cluster2600/porscheparts/twins/m64-cylinder-head/source/additivefoam/README.md

# Marangoni contract fix for OpenFOAM 14

This patch only adds `assignable() const { return false; }` to the ORNL
Marangoni boundary condition. It allows `constrainHbyA` to preserve the normal
condition while the pressure predictor is built. It modifies neither
`evaluate`, nor `snGrad`, nor the pressure equations, nor the material
properties. It is not a cylinder head qualification.

The upstream file, under **GPL-3.0-or-later**, is
[`marangoniFvPatchVectorField.H`](https://github.com/ORNL/AdditiveFOAM/blob/9c05c5eb54db03faa342b14b0806efe740de8c44/applications/solvers/additiveFoam/derivedFvPatchFields/marangoni/marangoniFvPatchV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).
The patch is distributed under the same license. The tested context is
OpenFOAM 14, commit `7b05503f98a85be88af930df48623b4d152bfc35`.
The diff has no context lines: the exact input digest below is therefore a
precondition, and the output digest must be verified.

SHA-256 digests of the header:

- Required input: `bb21f5c705425c6903945f9ca95055d6ca4083d8b9d58e1b15e2a1c75deb022a`.
- Tested output: `c1bb4ab01a24a907aefda0995d7df650d4dc46c23f61f9d1130bd7d6a601a33c`.

On a **fresh copy of the solver sources**, from the directory that contains
`derivedFvPatchFields/`, verify the input hash before applying the patch with
`patch -p1`. Refuse any digest difference or ambiguous context; do not replace a
historical binary in place. Then rebuild the solver in a separate output
directory and record the digests of the sources, libraries and executable.

```mermaid
flowchart TD
    A["Fresh copy of the<br/>solver sources"] --> B{"Header input digest<br/>bb21f5c7…?"}
    B -- "different or ambiguous" --> R["Refuse; historical<br/>binary untouched"]:::stop
    B -- "exact" --> C["patch -p1"]
    C --> D{"Output digest<br/>c1bb4ab0…?"}
    D -- "no" --> R
    D -- "yes" --> E["Rebuild in a separate directory<br/>record source, library, executable digests"]
    E --> F["Native old/new witness<br/>traction, adjustPhi"]
    F -. "not sufficient" .-> G["LPBF coupon acceptance:<br/>balances, coupling, convergence,<br/>calibration checked separately"]:::open
    classDef stop fill:#fde2e1,stroke:#c0392b,color:#1a1a1a;
    classDef ok fill:#e3f1e6,stroke:#2e7d32,color:#1a1a1a;
    classDef open fill:#fff4d6,stroke:#b7791f,color:#1a1a1a;
```

The [native old/new witness](../../../../docs/reports/M64_F58_PREDICTOR_CONTRACT_20260908.md)
checks the conservation of the traction and the native `adjustPhi` step.
Success of this witness is not enough to accept an LPBF coupon: its balances,
its coupling, its convergence and its physical calibration remain separate
checks.

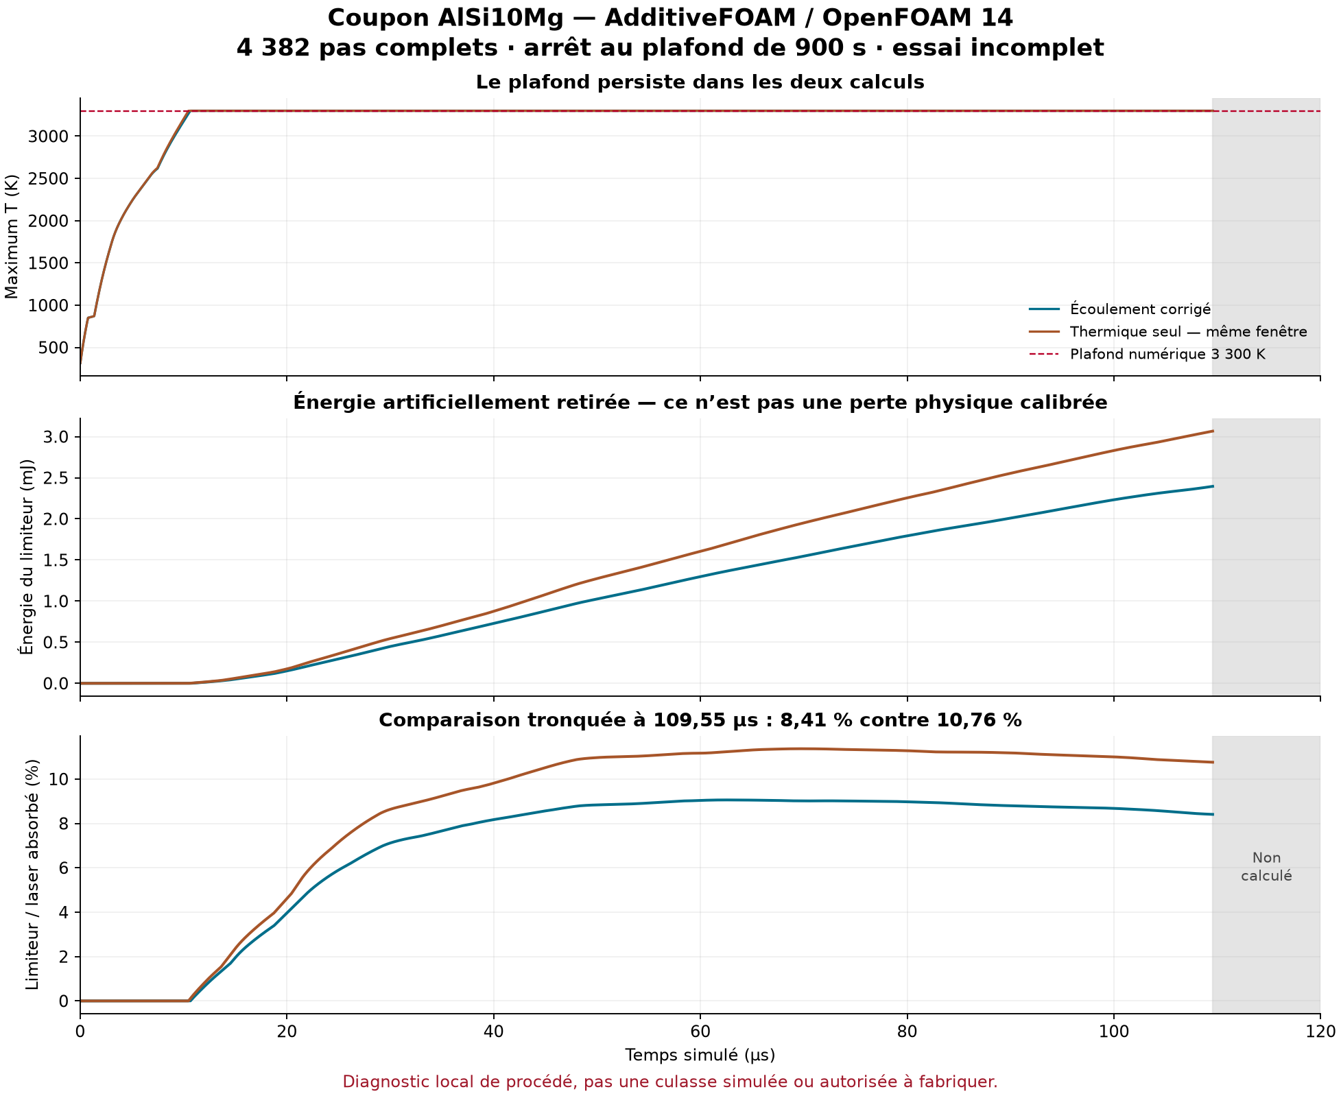
[picture p60: twins/m64-cylinder-head/evidence/corrected-coupon-diagnostic-20260908.png]
F58 AlSi10Mg coupon run with the corrected Marangoni contract: maximum temperature pinned at the 3,300 K numerical ceiling, limiter energy, and limiter share of absorbed laser, over the common 0–109.55 µs window


*The [corrected F58 coupon](../../../../docs/reports/M64_F58_CORRECTED_COUPON_20260908.md)
run that used this patch (labels in French): 4,382 complete steps, stopped at
the 900 s ceiling, an incomplete trial. It shows that the numerical 3,300 K
ceiling persists; it does not isolate the patch's effect and is not a simulated
or manufacturable cylinder head.*
