cluster2600/porscheparts/docs/reports/M64_BOUNDED_MESH_TRIALS_20260928.md

# M64 — bounded chamfer and native tip-cut experiments, 28 September 2026

## Retained result

Follow-up: the [local native reconstruction](M64_LOCAL_RECONSTRUCTION_20260928.md)
passes six-face locality and BOP checks, but its surface quality is worse;
the retained 32-tetrahedron result is unchanged.

**Zero rejected tetrahedra has not been demonstrated on the head.** The retained
volume mesh still has **32 elements below minSICN 0.1, out of 1,341,461**.
This continuation implements the [research-backed experiments](M64_ZERO_DEFECT_RESEARCH_20260928.md)
and rejects a misleading zero-quality-defect result on a synthetic witness.
Neither that witness nor a valid Boolean operation is a validated cylinder head.

A new **unchanged-CAD surface screen** has **seven incompatible triangles on
five faces**, versus eight on six faces in the retained mesh's boundary. It is
a different surface discretisation, **not** a new volume mesh or a reduction
of the retained 32-tetrahedron count. No CAD master, quality threshold,
functional-interface designation or manufacturing authorisation changes.

The private reference is still the scan-derived **935 research body**, not
certified M64 engine interfaces. Coordinates remain provisional scan units;
0.020 below is not a validated millimetre allowance and is unrelated to the
0.040 mm carrier-displacement target. Scan attribution and rights are recorded
under [Wolfe Classics](../../catalog/sources/src-wolfe-classics-935-billet-cylinder-head-scan.json).
Only this diagnostic figure, code and aggregate results are published; native
geometry, raw coordinates, volume meshes and detailed receipts stay private.

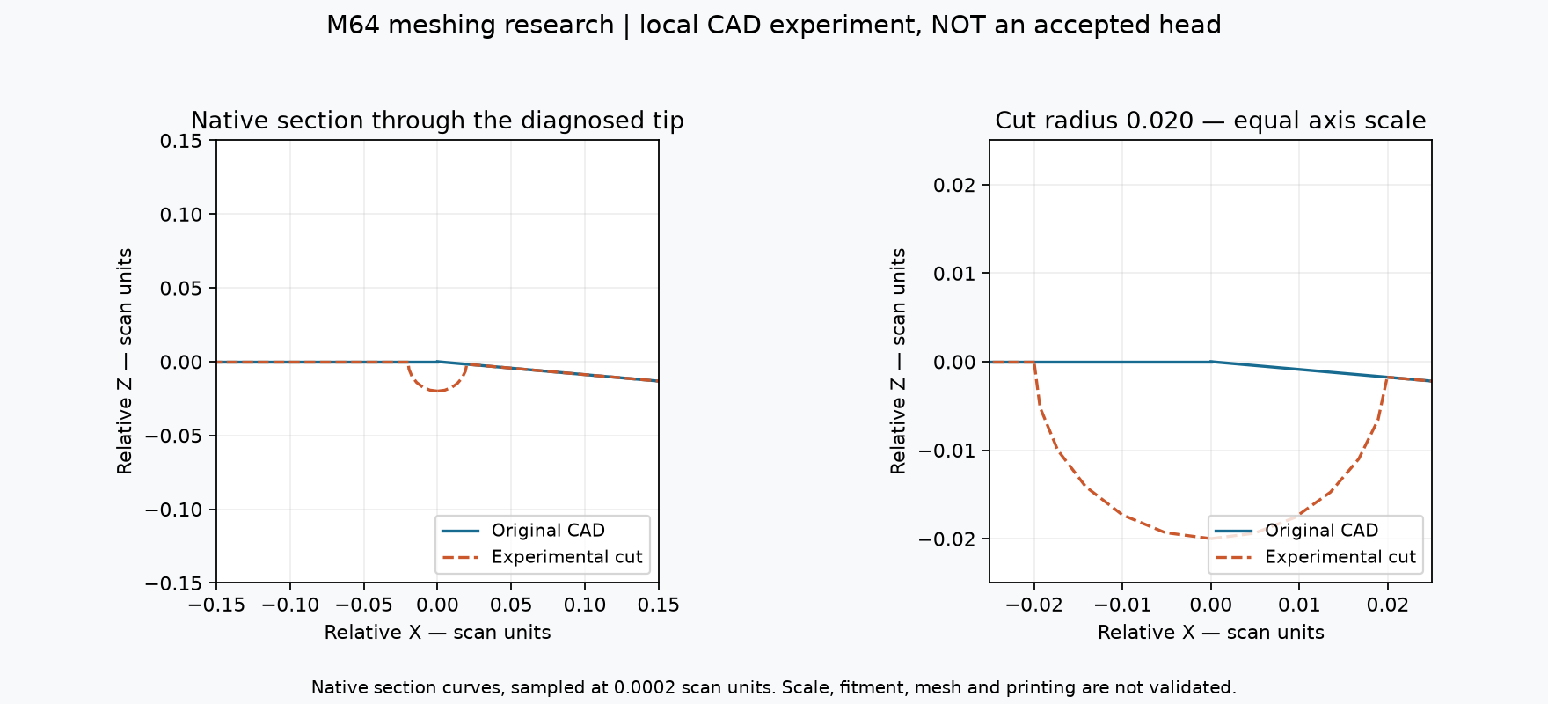
[picture p79: docs/media/m64-bounded-mesh-20260928/tip-cut-section.png]
Actual native section at the experimental cut


*Blue: original native section; orange: an experimental spherical cut of radius
0.020. The equal-scale section exposes the new notch; it is not an adopted
cooling feature, product photograph, thermal simulation or printing approval.*

## Tests and findings

| Experiment | Measured result | Decision |
|---|---|---|
| Shared curve/parametric-curve consistency on six obstructing faces | 19 edge/face uses, 129 samples each; maximum sampled gap **1.40088e-7**; none exceeds its recorded edge tolerance | No measured justification for a simple shared-curve repair. Sampling does not certify unsampled extrema. |
| Bounded DelOptim intermediate stage, unit tetrahedron, epsilon 0.020 | **4,182 inner tets; zero below 0.1; minimum 0.126104875** | **Rejected:** two material components and two boundary edges without incidence two. |
| Independent distance bounds on that witness | Two directed upper bounds **0.01970484492** and **0.00679892761**, below 0.020; interval gap tolerance 1e-4 | Small distance does not rescue failed topology. These are floating-point polygon comparisons, not a native-CAD or rounding-error certificate. |
| Acute tetrahedron witness, same bounded safe mode | Mesher stopped after **120 s**, no completed exported mesh | Nonconverged; no quality result. |
| One native spherical cut at face 1648, radius 0.020 | Exactly five source faces affected in memory; one valid solid and shell, unchanged maximum tolerances, valid reread; **BOP audit passes** without faults/errors/warnings in **261.75 s** | CAD candidate only; does not establish useful geometry or a passing mesh. |
| Four distinct acute tips on five selected faces, radius 0.020 | Exactly ten source faces affected in memory; **4,922 faces**, one valid solid/shell, unchanged maximum tolerances, valid reread | Local CAD construction succeeds; full candidate BOP and mesh/volume/deviation qualification remain open. |
| First surface recipe, single-tip candidate | 86,606 triangles, **105 incompatible**, minimum 0 | Rejected. This exploratory recipe also differs outside the cut; do not attribute every new bad triangle to the cut. |
| First surface recipe, four-tip candidate | Native process exits **139**, no completed surface result | Failed process; incomplete receipt is not a pass. |
| Curvature-aware matched recipe, unchanged reference | **441,650 triangles; seven incompatible; minimum 0.02134670874**, **260.69 s** | Surface-only improvement; still incompatible with zero rejected tets on that fixed skin. |
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
