cluster2600/porscheparts/docs/assets/m64-g13/central-section-x0.png

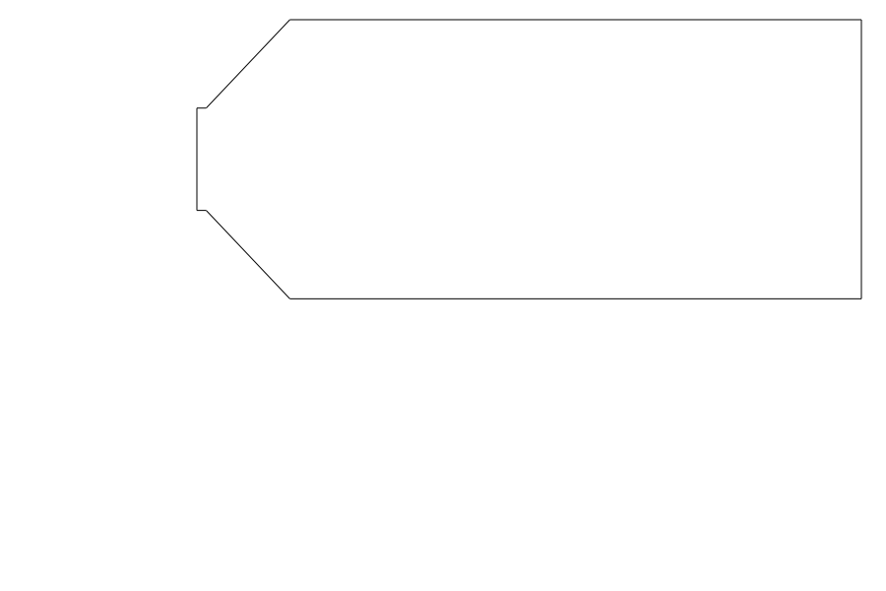
docs/assets/m64-g13/central-section-x0.png
