cluster2600/porscheparts/docs/assets/m64-g13/central-spine.png

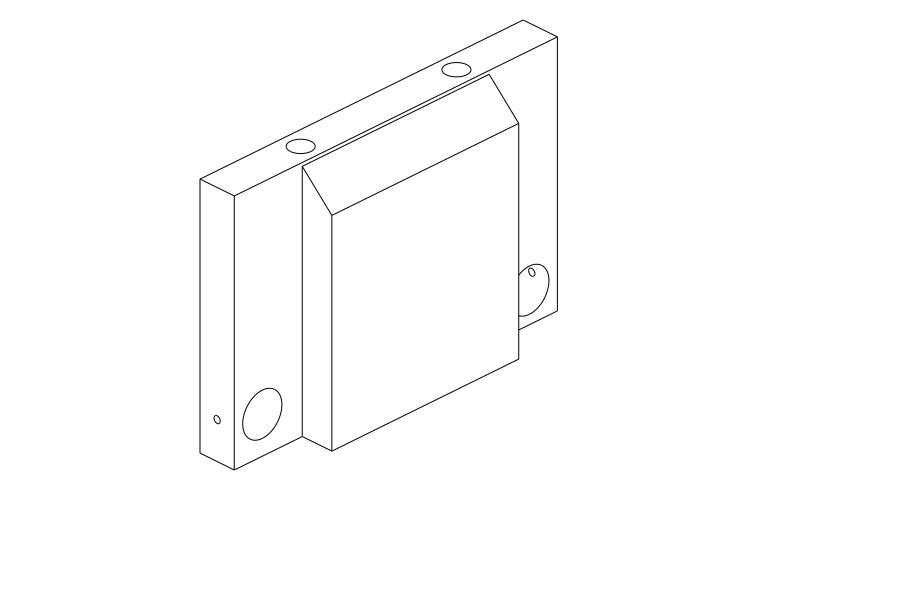
docs/assets/m64-g13/central-spine.png
