cluster2600/porscheparts/docs/assets/m64-g14/central68.png

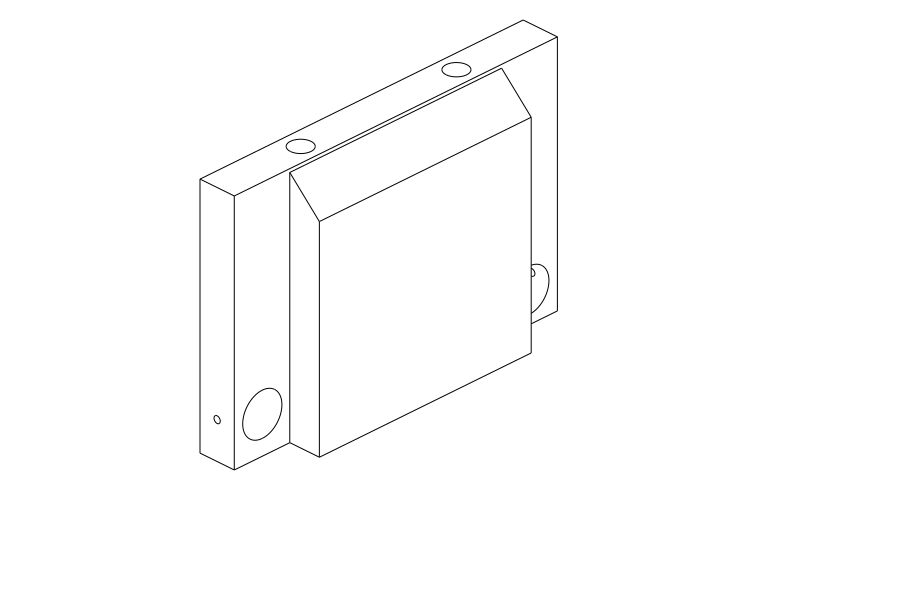
docs/assets/m64-g14/central68.png
