cluster2600/porscheparts/docs/assets/m64-g14/central-caps.png

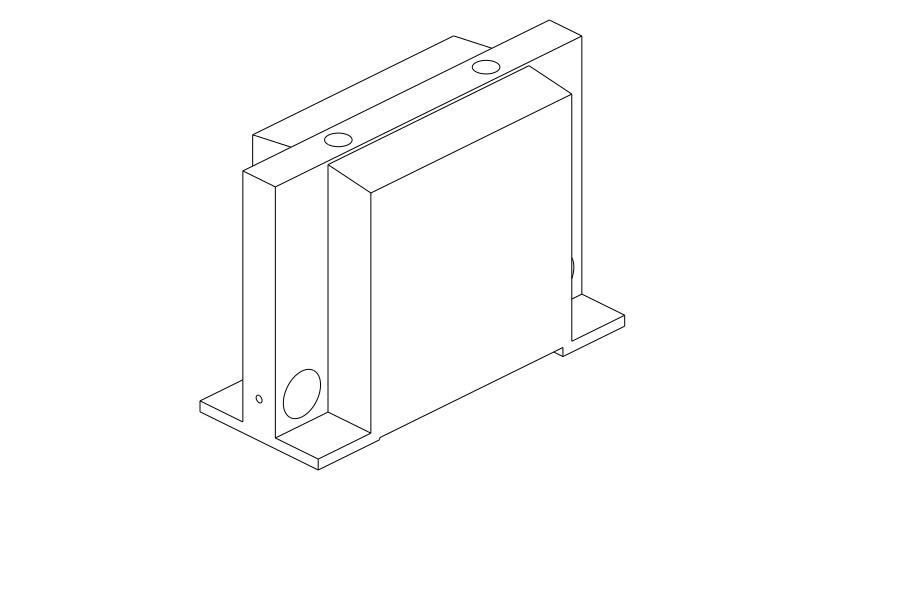
docs/assets/m64-g14/central-caps.png
