cluster2600/porscheparts/docs/assets/m64-g14/outer-combined-section.png

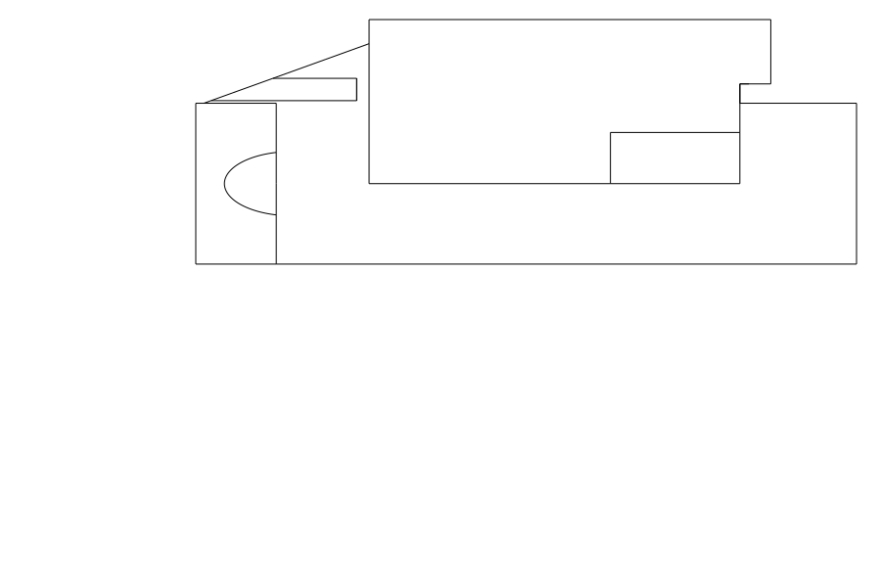
docs/assets/m64-g14/outer-combined-section.png
