cluster2600/porscheparts/docs/images/m64-hybrid-group-quality-20260909.png

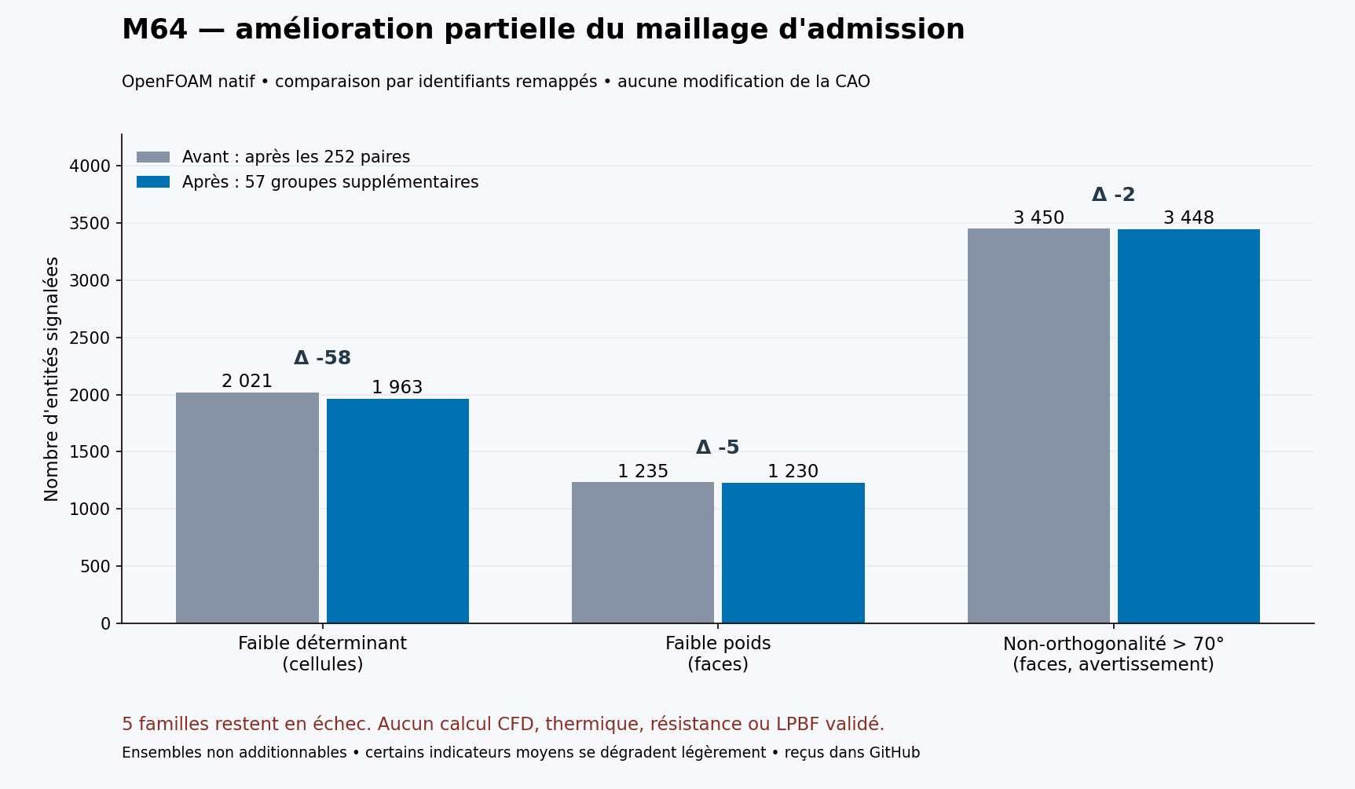
docs/images/m64-hybrid-group-quality-20260909.png
