cluster2600/porscheparts/docs/M64_SURFACE_METHOD_COMPARISON_20260909.png

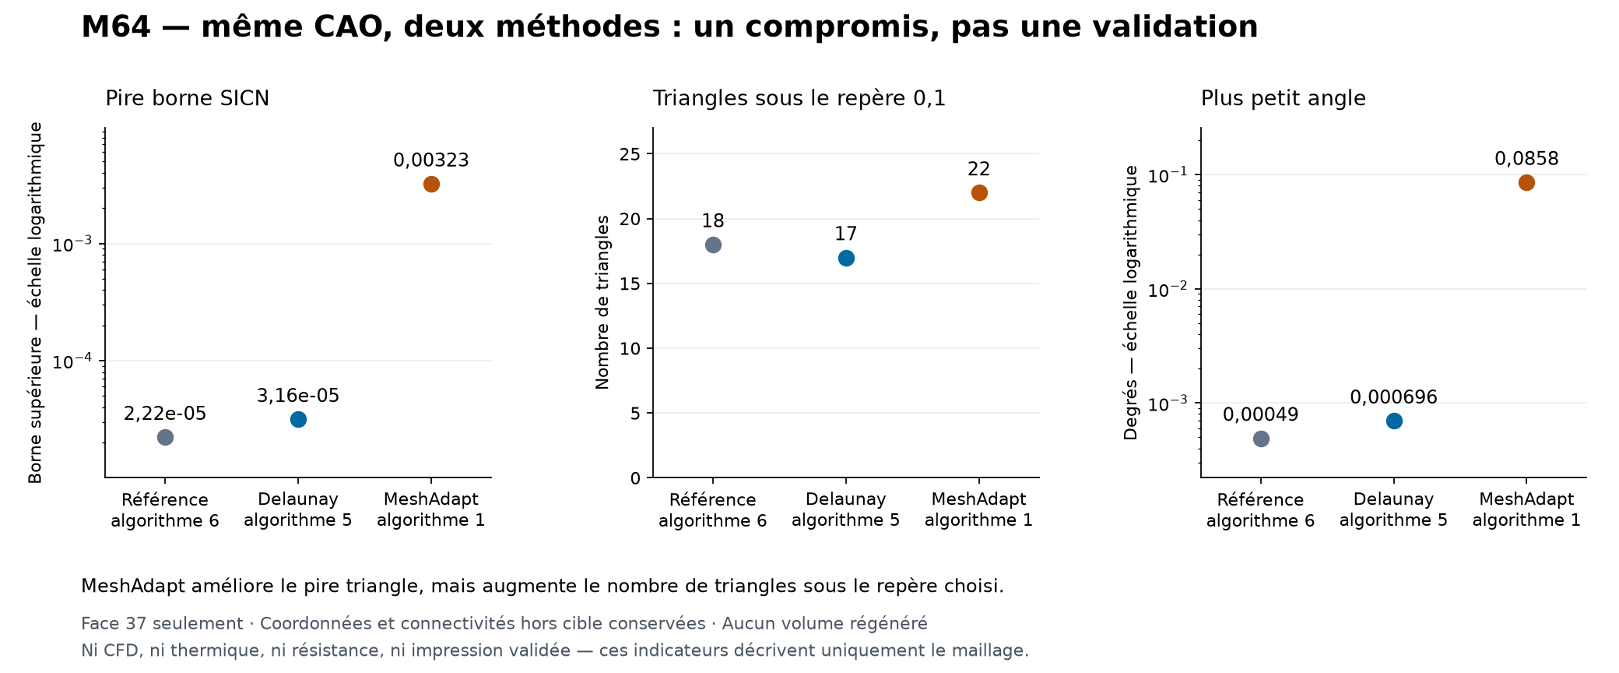
docs/M64_SURFACE_METHOD_COMPARISON_20260909.png
