cluster2600/porscheparts/docs/media/diagrams/digital-twin-993-etat.png

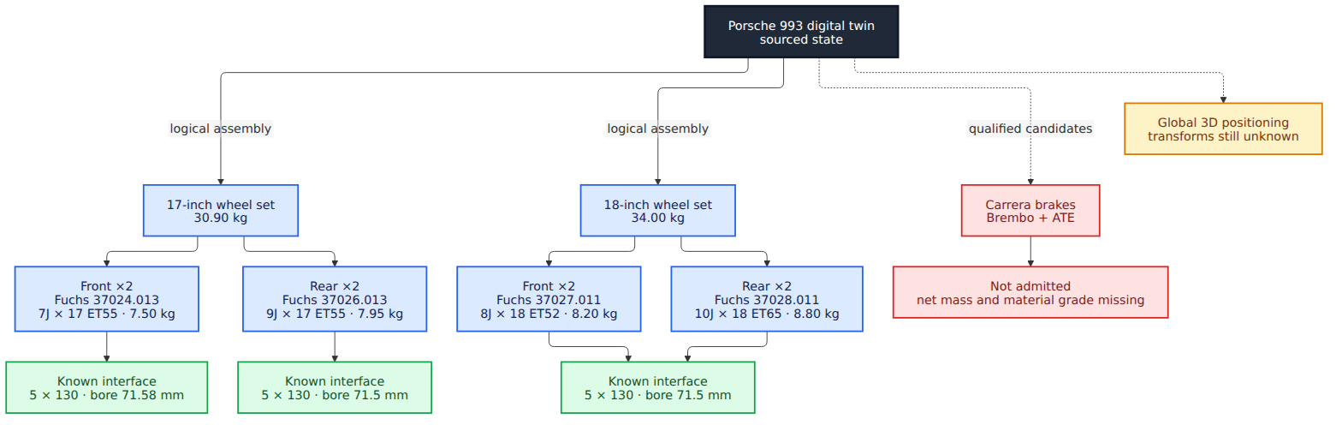
docs/media/diagrams/digital-twin-993-etat.png
