cluster2600/porscheparts/docs/media/diagrams/m64-700ps-execution.png

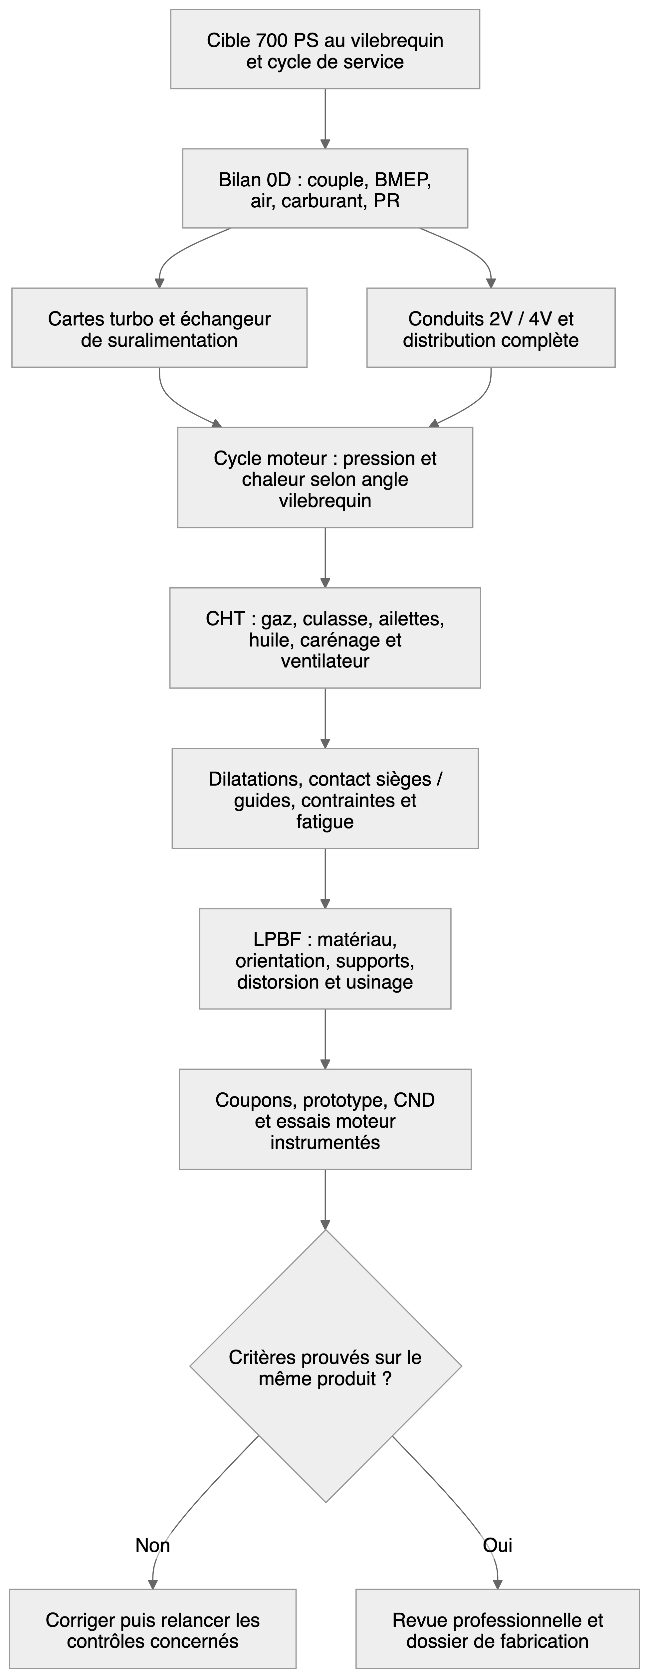
docs/media/diagrams/m64-700ps-execution.png
