cluster2600/porscheparts/docs/media/diagrams/m64-stack.png

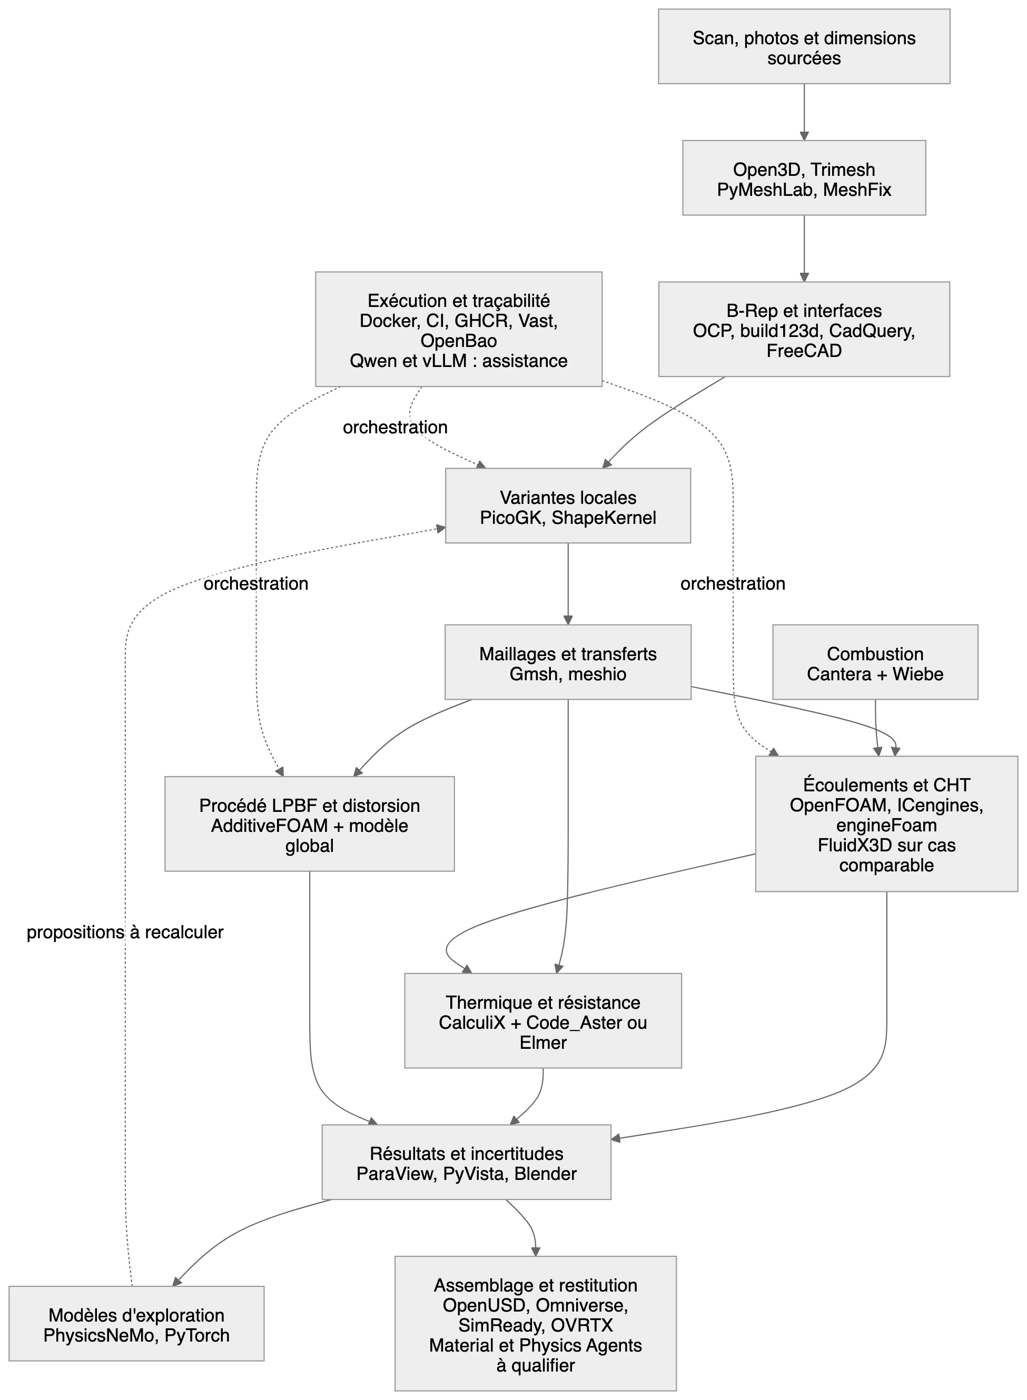
docs/media/diagrams/m64-stack.png
