cluster2600/porscheparts/docs/media/diagrams/m64-vast-run.png

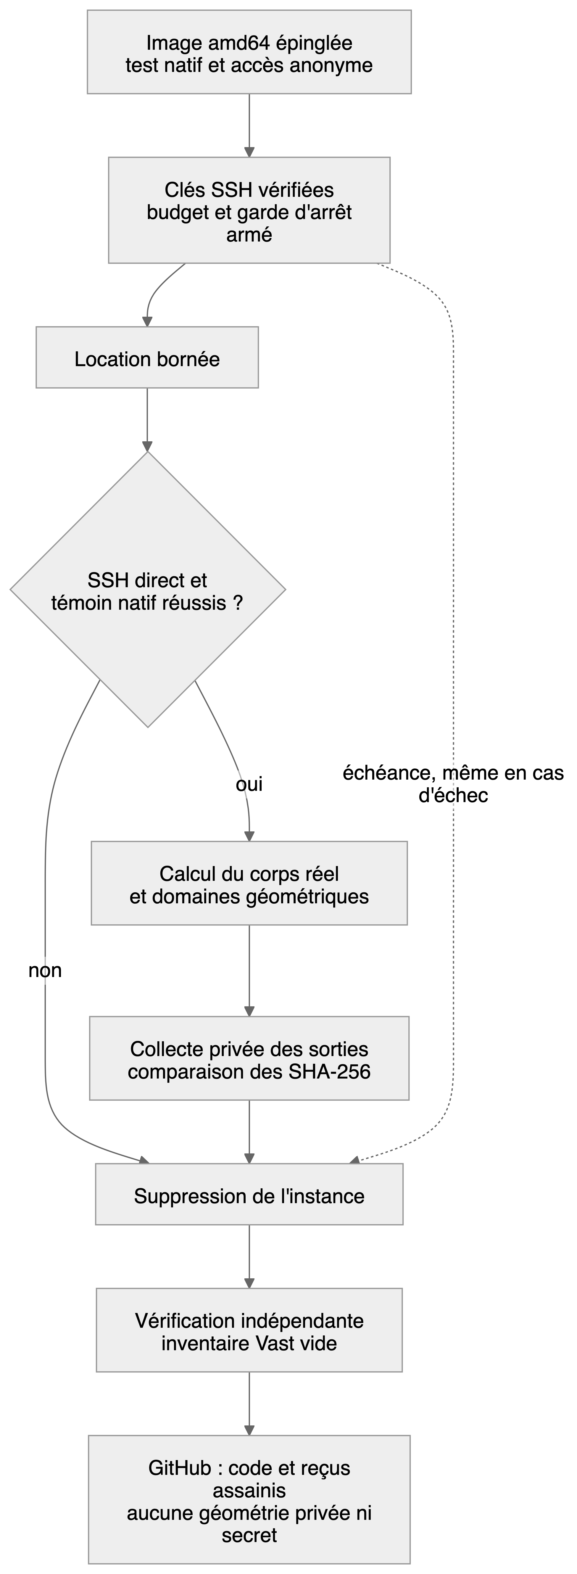
docs/media/diagrams/m64-vast-run.png
