cluster2600/porscheparts/docs/media/m64-adaptive-mesh-20260928/acute-native-face.png

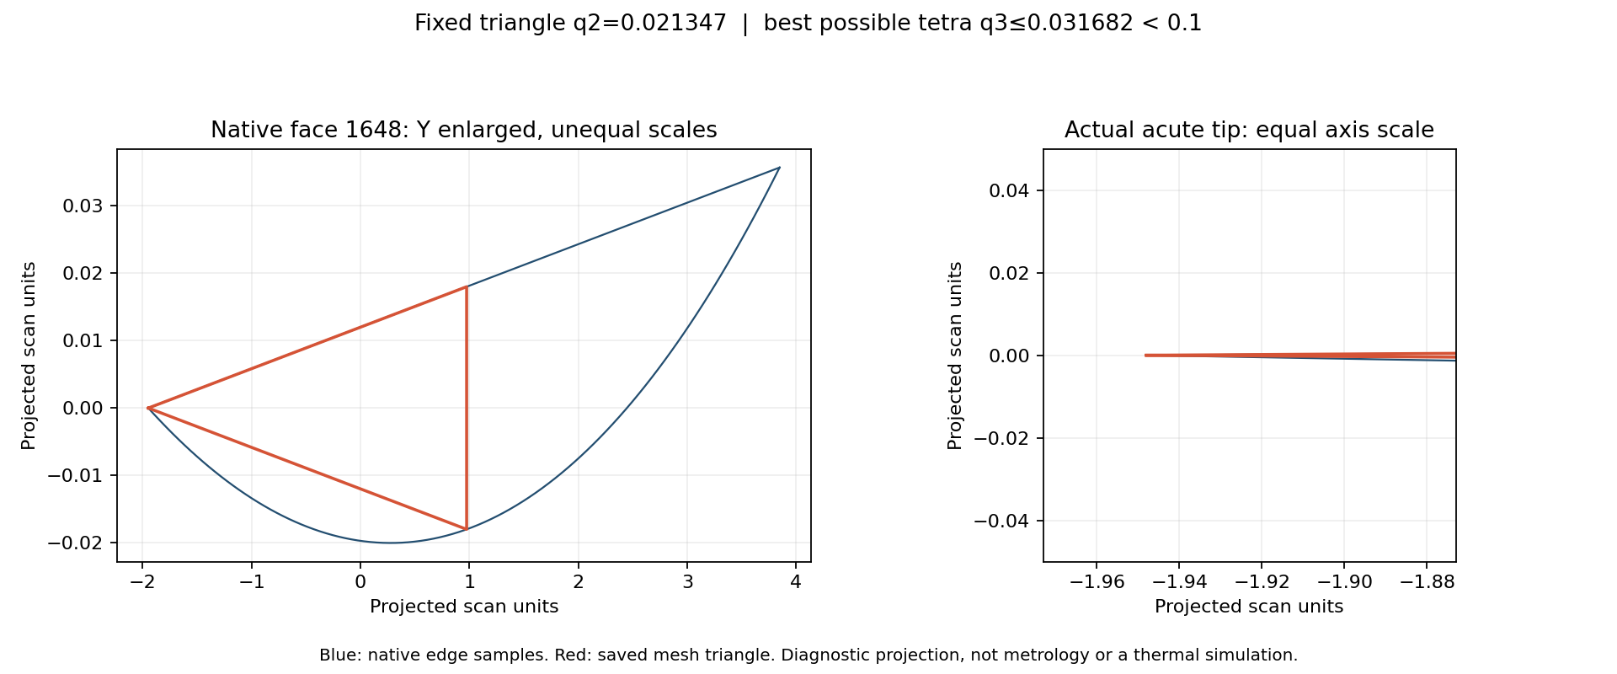
docs/media/m64-adaptive-mesh-20260928/acute-native-face.png
