cluster2600/porscheparts/docs/media/m64-am-20260928/geometric-screen.png

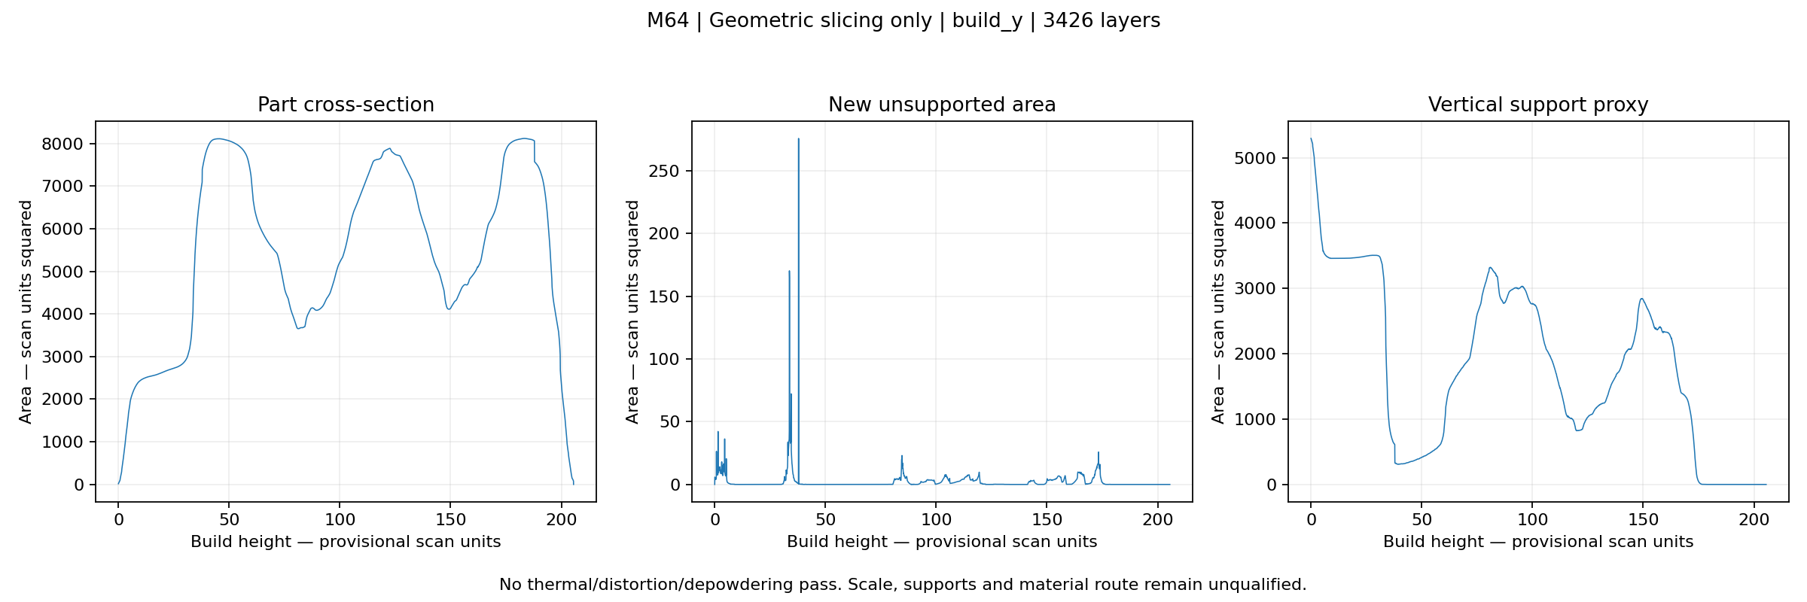
docs/media/m64-am-20260928/geometric-screen.png
