cluster2600/porscheparts/docs/media/m64-fixed-boundary-seam-20260928/native-section.png

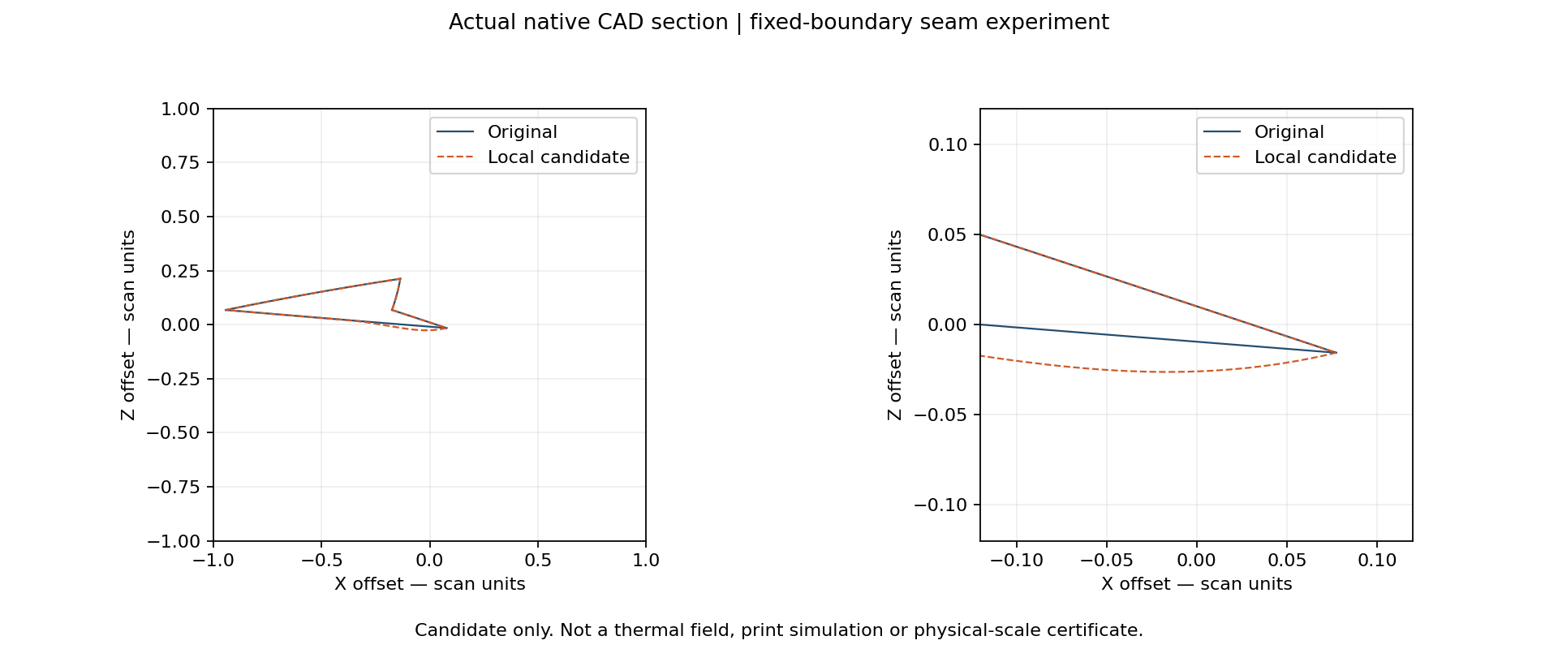
docs/media/m64-fixed-boundary-seam-20260928/native-section.png
