cluster2600/porscheparts/docs/media/m64-junction-recovery-20260928/junction-classes.png

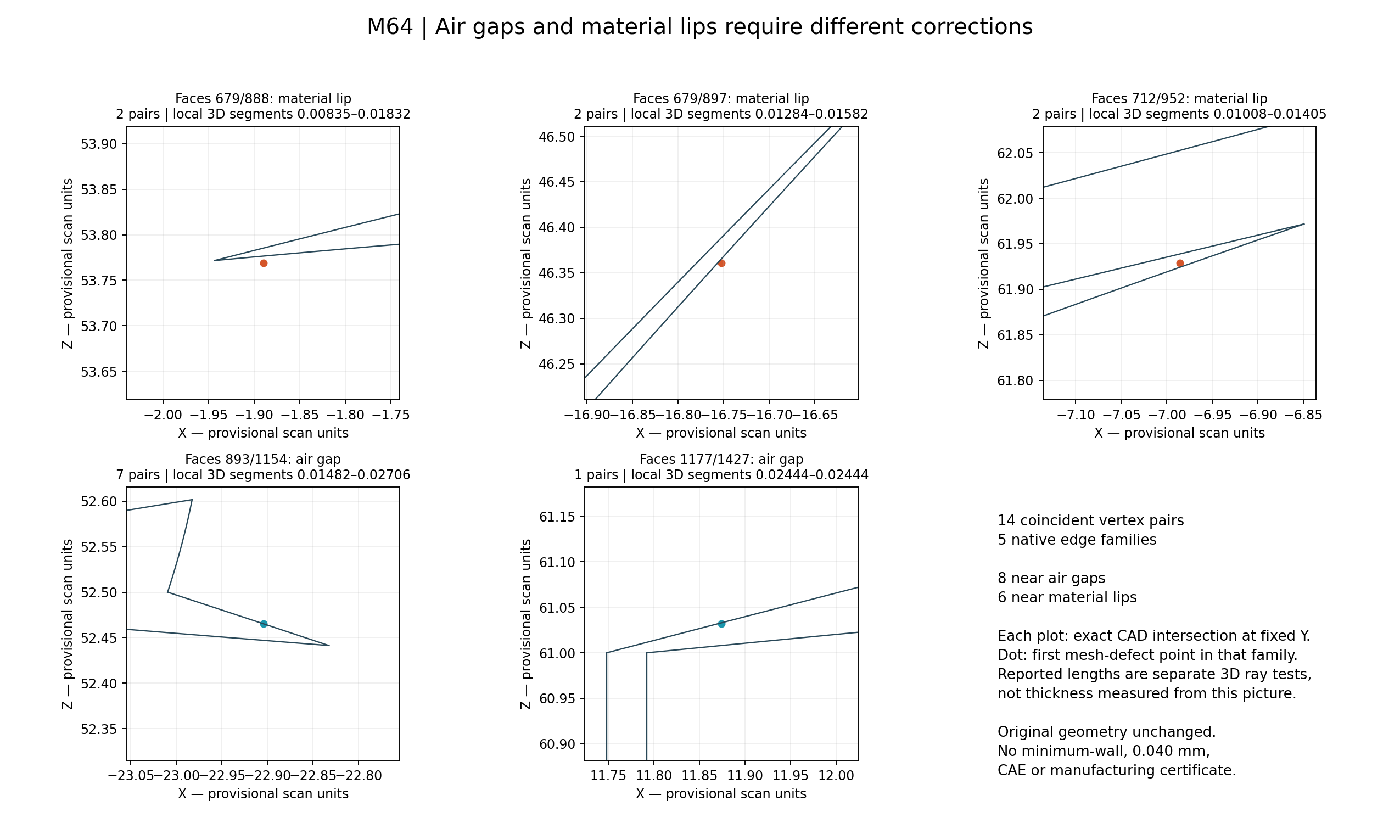
docs/media/m64-junction-recovery-20260928/junction-classes.png
