cluster2600/porscheparts/docs/media/m64-physics-am-20260928/thermal-reference.png

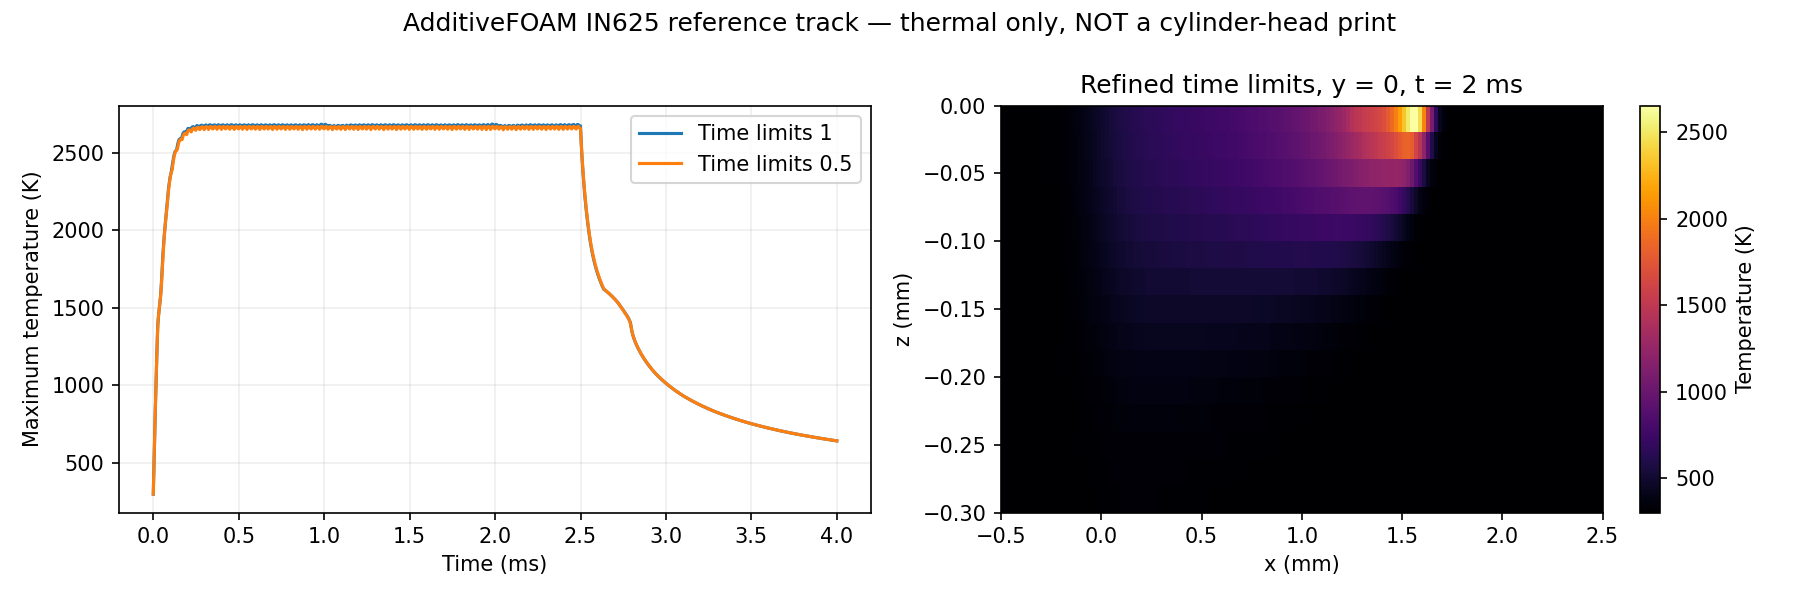
docs/media/m64-physics-am-20260928/thermal-reference.png
