cluster2600/porscheparts/docs/media/videos/917-head-f38-functional/assets/f38-lpbf.png

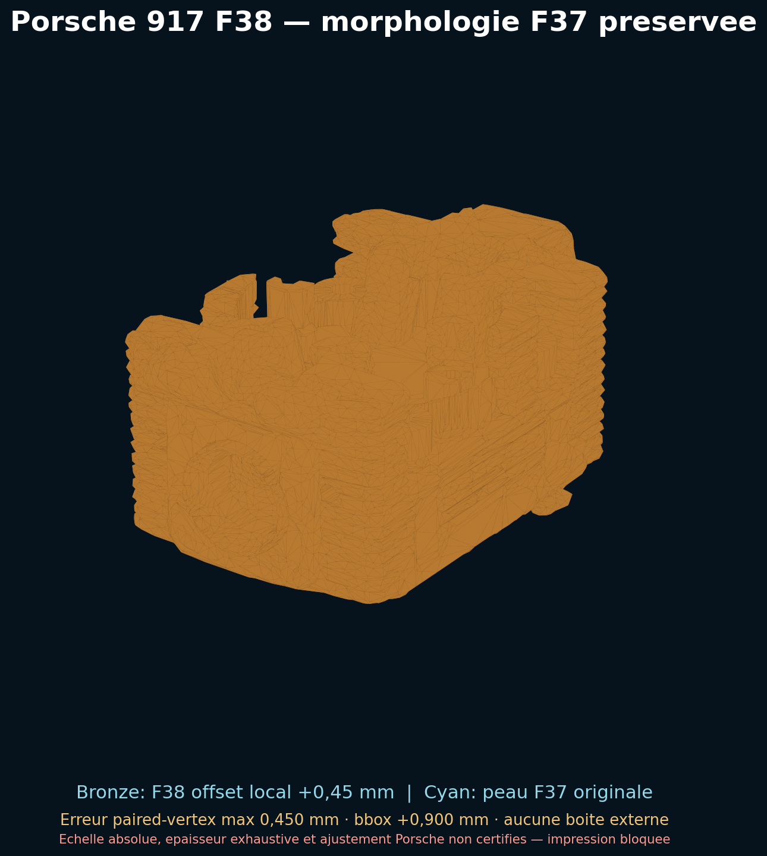
docs/media/videos/917-head-f38-functional/assets/f38-lpbf.png
