cluster2600/porscheparts/docs/media/videos/917-head-f39-function/assets/f39-cooling.png

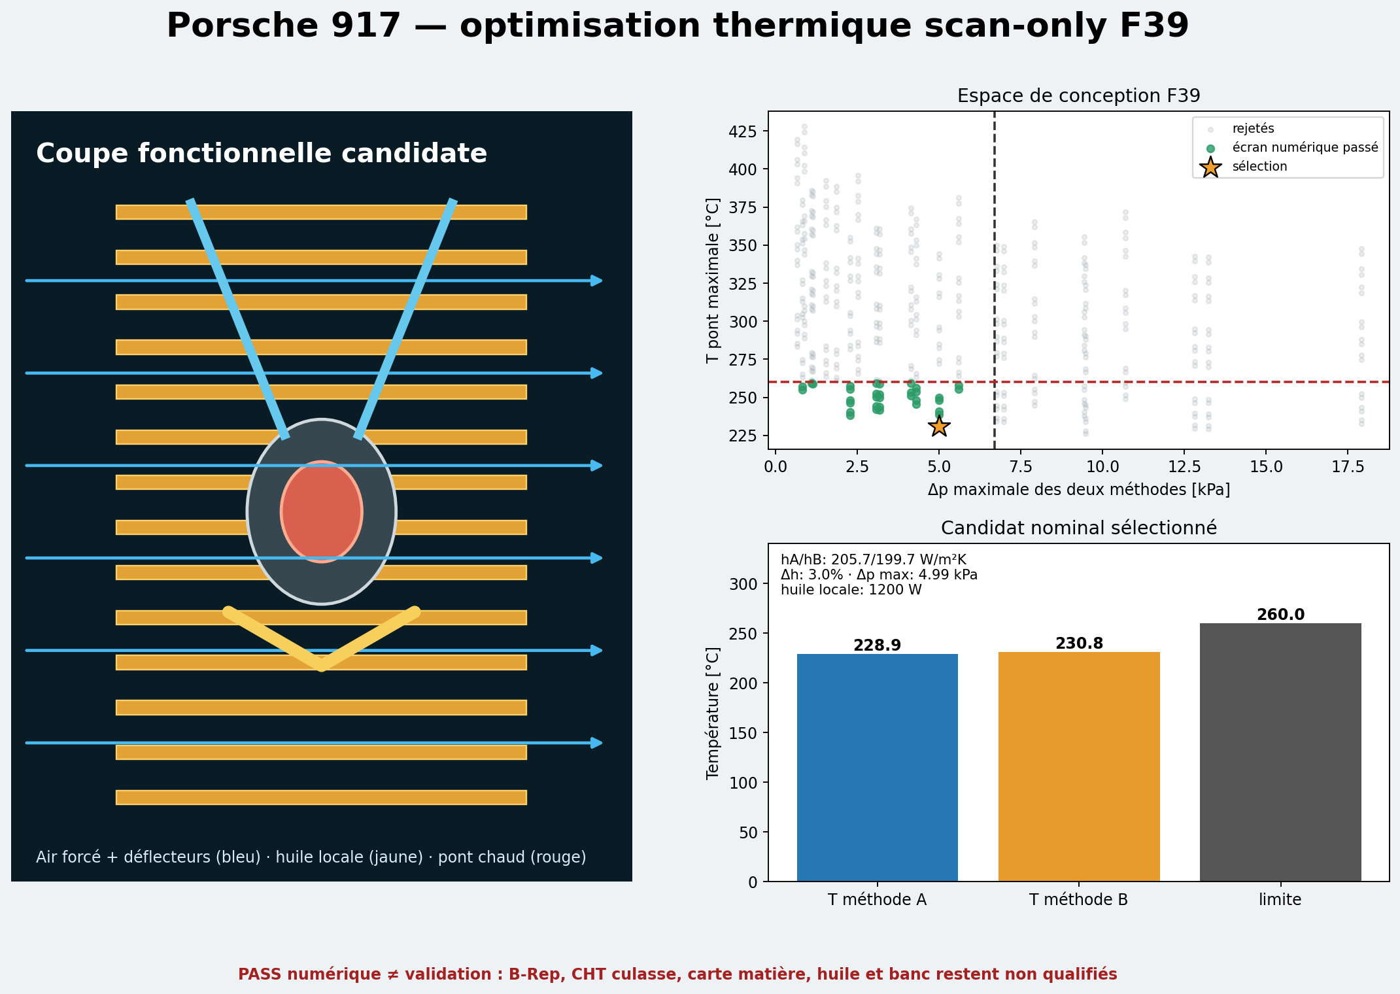
docs/media/videos/917-head-f39-function/assets/f39-cooling.png
