cluster2600/porscheparts/docs/research/993-turbo-20261002/exports/fr/demande_calculee_par_turbo.png

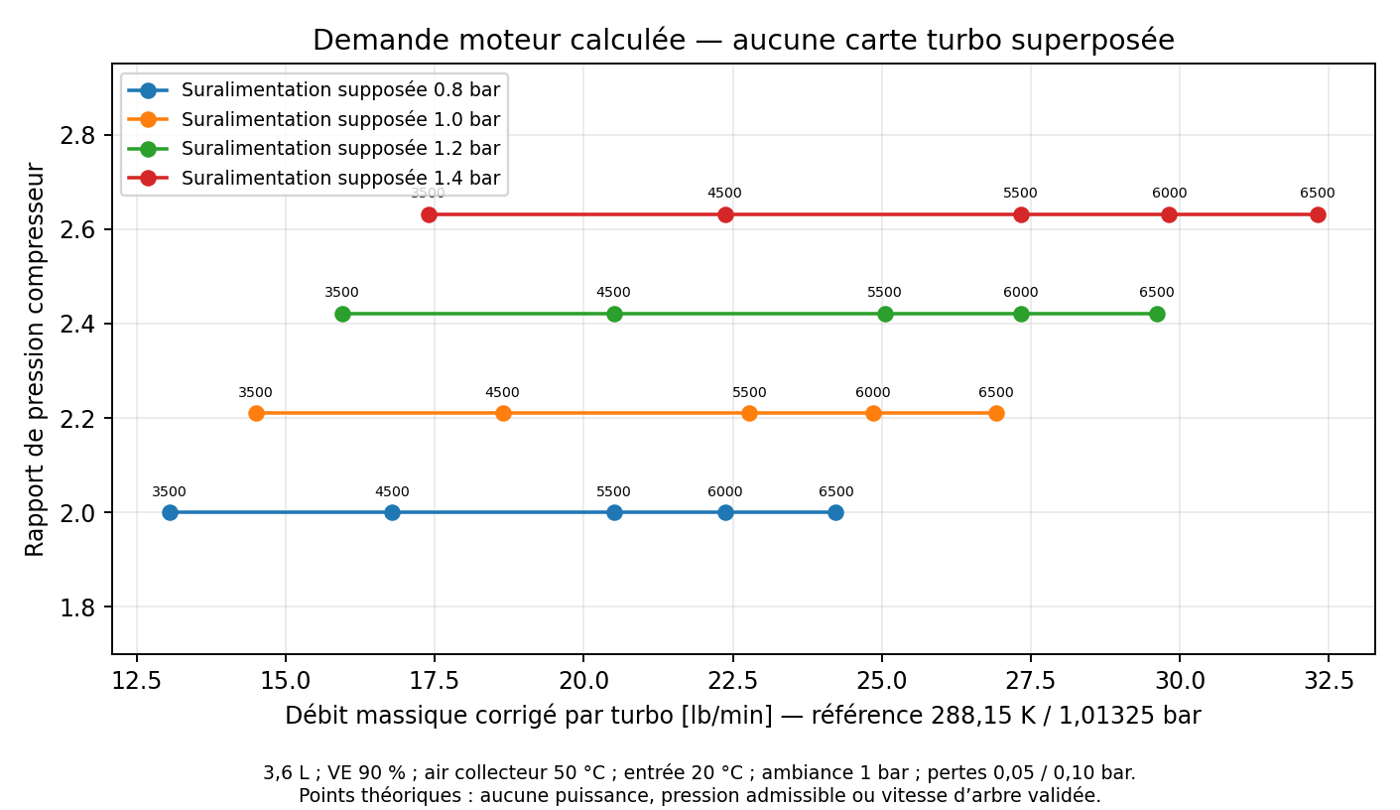
docs/research/993-turbo-20261002/exports/fr/demande_calculee_par_turbo.png
