cluster2600/porscheparts/twins/964-chassis/evidence/overlay.png

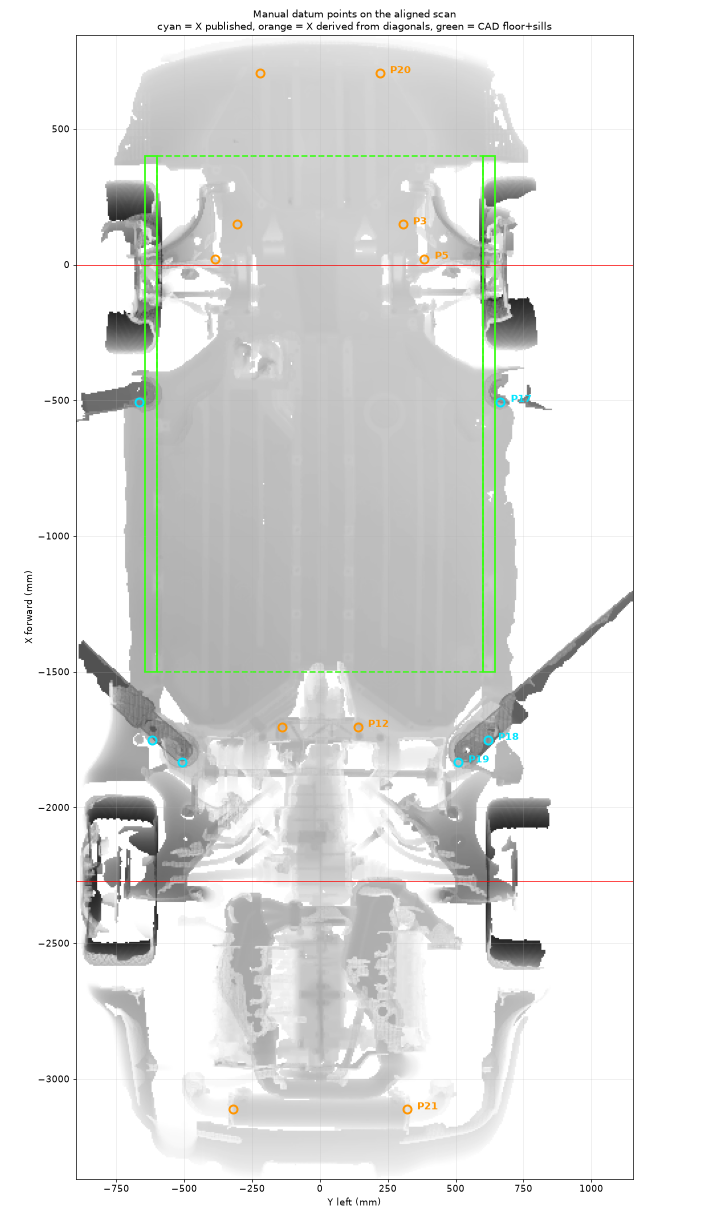
twins/964-chassis/evidence/overlay.png
