cluster2600/porscheparts/twins/993-exhaust-tip-ti-f0/evidence/lpbf-f1/993-exh-oval-tip-ti-f1-0001-lpbf-geometry-screen.png

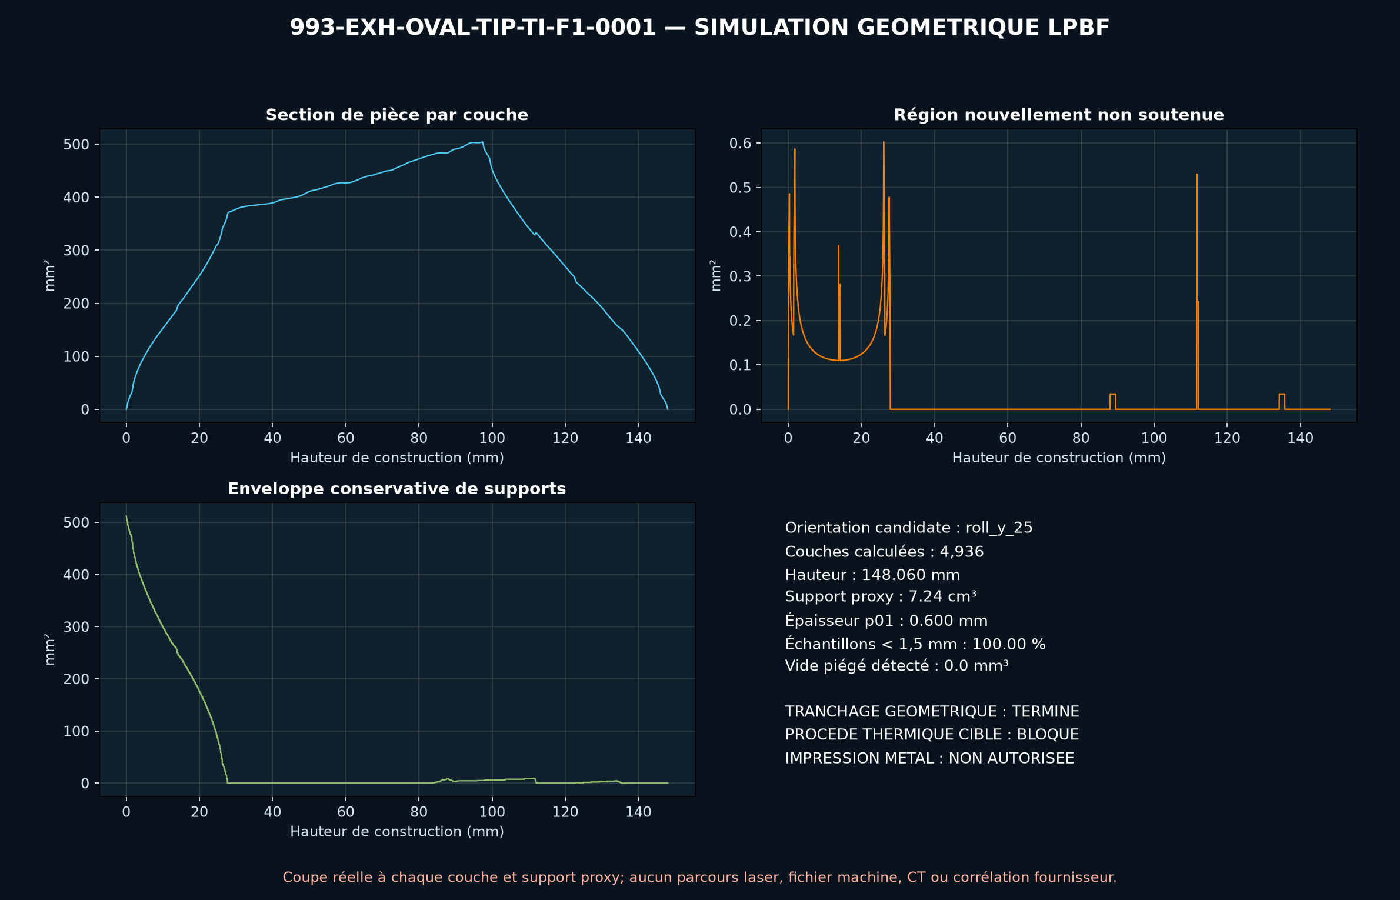
twins/993-exhaust-tip-ti-f0/evidence/lpbf-f1/993-exh-oval-tip-ti-f1-0001-lpbf-geometry-screen.png
