cluster2600/porscheparts/twins/993-m64-60-piston-gallery-f0/evidence/simready-f0/piston-cp1-gallery-f0-ovrtx.png

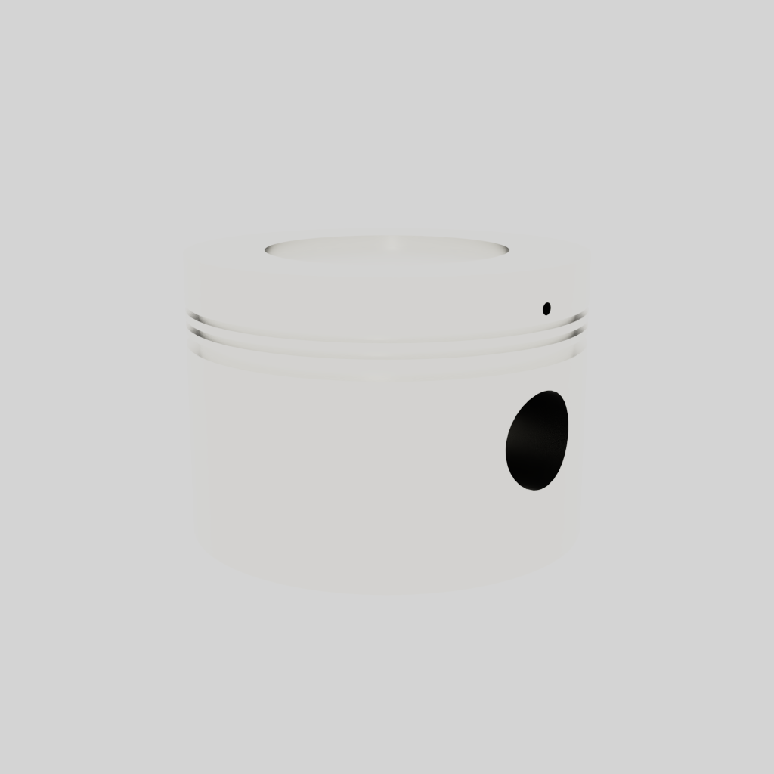
twins/993-m64-60-piston-gallery-f0/evidence/simready-f0/piston-cp1-gallery-f0-ovrtx.png
