cluster2600/porscheparts/twins/993-oval-exhaust-tip-in625-f0/evidence/simready-f0/grasp-preview-overlay.png

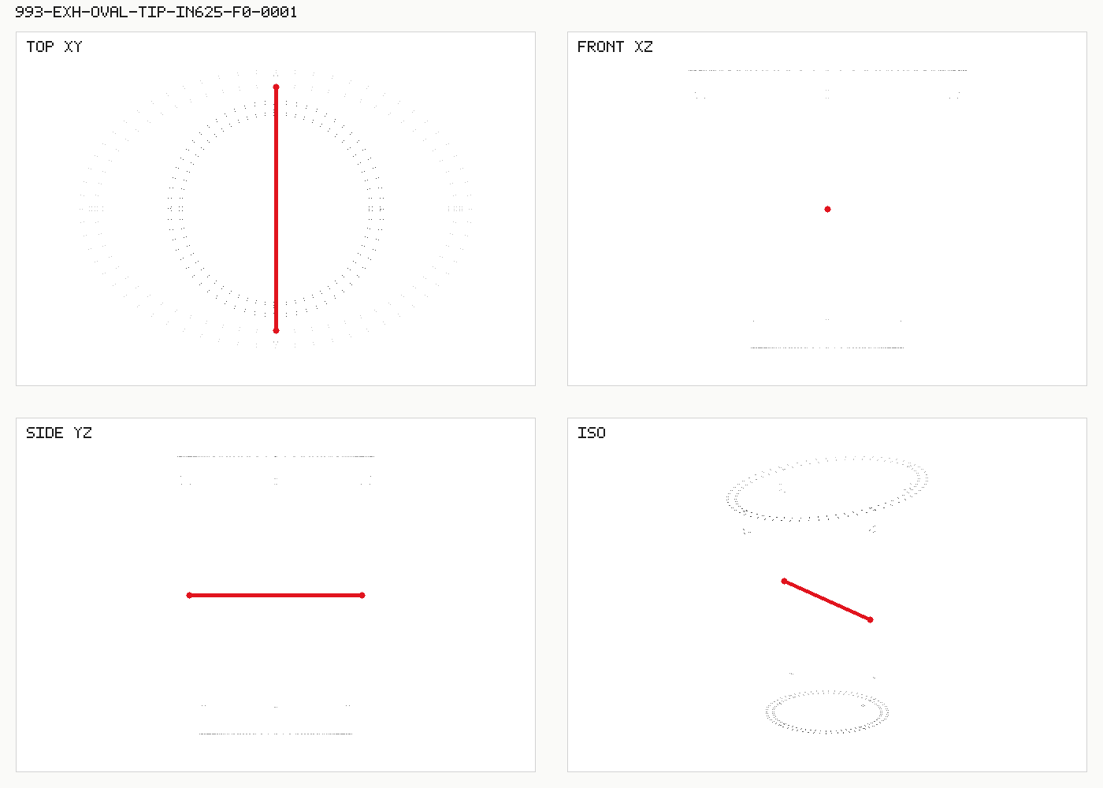
twins/993-oval-exhaust-tip-in625-f0/evidence/simready-f0/grasp-preview-overlay.png
