cluster2600/porscheparts/twins/m64-cylinder-head/evidence/935-reference-transition-before-after.png

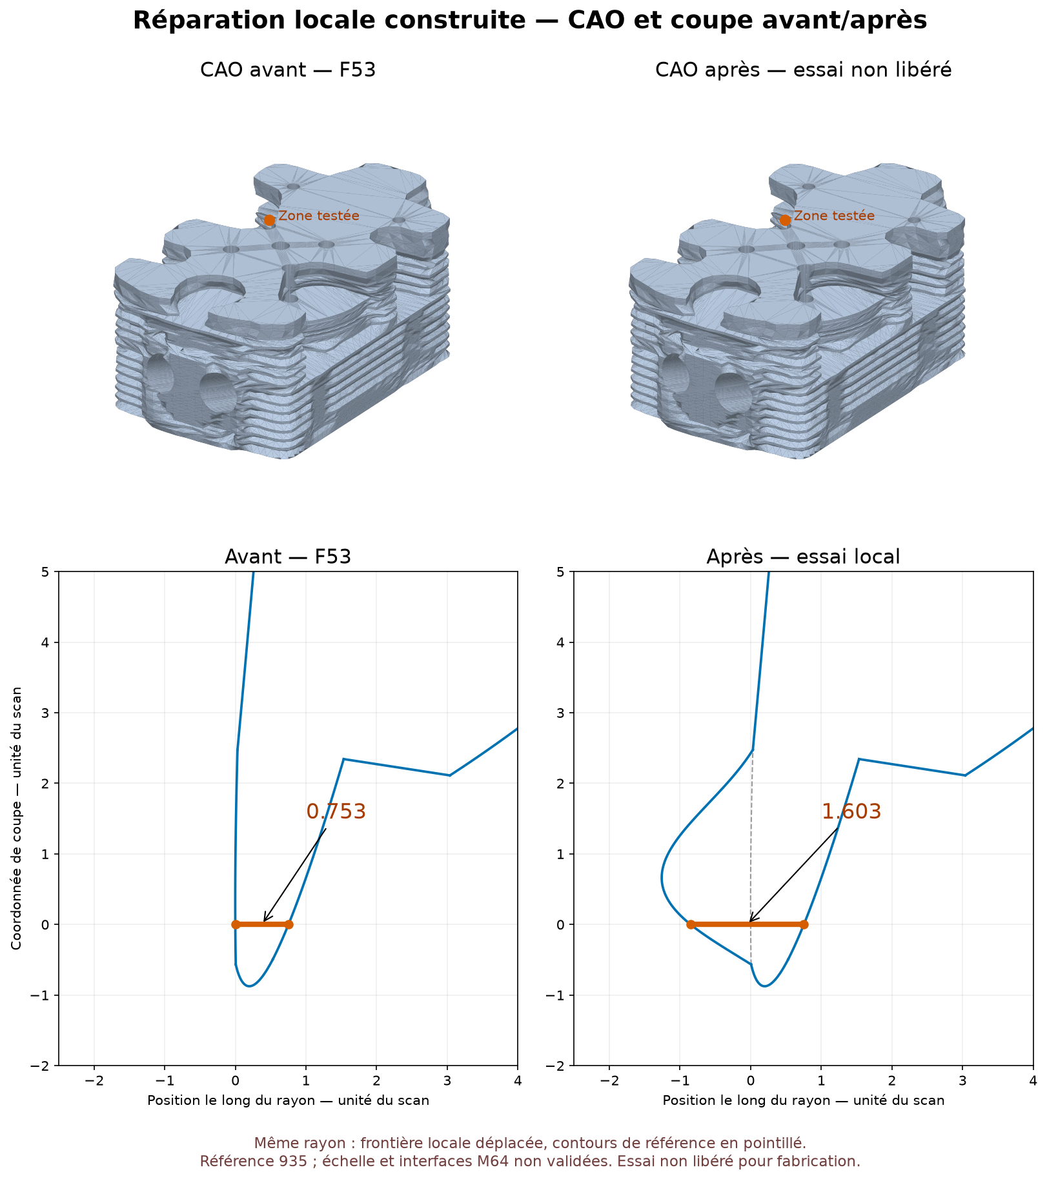
twins/m64-cylinder-head/evidence/935-reference-transition-before-after.png
