cluster2600/porscheparts/twins/m64-cylinder-head/evidence/g7-local-supports-cooling-20260925/supports-isometric.png

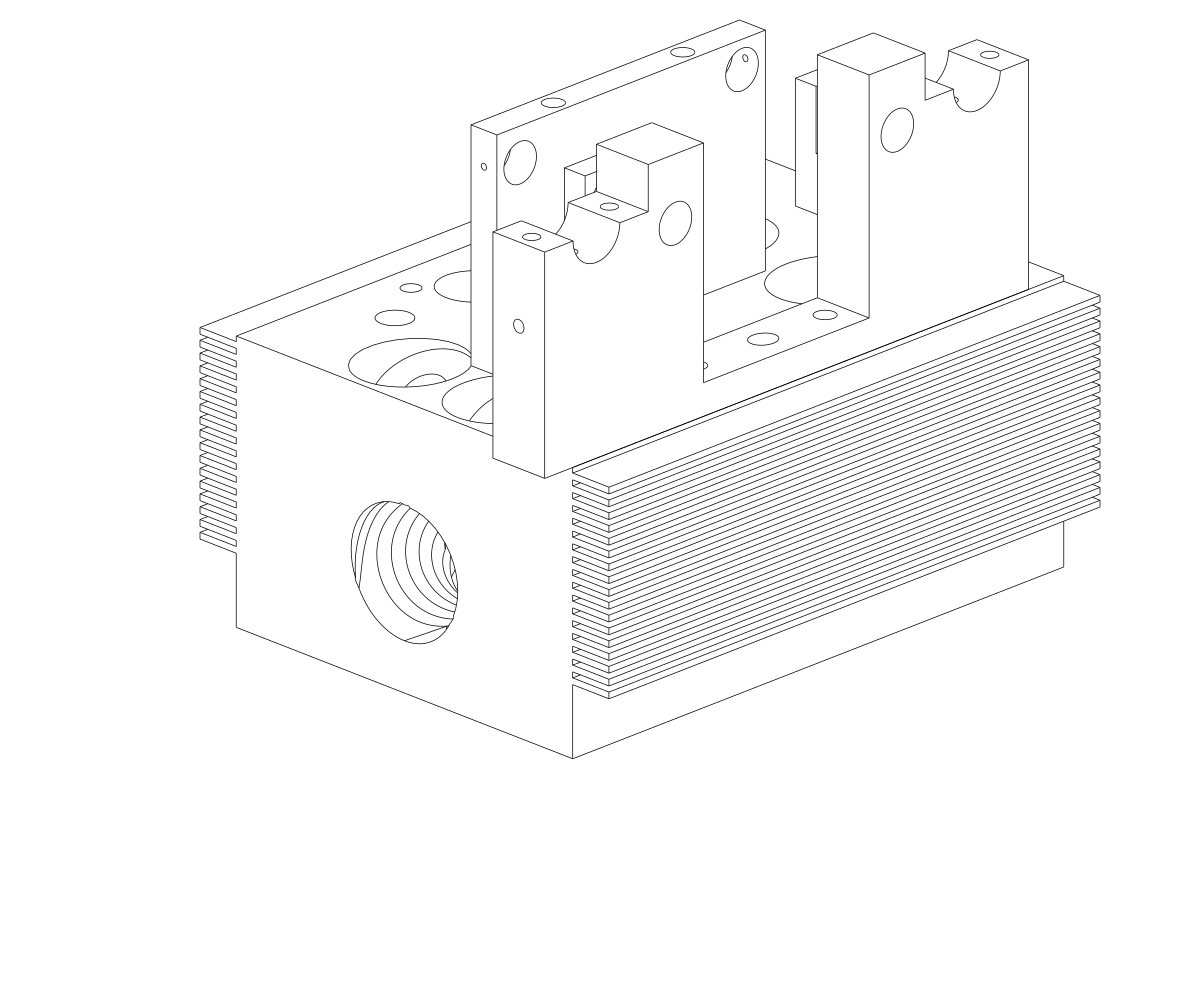
twins/m64-cylinder-head/evidence/g7-local-supports-cooling-20260925/supports-isometric.png
