cluster2600/porscheparts/twins/m64-cylinder-head/evidence/g11-support-stiffness-20260926/outer-d30-w30-section.png

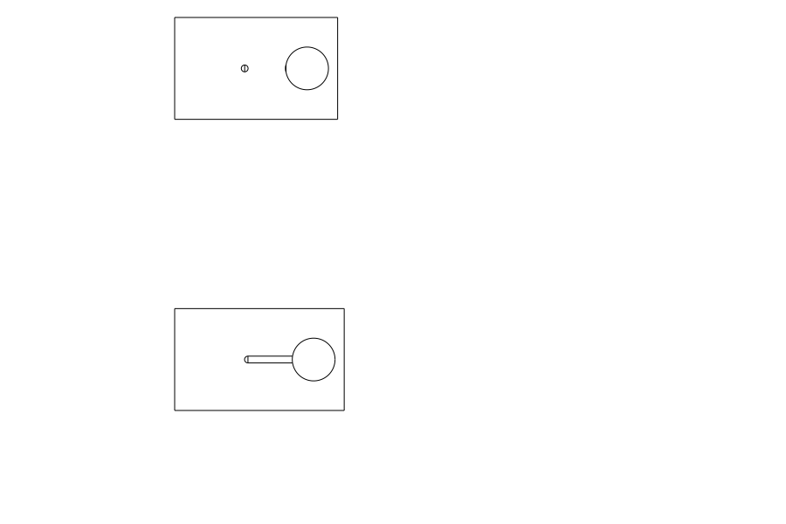
twins/m64-cylinder-head/evidence/g11-support-stiffness-20260926/outer-d30-w30-section.png
