cluster2600/porscheparts/twins/m64-cylinder-head/evidence/g12-local-buttresses-20260926/local24-preview.png

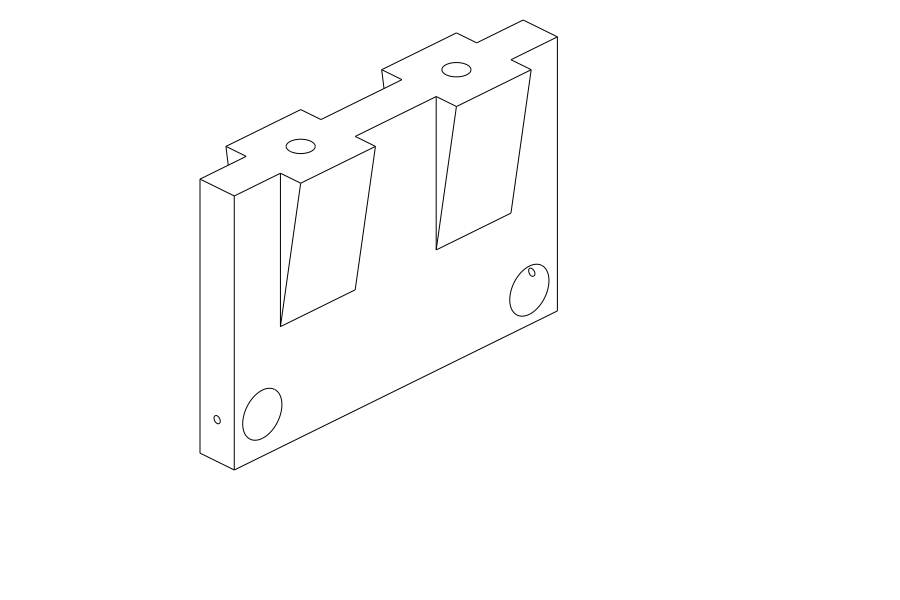
twins/m64-cylinder-head/evidence/g12-local-buttresses-20260926/local24-preview.png
