cluster2600/porscheparts/twins/m64-cylinder-head/evidence/thermal-face-proposals-and-section.png

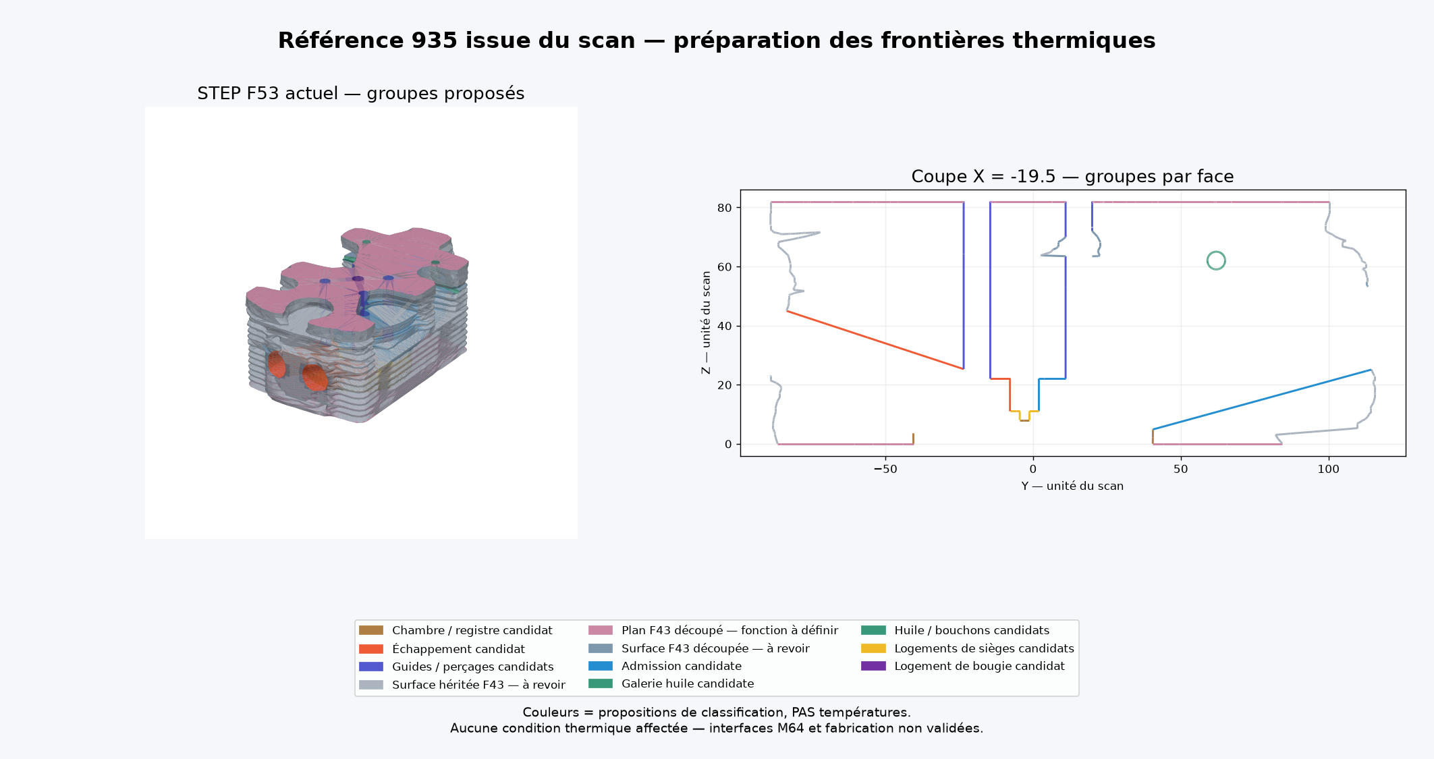
twins/m64-cylinder-head/evidence/thermal-face-proposals-and-section.png
