cluster2600/porscheparts/twins/m64-cylinder-head/evidence/valvetrain-v1/valvetrain-v1-float-sweep.png

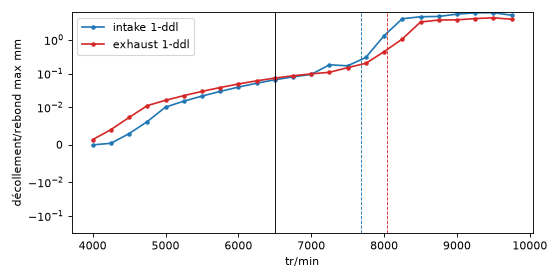
twins/m64-cylinder-head/evidence/valvetrain-v1/valvetrain-v1-float-sweep.png
