cluster2600/porscheparts/twins/m64-cylinder-head/evidence/valvetrain-v1/valvetrain-v1-kinematics.png

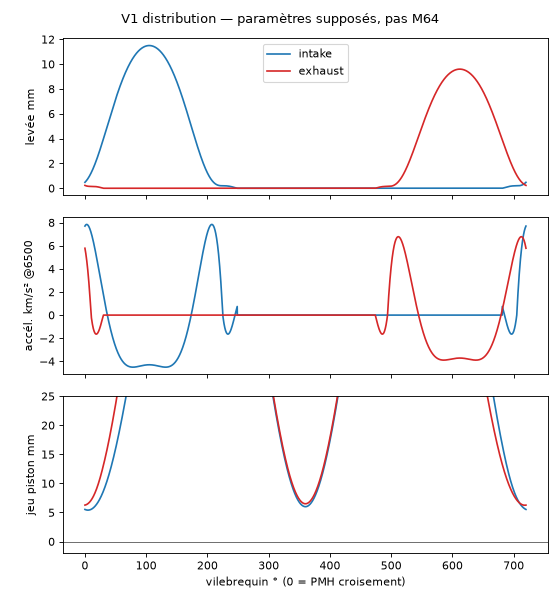
twins/m64-cylinder-head/evidence/valvetrain-v1/valvetrain-v1-kinematics.png
