cluster2600/porscheparts/twins/picogk-station-demo/qualification/runtime/omniverse-ui/kali2-native-video.png

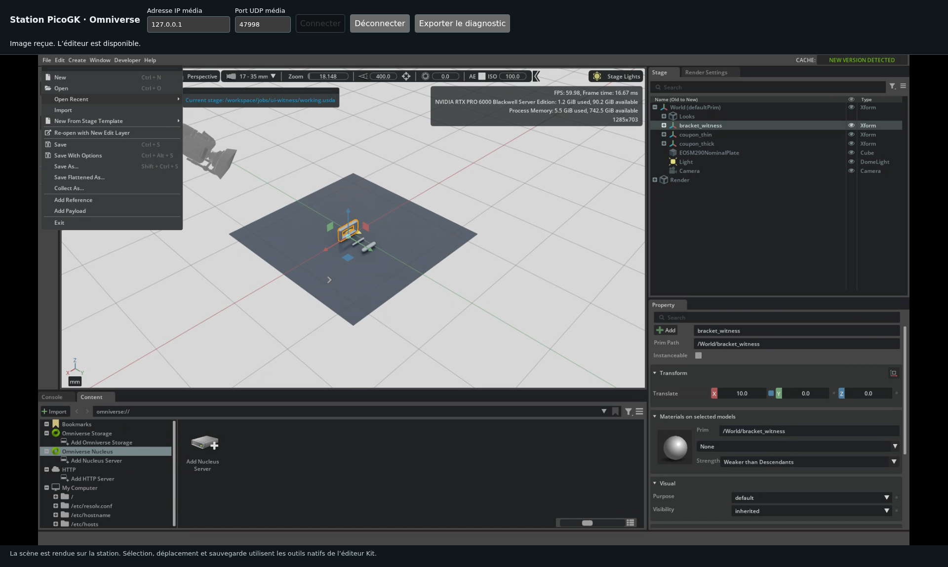
twins/picogk-station-demo/qualification/runtime/omniverse-ui/kali2-native-video.png
