cluster2600/porscheparts/twins/picogk-station-demo/qualification/runtime/omniverse-ui/picogk-kit-10mm-proof.png

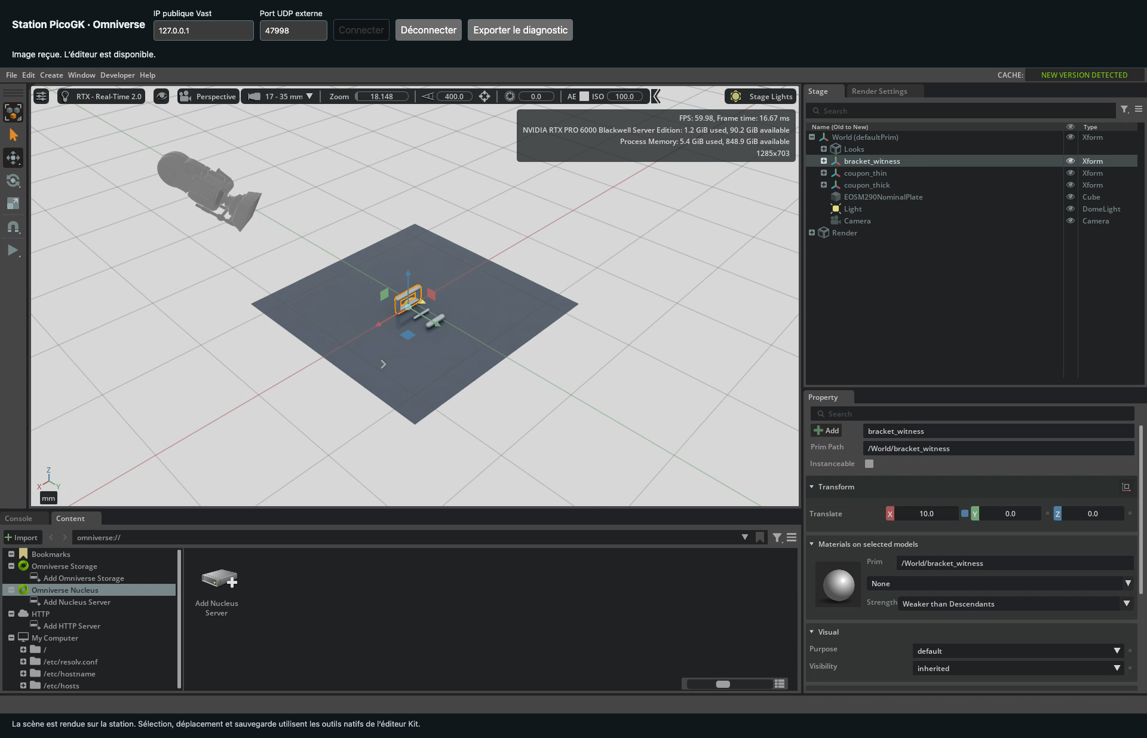
twins/picogk-station-demo/qualification/runtime/omniverse-ui/picogk-kit-10mm-proof.png
