cluster2600/porscheparts/twins/picogk-station-demo/qualification/runtime/omniverse-ui/picogk-kit-filename-corrected.png

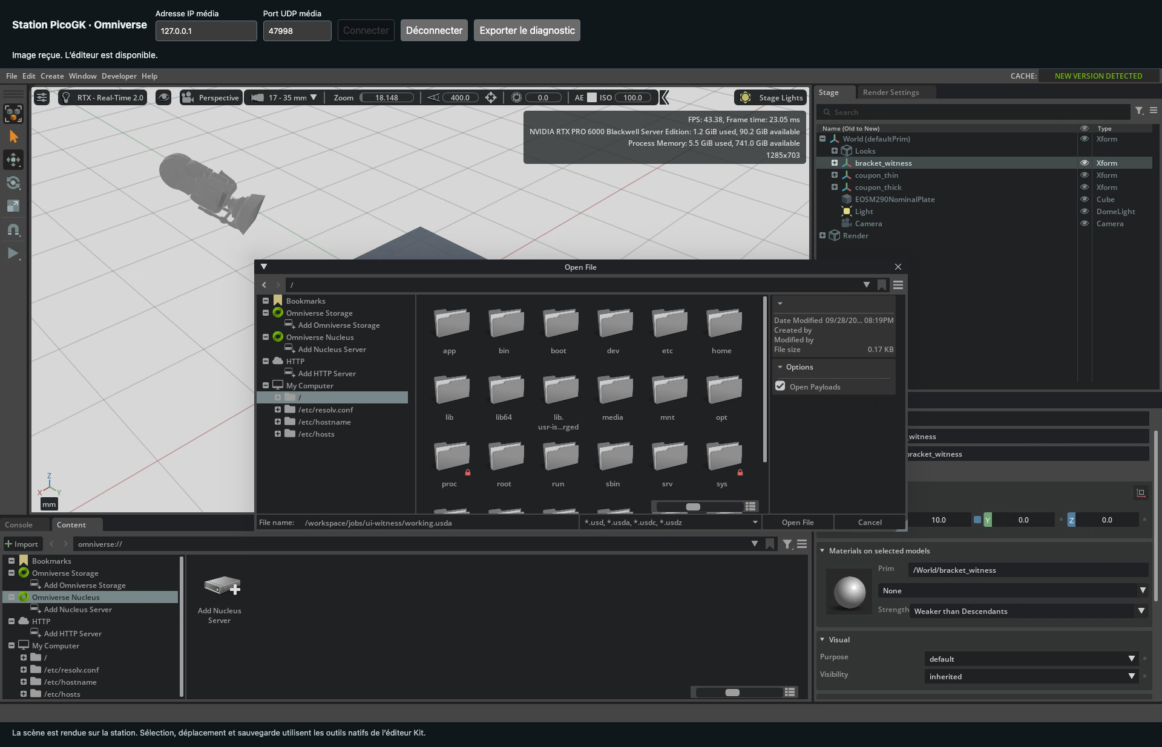
twins/picogk-station-demo/qualification/runtime/omniverse-ui/picogk-kit-filename-corrected.png
