cluster2600/porscheparts/twins/picogk-station-demo/qualification/runtime/omniverse-ui/picogk-kit-native-initial.png

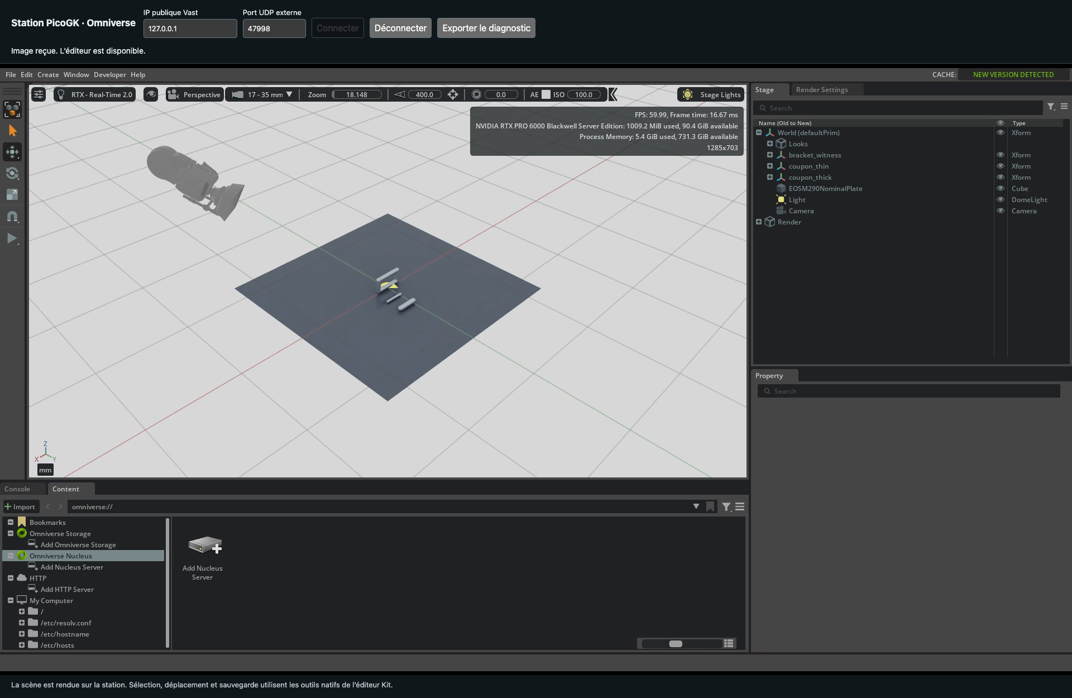
twins/picogk-station-demo/qualification/runtime/omniverse-ui/picogk-kit-native-initial.png
