cluster2600/porscheparts/twins/picogk-station-demo/qualification/runtime/ovrtx-after-edit/render-after.png

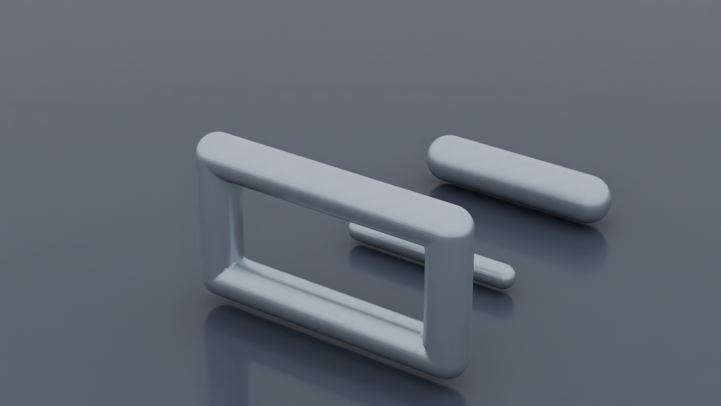
twins/picogk-station-demo/qualification/runtime/ovrtx-after-edit/render-after.png
