cluster2600/porscheparts/twins/picogk-station-demo/qualification/runtime/ovrtx-gpu3/render.png

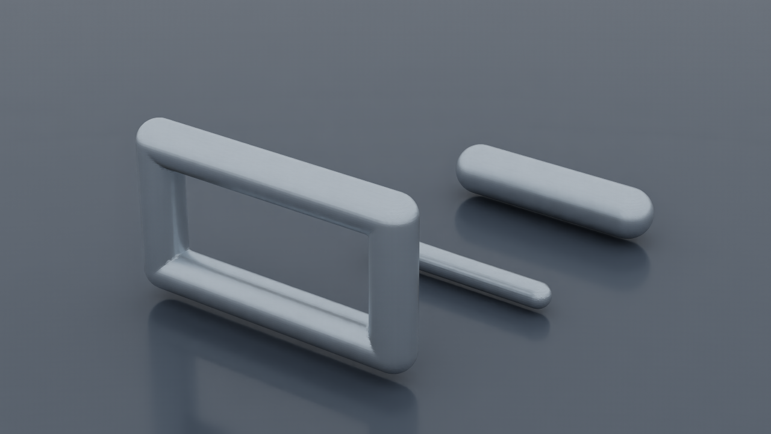
twins/picogk-station-demo/qualification/runtime/ovrtx-gpu3/render.png
