cluster2600/porscheparts/twins/reference-917-engine/evidence/f43-scan-contour-patch/917-head-f43-scan-contour-section.png

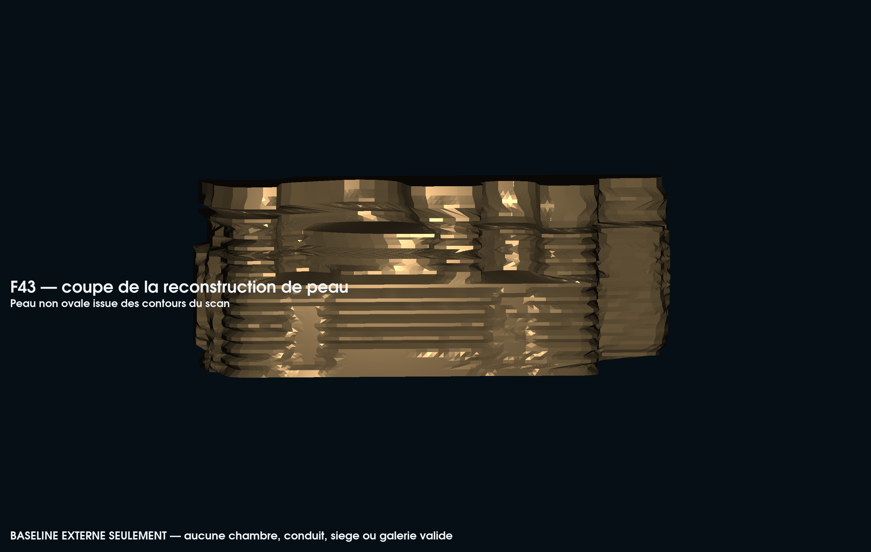
twins/reference-917-engine/evidence/f43-scan-contour-patch/917-head-f43-scan-contour-section.png
