cluster2600/porscheparts/twins/reference-917-engine/evidence/f47-cae-loads/figures/f47-cae-load-envelopes.png

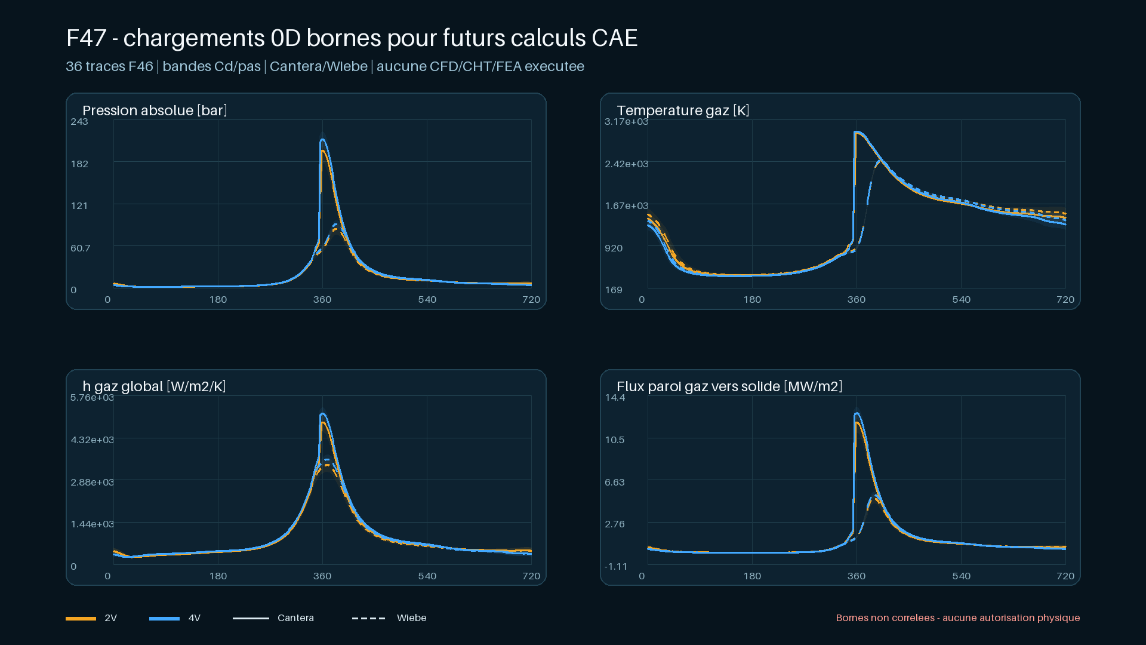
twins/reference-917-engine/evidence/f47-cae-loads/figures/f47-cae-load-envelopes.png
