cluster2600/porscheparts/twins/reference-917-engine/evidence/f47-internal-brep/917-head-f47-2v-4v-sections.png

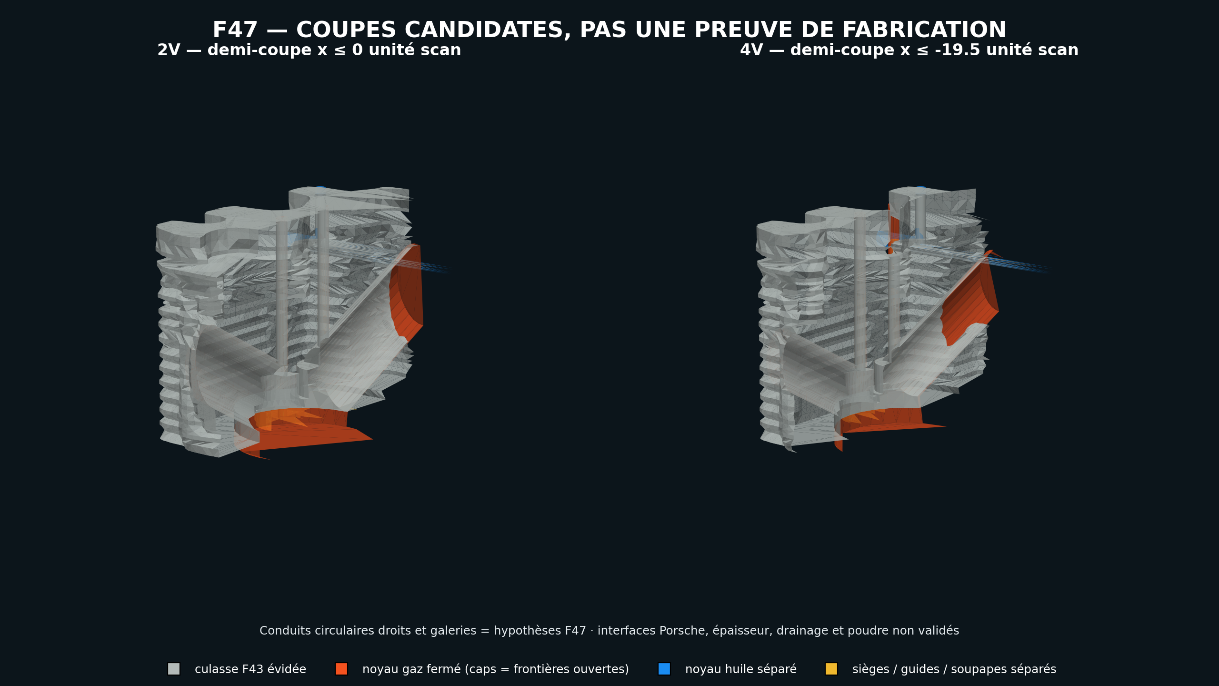
twins/reference-917-engine/evidence/f47-internal-brep/917-head-f47-2v-4v-sections.png
