cluster2600/porscheparts/twins/reference-917-engine/evidence/f48-cfd-domains/917-f48-cfd-domain-overview.png

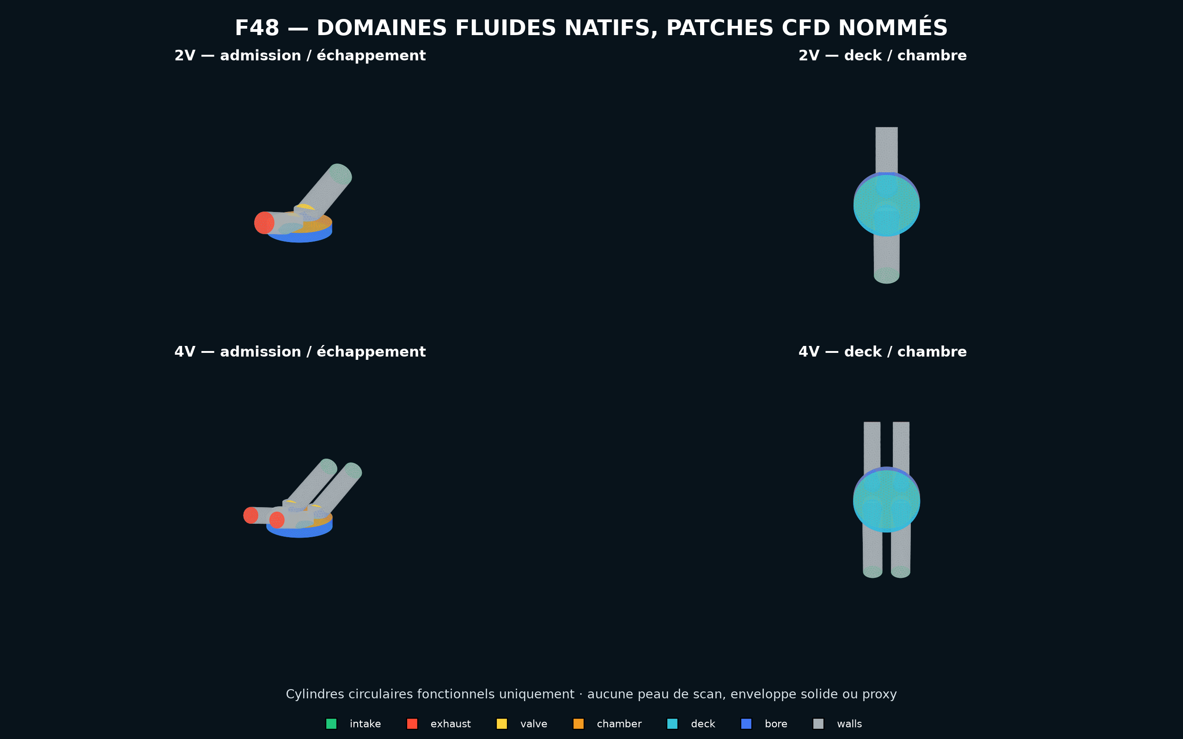
twins/reference-917-engine/evidence/f48-cfd-domains/917-f48-cfd-domain-overview.png
