cluster2600/porscheparts/twins/reference-917-engine/evidence/f49-cfd-cht/917-f49-openfoam-flow-comparison.png

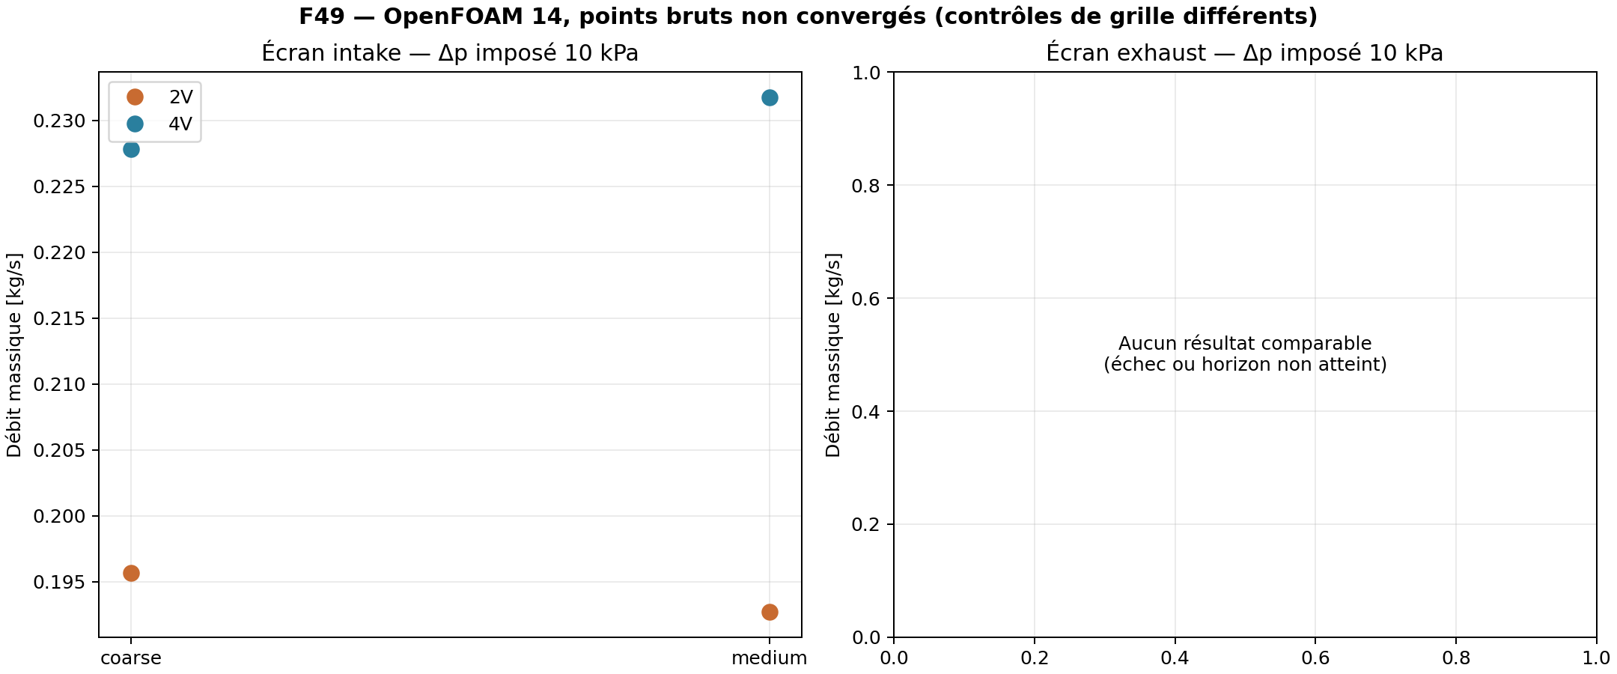
twins/reference-917-engine/evidence/f49-cfd-cht/917-f49-openfoam-flow-comparison.png
