cluster2600/porscheparts/twins/reference-917-engine/evidence/f50-cfd-recovery/917-f50-incompressible-grid-comparison.png

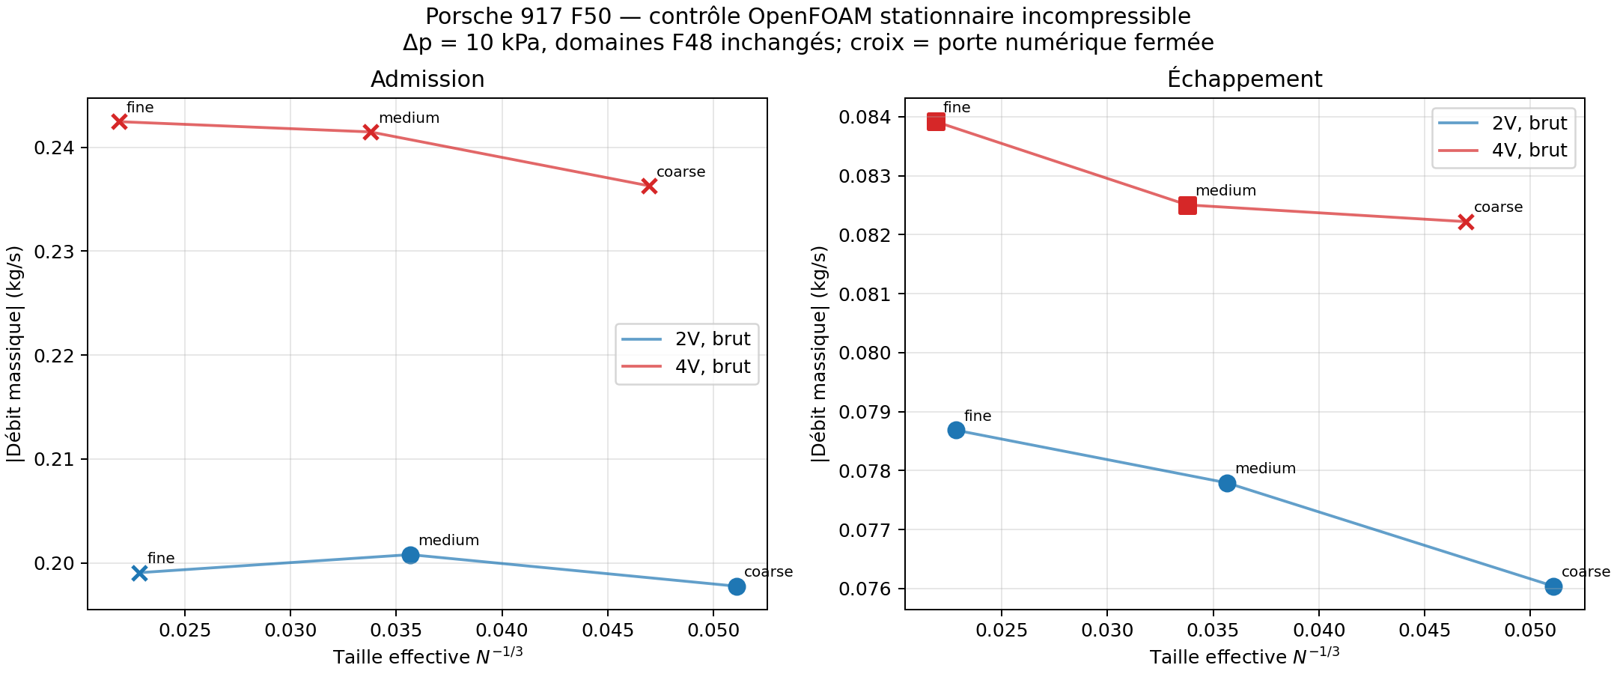
twins/reference-917-engine/evidence/f50-cfd-recovery/917-f50-incompressible-grid-comparison.png
