cluster2600/porscheparts/twins/reference-917-engine/evidence/f50-thermomechanical/f50-local-deck-2v-fields.png

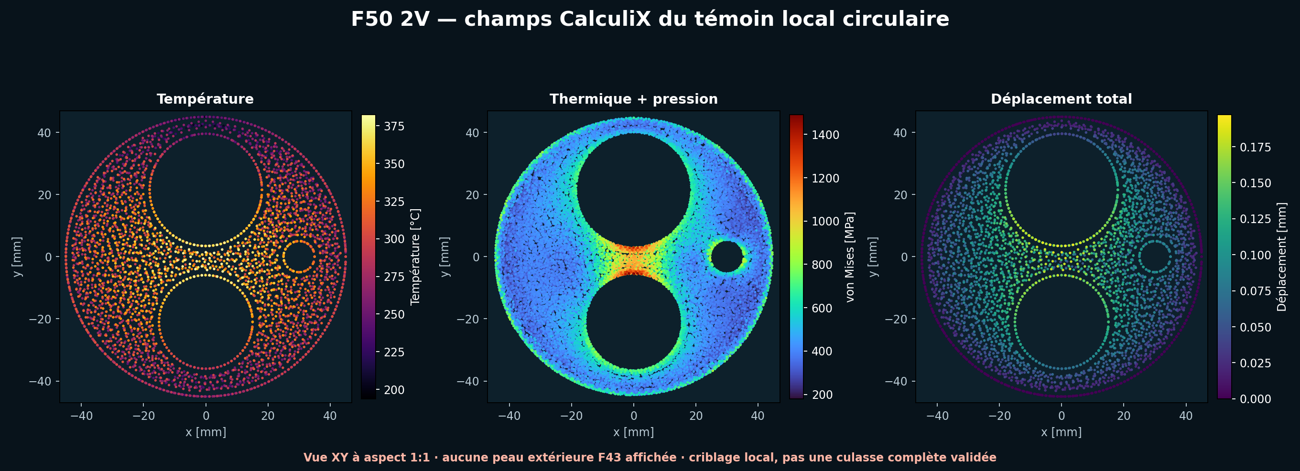
twins/reference-917-engine/evidence/f50-thermomechanical/f50-local-deck-2v-fields.png
