cluster2600/porscheparts/parts/993-eng-intake-valve-f1-0001/README.md

<!-- generated by scripts/render_part_pages.py - do not edit by hand -->

<div align="center">

# 993 intake valve - F1 proxy and titanium variant

**`993-ENG-INTAKE-VALVE-F1-0001`** · Porsche 993 · 1994–1998

  

</div>

> [!CAUTION]
> **Not ready to print, and not a copy of the original part.** The model shown here is a
> concept block for studying the part in software:
> - validation status `concept`: nothing has been checked against a real part;
> - geometry `estimated`: its dimensions are estimated design variables, not measured on the original part;
> - safety class `prohibited_pending_engineering`;
> - no part in this repository is released — read [SAFETY.md](../../SAFETY.md).

<table><tr>
<td width="50%" valign="top">
<b>Original part</b><br><br>
The original part is documented — pictures, catalogue entries or published data — on these pages. They are copyrighted, so they are linked here, not copied:<br><br>
↗ <a href="https://www.fvd.net/de/shop/einlassventil-49mm-993-94-95-turbo-95-98-m64-05-06-07-08-60-nicht-natrium-gekuehlt-99310540902eq1-99310540902~p306501">FVD - Declared 993 intake valve dimensions</a><br>
</td>
<td width="50%" valign="top" align="center">
<b>This repository's concept model</b><br><br>
Concept CAD block for 993 intake valve - F1 proxy and titanium variant<br>
<sub>Concept CAD block, 49.1 × 49.1 × 109.0 mm — <b>not</b> the original part, not a print file, not evidence of fit.</sub>
</td>
</tr></table>

> [!CAUTION]
> **Prohibited pending engineering** — risk, or insufficient data. Never published as a released part.

## What it is

Non-functional parametric proxy for comparing the envelope and mass of a 993 intake valve with a 49 mm head and 8 mm stem, with a Ti-6Al-4V variant explicitly limited to simulation.

## What it does on the car

Mass simulation, collision preparation and envelope check only

## At a glance

| | |
|---|---|
| Porsche part numbers | 99310540902 |
| variants | `993_C2`, `993_C4`, `993_Turbo` |
| candidate material | Ti-6Al-4V Grade 5 |
| candidate process | DMLS |
| safety class | `prohibited_pending_engineering` |
| validation status | `concept` |
| geometry | estimated, master build123d |

## Where it stands

```mermaid
flowchart LR
    L0["concept"]
    L1["dimensionally_reviewed"]
    L2["prototype_fitted"]
    L3["functionally_tested"]
    L4["engineering_reviewed"]
    L5["released"]
    L0 --> L1 --> L2 --> L3 --> L4 --> L5
    X["⛔ prohibited pending engineering"]
    L0 -. blocked .-> X
    classDef here fill:#fff4d6,stroke:#b7791f,color:#1a1a1a,stroke-width:3px;
    classDef done fill:#e3f1e6,stroke:#2e7d32,color:#1a1a1a;
    classDef todo fill:#f4f4f4,stroke:#9e9e9e,color:#6b6b6b;
    classDef stop fill:#fde2e1,stroke:#c0392b,color:#1a1a1a;
    class L0 here
    class L1 todo
    class L2 todo
    class L3 todo
    class L4 todo
    class L5 todo
    class X stop
```

*Validation ladder of `catalog/schemas/part.schema.json`; this record is at `concept`.*

## Views

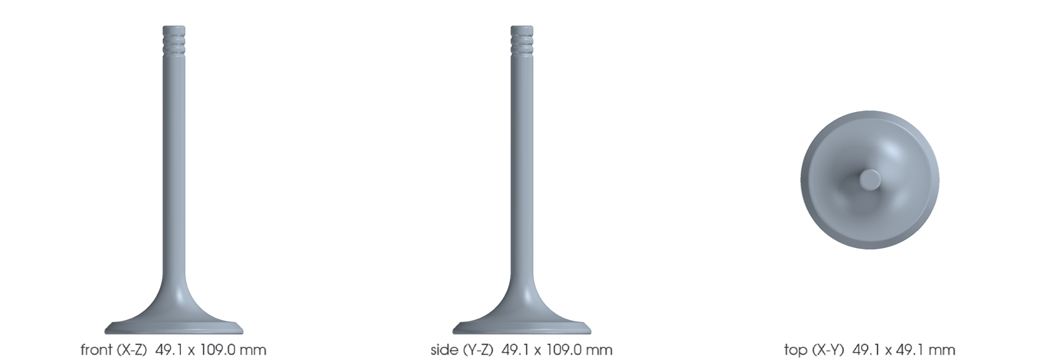
[picture p163: parts/993-eng-intake-valve-f1-0001/media/views.png]
Front, side and top orthographic views


*Orthographic views of the same concept CAD, with its bounding dimensions — not drawings of the original part.*

## What's in this folder

| folder | what it holds | files |
|---|---|---|
| `derived/` | CAD exports generated from the source (STEP for CAD tools, STL for meshing) | [`derived/993-intake-49-f1-picogk.json`](derived/993-intake-49-f1-picogk.json), [`derived/993-intake-49-f1-picogk.stl`](derived/993-intake-49-f1-picogk.stl), [`derived/993-intake-49-f1.step`](derived/993-intake-49-f1.step) |
| `media/` | concept-model views rendered from the CAD by `scripts/render_part_previews.py` — not pictures of the original | [`media/preview.json`](media/preview.json), [`media/preview.png`](media/preview.png), [`media/views.png`](media/views.png) |
| `source/` | parametric source — the editable master that generates the geometry | [`source/picogk.json`](source/picogk.json) |

## Read more

- **Full description page**, with sources and evidence: [docs/pieces/993-eng-intake-valve-f1-0001.md](../../docs/pieces/993-eng-intake-valve-f1-0001.md)
- **Catalogue record** (source of truth): [`catalog/parts/993-eng-intake-valve-f1-0001.json`](../../catalog/parts/993-eng-intake-valve-f1-0001.json)
- **Safety rules**: [SAFETY.md](../../SAFETY.md)

---

*This page is generated from the catalogue record by `scripts/render_part_pages.py` and checked by `make check`. Edit the record, not this page.*
