cluster2600/porscheparts/parts/993-eng-intake-valve-ti64-hollow-f0-0001/README.md

<!-- generated by scripts/render_part_pages.py - do not edit by hand -->

<div align="center">

# 993 hollow Ti64 intake valve, F0 LPBF concept

**`993-ENG-INTAKE-VALVE-TI64-HOLLOW-F0-0001`** · Porsche 993 · 1994–1998

  

</div>

> [!CAUTION]
> **Not ready to print, and not a copy of the original part.** The model shown here is a
> concept block for studying the part in software:
> - validation status `concept`: nothing has been checked against a real part;
> - geometry `mixed`: its dimensions are partly sourced, partly assumed, not measured on the original part;
> - safety class `prohibited_pending_engineering`;
> - no part in this repository is released — read [SAFETY.md](../../SAFETY.md).

<table><tr>
<td width="50%" valign="top">
<b>Original part</b><br><br>
The original part is documented — pictures, catalogue entries or published data — on these pages. They are copyrighted, so they are linked here, not copied:<br><br>
↗ <a href="https://www.fvd.net/de/shop/einlassventil-49mm-993-94-95-turbo-95-98-m64-05-06-07-08-60-nicht-natrium-gekuehlt-99310540902eq1-99310540902~p306501">FVD - declared 993 intake valve dimensions</a><br>
↗ <a href="https://porschefanatics.com/engine/993/">PorscheFanatics - titanium valve context for the 993 engine</a><br>
↗ <a href="https://www.elferclassic.de/technik/techdaten/993-turbo-95-98-techdat.php">elferclassic - 993 Turbo technical data</a><br>
</td>
<td width="50%" valign="top" align="center">
<b>This repository's concept model</b><br><br>
Concept CAD block for 993 hollow Ti64 intake valve, F0 LPBF concept<br>
<sub>Concept CAD block, 49.1 × 49.1 × 109.1 mm — <b>not</b> the original part, not a print file, not evidence of fit.</sub>
</td>
</tr></table>

> [!CAUTION]
> **Prohibited pending engineering** — risk, or insufficient data. Never published as a released part.

## What it is

Independent concept of a hollow Ti-6Al-4V intake valve with four internal ribs and an open axial bore for depowdering. Only the head diameter, stem diameter, product envelope, declared mass and part number are published; all functional geometry remains an F0 hypothesis.

## What it does on the car

CAD, DfAM, mass, harmonic kinematics, axial load, buckling, natural mode and thermal screening; no manufacturing, installation or engine start-up authorized

## At a glance

| | |
|---|---|
| Porsche part numbers | 99310540902 |
| variants | `993_C2`, `993_C4`, `993_Turbo`, `M64_research` |
| candidate material | Ti-6Al-4V Grade 5 LPBF, screening |
| candidate process | LPBF |
| safety class | `prohibited_pending_engineering` |
| validation status | `concept` |
| geometry | mixed, master build123d |

## Where it stands

```mermaid
flowchart LR
    L0["concept"]
    L1["dimensionally_reviewed"]
    L2["prototype_fitted"]
    L3["functionally_tested"]
    L4["engineering_reviewed"]
    L5["released"]
    L0 --> L1 --> L2 --> L3 --> L4 --> L5
    X["⛔ prohibited pending engineering"]
    L0 -. blocked .-> X
    classDef here fill:#fff4d6,stroke:#b7791f,color:#1a1a1a,stroke-width:3px;
    classDef done fill:#e3f1e6,stroke:#2e7d32,color:#1a1a1a;
    classDef todo fill:#f4f4f4,stroke:#9e9e9e,color:#6b6b6b;
    classDef stop fill:#fde2e1,stroke:#c0392b,color:#1a1a1a;
    class L0 here
    class L1 todo
    class L2 todo
    class L3 todo
    class L4 todo
    class L5 todo
    class X stop
```

*Validation ladder of `catalog/schemas/part.schema.json`; this record is at `concept`.*

## Views

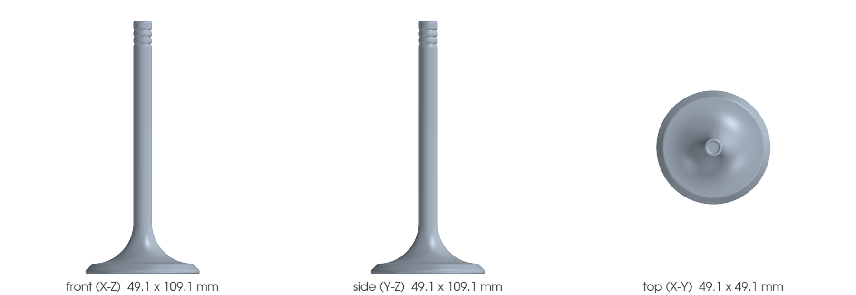
[picture p164: parts/993-eng-intake-valve-ti64-hollow-f0-0001/media/views.png]
Front, side and top orthographic views


*Orthographic views of the same concept CAD, with its bounding dimensions — not drawings of the original part.*

## Screens and evidence images

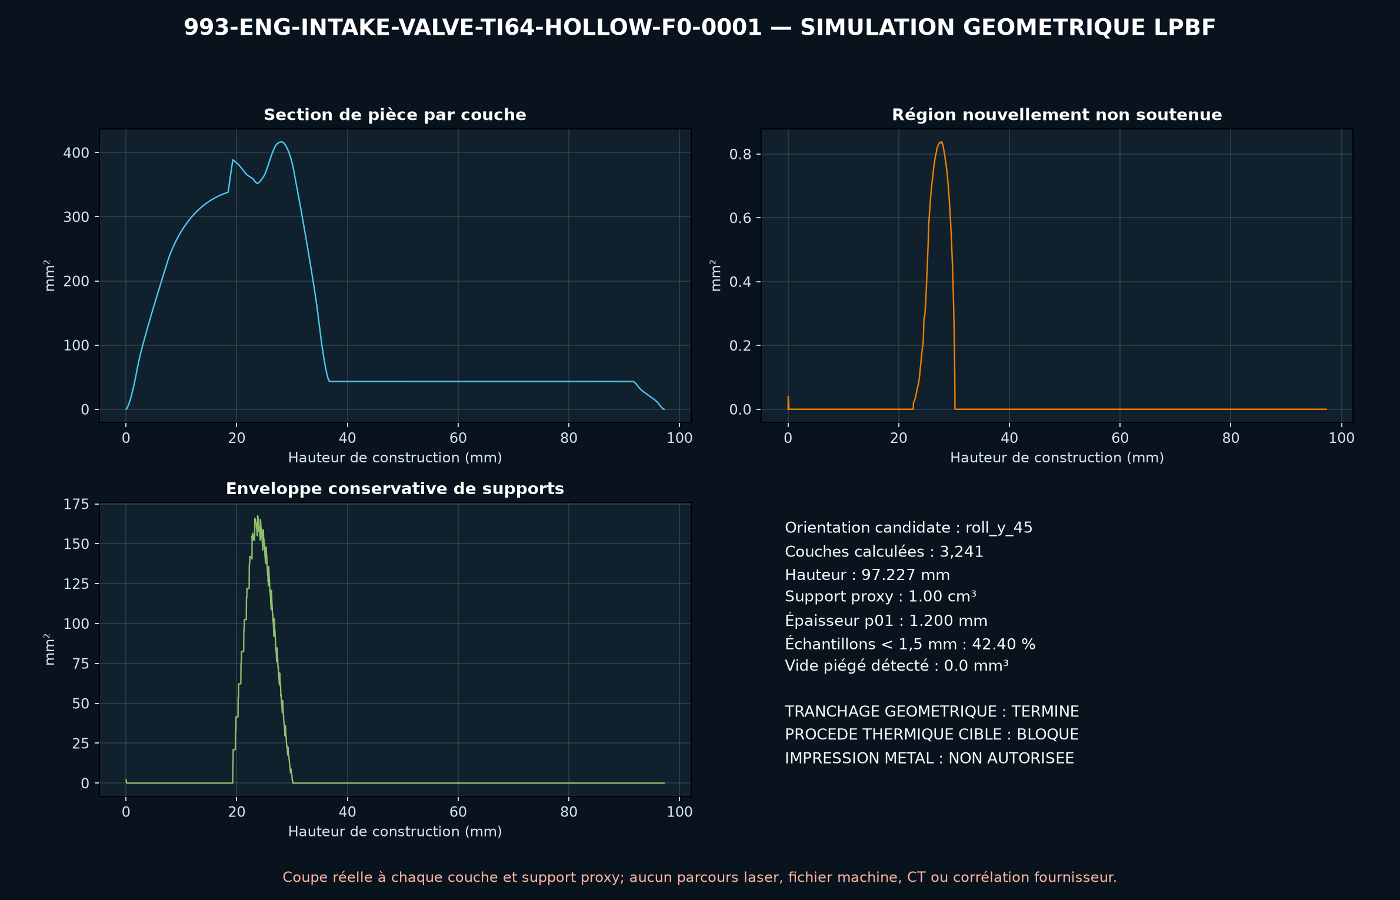
[picture p165: parts/993-eng-intake-valve-ti64-hollow-f0-0001/evidence/lpbf-f0/993-eng-intake-valve-ti64-hollow-f0-0001-lpbf-geometry-screen.png]
993-eng-intake-valve-ti64-hollow-f0-0001-lpbf-geometry-screen


*`evidence/lpbf-f0/993-eng-intake-valve-ti64-hollow-f0-0001-lpbf-geometry-screen.png` — a screening output, not a validation.*

## What's in this folder

| folder | what it holds | files |
|---|---|---|
| `derived/` | CAD exports generated from the source (STEP for CAD tools, STL for meshing) | [`derived/intake_valve_ti64_hollow_f0-picogk.json`](derived/intake_valve_ti64_hollow_f0-picogk.json), [`derived/intake_valve_ti64_hollow_f0-picogk.stl`](derived/intake_valve_ti64_hollow_f0-picogk.stl), [`derived/intake_valve_ti64_hollow_f0.step`](derived/intake_valve_ti64_hollow_f0.step), [`derived/intake_valve_ti64_hollow_f0.stl`](derived/intake_valve_ti64_hollow_f0.stl) |
| `evidence/` | screens, reports and manifests — **pinned by SHA-256, never edited by hand** | [`evidence/engineering-screen.json`](evidence/engineering-screen.json), [`evidence/lpbf-f0/993-eng-intake-valve-ti64-hollow-f0-0001-layer-metrics.csv`](evidence/lpbf-f0/993-eng-intake-valve-ti64-hollow-f0-0001-layer-metrics.csv), [`evidence/lpbf-f0/993-eng-intake-valve-ti64-hollow-f0-0001-lpbf-geometry-manifest.json`](evidence/lpbf-f0/993-eng-intake-valve-ti64-hollow-f0-0001-lpbf-geometry-manifest.json), [`evidence/lpbf-f0/993-eng-intake-valve-ti64-hollow-f0-0001-lpbf-geometry-report.json`](evidence/lpbf-f0/993-eng-intake-valve-ti64-hollow-f0-0001-lpbf-geometry-report.json), [`evidence/lpbf-f0/993-eng-intake-valve-ti64-hollow-f0-0001-lpbf-geometry-screen.png`](evidence/lpbf-f0/993-eng-intake-valve-ti64-hollow-f0-0001-lpbf-geometry-screen.png) |
| `media/` | concept-model views rendered from the CAD by `scripts/render_part_previews.py` — not pictures of the original | [`media/preview.json`](media/preview.json), [`media/preview.png`](media/preview.png), [`media/views.png`](media/views.png) |
| `source/` | parametric source — the editable master that generates the geometry | [`source/intake_valve.py`](source/intake_valve.py), [`source/picogk.json`](source/picogk.json) |

## Read more

- **Full description page**, with sources and evidence: [docs/pieces/993-eng-intake-valve-ti64-hollow-f0-0001.md](../../docs/pieces/993-eng-intake-valve-ti64-hollow-f0-0001.md)
- **Catalogue record** (source of truth): [`catalog/parts/993-eng-intake-valve-ti64-hollow-f0-0001.json`](../../catalog/parts/993-eng-intake-valve-ti64-hollow-f0-0001.json)
- **Design dossier**: [993_INTAKE_VALVE_TI64_HOLLOW_F0](../../docs/993/993_INTAKE_VALVE_TI64_HOLLOW_F0.md)
- **Safety rules**: [SAFETY.md](../../SAFETY.md)

---

*This page is generated from the catalogue record by `scripts/render_part_pages.py` and checked by `make check`. Edit the record, not this page.*
