cluster2600/porscheparts/parts/993-eng-intercooler-end-tank-alsi10mg-f0-0001/README.md

<!-- generated by scripts/render_part_pages.py - do not edit by hand -->

<div align="center">

# 993 Turbo intercooler end tank, AlSi10Mg concept F0

**`993-ENG-INTERCOOLER-END-TANK-ALSI10MG-F0-0001`** · Porsche 993 · 1995–1998

  

</div>

> [!CAUTION]
> **Not ready to print, and not a copy of the original part.** The model shown here is a
> concept block for studying the part in software:
> - validation status `concept`: nothing has been checked against a real part;
> - geometry `mixed`: its dimensions are partly sourced, partly assumed, not measured on the original part;
> - safety class `prohibited_pending_engineering`;
> - no part in this repository is released — read [SAFETY.md](../../SAFETY.md).

<table><tr>
<td width="50%" valign="top">
<b>Original part</b><br><br>
The original part is documented — pictures, catalogue entries or published data — on these pages. They are copyrighted, so they are linked here, not copied:<br><br>
↗ <a href="https://www.tatechnix.de/tatechnix/gx/ta-technix-produkte/performance-parts/intercooler/-138841/911-141181/993-159629/ta-technix-intercooler-suitable-for-porsche-911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">TA Technix - intercooler for Porsche 911 Turbo 993</a><br>
↗ <a href="https://albertmotorsport.de/en/993-turbo-gt2-engine/993-tt-gt2-intercooler-aluminum-oem-replacement-porsche-911">Albert Motorsport - 993 Turbo/GT2 aluminum intercooler</a><br>
↗ <a href="https://porschefanatics.com/engine/993/">PorscheFanatics - 993 charge-air cooling architecture</a><br>
↗ <a href="https://www.elferclassic.de/technik/techdaten/993-turbo-95-98-techdat.php">elferclassic - German technical data for the 993 Turbo</a><br>
</td>
<td width="50%" valign="top" align="center">
<b>This repository's concept model</b><br><br>
Concept CAD block for 993 Turbo intercooler end tank, AlSi10Mg concept F0<br>
<sub>Concept CAD block, 134.1 × 274.1 × 114.1 mm — <b>not</b> the original part, not a print file, not evidence of fit.</sub>
</td>
</tr></table>

> [!CAUTION]
> **Prohibited pending engineering** — risk, or insufficient data. Never published as a released part.

## What it is

Independent concept of a round-to-rectangular-face transition with three open internal guide vanes, used to screen an LPBF AlSi10Mg end tank. The published overall dimensions bound the F0 but define neither the core orientation nor a compatible geometry.

## What it does on the car

CAD, DfAM, flow, pressure loss, pressure, membrane, guided panel, thermal and cycle screening; no manufacture, installation or engine start-up authorized

## At a glance

| | |
|---|---|
| Porsche part numbers | not recorded |
| variants | `993_Turbo`, `993_GT2`, `M64_60_research` |
| candidate material | EOS Aluminium AlSi10Mg for screening |
| candidate process | LPBF |
| safety class | `prohibited_pending_engineering` |
| validation status | `concept` |
| geometry | mixed, master build123d |

## Where it stands

```mermaid
flowchart LR
    L0["concept"]
    L1["dimensionally_reviewed"]
    L2["prototype_fitted"]
    L3["functionally_tested"]
    L4["engineering_reviewed"]
    L5["released"]
    L0 --> L1 --> L2 --> L3 --> L4 --> L5
    X["⛔ prohibited pending engineering"]
    L0 -. blocked .-> X
    classDef here fill:#fff4d6,stroke:#b7791f,color:#1a1a1a,stroke-width:3px;
    classDef done fill:#e3f1e6,stroke:#2e7d32,color:#1a1a1a;
    classDef todo fill:#f4f4f4,stroke:#9e9e9e,color:#6b6b6b;
    classDef stop fill:#fde2e1,stroke:#c0392b,color:#1a1a1a;
    class L0 here
    class L1 todo
    class L2 todo
    class L3 todo
    class L4 todo
    class L5 todo
    class X stop
```

*Validation ladder of `catalog/schemas/part.schema.json`; this record is at `concept`.*

## Views

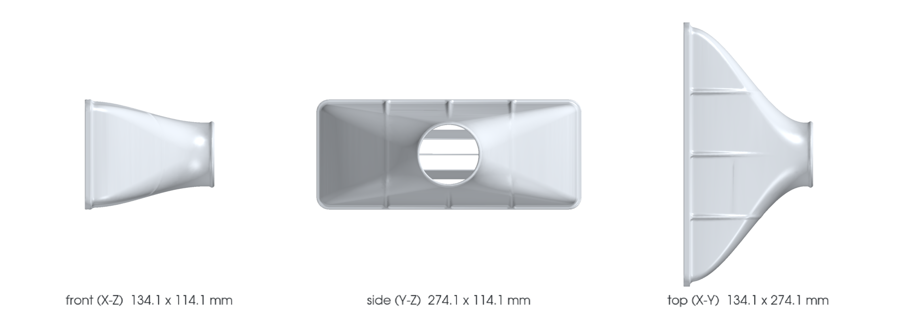
[picture p169: parts/993-eng-intercooler-end-tank-alsi10mg-f0-0001/media/views.png]
Front, side and top orthographic views


*Orthographic views of the same concept CAD, with its bounding dimensions — not drawings of the original part.*

## Screens and evidence images

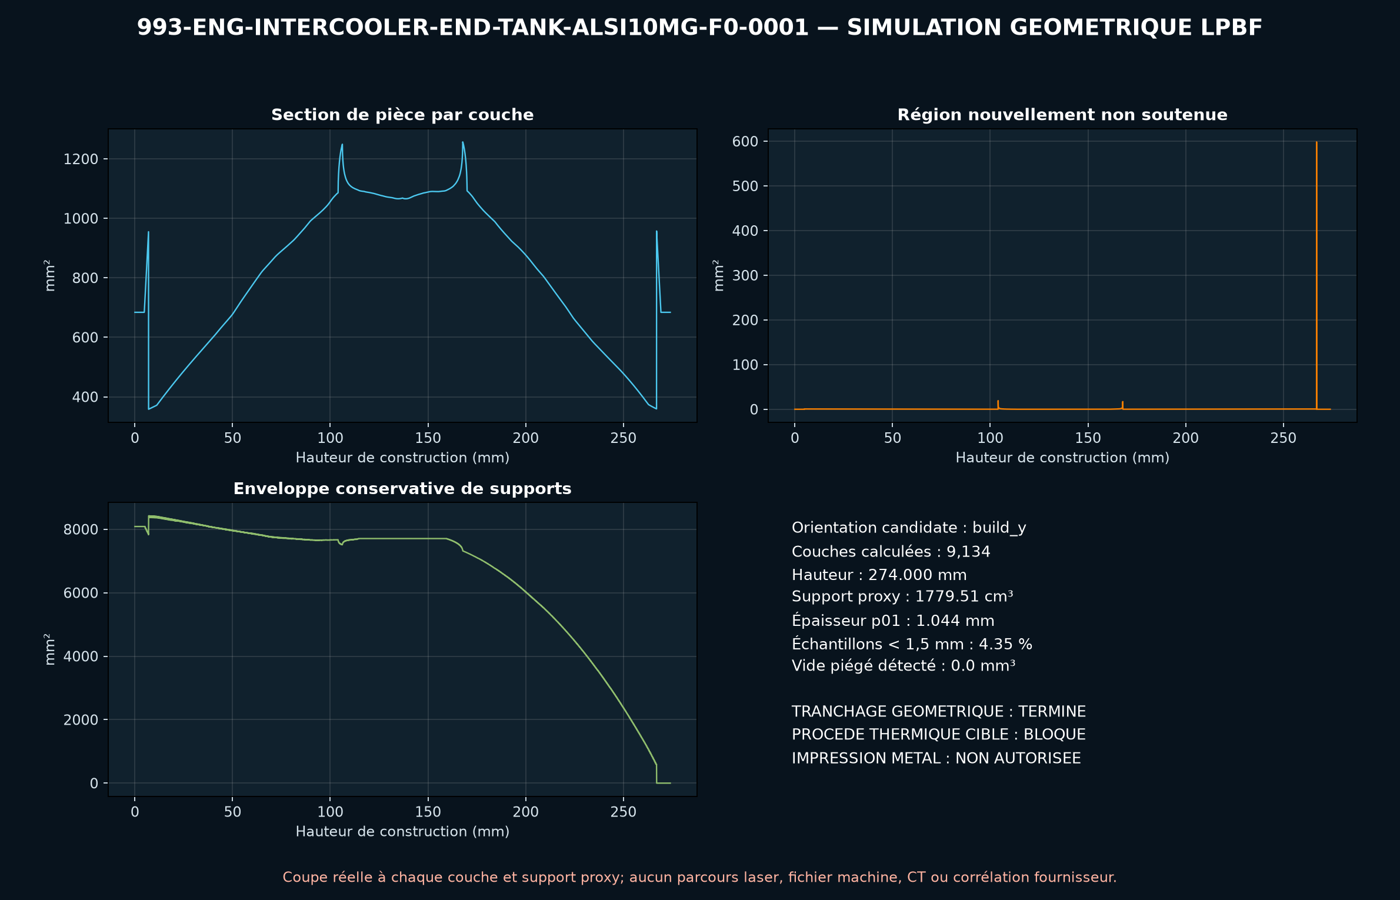
[picture p170: parts/993-eng-intercooler-end-tank-alsi10mg-f0-0001/evidence/lpbf-f0/993-eng-intercooler-end-tank-alsi10mg-f0-0001-lpbf-geometry-screen.png]
993-eng-intercooler-end-tank-alsi10mg-f0-0001-lpbf-geometry-screen


*`evidence/lpbf-f0/993-eng-intercooler-end-tank-alsi10mg-f0-0001-lpbf-geometry-screen.png` — a screening output, not a validation.*

## What's in this folder

| folder | what it holds | files |
|---|---|---|
| `derived/` | CAD exports generated from the source (STEP for CAD tools, STL for meshing) | [`derived/end_tank_alsi10mg_f0-picogk.json`](derived/end_tank_alsi10mg_f0-picogk.json), [`derived/end_tank_alsi10mg_f0-picogk.stl`](derived/end_tank_alsi10mg_f0-picogk.stl), [`derived/end_tank_alsi10mg_f0.step`](derived/end_tank_alsi10mg_f0.step), [`derived/end_tank_alsi10mg_f0.stl`](derived/end_tank_alsi10mg_f0.stl) |
| `evidence/` | screens, reports and manifests — **pinned by SHA-256, never edited by hand** | [`evidence/engineering-screen.json`](evidence/engineering-screen.json), [`evidence/lpbf-f0/993-eng-intercooler-end-tank-alsi10mg-f0-0001-layer-metrics.csv`](evidence/lpbf-f0/993-eng-intercooler-end-tank-alsi10mg-f0-0001-layer-metrics.csv), [`evidence/lpbf-f0/993-eng-intercooler-end-tank-alsi10mg-f0-0001-lpbf-geometry-manifest.json`](evidence/lpbf-f0/993-eng-intercooler-end-tank-alsi10mg-f0-0001-lpbf-geometry-manifest.json), [`evidence/lpbf-f0/993-eng-intercooler-end-tank-alsi10mg-f0-0001-lpbf-geometry-report.json`](evidence/lpbf-f0/993-eng-intercooler-end-tank-alsi10mg-f0-0001-lpbf-geometry-report.json), [`evidence/lpbf-f0/993-eng-intercooler-end-tank-alsi10mg-f0-0001-lpbf-geometry-screen.png`](evidence/lpbf-f0/993-eng-intercooler-end-tank-alsi10mg-f0-0001-lpbf-geometry-screen.png) |
| `media/` | concept-model views rendered from the CAD by `scripts/render_part_previews.py` — not pictures of the original | [`media/preview.json`](media/preview.json), [`media/preview.png`](media/preview.png), [`media/views.png`](media/views.png) |
| `source/` | parametric source — the editable master that generates the geometry | [`source/end_tank.py`](source/end_tank.py), [`source/picogk.json`](source/picogk.json) |

## Read more

- **Full description page**, with sources and evidence: [docs/pieces/993-eng-intercooler-end-tank-alsi10mg-f0-0001.md](../../docs/pieces/993-eng-intercooler-end-tank-alsi10mg-f0-0001.md)
- **Catalogue record** (source of truth): [`catalog/parts/993-eng-intercooler-end-tank-alsi10mg-f0-0001.json`](../../catalog/parts/993-eng-intercooler-end-tank-alsi10mg-f0-0001.json)
- **Design dossier**: [993_INTERCOOLER_END_TANK_ALSI10MG_F0](../../docs/993/993_INTERCOOLER_END_TANK_ALSI10MG_F0.md)
- **Safety rules**: [SAFETY.md](../../SAFETY.md)

---

*This page is generated from the catalogue record by `scripts/render_part_pages.py` and checked by `make check`. Edit the record, not this page.*
