cluster2600/porscheparts/parts/993-eng-k16-compressor-wheel-al2139-f1-0001/README.md

<!-- generated by scripts/render_part_pages.py - do not edit by hand -->

<div align="center">

# K16 compressor wheel, Al2139 AM F1 iteration

**`993-ENG-K16-COMPRESSOR-WHEEL-AL2139-F1-0001`** · Porsche 993 · 1995–1998

  

</div>

> [!WARNING]
> **A 1:1 display mock-up is printable — never for use.** [`print/`](print/README.md): the design, unchanged except for MOCK-UP / NOT FOR USE engraved in it, sliced in 9h 29m 16s (60.3 cm³). The part itself stays prohibited ([decision 0011](../../docs/decisions/0011-printable-display-mockups-of-prohibited-parts.md)).

> [!CAUTION]
> **Prohibited, not validated, and not a copy of the original.** The mock-up is a display piece; the model shown here is a
> design whose fit has not been checked against the car:
> - validation status `concept`: nothing has been checked against a real part;
> - geometry `mixed`: its dimensions are partly sourced, partly assumed, not measured on the original part;
> - safety class `prohibited_pending_engineering`;
> - no part in this repository is released — read [SAFETY.md](../../SAFETY.md).

<table><tr>
<td width="50%" valign="top">
<b>Original part</b><br><br>
The original part is documented — pictures, catalogue entries or published data — on these pages. They are copyrighted, so they are linked here, not copied:<br><br>
↗ <a href="https://www.invasionautoproducts.com/94pocark16tu.html">Invasion Auto Products - declared internal data of the right-hand 993 Turbo K16</a><br>
↗ <a href="https://porschefanatics.com/engine/993/">PorscheFanatics - context of 993 turbochargers and wheels</a><br>
↗ <a href="https://github.com/cluster2600/porscheparts/blob/main/docs/993_K16_COMPRESSOR_WHEEL_ALSI10MG_F0.md">Project AlSi10Mg K16 wheel F0</a><br>
↗ <a href="https://www.turbomaster.info/eng/turbocharger-map.php">TurboMaster - principles for reading a compressor map</a><br>
</td>
<td width="50%" valign="top" align="center">
<b>What you can print: a display mock-up</b><br><br>
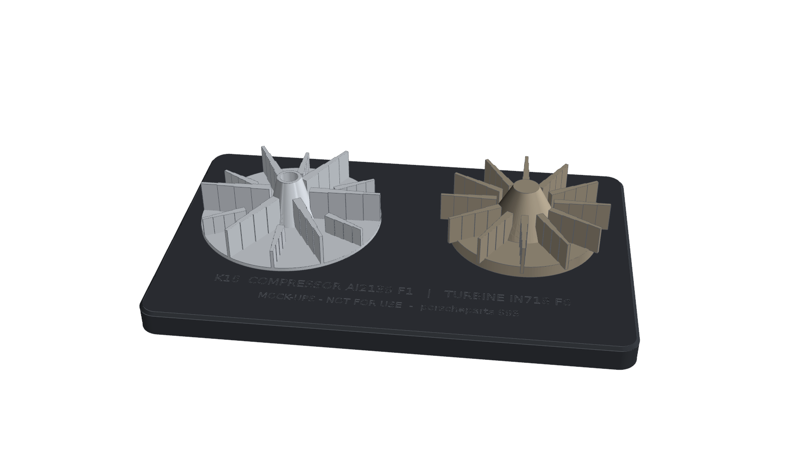
[picture p171: parts/993-eng-k16-compressor-wheel-al2139-f1-0001/print/mockup.png]
Engraved display mock-up of K16 compressor wheel, Al2139 AM F1 iteration
<br>
<sub>1:1 display mock-up with MOCK-UP / NOT FOR USE engraved in it. <b>Never</b> for an engine; not the original part.</sub>
</td>
</tr></table>

> [!CAUTION]
> **Prohibited pending engineering** — risk, or insufficient data. Never published as a released part.

## What it is

Iteration of the rejected AlSi10Mg F0, with Al2139 AM and blades of variable root-to-tip thickness. The 40.6/60.5 mm diameters and the 6+6 blade count remain the only published geometric facts; the F1 passes three ambient algebraic screens without becoming a functional wheel.

## What it does on the car

F0-F1 loop for material and thickness choice, CAD, thermodynamics, rotating disk, centrifugal tension, overspeed, expansion and imbalance; no manufacturing, rotation, installation or start-up authorized

## At a glance

| | |
|---|---|
| Porsche part numbers | not recorded |
| variants | `993_Turbo`, `K16_right_research`, `M64_60_research` |
| candidate material | EOS Aluminium Al2139 AM, M290 60 µm, heat-treated condition, for comparison |
| candidate process | LPBF |
| safety class | `prohibited_pending_engineering` |
| validation status | `concept` |
| geometry | mixed, master build123d |

## Where it stands

```mermaid
flowchart LR
    L0["concept"]
    L1["dimensionally_reviewed"]
    L2["prototype_fitted"]
    L3["functionally_tested"]
    L4["engineering_reviewed"]
    L5["released"]
    L0 --> L1 --> L2 --> L3 --> L4 --> L5
    X["⛔ prohibited pending engineering"]
    L0 -. blocked .-> X
    classDef here fill:#fff4d6,stroke:#b7791f,color:#1a1a1a,stroke-width:3px;
    classDef done fill:#e3f1e6,stroke:#2e7d32,color:#1a1a1a;
    classDef todo fill:#f4f4f4,stroke:#9e9e9e,color:#6b6b6b;
    classDef stop fill:#fde2e1,stroke:#c0392b,color:#1a1a1a;
    class L0 here
    class L1 todo
    class L2 todo
    class L3 todo
    class L4 todo
    class L5 todo
    class X stop
```

*Validation ladder of `catalog/schemas/part.schema.json`; this record is at `concept`.*

## Views

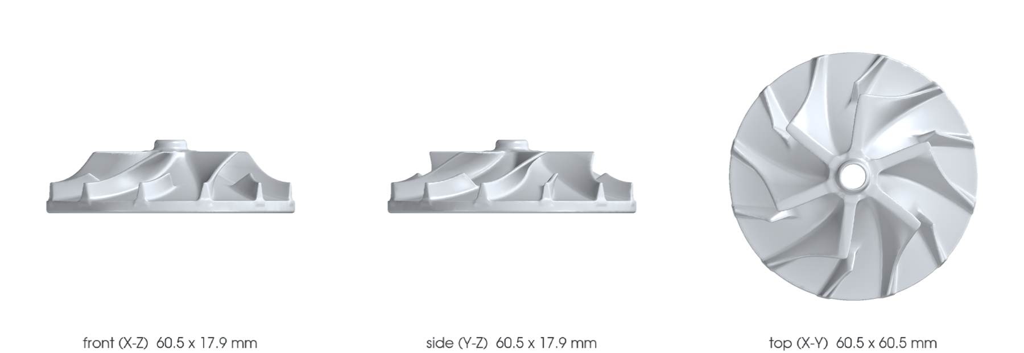
[picture p172: parts/993-eng-k16-compressor-wheel-al2139-f1-0001/media/views.png]
Front, side and top orthographic views


*Orthographic views of the same concept CAD, with its bounding dimensions — not drawings of the original part.*

## Screens and evidence images

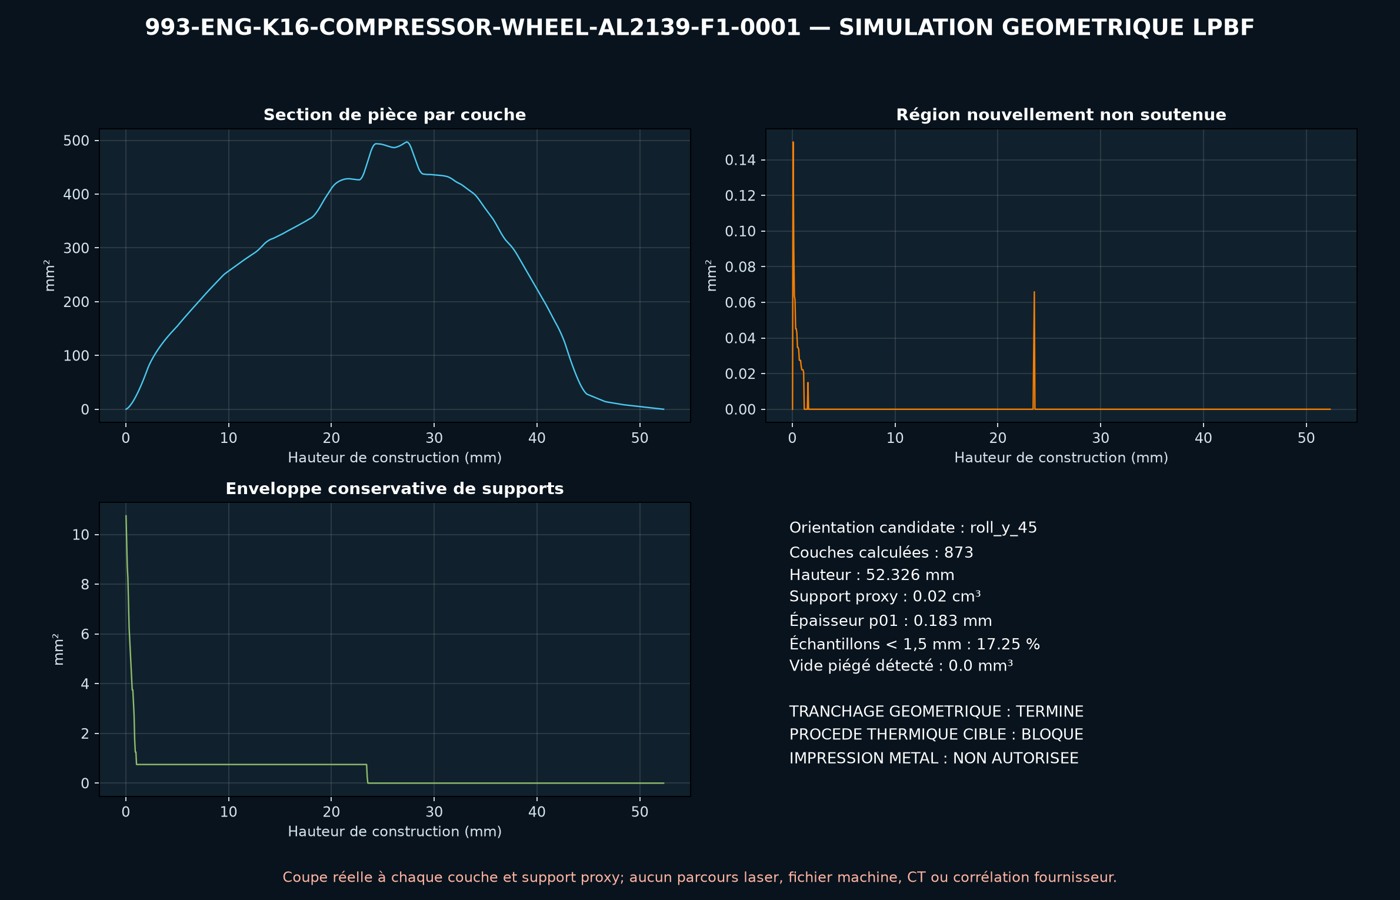
[picture p173: parts/993-eng-k16-compressor-wheel-al2139-f1-0001/evidence/lpbf-f0/993-eng-k16-compressor-wheel-al2139-f1-0001-lpbf-geometry-screen.png]
993-eng-k16-compressor-wheel-al2139-f1-0001-lpbf-geometry-screen


*`evidence/lpbf-f0/993-eng-k16-compressor-wheel-al2139-f1-0001-lpbf-geometry-screen.png` — a screening output, not a validation.*

display

*`print/display.png` — a screening output, not a validation.*

mockup

*`print/mockup.png` — a screening output, not a validation.*

## What's in this folder

| folder | what it holds | files |
|---|---|---|
| `derived/` | CAD exports generated from the source (STEP for CAD tools, STL for meshing) | [`derived/compressor_wheel_al2139_f1-picogk.json`](derived/compressor_wheel_al2139_f1-picogk.json), [`derived/compressor_wheel_al2139_f1-picogk.stl`](derived/compressor_wheel_al2139_f1-picogk.stl), [`derived/compressor_wheel_al2139_f1.step`](derived/compressor_wheel_al2139_f1.step), [`derived/compressor_wheel_al2139_f1.stl`](derived/compressor_wheel_al2139_f1.stl) |
| `evidence/` | screens, reports and manifests — **pinned by SHA-256, never edited by hand** | [`evidence/engineering-screen.json`](evidence/engineering-screen.json), [`evidence/lpbf-f0/993-eng-k16-compressor-wheel-al2139-f1-0001-layer-metrics.csv`](evidence/lpbf-f0/993-eng-k16-compressor-wheel-al2139-f1-0001-layer-metrics.csv), [`evidence/lpbf-f0/993-eng-k16-compressor-wheel-al2139-f1-0001-lpbf-geometry-manifest.json`](evidence/lpbf-f0/993-eng-k16-compressor-wheel-al2139-f1-0001-lpbf-geometry-manifest.json), [`evidence/lpbf-f0/993-eng-k16-compressor-wheel-al2139-f1-0001-lpbf-geometry-report.json`](evidence/lpbf-f0/993-eng-k16-compressor-wheel-al2139-f1-0001-lpbf-geometry-report.json), [`evidence/lpbf-f0/993-eng-k16-compressor-wheel-al2139-f1-0001-lpbf-geometry-screen.png`](evidence/lpbf-f0/993-eng-k16-compressor-wheel-al2139-f1-0001-lpbf-geometry-screen.png) |
| `media/` | concept-model views rendered from the CAD by `scripts/render_part_previews.py` — not pictures of the original | [`media/preview.json`](media/preview.json), [`media/preview.png`](media/preview.png), [`media/views.png`](media/views.png) |
| `print/` | **ready-to-print files**: 3MF project, STL and instructions | [`print/display.png`](print/display.png), [`print/k16_compressor_wheel_mockup.stl`](print/k16_compressor_wheel_mockup.stl), [`print/k16_display_pair_plate.3mf`](print/k16_display_pair_plate.3mf), [`print/k16_display_pair_plate.step`](print/k16_display_pair_plate.step), [`print/k16_display_pair_plate.stl`](print/k16_display_pair_plate.stl), [`print/k16_display_stand.stl`](print/k16_display_stand.stl), [`print/mockup.png`](print/mockup.png), [`print/print.json`](print/print.json) |
| `source/` | parametric source — the editable master that generates the geometry | [`source/compressor_wheel_f1.py`](source/compressor_wheel_f1.py), [`source/k16_display_pair.py`](source/k16_display_pair.py), [`source/picogk.json`](source/picogk.json), [`source/render_k16_display.py`](source/render_k16_display.py) |

## Read more

- **Full description page**, with sources and evidence: [docs/pieces/993-eng-k16-compressor-wheel-al2139-f1-0001.md](../../docs/pieces/993-eng-k16-compressor-wheel-al2139-f1-0001.md)
- **Catalogue record** (source of truth): [`catalog/parts/993-eng-k16-compressor-wheel-al2139-f1-0001.json`](../../catalog/parts/993-eng-k16-compressor-wheel-al2139-f1-0001.json)
- **Design dossier**: [993_K16_COMPRESSOR_WHEEL_AL2139_F1](../../docs/993/993_K16_COMPRESSOR_WHEEL_AL2139_F1.md)
- **Design dossier**: [993_K16_ROD_IMPROVEMENT_PROGRAMME](../../docs/993/993_K16_ROD_IMPROVEMENT_PROGRAMME.md)
- **Safety rules**: [SAFETY.md](../../SAFETY.md)

---

*This page is generated from the catalogue record by `scripts/render_part_pages.py` and checked by `make check`. Edit the record, not this page.*
