cluster2600/porscheparts/parts/993-eng-k16-compressor-wheel-alsi10mg-f0-0001/README.md

<!-- generated by scripts/render_part_pages.py - do not edit by hand -->

<div align="center">

# 993 K16 compressor wheel, F0 AlSi10Mg LPBF concept

**`993-ENG-K16-COMPRESSOR-WHEEL-ALSI10MG-F0-0001`** · Porsche 993 · 1995–1998

  

</div>

> [!CAUTION]
> **Not ready to print, and not a copy of the original part.** The model shown here is a
> concept block for studying the part in software:
> - validation status `concept`: nothing has been checked against a real part;
> - geometry `mixed`: its dimensions are partly sourced, partly assumed, not measured on the original part;
> - safety class `prohibited_pending_engineering`;
> - no part in this repository is released — read [SAFETY.md](../../SAFETY.md).

<table><tr>
<td width="50%" valign="top">
<b>Original part</b><br><br>
The original part is documented — pictures, catalogue entries or published data — on these pages. They are copyrighted, so they are linked here, not copied:<br><br>
↗ <a href="https://www.invasionautoproducts.com/94pocark16tu.html">Invasion Auto Products - declared internal data of the right-hand 993 Turbo K16</a><br>
↗ <a href="https://porschefanatics.com/engine/993/">PorscheFanatics - context of 993 turbochargers</a><br>
↗ <a href="https://www.turbomaster.info/eng/turbocharger-map.php">TurboMaster - principles for reading a compressor map</a><br>
↗ <a href="https://www.elferclassic.de/technik/techdaten/993-turbo-95-98-techdat.php">elferclassic - 993 Turbo technical data</a><br>
</td>
<td width="50%" valign="top" align="center">
<b>This repository's concept model</b><br><br>
Concept CAD block for 993 K16 compressor wheel, F0 AlSi10Mg LPBF concept<br>
<sub>Concept CAD block, 60.5 × 60.5 × 17.9 mm — <b>not</b> the original part, not a print file, not evidence of fit.</sub>
</td>
</tr></table>

> [!CAUTION]
> **Prohibited pending engineering** — risk, or insufficient data. Never published as a released part.

## What it is

Independent concept of an AlSi10Mg compressor wheel with six main blades and six straight splitters. Only the inducer/exducer diameters, the 6+6 count and the supplier part numbers are published; the hub, the bore and all aerodynamic surfaces remain F0 hypotheses.

## What it does on the car

CAD, DfAM, continuity, compressor thermodynamics, rotating disk, blade tension, expansion, imbalance and energy screening; no manufacturing, rotation, installation or start-up authorized

## At a glance

| | |
|---|---|
| Porsche part numbers | not recorded |
| variants | `993_Turbo`, `K16_right_research`, `M64_60_research` |
| candidate material | EOS AlSi10Mg, screening |
| candidate process | LPBF |
| safety class | `prohibited_pending_engineering` |
| validation status | `concept` |
| geometry | mixed, master build123d |

## Where it stands

```mermaid
flowchart LR
    L0["concept"]
    L1["dimensionally_reviewed"]
    L2["prototype_fitted"]
    L3["functionally_tested"]
    L4["engineering_reviewed"]
    L5["released"]
    L0 --> L1 --> L2 --> L3 --> L4 --> L5
    X["⛔ prohibited pending engineering"]
    L0 -. blocked .-> X
    classDef here fill:#fff4d6,stroke:#b7791f,color:#1a1a1a,stroke-width:3px;
    classDef done fill:#e3f1e6,stroke:#2e7d32,color:#1a1a1a;
    classDef todo fill:#f4f4f4,stroke:#9e9e9e,color:#6b6b6b;
    classDef stop fill:#fde2e1,stroke:#c0392b,color:#1a1a1a;
    class L0 here
    class L1 todo
    class L2 todo
    class L3 todo
    class L4 todo
    class L5 todo
    class X stop
```

*Validation ladder of `catalog/schemas/part.schema.json`; this record is at `concept`.*

## Views

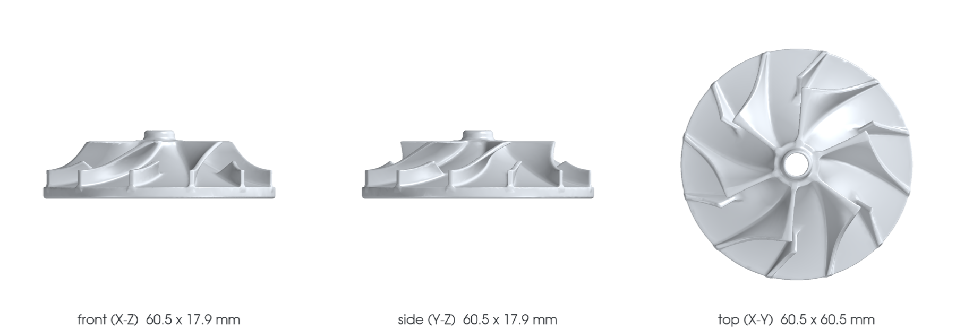
[picture p174: parts/993-eng-k16-compressor-wheel-alsi10mg-f0-0001/media/views.png]
Front, side and top orthographic views


*Orthographic views of the same concept CAD, with its bounding dimensions — not drawings of the original part.*

## Screens and evidence images

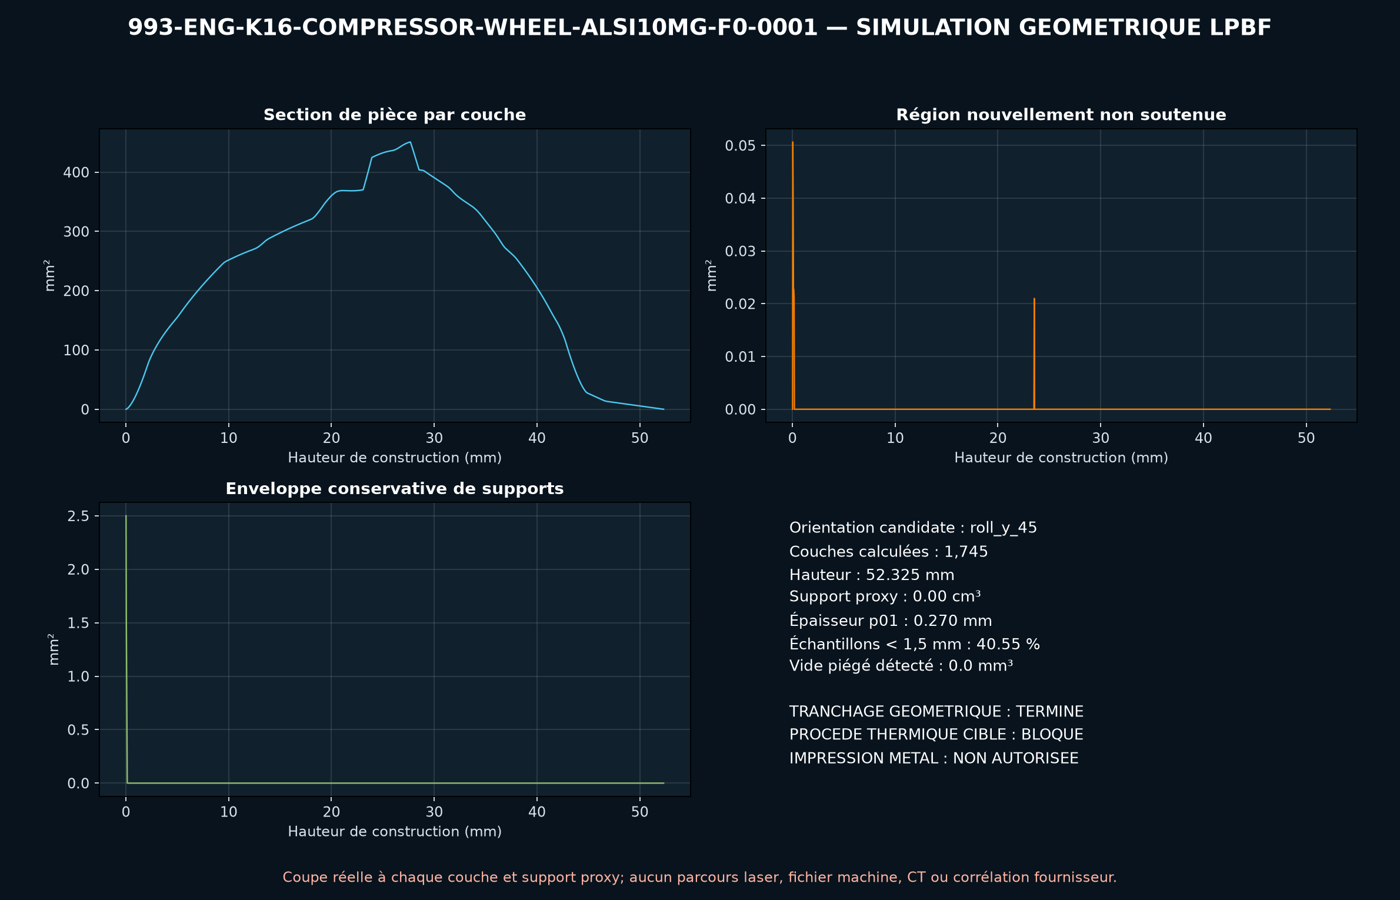
[picture p175: parts/993-eng-k16-compressor-wheel-alsi10mg-f0-0001/evidence/lpbf-f0/993-eng-k16-compressor-wheel-alsi10mg-f0-0001-lpbf-geometry-screen.png]
993-eng-k16-compressor-wheel-alsi10mg-f0-0001-lpbf-geometry-screen


*`evidence/lpbf-f0/993-eng-k16-compressor-wheel-alsi10mg-f0-0001-lpbf-geometry-screen.png` — a screening output, not a validation.*

## What's in this folder

| folder | what it holds | files |
|---|---|---|
| `derived/` | CAD exports generated from the source (STEP for CAD tools, STL for meshing) | [`derived/compressor_wheel_alsi10mg_f0-picogk.json`](derived/compressor_wheel_alsi10mg_f0-picogk.json), [`derived/compressor_wheel_alsi10mg_f0-picogk.stl`](derived/compressor_wheel_alsi10mg_f0-picogk.stl), [`derived/compressor_wheel_alsi10mg_f0.step`](derived/compressor_wheel_alsi10mg_f0.step), [`derived/compressor_wheel_alsi10mg_f0.stl`](derived/compressor_wheel_alsi10mg_f0.stl) |
| `evidence/` | screens, reports and manifests — **pinned by SHA-256, never edited by hand** | [`evidence/engineering-screen.json`](evidence/engineering-screen.json), [`evidence/lpbf-f0/993-eng-k16-compressor-wheel-alsi10mg-f0-0001-layer-metrics.csv`](evidence/lpbf-f0/993-eng-k16-compressor-wheel-alsi10mg-f0-0001-layer-metrics.csv), [`evidence/lpbf-f0/993-eng-k16-compressor-wheel-alsi10mg-f0-0001-lpbf-geometry-manifest.json`](evidence/lpbf-f0/993-eng-k16-compressor-wheel-alsi10mg-f0-0001-lpbf-geometry-manifest.json), [`evidence/lpbf-f0/993-eng-k16-compressor-wheel-alsi10mg-f0-0001-lpbf-geometry-report.json`](evidence/lpbf-f0/993-eng-k16-compressor-wheel-alsi10mg-f0-0001-lpbf-geometry-report.json), [`evidence/lpbf-f0/993-eng-k16-compressor-wheel-alsi10mg-f0-0001-lpbf-geometry-screen.png`](evidence/lpbf-f0/993-eng-k16-compressor-wheel-alsi10mg-f0-0001-lpbf-geometry-screen.png) |
| `media/` | concept-model views rendered from the CAD by `scripts/render_part_previews.py` — not pictures of the original | [`media/preview.json`](media/preview.json), [`media/preview.png`](media/preview.png), [`media/views.png`](media/views.png) |
| `source/` | parametric source — the editable master that generates the geometry | [`source/compressor_wheel.py`](source/compressor_wheel.py), [`source/picogk.json`](source/picogk.json) |

## Read more

- **Full description page**, with sources and evidence: [docs/pieces/993-eng-k16-compressor-wheel-alsi10mg-f0-0001.md](../../docs/pieces/993-eng-k16-compressor-wheel-alsi10mg-f0-0001.md)
- **Catalogue record** (source of truth): [`catalog/parts/993-eng-k16-compressor-wheel-alsi10mg-f0-0001.json`](../../catalog/parts/993-eng-k16-compressor-wheel-alsi10mg-f0-0001.json)
- **Design dossier**: [993_K16_COMPRESSOR_WHEEL_ALSI10MG_F0](../../docs/993/993_K16_COMPRESSOR_WHEEL_ALSI10MG_F0.md)
- **Safety rules**: [SAFETY.md](../../SAFETY.md)

---

*This page is generated from the catalogue record by `scripts/render_part_pages.py` and checked by `make check`. Edit the record, not this page.*
