cluster2600/porscheparts/parts/993-eng-k16-turbine-wheel-in718-f0-0001/README.md

<!-- generated by scripts/render_part_pages.py - do not edit by hand -->

<div align="center">

# K16 turbine wheel, IN718 F0 concept

**`993-ENG-K16-TURBINE-WHEEL-IN718-F0-0001`** · Porsche 993 · 1995–1998

  

</div>

> [!WARNING]
> **A 1:1 display mock-up is printable — never for use.** [`print/`](print/README.md): the design, unchanged except for MOCK-UP / NOT FOR USE engraved in it, sliced in 1h 45m 17s (9.95 cm³). The part itself stays prohibited ([decision 0011](../../docs/decisions/0011-printable-display-mockups-of-prohibited-parts.md)).

> [!CAUTION]
> **Prohibited, not validated, and not a copy of the original.** The mock-up is a display piece; the model shown here is a
> design whose fit has not been checked against the car:
> - validation status `concept`: nothing has been checked against a real part;
> - geometry `mixed`: its dimensions are partly sourced, partly assumed, not measured on the original part;
> - safety class `prohibited_pending_engineering`;
> - no part in this repository is released — read [SAFETY.md](../../SAFETY.md).

<table><tr>
<td width="50%" valign="top">
<b>Original part</b><br><br>
The original part is documented — pictures, catalogue entries or published data — on these pages. They are copyrighted, so they are linked here, not copied:<br><br>
↗ <a href="https://porschefanatics.com/engine/993/">PorscheFanatics - 993 turbocharger context</a><br>
↗ <a href="https://www.turbomaster.com/eng/turbo/borgwarner/5316-988-6735/">TurboMaster - K16 5316-988-6735</a><br>
↗ <a href="https://www.invasionautoproducts.com/94pocark16tu.html">Invasion Auto Products - stated internal data of the right K16</a><br>
↗ <a href="https://www.kinugawaturbo.com/products/kinugawa-turbo-turbine-wheel-for-posche-911-996-kkk-k16-49mm-55-mm-12-blades">Kinugawa - replacement K16 wheel</a><br>
</td>
<td width="50%" valign="top" align="center">
<b>What you can print: a display mock-up</b><br><br>
<a href="print/README.md">Engraved display mock-up of K16 turbine wheel, IN718 F0 concept</a><br>
<sub>1:1 display mock-up with MOCK-UP / NOT FOR USE engraved in it. <b>Never</b> for an engine; not the original part.</sub>
</td>
</tr></table>

> [!CAUTION]
> **Prohibited pending engineering** — risk, or insufficient data. Never published as a released part.

## What it is

Clean-sheet concept of a twelve-blade K16 hot rotor to screen the value and limits of an IN718 LPBF route. The diameters, blade count and part reference come from supplier catalogues; all profiles and interfaces remain hypothetical.

## What it does on the car

F0 screening of CAD, rotation, overspeed, thermal, turbine power, expansion, imbalance and cycles; no manufacturing, rotation, installation or engine start authorized

## At a glance

| | |
|---|---|
| Porsche part numbers | not recorded |
| variants | `993_Turbo` |
| candidate material | EOS NickelAlloy IN718 API, M290 40 µm, heat treated for comparison |
| candidate process | undecided |
| safety class | `prohibited_pending_engineering` |
| validation status | `concept` |
| geometry | mixed, master build123d |

## Where it stands

```mermaid
flowchart LR
    L0["concept"]
    L1["dimensionally_reviewed"]
    L2["prototype_fitted"]
    L3["functionally_tested"]
    L4["engineering_reviewed"]
    L5["released"]
    L0 --> L1 --> L2 --> L3 --> L4 --> L5
    X["⛔ prohibited pending engineering"]
    L0 -. blocked .-> X
    classDef here fill:#fff4d6,stroke:#b7791f,color:#1a1a1a,stroke-width:3px;
    classDef done fill:#e3f1e6,stroke:#2e7d32,color:#1a1a1a;
    classDef todo fill:#f4f4f4,stroke:#9e9e9e,color:#6b6b6b;
    classDef stop fill:#fde2e1,stroke:#c0392b,color:#1a1a1a;
    class L0 here
    class L1 todo
    class L2 todo
    class L3 todo
    class L4 todo
    class L5 todo
    class X stop
```

*Validation ladder of `catalog/schemas/part.schema.json`; this record is at `concept`.*

## Views

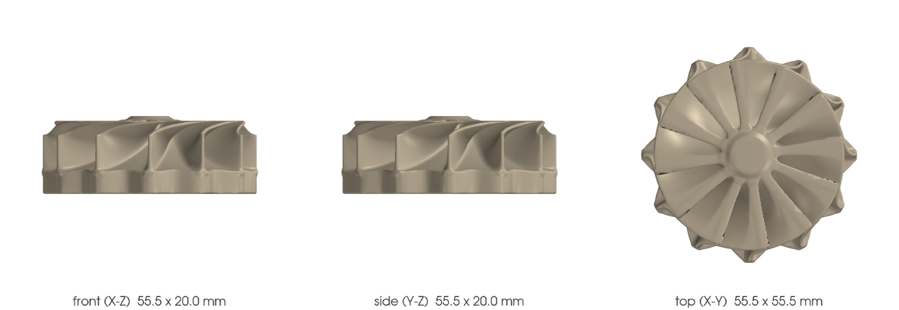
[picture p176: parts/993-eng-k16-turbine-wheel-in718-f0-0001/media/views.png]
Front, side and top orthographic views


*Orthographic views of the same concept CAD, with its bounding dimensions — not drawings of the original part.*

## Screens and evidence images

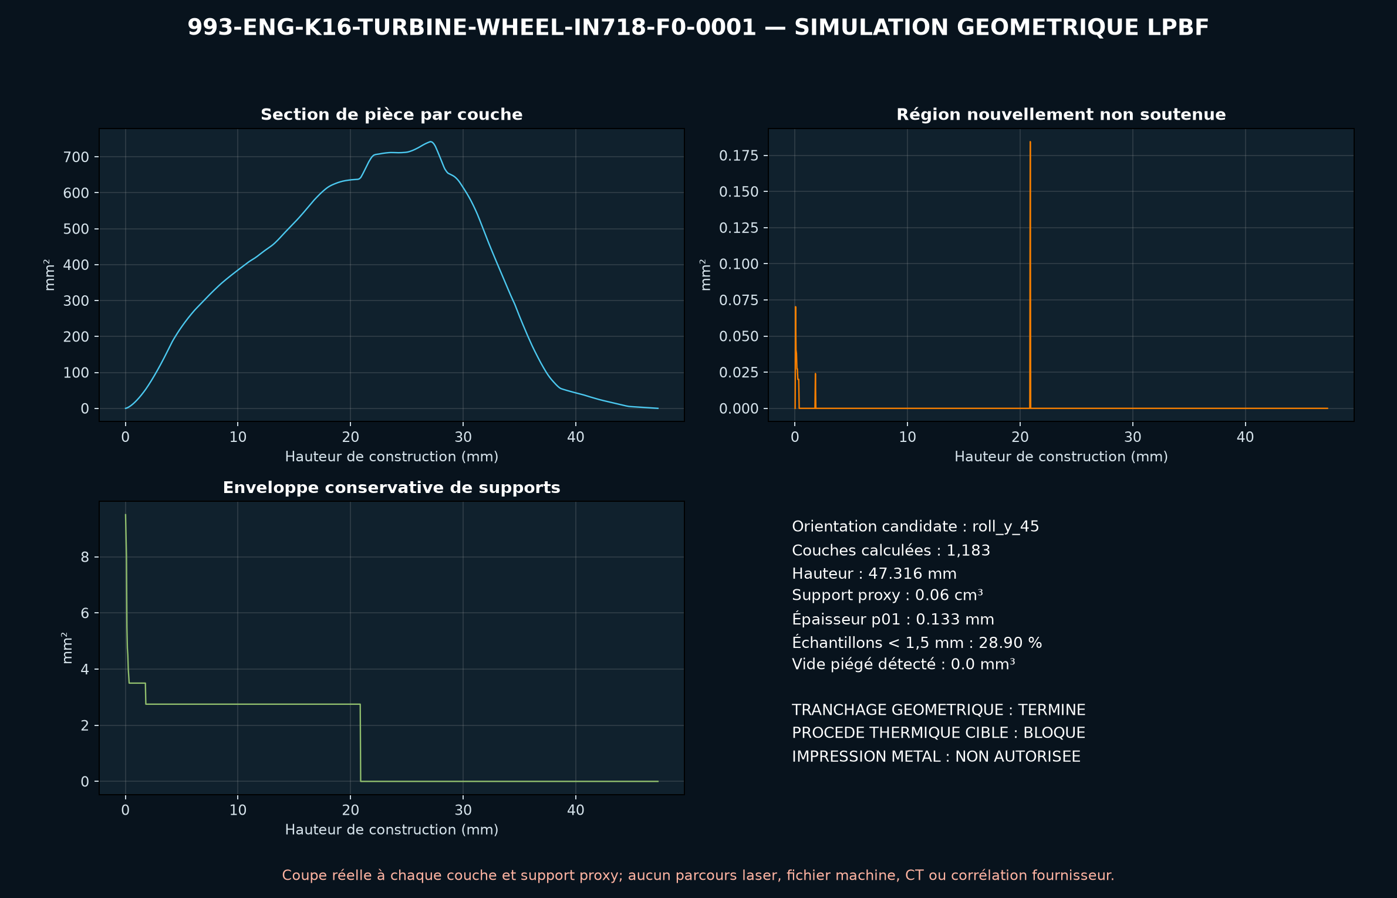
[picture p177: parts/993-eng-k16-turbine-wheel-in718-f0-0001/evidence/lpbf-f0/993-eng-k16-turbine-wheel-in718-f0-0001-lpbf-geometry-screen.png]
993-eng-k16-turbine-wheel-in718-f0-0001-lpbf-geometry-screen


*`evidence/lpbf-f0/993-eng-k16-turbine-wheel-in718-f0-0001-lpbf-geometry-screen.png` — a screening output, not a validation.*

mockup

*`print/mockup.png` — a screening output, not a validation.*

## What's in this folder

| folder | what it holds | files |
|---|---|---|
| `derived/` | CAD exports generated from the source (STEP for CAD tools, STL for meshing) | [`derived/turbine_wheel_in718_f0-picogk.json`](derived/turbine_wheel_in718_f0-picogk.json), [`derived/turbine_wheel_in718_f0-picogk.stl`](derived/turbine_wheel_in718_f0-picogk.stl), [`derived/turbine_wheel_in718_f0.step`](derived/turbine_wheel_in718_f0.step), [`derived/turbine_wheel_in718_f0.stl`](derived/turbine_wheel_in718_f0.stl) |
| `evidence/` | screens, reports and manifests — **pinned by SHA-256, never edited by hand** | [`evidence/engineering-screen.json`](evidence/engineering-screen.json), [`evidence/lpbf-f0/993-eng-k16-turbine-wheel-in718-f0-0001-layer-metrics.csv`](evidence/lpbf-f0/993-eng-k16-turbine-wheel-in718-f0-0001-layer-metrics.csv), [`evidence/lpbf-f0/993-eng-k16-turbine-wheel-in718-f0-0001-lpbf-geometry-manifest.json`](evidence/lpbf-f0/993-eng-k16-turbine-wheel-in718-f0-0001-lpbf-geometry-manifest.json), [`evidence/lpbf-f0/993-eng-k16-turbine-wheel-in718-f0-0001-lpbf-geometry-report.json`](evidence/lpbf-f0/993-eng-k16-turbine-wheel-in718-f0-0001-lpbf-geometry-report.json), [`evidence/lpbf-f0/993-eng-k16-turbine-wheel-in718-f0-0001-lpbf-geometry-screen.png`](evidence/lpbf-f0/993-eng-k16-turbine-wheel-in718-f0-0001-lpbf-geometry-screen.png) |
| `media/` | concept-model views rendered from the CAD by `scripts/render_part_previews.py` — not pictures of the original | [`media/preview.json`](media/preview.json), [`media/preview.png`](media/preview.png), [`media/views.png`](media/views.png) |
| `print/` | **ready-to-print files**: 3MF project, STL and instructions | [`print/k16_turbine_wheel_mockup.stl`](print/k16_turbine_wheel_mockup.stl), [`print/mockup.png`](print/mockup.png), [`print/print.json`](print/print.json) |
| `source/` | parametric source — the editable master that generates the geometry | [`source/picogk.json`](source/picogk.json), [`source/turbine_wheel.py`](source/turbine_wheel.py) |

## Read more

- **Full description page**, with sources and evidence: [docs/pieces/993-eng-k16-turbine-wheel-in718-f0-0001.md](../../docs/pieces/993-eng-k16-turbine-wheel-in718-f0-0001.md)
- **Catalogue record** (source of truth): [`catalog/parts/993-eng-k16-turbine-wheel-in718-f0-0001.json`](../../catalog/parts/993-eng-k16-turbine-wheel-in718-f0-0001.json)
- **Design dossier**: [993_K16_ROD_IMPROVEMENT_PROGRAMME](../../docs/993/993_K16_ROD_IMPROVEMENT_PROGRAMME.md)
- **Design dossier**: [993_K16_TURBINE_WHEEL_IN718_F0](../../docs/993/993_K16_TURBINE_WHEEL_IN718_F0.md)
- **Safety rules**: [SAFETY.md](../../SAFETY.md)

---

*This page is generated from the catalogue record by `scripts/render_part_pages.py` and checked by `make check`. Edit the record, not this page.*
