cluster2600/porscheparts/parts/993-eng-piston-cp1-gallery-f0-0001/README.md

<!-- generated by scripts/render_part_pages.py - do not edit by hand -->

<div align="center">

# M64/60 piston with cooling gallery, CP1 F0 concept

**`993-ENG-PISTON-CP1-GALLERY-F0-0001`** · Porsche 993 · 1995–1998

  

</div>

> [!CAUTION]
> **Not ready to print, and not a copy of the original part.** The model shown here is a
> concept block for studying the part in software:
> - validation status `concept`: nothing has been checked against a real part;
> - geometry `mixed`: its dimensions are partly sourced, partly assumed, not measured on the original part;
> - safety class `prohibited_pending_engineering`;
> - no part in this repository is released — read [SAFETY.md](../../SAFETY.md).

<table><tr>
<td width="50%" valign="top">
<b>Original part</b><br><br>
The original part is documented — pictures, catalogue entries or published data — on these pages. They are copyrighted, so they are linked here, not copied:<br><br>
↗ <a href="https://porschefanatics.com/parts/c/engine-internals/">PorscheFanatics - additive piston precedent and 993 pistons</a><br>
↗ <a href="https://newsroom.porsche.com/en/2020/technology/porsche-cooperation-mahle-trumpf-pistons-3d-printer-power-efficiency-911-gt2-rs-21462.html">Porsche Newsroom - laser-fused pistons</a><br>
↗ <a href="https://www.elferclassic.de/technik/techdaten/993-turbo-95-98-techdat.php">elferclassic - German technical data of the 993 Turbo</a><br>
↗ <a href="https://events.esd.org/wp-content/uploads/2018/07/3D-Printed-Piston-for-Heavy-Duty-Diesel-Engines.pdf">IAV / GVSETS 2018 - additive diesel piston</a><br>
</td>
<td width="50%" valign="top" align="center">
<b>This repository's concept model</b><br><br>
Concept CAD block for M64/60 piston with cooling gallery, CP1 F0 concept<br>
<sub>Concept CAD block, 99.1 × 99.1 × 70.1 mm — <b>not</b> the original part, not a print file, not evidence of fit.</sub>
</td>
</tr></table>

> [!CAUTION]
> **Prohibited pending engineering** — risk, or insufficient data. Never published as a released part.

## What it is

Independent concept of an Aheadd CP1 LPBF piston with a toroidal gallery under the crown and two temporary depowdering ports. Only the M64/60 bore/stroke/engine speed and the Porsche methodological precedent are published; the entire piston geometry remains an F0 hypothesis.

## What it does on the car

CAD, DfAM, plate mechanics, inertia, pin pressure, conduction and gallery hydraulics screening; no manufacturing, installation or engine start authorized

## At a glance

| | |
|---|---|
| Porsche part numbers | not recorded |
| variants | `993_Turbo`, `M64_60_research` |
| candidate material | Constellium Aheadd CP1, Velo3D Sapphire 50 µm route for screening only |
| candidate process | LPBF |
| safety class | `prohibited_pending_engineering` |
| validation status | `concept` |
| geometry | mixed, master build123d |

## Where it stands

```mermaid
flowchart LR
    L0["concept"]
    L1["dimensionally_reviewed"]
    L2["prototype_fitted"]
    L3["functionally_tested"]
    L4["engineering_reviewed"]
    L5["released"]
    L0 --> L1 --> L2 --> L3 --> L4 --> L5
    X["⛔ prohibited pending engineering"]
    L0 -. blocked .-> X
    classDef here fill:#fff4d6,stroke:#b7791f,color:#1a1a1a,stroke-width:3px;
    classDef done fill:#e3f1e6,stroke:#2e7d32,color:#1a1a1a;
    classDef todo fill:#f4f4f4,stroke:#9e9e9e,color:#6b6b6b;
    classDef stop fill:#fde2e1,stroke:#c0392b,color:#1a1a1a;
    class L0 here
    class L1 todo
    class L2 todo
    class L3 todo
    class L4 todo
    class L5 todo
    class X stop
```

*Validation ladder of `catalog/schemas/part.schema.json`; this record is at `concept`.*

## Views

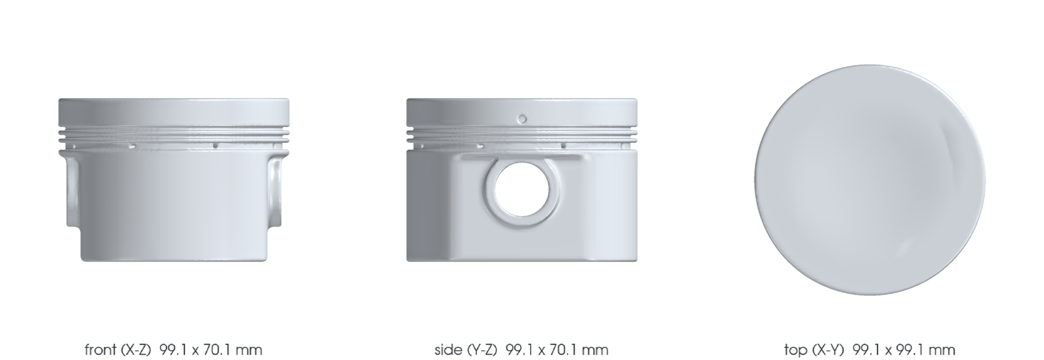
[picture p180: parts/993-eng-piston-cp1-gallery-f0-0001/media/views.png]
Front, side and top orthographic views


*Orthographic views of the same concept CAD, with its bounding dimensions — not drawings of the original part.*

## What's in this folder

| folder | what it holds | files |
|---|---|---|
| `derived/` | CAD exports generated from the source (STEP for CAD tools, STL for meshing) | [`derived/piston_cp1_gallery_f0-picogk.json`](derived/piston_cp1_gallery_f0-picogk.json), [`derived/piston_cp1_gallery_f0-picogk.stl`](derived/piston_cp1_gallery_f0-picogk.stl), [`derived/piston_cp1_gallery_f0.step`](derived/piston_cp1_gallery_f0.step) |
| `evidence/` | screens, reports and manifests — **pinned by SHA-256, never edited by hand** | [`evidence/engineering-screen.json`](evidence/engineering-screen.json) |
| `media/` | concept-model views rendered from the CAD by `scripts/render_part_previews.py` — not pictures of the original | [`media/preview.json`](media/preview.json), [`media/preview.png`](media/preview.png), [`media/views.png`](media/views.png) |
| `source/` | parametric source — the editable master that generates the geometry | [`source/picogk.json`](source/picogk.json), [`source/piston.py`](source/piston.py) |

## Read more

- **Full description page**, with sources and evidence: [docs/pieces/993-eng-piston-cp1-gallery-f0-0001.md](../../docs/pieces/993-eng-piston-cp1-gallery-f0-0001.md)
- **Catalogue record** (source of truth): [`catalog/parts/993-eng-piston-cp1-gallery-f0-0001.json`](../../catalog/parts/993-eng-piston-cp1-gallery-f0-0001.json)
- **Design dossier**: [993_PISTON_CP1_COOLING_GALLERY_F0](../../docs/993/993_PISTON_CP1_COOLING_GALLERY_F0.md)
- **Digital twin record**: [`twin-993-m64-60-piston-gallery-f0.json`](../../catalog/twins/twin-993-m64-60-piston-gallery-f0.json) — see [twins/README.md](../../twins/README.md)
- **Safety rules**: [SAFETY.md](../../SAFETY.md)

---

*This page is generated from the catalogue record by `scripts/render_part_pages.py` and checked by `make check`. Edit the record, not this page.*
