cluster2600/porscheparts/parts/993-eng-turbo-heat-shield-in625-f0-0001/README.md

<!-- generated by scripts/render_part_pages.py - do not edit by hand -->

<div align="center">

# 993 left turbo heat shield cover, F0 IN625 concept

**`993-ENG-TURBO-HEAT-SHIELD-IN625-F0-0001`** · Porsche 993 · 1995–1998

  

</div>

> [!CAUTION]
> **Not ready to print, and not a copy of the original part.** The model shown here is a
> concept block for studying the part in software:
> - validation status `concept`: nothing has been checked against a real part;
> - geometry `mixed`: its dimensions are partly sourced, partly assumed, not measured on the original part;
> - safety class `functional`;
> - no part in this repository is released — read [SAFETY.md](../../SAFETY.md).

<table><tr>
<td width="50%" valign="top">
<b>Original part</b><br><br>
The original part is documented — pictures, catalogue entries or published data — on these pages. They are copyrighted, so they are linked here, not copied:<br><br>
↗ <a href="https://porschefanatics.com/oem/993/202-16/">PorscheFanatics - PET transcription of the 993 Turbo groups</a><br>
↗ <a href="https://www.fvd.net/en-ch/shop/cover-heat-protection-turbo-loader-left-99312311351~p248974">FVD - left heat shield cover 99312311351</a><br>
↗ <a href="https://www.specialmetals.com/documents/technical-bulletins/inconel/inconel-alloy-625.pdf">Special Metals - INCONEL alloy 625</a><br>
</td>
<td width="50%" valign="top" align="center">
<b>This repository's concept model</b><br><br>
Concept CAD block for 993 left turbo heat shield cover, F0 IN625 concept<br>
<sub>Concept CAD block, 160.0 × 110.1 × 105.0 mm — <b>not</b> the original part, not a print file, not evidence of fit.</sub>
</td>
</tr></table>

> [!NOTE]
> **Functional** — loaded part whose failure can immobilize or damage the vehicle. Published only after documented functional testing.

## What it is

Independent concept of an open shell with integrated bosses for screening an LPBF remanufacture in IN625. PorscheFanatics confirms the PET identity; FVD publishes only the envelope and mass of the left-hand cover 993 123 113 51.

## What it does on the car

CAD, thermal, mechanical and DfAM screening; no manufacturing for fitment and no vehicle installation authorized

## At a glance

| | |
|---|---|
| Porsche part numbers | 99312311351 |
| variants | `993_Turbo`, `993_GT2` |
| candidate material | EOS NickelAlloy IN625 / UNS N06625, screening |
| candidate process | undecided |
| safety class | `functional` |
| validation status | `concept` |
| geometry | mixed, master build123d |

## Where it stands

```mermaid
flowchart LR
    L0["concept"]
    L1["dimensionally_reviewed"]
    L2["prototype_fitted"]
    L3["functionally_tested"]
    L4["engineering_reviewed"]
    L5["released"]
    L0 --> L1 --> L2 --> L3 --> L4 --> L5
    classDef here fill:#fff4d6,stroke:#b7791f,color:#1a1a1a,stroke-width:3px;
    classDef done fill:#e3f1e6,stroke:#2e7d32,color:#1a1a1a;
    classDef todo fill:#f4f4f4,stroke:#9e9e9e,color:#6b6b6b;
    classDef stop fill:#fde2e1,stroke:#c0392b,color:#1a1a1a;
    class L0 here
    class L1 todo
    class L2 todo
    class L3 todo
    class L4 todo
    class L5 todo
```

*Validation ladder of `catalog/schemas/part.schema.json`; this record is at `concept`.*

## Views

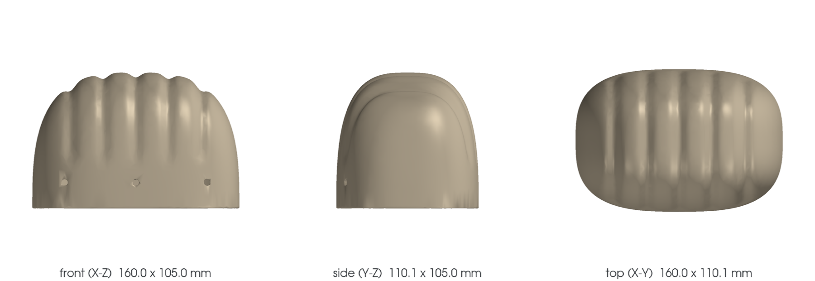
[picture p183: parts/993-eng-turbo-heat-shield-in625-f0-0001/media/views.png]
Front, side and top orthographic views


*Orthographic views of the same concept CAD, with its bounding dimensions — not drawings of the original part.*

## PicoGK voxel model

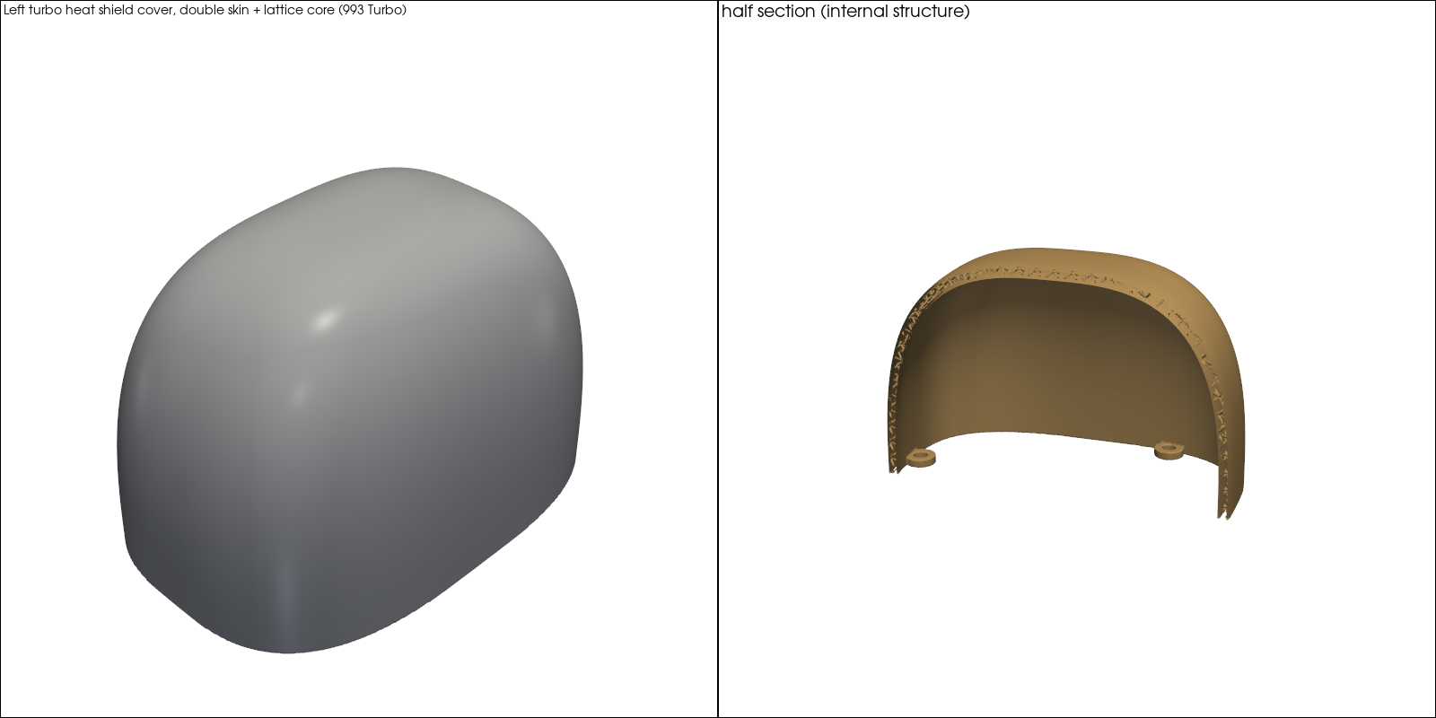
[picture p184: parts/993-eng-turbo-heat-shield-in625-f0-0001/media/picogk-batch-01.png]
PicoGK model: shaded view and half section


*Variant generated with the PicoGK voxel kernel in [`parts/picogk-993-batch-01`](../../parts/picogk-993-batch-01/README.md): published overall envelope, internal structure (double wall, lattice core or vanes) shown in the half section. Mounting interfaces are assumptions — not the original part, not a print file, not evidence of fit.*

## Screens and evidence images

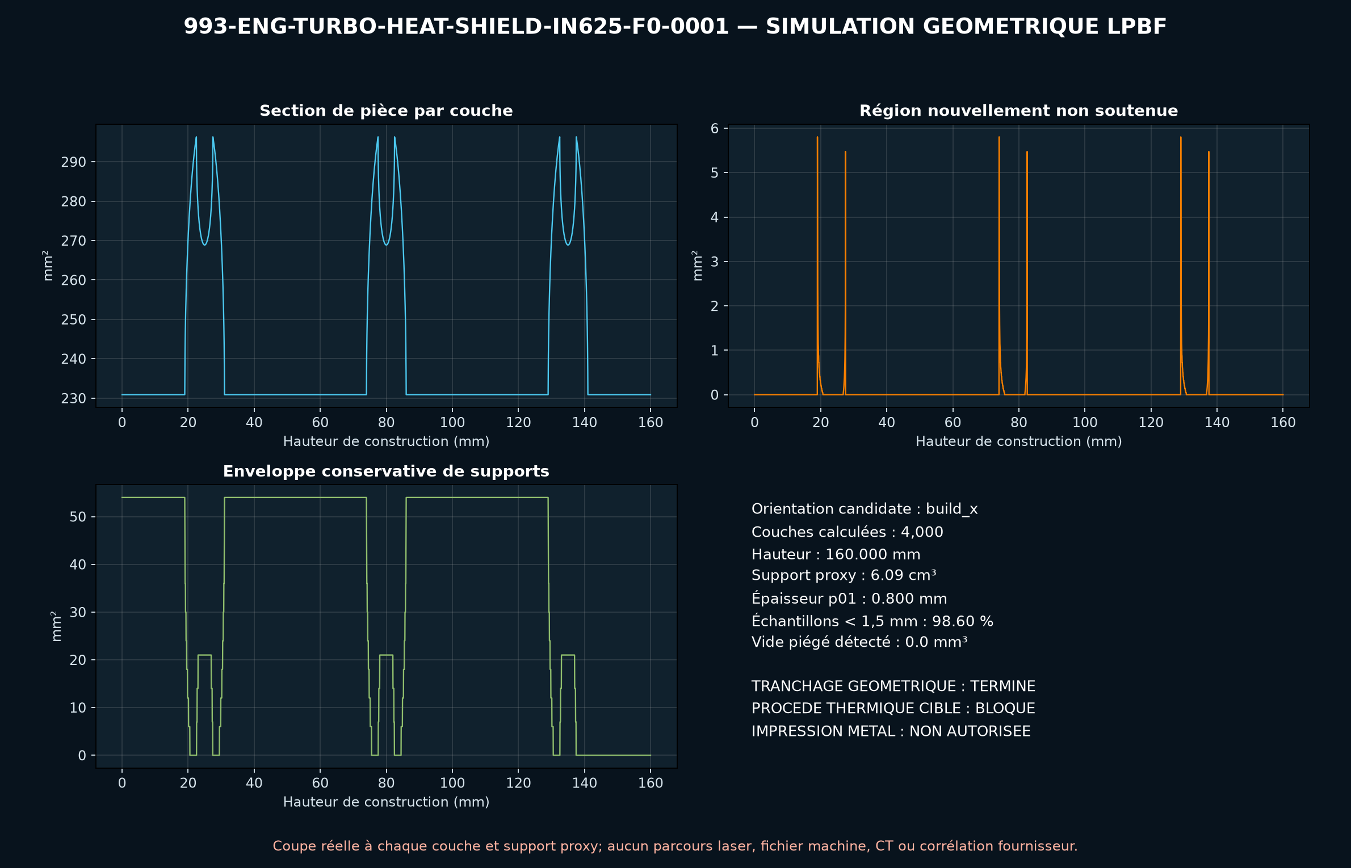
[picture p185: parts/993-eng-turbo-heat-shield-in625-f0-0001/evidence/lpbf-f0/993-eng-turbo-heat-shield-in625-f0-0001-lpbf-geometry-screen.png]
993-eng-turbo-heat-shield-in625-f0-0001-lpbf-geometry-screen


*`evidence/lpbf-f0/993-eng-turbo-heat-shield-in625-f0-0001-lpbf-geometry-screen.png` — a screening output, not a validation.*

## What's in this folder

| folder | what it holds | files |
|---|---|---|
| `derived/` | CAD exports generated from the source (STEP for CAD tools, STL for meshing) | [`derived/turbo_heat_shield_in625_f0-picogk.json`](derived/turbo_heat_shield_in625_f0-picogk.json), [`derived/turbo_heat_shield_in625_f0-picogk.stl`](derived/turbo_heat_shield_in625_f0-picogk.stl), [`derived/turbo_heat_shield_in625_f0.step`](derived/turbo_heat_shield_in625_f0.step), [`derived/turbo_heat_shield_in625_f0.stl`](derived/turbo_heat_shield_in625_f0.stl) |
| `evidence/` | screens, reports and manifests — **pinned by SHA-256, never edited by hand** | [`evidence/engineering-screen.json`](evidence/engineering-screen.json), [`evidence/lpbf-f0/993-eng-turbo-heat-shield-in625-f0-0001-layer-metrics.csv`](evidence/lpbf-f0/993-eng-turbo-heat-shield-in625-f0-0001-layer-metrics.csv), [`evidence/lpbf-f0/993-eng-turbo-heat-shield-in625-f0-0001-lpbf-geometry-manifest.json`](evidence/lpbf-f0/993-eng-turbo-heat-shield-in625-f0-0001-lpbf-geometry-manifest.json), [`evidence/lpbf-f0/993-eng-turbo-heat-shield-in625-f0-0001-lpbf-geometry-report.json`](evidence/lpbf-f0/993-eng-turbo-heat-shield-in625-f0-0001-lpbf-geometry-report.json), [`evidence/lpbf-f0/993-eng-turbo-heat-shield-in625-f0-0001-lpbf-geometry-screen.png`](evidence/lpbf-f0/993-eng-turbo-heat-shield-in625-f0-0001-lpbf-geometry-screen.png) |
| `media/` | concept-model views rendered from the CAD by `scripts/render_part_previews.py` — not pictures of the original | [`media/picogk-batch-01.png`](media/picogk-batch-01.png), [`media/preview.json`](media/preview.json), [`media/preview.png`](media/preview.png), [`media/views.png`](media/views.png) |
| `source/` | parametric source — the editable master that generates the geometry | [`source/picogk.json`](source/picogk.json), [`source/turbo_heat_shield.py`](source/turbo_heat_shield.py) |

## Read more

- **Full description page**, with sources and evidence: [docs/pieces/993-eng-turbo-heat-shield-in625-f0-0001.md](../../docs/pieces/993-eng-turbo-heat-shield-in625-f0-0001.md)
- **Catalogue record** (source of truth): [`catalog/parts/993-eng-turbo-heat-shield-in625-f0-0001.json`](../../catalog/parts/993-eng-turbo-heat-shield-in625-f0-0001.json)
- **Design dossier**: [993_TURBO_HEAT_SHIELD_IN625_F0](../../docs/993/993_TURBO_HEAT_SHIELD_IN625_F0.md)
- **Safety rules**: [SAFETY.md](../../SAFETY.md)

---

*This page is generated from the catalogue record by `scripts/render_part_pages.py` and checked by `make check`. Edit the record, not this page.*
