cluster2600/porscheparts/parts/993-eng-upper-valve-cover-alsi10mg-f0-0001/README.md

<!-- generated by scripts/render_part_pages.py - do not edit by hand -->

<div align="center">

# Upper valve cover with COP towers, F0 AlSi10Mg concept

**`993-ENG-UPPER-VALVE-COVER-ALSI10MG-F0-0001`** · Porsche 993 · 1994–1998

  

</div>

> [!CAUTION]
> **Not ready to print, and not a copy of the original part.** The model shown here is a
> concept block for studying the part in software:
> - validation status `concept`: nothing has been checked against a real part;
> - geometry `estimated`: its dimensions are estimated design variables, not measured on the original part;
> - safety class `prohibited_pending_engineering`;
> - no part in this repository is released — read [SAFETY.md](../../SAFETY.md).

<table><tr>
<td width="50%" valign="top">
<b>Original part</b><br><br>
The original part is documented — pictures, catalogue entries or published data — on these pages. They are copyrighted, so they are linked here, not copied:<br><br>
↗ <a href="https://porschefanatics.com/engine/993/">PorscheFanatics - 993 valve covers and coil-on-plug integration</a><br>
↗ <a href="https://www.fvd.net/en-us/shop/complete-upper-and-lower-valve-cover-set-993-carrera-rs-billet-aluminum-made-in-germany-fvd105993cset~p312212">FVD - complete set of 993 billet valve covers</a><br>
↗ <a href="https://www.protomotive.com/wp422/product/993-turbo-and-carrera-upper-valve-covers/">Protomotive - 993 upper valve covers in 6061-T6</a><br>
↗ <a href="https://porschefanatics.com/993/torques/">PorscheFanatics - 993 tightening torques</a><br>
</td>
<td width="50%" valign="top" align="center">
<b>This repository's concept model</b><br><br>
Concept CAD block for Upper valve cover with COP towers, F0 AlSi10Mg concept<br>
<sub>Concept CAD block, 220.1 × 95.8 × 46.0 mm — <b>not</b> the original part, not a print file, not evidence of fit.</sub>
</td>
</tr></table>

> [!CAUTION]
> **Prohibited pending engineering** — risk, or insufficient data. Never published as a released part.

## What it is

Independent concept of a 993 upper valve cover, open on the oil side, with six fins and three integrated coil-on-plug towers. The sources confirm billet alternatives and interest in COP, but no individual geometry; all F0 interfaces are synthetic.

## What it does on the car

F0 screening of open CAD, COP consolidation, crankcase pressure, clamping, flatness, thermal, convection and mass; no manufacturing, sealing, installation or start-up authorized

## At a glance

| | |
|---|---|
| Porsche part numbers | not recorded |
| variants | `993_Carrera`, `993_Turbo` |
| candidate material | EOS Aluminium AlSi10Mg T6, for comparison |
| candidate process | undecided |
| safety class | `prohibited_pending_engineering` |
| validation status | `concept` |
| geometry | estimated, master build123d |

## Where it stands

```mermaid
flowchart LR
    L0["concept"]
    L1["dimensionally_reviewed"]
    L2["prototype_fitted"]
    L3["functionally_tested"]
    L4["engineering_reviewed"]
    L5["released"]
    L0 --> L1 --> L2 --> L3 --> L4 --> L5
    X["⛔ prohibited pending engineering"]
    L0 -. blocked .-> X
    classDef here fill:#fff4d6,stroke:#b7791f,color:#1a1a1a,stroke-width:3px;
    classDef done fill:#e3f1e6,stroke:#2e7d32,color:#1a1a1a;
    classDef todo fill:#f4f4f4,stroke:#9e9e9e,color:#6b6b6b;
    classDef stop fill:#fde2e1,stroke:#c0392b,color:#1a1a1a;
    class L0 here
    class L1 todo
    class L2 todo
    class L3 todo
    class L4 todo
    class L5 todo
    class X stop
```

*Validation ladder of `catalog/schemas/part.schema.json`; this record is at `concept`.*

## Views

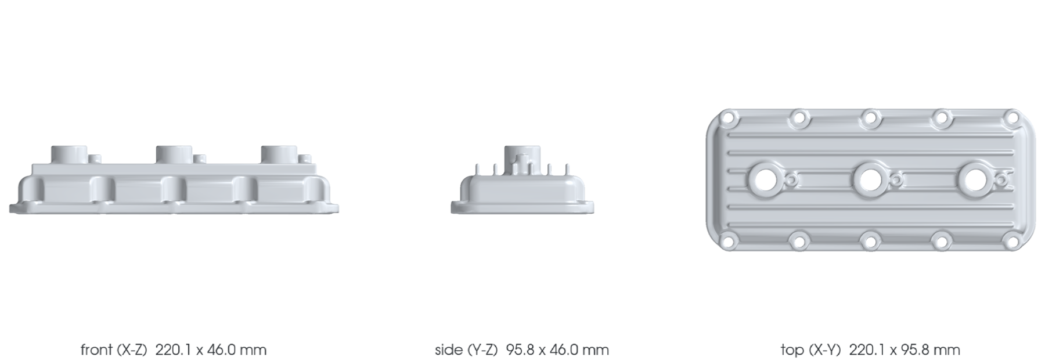
[picture p188: parts/993-eng-upper-valve-cover-alsi10mg-f0-0001/media/views.png]
Front, side and top orthographic views


*Orthographic views of the same concept CAD, with its bounding dimensions — not drawings of the original part.*

## Screens and evidence images

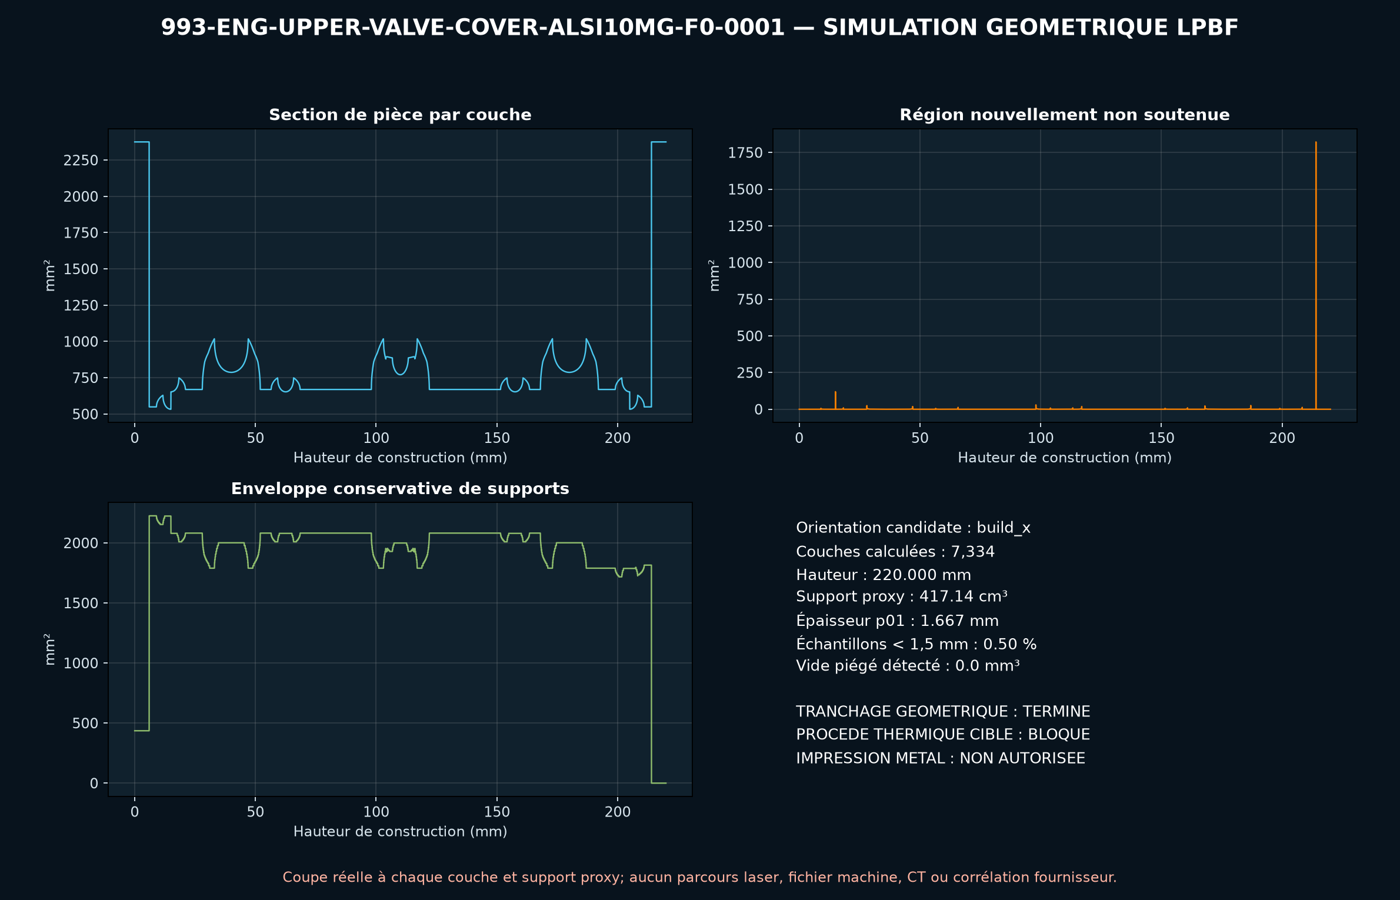
[picture p189: parts/993-eng-upper-valve-cover-alsi10mg-f0-0001/evidence/lpbf-f0/993-eng-upper-valve-cover-alsi10mg-f0-0001-lpbf-geometry-screen.png]
993-eng-upper-valve-cover-alsi10mg-f0-0001-lpbf-geometry-screen


*`evidence/lpbf-f0/993-eng-upper-valve-cover-alsi10mg-f0-0001-lpbf-geometry-screen.png` — a screening output, not a validation.*

## What's in this folder

| folder | what it holds | files |
|---|---|---|
| `derived/` | CAD exports generated from the source (STEP for CAD tools, STL for meshing) | [`derived/upper_valve_cover_alsi10mg_f0-picogk.json`](derived/upper_valve_cover_alsi10mg_f0-picogk.json), [`derived/upper_valve_cover_alsi10mg_f0-picogk.stl`](derived/upper_valve_cover_alsi10mg_f0-picogk.stl), [`derived/upper_valve_cover_alsi10mg_f0.step`](derived/upper_valve_cover_alsi10mg_f0.step), [`derived/upper_valve_cover_alsi10mg_f0.stl`](derived/upper_valve_cover_alsi10mg_f0.stl) |
| `evidence/` | screens, reports and manifests — **pinned by SHA-256, never edited by hand** | [`evidence/engineering-screen.json`](evidence/engineering-screen.json), [`evidence/lpbf-f0/993-eng-upper-valve-cover-alsi10mg-f0-0001-layer-metrics.csv`](evidence/lpbf-f0/993-eng-upper-valve-cover-alsi10mg-f0-0001-layer-metrics.csv), [`evidence/lpbf-f0/993-eng-upper-valve-cover-alsi10mg-f0-0001-lpbf-geometry-manifest.json`](evidence/lpbf-f0/993-eng-upper-valve-cover-alsi10mg-f0-0001-lpbf-geometry-manifest.json), [`evidence/lpbf-f0/993-eng-upper-valve-cover-alsi10mg-f0-0001-lpbf-geometry-report.json`](evidence/lpbf-f0/993-eng-upper-valve-cover-alsi10mg-f0-0001-lpbf-geometry-report.json), [`evidence/lpbf-f0/993-eng-upper-valve-cover-alsi10mg-f0-0001-lpbf-geometry-screen.png`](evidence/lpbf-f0/993-eng-upper-valve-cover-alsi10mg-f0-0001-lpbf-geometry-screen.png) |
| `media/` | concept-model views rendered from the CAD by `scripts/render_part_previews.py` — not pictures of the original | [`media/preview.json`](media/preview.json), [`media/preview.png`](media/preview.png), [`media/views.png`](media/views.png) |
| `source/` | parametric source — the editable master that generates the geometry | [`source/picogk.json`](source/picogk.json), [`source/upper_valve_cover.py`](source/upper_valve_cover.py) |

## Read more

- **Full description page**, with sources and evidence: [docs/pieces/993-eng-upper-valve-cover-alsi10mg-f0-0001.md](../../docs/pieces/993-eng-upper-valve-cover-alsi10mg-f0-0001.md)
- **Catalogue record** (source of truth): [`catalog/parts/993-eng-upper-valve-cover-alsi10mg-f0-0001.json`](../../catalog/parts/993-eng-upper-valve-cover-alsi10mg-f0-0001.json)
- **Design dossier**: [993_UPPER_VALVE_COVER_ALSI10MG_F0](../../docs/993/993_UPPER_VALVE_COVER_ALSI10MG_F0.md)
- **Safety rules**: [SAFETY.md](../../SAFETY.md)

---

*This page is generated from the catalogue record by `scripts/render_part_pages.py` and checked by `make check`. Edit the record, not this page.*
