cluster2600/porscheparts/parts/993-int-dashboard-trim-0001/README.md

<!-- generated by scripts/render_part_pages.py - do not edit by hand -->

<div align="center">

# Dashboard trim, composite

**`993-INT-DASHBOARD-TRIM-0001`** · Porsche 993 · 1994–1998

  

</div>

> [!CAUTION]
> **Not ready to print, and not a copy of the original part.** The model shown here is a
> concept block for studying the part in software:
> - validation status `concept`: nothing has been checked against a real part;
> - geometry `estimated`: its dimensions are estimated design variables, not measured on the original part;
> - safety class `functional`;
> - no part in this repository is released — read [SAFETY.md](../../SAFETY.md).

<table><tr>
<td width="50%" valign="top">
<b>Original part</b><br><br>
The original part is documented — pictures, catalogue entries or published data — on these pages. They are copyrighted, so they are linked here, not copied:<br><br>
↗ <a href="https://rsworkshop.ch/downloaded/pet-porsche/993_1994-98_KATALOG.pdf">Porsche PET - 911 1994-1998 Type 993, parts catalogue revision Kat 017</a><br>
↗ <a href="http://www.federleichte-elfer.de/dp93/innen.html">Federleichte Elfer - mass table, 993 interior</a><br>
</td>
<td width="50%" valign="top" align="center">
<b>This repository's concept model</b><br><br>
Concept CAD block for Dashboard trim, composite<br>
<sub>Concept CAD block, 1346.7 × 115.7 × 60.2 mm — <b>not</b> the original part, not a print file, not evidence of fit.</sub>
</td>
</tr></table>

> [!NOTE]
> **Functional** — loaded part whose failure can immobilize or damage the vehicle. Published only after documented functional testing.

## What it is

993 dashboard trim reproduced in composite, **for vehicles without a passenger airbag only**. The part is not the dashboard itself: that one, 993 502 027 02, is a body shell panel. This is the trim that covers it, fitted on clip nuts and self-tapping screws. Selected because no manufacturer offers it in carbon, unlike body panels.

## What it does on the car

Visible trim of the dashboard cross member on a vehicle without a passenger airbag, carrying the air vents and the instrument hood, and receiving the knee protection strip, which stays original

## At a glance

| | |
|---|---|
| Porsche part numbers | 993 552 055 00, 993 552 056 00, 993 552 055 70, 993 552 056 70 |
| variants | M564 without airbag, Carrera RS M002, Carrera RS Clubsport M003 |
| candidate material | fiber and resin to be determined |
| candidate process | undecided |
| safety class | `functional` |
| validation status | `concept` |
| geometry | estimated, master build123d |

## Where it stands

```mermaid
flowchart LR
    L0["concept"]
    L1["dimensionally_reviewed"]
    L2["prototype_fitted"]
    L3["functionally_tested"]
    L4["engineering_reviewed"]
    L5["released"]
    L0 --> L1 --> L2 --> L3 --> L4 --> L5
    classDef here fill:#fff4d6,stroke:#b7791f,color:#1a1a1a,stroke-width:3px;
    classDef done fill:#e3f1e6,stroke:#2e7d32,color:#1a1a1a;
    classDef todo fill:#f4f4f4,stroke:#9e9e9e,color:#6b6b6b;
    classDef stop fill:#fde2e1,stroke:#c0392b,color:#1a1a1a;
    class L0 here
    class L1 todo
    class L2 todo
    class L3 todo
    class L4 todo
    class L5 todo
```

*Validation ladder of `catalog/schemas/part.schema.json`; this record is at `concept`.*

## Views

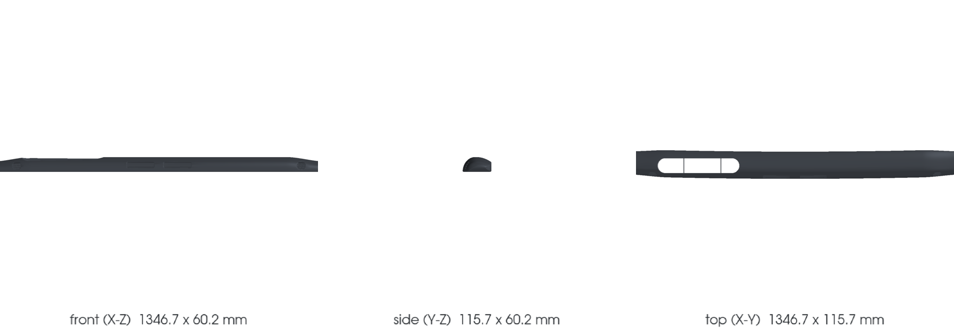
[picture p194: parts/993-int-dashboard-trim-0001/media/views.png]
Front, side and top orthographic views


*Orthographic views of the same concept CAD, with its bounding dimensions — not drawings of the original part.*

## What's in this folder

| folder | what it holds | files |
|---|---|---|
| `derived/` | CAD exports generated from the source (STEP for CAD tools, STL for meshing) | [`derived/dashboard_trim_concept_f0-picogk.json`](derived/dashboard_trim_concept_f0-picogk.json), [`derived/dashboard_trim_concept_f0-picogk.stl`](derived/dashboard_trim_concept_f0-picogk.stl), [`derived/dashboard_trim_concept_f0.step`](derived/dashboard_trim_concept_f0.step) |
| `evidence/` | screens, reports and manifests — **pinned by SHA-256, never edited by hand** | [`evidence/concept-f0.json`](evidence/concept-f0.json), [`evidence/measurement-plan.md`](evidence/measurement-plan.md) |
| `media/` | concept-model views rendered from the CAD by `scripts/render_part_previews.py` — not pictures of the original | [`media/preview.json`](media/preview.json), [`media/preview.png`](media/preview.png), [`media/views.png`](media/views.png) |
| `source/` | parametric source — the editable master that generates the geometry | [`source/picogk.json`](source/picogk.json) |

## Read more

- **Full description page**, with sources and evidence: [docs/pieces/993-int-dashboard-trim-0001.md](../../docs/pieces/993-int-dashboard-trim-0001.md)
- **Catalogue record** (source of truth): [`catalog/parts/993-int-dashboard-trim-0001.json`](../../catalog/parts/993-int-dashboard-trim-0001.json)
- **Safety rules**: [SAFETY.md](../../SAFETY.md)

---

*This page is generated from the catalogue record by `scripts/render_part_pages.py` and checked by `make check`. Edit the record, not this page.*
