cluster2600/porscheparts/parts/993-int-door-opener-lever-f0-0001/README.md

<!-- generated by scripts/render_part_pages.py - do not edit by hand -->

<div align="center">

# 993 interior door opener lever, F0 aluminum concept

**`993-INT-DOOR-OPENER-LEVER-F0-0001`** · Porsche 993 · 1994–1998

  

</div>

> [!CAUTION]
> **Not ready to print, and not a copy of the original part.** The model shown here is a
> concept block for studying the part in software:
> - validation status `concept`: nothing has been checked against a real part;
> - geometry `mixed`: its dimensions are partly sourced, partly assumed, not measured on the original part;
> - safety class `functional`;
> - no part in this repository is released — read [SAFETY.md](../../SAFETY.md).

<table><tr>
<td width="50%" valign="top">
<b>Original part</b><br><br>
The original part is documented — pictures, catalogue entries or published data — on these pages. They are copyrighted, so they are linked here, not copied:<br><br>
↗ <a href="https://porschefanatics.com/oem/">PorscheFanatics - PET part numbers of the 993 interior door openers</a><br>
↗ <a href="https://www.fvd.net/de/shop/tueroeffnersatz-2-stk-aluminium-schwarz-993-fvd55599301b~p310555">FVD - aluminum door opener set FVD55599301B</a><br>
</td>
<td width="50%" valign="top" align="center">
<b>This repository's concept model</b><br><br>
Concept CAD block for 993 interior door opener lever, F0 aluminum concept<br>
<sub>Concept CAD block, 108.0 × 44.5 × 27.1 mm — <b>not</b> the original part, not a print file, not evidence of fit.</sub>
</td>
</tr></table>

> [!NOTE]
> **Functional** — loaded part whose failure can immobilize or damage the vehicle. Published only after documented functional testing.

## What it is

Independent concept of an integrated lever and clevis for studying a low-volume LPBF remanufacture. PorscheFanatics establishes the left and right PET part numbers; FVD publishes the envelope and mass of an aftermarket pair, but no interface geometry allows fitment.

## What it does on the car

CAD, DfAM and mechanical screening of an opening lever; no fitment and no egress use authorized

## At a glance

| | |
|---|---|
| Porsche part numbers | 99355585100, 99355585200 |
| variants | `993_door_trim_variants_to_confirm` |
| candidate material | AlSi10Mg, screening |
| candidate process | LPBF |
| safety class | `functional` |
| validation status | `concept` |
| geometry | mixed, master build123d |

## Where it stands

```mermaid
flowchart LR
    L0["concept"]
    L1["dimensionally_reviewed"]
    L2["prototype_fitted"]
    L3["functionally_tested"]
    L4["engineering_reviewed"]
    L5["released"]
    L0 --> L1 --> L2 --> L3 --> L4 --> L5
    classDef here fill:#fff4d6,stroke:#b7791f,color:#1a1a1a,stroke-width:3px;
    classDef done fill:#e3f1e6,stroke:#2e7d32,color:#1a1a1a;
    classDef todo fill:#f4f4f4,stroke:#9e9e9e,color:#6b6b6b;
    classDef stop fill:#fde2e1,stroke:#c0392b,color:#1a1a1a;
    class L0 here
    class L1 todo
    class L2 todo
    class L3 todo
    class L4 todo
    class L5 todo
```

*Validation ladder of `catalog/schemas/part.schema.json`; this record is at `concept`.*

## Views

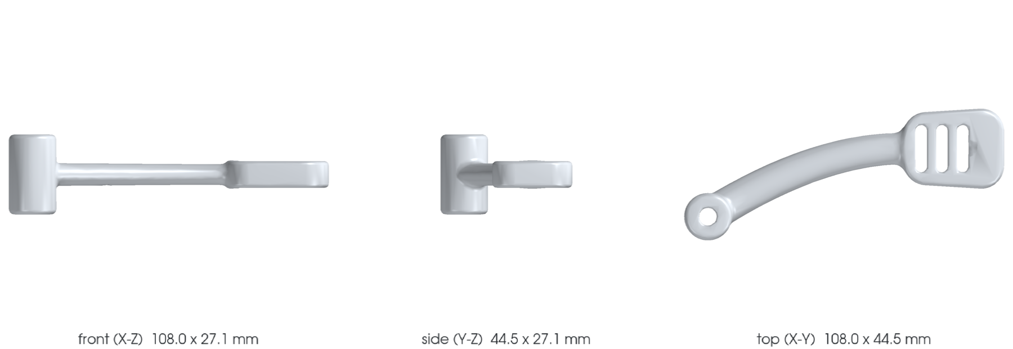
[picture p195: parts/993-int-door-opener-lever-f0-0001/media/views.png]
Front, side and top orthographic views


*Orthographic views of the same concept CAD, with its bounding dimensions — not drawings of the original part.*

## PicoGK voxel model

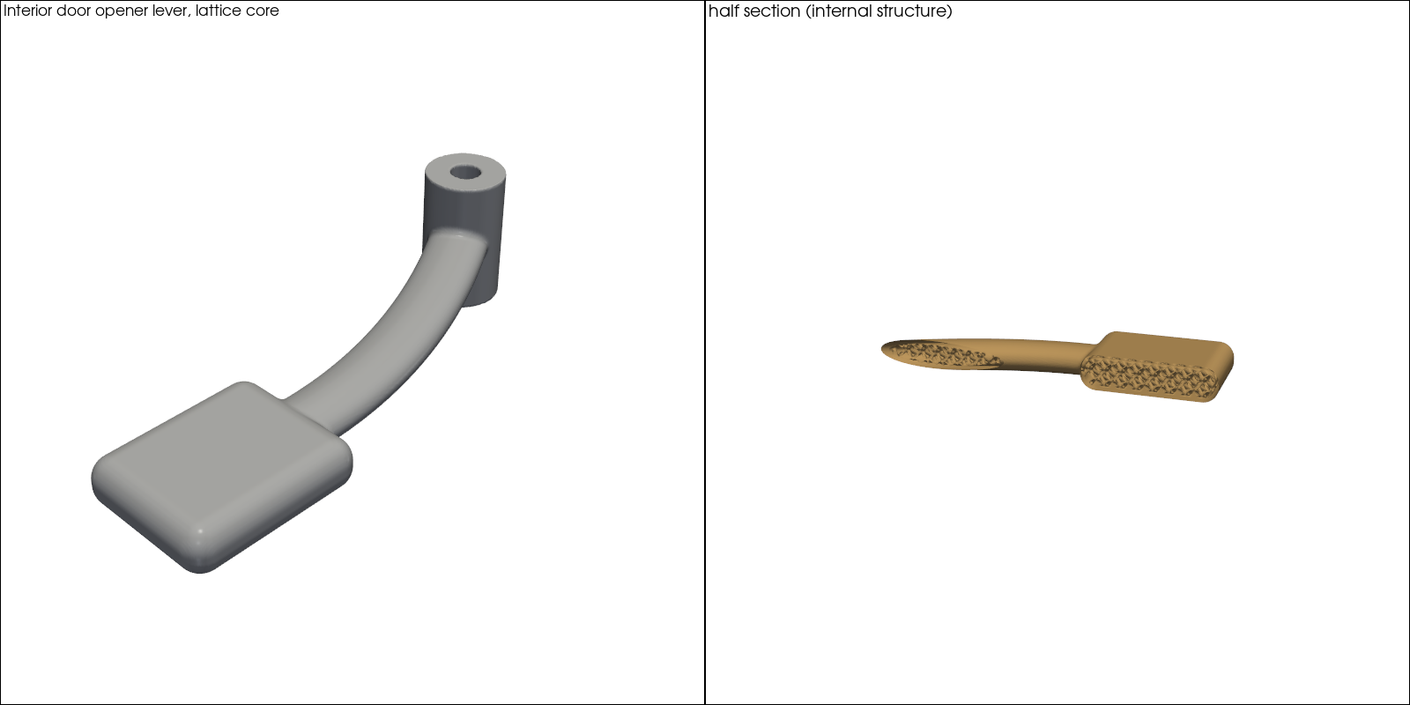
[picture p196: parts/993-int-door-opener-lever-f0-0001/media/picogk-batch-01.png]
PicoGK model: shaded view and half section


*Variant generated with the PicoGK voxel kernel in [`parts/picogk-993-batch-01`](../../parts/picogk-993-batch-01/README.md): published overall envelope, internal structure (double wall, lattice core or vanes) shown in the half section. Mounting interfaces are assumptions — not the original part, not a print file, not evidence of fit.*

## What's in this folder

| folder | what it holds | files |
|---|---|---|
| `derived/` | CAD exports generated from the source (STEP for CAD tools, STL for meshing) | [`derived/door_opener_lever_f0-picogk.json`](derived/door_opener_lever_f0-picogk.json), [`derived/door_opener_lever_f0-picogk.stl`](derived/door_opener_lever_f0-picogk.stl), [`derived/door_opener_lever_f0.step`](derived/door_opener_lever_f0.step), [`derived/door_opener_lever_f0.stl`](derived/door_opener_lever_f0.stl) |
| `evidence/` | screens, reports and manifests — **pinned by SHA-256, never edited by hand** | [`evidence/engineering-screen.json`](evidence/engineering-screen.json) |
| `media/` | concept-model views rendered from the CAD by `scripts/render_part_previews.py` — not pictures of the original | [`media/picogk-batch-01.png`](media/picogk-batch-01.png), [`media/preview.json`](media/preview.json), [`media/preview.png`](media/preview.png), [`media/views.png`](media/views.png) |
| `source/` | parametric source — the editable master that generates the geometry | [`source/door_opener_lever.py`](source/door_opener_lever.py), [`source/picogk.json`](source/picogk.json) |

## Read more

- **Full description page**, with sources and evidence: [docs/pieces/993-int-door-opener-lever-f0-0001.md](../../docs/pieces/993-int-door-opener-lever-f0-0001.md)
- **Catalogue record** (source of truth): [`catalog/parts/993-int-door-opener-lever-f0-0001.json`](../../catalog/parts/993-int-door-opener-lever-f0-0001.json)
- **Design dossier**: [993_DOOR_OPENER_LEVER_ALSI10MG_F0](../../docs/993/993_DOOR_OPENER_LEVER_ALSI10MG_F0.md)
- **Digital twin record**: [`twin-993-door-opener-lever-alsi10mg-f0.json`](../../catalog/twins/twin-993-door-opener-lever-alsi10mg-f0.json) — see [twins/README.md](../../twins/README.md)
- **Safety rules**: [SAFETY.md](../../SAFETY.md)

---

*This page is generated from the catalogue record by `scripts/render_part_pages.py` and checked by `make check`. Edit the record, not this page.*
