cluster2600/porscheparts/parts/993-eng-cooling-impeller-alsi10mg-f0-0001/README.md

<!-- generated by scripts/render_part_pages.py - do not edit by hand -->

<div align="center">

# 993 engine cooling fan — archived Carrera F0 concept

**`993-ENG-COOLING-IMPELLER-ALSI10MG-F0-0001`** · Porsche 993 · 1994–1998

  

</div>

> [!CAUTION]
> **Not ready to print, and not a copy of the original part.** This folder preserves an archived Carrera F0 concept. The current Turbo study is linked below. No part is declared dimensionally accurate, fitted, tested, safe or released without supporting evidence: see [SAFETY.md](../../SAFETY.md).

## Current programme: M64/60 Turbo cooling fan

Target: **993 Turbo M64.60 with the PMB / Classic Retrofit 240 A alternator**. Porsche PET illustration 105-00, plates 77–78, distinguishes the Turbo rotor (964 106 015 22) from the Carrera rotor (964 106 015 31, this folder's catalogue record). The experimental rotor remains partly hypothetical.

**Latest campaign:** [blade/clearance mesh recovery and CFD evidence](../../twins/993-engine-cooling-fan-system-f0/MESH_RECOVERY_20261002.md), following the [local Qwen → PicoGK → OpenFOAM / CalculiX → OpenUSD run](../../twins/993-engine-cooling-fan-system-f0/QWEN_CHAIN_20261002.md). The recovery report carries the current calculation status and archived evidence. The isolated-duct calculations do not establish airflow delivered to the installed engine.

| Work | Editable sources and evidence | Status |
| --- | --- | --- |
| Reference rebuild: 11 blades, ventilated cup, 12 windows | [Rebuild report](../../twins/993-engine-cooling-fan-system-f0/REFERENCE_REBUILD.md), [parameters](../../twins/993-engine-cooling-fan-system-f0/source/picogk-reference/reference.json), [PicoGK C#](../../twins/993-engine-cooling-fan-system-f0/source/picogk-reference/Program.cs) | Visual reference reconstruction; unmeasured parameters explicitly identified |
| Organic blade candidates A–E | [Study](../../twins/993-engine-cooling-fan-system-f0/ORGANIC_BLADE_STUDY.md), [candidate E parameters](../../twins/993-engine-cooling-fan-system-f0/source/picogk-reference/organic-e.json) | Documented numerical attempts, including failures; no validated aerodynamic optimum |
| Parametric rotor and housing, wave 2 | [M64Fan.cs](../../parts/m64-cooling-fan-0001/geometry/M64Fan.cs), [configuration](../../parts/m64-cooling-fan-0001/geometry/fan-config.json) | Editable, labelled assumptions; no archived compiled output for this separate source |
| Earlier actuator-disc CFD, OpenFOAM v2312 | [Baseline rig](../../simulation/993-fan-baseline/README.md) | Exploratory surrogate; not an installed performance prediction |
| Fan-drive metrology, M64-ACQ-0005 | [Dimensions](../../twins/m64-engine-system/metrology/fan-drive/fan-drive-dimensions.json), [scan record](../../catalog/scans/scan-fan-drive-0p21mm.json) | Initial scan analysis; ±4 mm uncertainty and unresolved discrepancies |
| Metal printing release | [Release dossier](../../twins/993-engine-cooling-fan-system-f0/PRINT_RELEASE.md) | **HOLD — no printing authorization** |

### Views generated from the actual study geometry

Reconstructed rotor: front, rear, section and exploded views

*Actual PicoGK mesh regenerated by `source/build_reference_review.py` from the [editable parameters](../../twins/993-engine-cooling-fan-system-f0/source/picogk-reference/reference.json). Status: `visual_reference_reconstruction`; [generation record](../../twins/993-engine-cooling-fan-system-f0/results/reference/generation.json). This is hypothetical CAD, not a photograph of a manufactured part.*

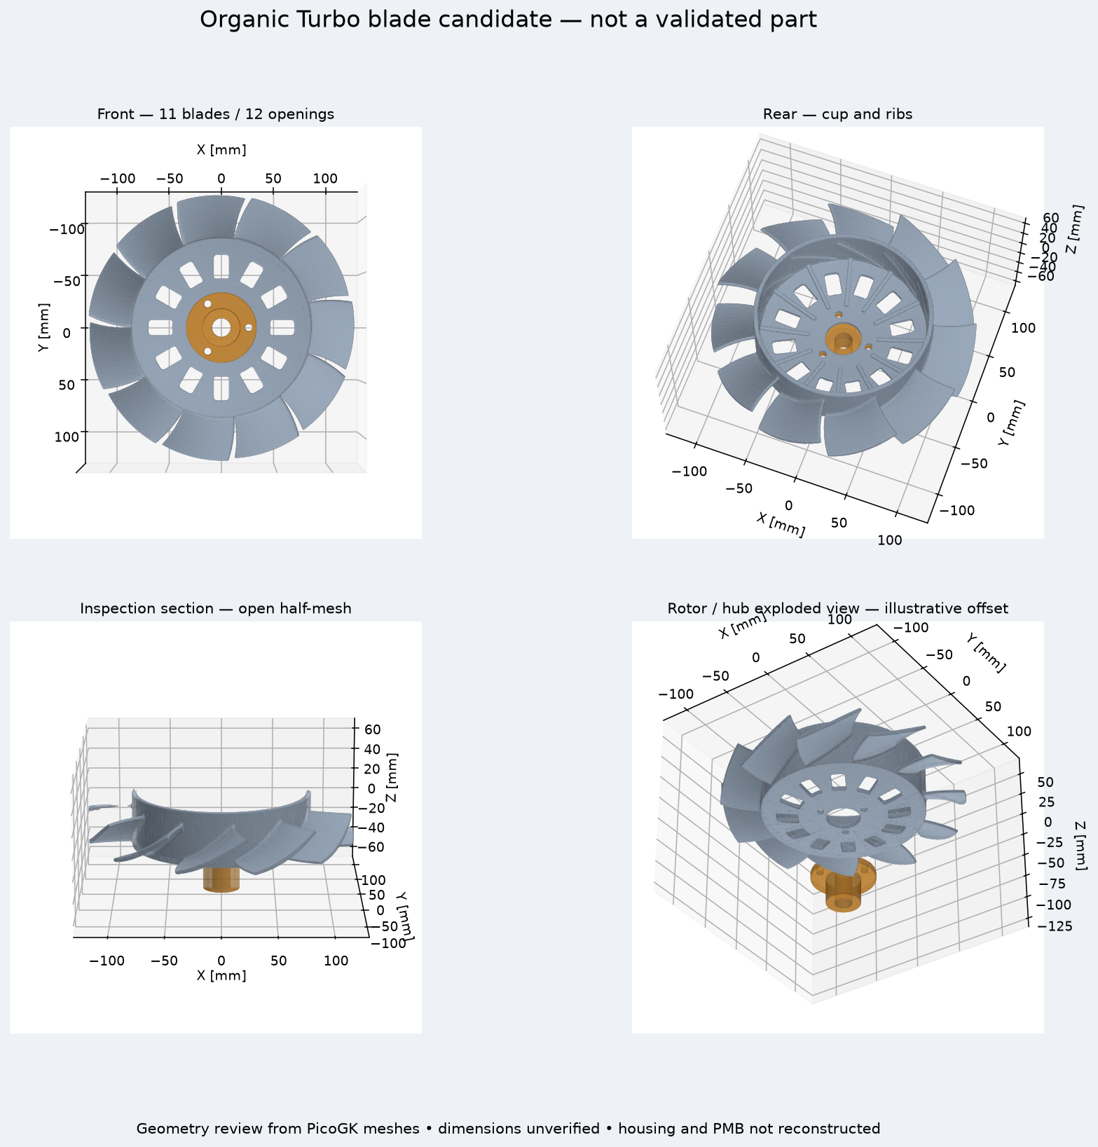
[picture p213: twins/993-engine-cooling-fan-system-f0/results/organic/e/review/reference-review.png]
Organic candidate E: actual PicoGK mesh views


*Candidate E: [mesh checks](../../twins/993-engine-cooling-fan-system-f0/results/organic/e/review/validation.json). Design hypothesis; no validated airflow gain or verified mating interfaces.*

### Fan-drive metrology

The initial M64-ACQ-0005 analysis used 1,256,836 scan vertices, nominal scan precision 0.21 mm and assumed millimetre units. Results from [fan_drive_metrology.py](../../twins/m64-engine-system/metrology/fan-drive/fan_drive_metrology.py):

| Dimension | Estimate | Uncertainty | Limitation |
| --- | ---: | ---: | --- |
| Fan pulley diameter | 229.5 mm | ±4 mm | Unresolved difference from the earlier ~255.6 mm estimate |
| Gear flange diameter | 214.2 mm | ±4 mm | Outer disc band |
| Tooth-tip diameter | 104.0 mm | ±4 mm | Radius-truncated analysis; earlier estimate was 127.6 mm |

These are preliminary estimates, not exact dimensions. The single-pass harmonic analysis was truncated at a 140 mm radius and lacks traceable instrument metrology.

## Provenance and limits

- The 11 blades and 12 windows were counted from FVD photographs, not a dimensioned drawing.
- Nominal 245 mm rotor diameter is an interpretation of commercial data, without an OEM tolerance.
- Cup depth, blade pitch, chords, thicknesses and radii remain labelled modelling assumptions.
- Hub, bearing, housing, rear cone and PMB mating interfaces are not dimensionally verified.
- The CFD lacks a measured engine resistance curve and a validated installed assembly. Rendering or solver success does not establish engine cooling performance.
- Printing remains on hold; no material/process is qualified for the rotating blades.
- Results from the archived Carrera F0 concept do not transfer to the rebuilt rotor.

## Measurements still needed

1. Confirm the actual Turbo hub and bearing interface before defining fits.
2. Measure the housing and radial rotor clearance.
3. Measure the selected PMB / Classic Retrofit 240 A interfaces and rear cone.
4. Reanalyse or scan the complete drive without radius truncation, with instrument traceability.
5. Measure the blade pitch on an original Turbo rotor.

## Archived Carrera F0 concept

This folder retains the [build123d source](../../parts/993-eng-cooling-impeller-alsi10mg-f0-0001/source/cooling_impeller.py), [STEP](../../parts/993-eng-cooling-impeller-alsi10mg-f0-0001/derived/cooling_impeller_alsi10mg_f0.step), [STL](../../parts/993-eng-cooling-impeller-alsi10mg-f0-0001/derived/cooling_impeller_alsi10mg_f0.stl) and [engineering screen](../../parts/993-eng-cooling-impeller-alsi10mg-f0-0001/evidence/engineering-screen.json). Evidence is SHA-256 pinned. The concept failed integration with its F0 housing: −14 mm radial clearance. Its 280 mm diameter, hub and twelve blades are synthetic study geometry, not a Turbo part.

The generic wheel and schematic orthographic images were removed from this presentation on 29 September 2026 because they could be mistaken for the Turbo design. They remain reproducible from the archived STEP with `make part-previews`.

## Related records

- [Full catalogue description](../../docs/pieces/993-eng-cooling-impeller-alsi10mg-f0-0001.md) (`docs/pieces/993-eng-cooling-impeller-alsi10mg-f0-0001.md`)
- [Catalogue source of truth](../../catalog/parts/993-eng-cooling-impeller-alsi10mg-f0-0001.json) (`catalog/parts/993-eng-cooling-impeller-alsi10mg-f0-0001.json`)
- [F0 design dossier](../../docs/993/993_COOLING_IMPELLER_ALSI10MG_F0.md)
- [System dossier](../../docs/993/993_ENGINE_COOLING_FAN_SYSTEM_F0.md)
- [PorscheFanatics project presentation](https://porschefanatics.com/projects/993-turbo-fan/)
- [Digital twin record](../../catalog/twins/twin-993-engine-cooling-fan-system-f0.json)
- [Safety rules](../../SAFETY.md)

---

*Generated by `scripts/render_part_pages.py` and checked by `make check`. Update the catalogue record or this part's presentation template, not the generated page.*
