cluster2600/porscheparts/docs/research/mezger-turbo-materials-20261003/README.md

# Mezger turbo engines: variants, materials and dimensions

Reviewed on 3 October 2026. This extends the [993 Turbo and K16 research](../993-turbo-20261002/README.md) for a 993 Turbo M64/60 project targeting more than 550 metric horsepower at the crankshaft. It adds **203 reviewed records linked to 46 sources**, including 41 newly catalogued sources. The machine-readable [reference](../../../catalog/reference/mezger-turbo-materials-20261003/README.md) and the separate [CPT/SFT preparation](../../../training/mezger-turbo-materials-20261003/README.md) preserve component, engine variant, source location and uncertainty.

“Mezger” identifies an engineering lineage, not one interchangeable engine. The air/oil-cooled 993 M64/60, mixed-cooling racing derivatives and water-cooled 996/997 Turbo/GT engines require separate component definitions. Naturally aspirated GT3 evidence is included as a named comparison. The direct-injected 997.2 Turbo and 991 GT3 are explicitly identified as later family boundaries.

## What can be established about the 993

| Component / application | Documentary result | Scope and limit | Records |
| --- | --- | --- | --- |
| 993 Carrera main crankcase | Aluminium-silicon alloy, split case; predecessor design continuity | Carrera factory statement plus shared Turbo PET case references support a qualified material-family relationship. No exact M64/60 grade, casting condition or wall thickness. | A001–A002 |
| 993 Carrera rocker arms | GGG70 casting grade | The direct grade statement is Carrera. Shared PET rocker lines are a separate comparison; no blanket certification of all Turbo revisions. | A003–A004 |
| 993 Carrera camshaft covers | Glass-fibre-reinforced polyamide with inserted bushes | Turbo lower covers and camshaft housings have distinct references. The 964 chapter's magnesium covers cannot replace this statement. | A005–A006, A010 |
| 993 Carrera main oil-pump housing | Die-cast magnesium | PET pump references support a qualified Turbo relationship; this is the pump housing, not the main engine case. No magnesium grade. | A007–A008 |
| 964 chain housings / stationary fan housing | Magnesium described in the 964 chapter | Not direct evidence for the 993 Turbo wheel or housing. Turbo fan references differ from Carrera. | A009, A011–A012 |
| 993 Turbo cooling casings | Aluminium for heavily stressed elements; magnesium or synthetic material for less stressed elements | The Turbo brochure does not assign individual parts or grades. | A013 |
| 993 Carrera cylinder barrels | Heat-resistant light alloy with galvanic Nikasil coating | Carrera factory chapter, not a direct material certificate for different Turbo piston/cylinder assemblies. | A014 |
| 993 sodium-filled valves | Intake filling documented for Carrera; RS intake and exhaust filling documented | Shared Turbo intake reference permits a qualified comparison. Turbo exhaust filling and metallic grade remain unverified. No titanium proof. | A016 |
| 993 GT2 road engine | M64/60 R, 3,600 cm³, 100 × 76.4 mm, 8:1, 316 kW / 430 PS at 5,750 rpm, 540 Nm at 4,500 rpm | Manufacturer road-car table. Does not define racing GT2/Evolution internals. | A018–A019 |

The primary 993 documents are the [Porsche AfterSales air-cooled training source](../../../catalog/sources/src-porsche-air-cooled-engine-repair-pubstack.json), [993 PET](../../../catalog/sources/src-porsche-pet-993.json), [Turbo brochure](../../../catalog/sources/src-porsche-uk-993-turbo-brochure-1995.json), and the [official road-GT2 technical table](https://newsroom.porsche.com/en/2024/scene-passion/porsche-911-993-gt2-coppa-florio-36266.html). The inspected workshop Volume I covers Carrera, Carrera 4, RS and Varioram; it does not supply a detailed Turbo supplement. Page and chapter scope remain attached to every record.

## Turbo and racing variants

These are published configurations, not universal horsepower ceilings or a component interchangeability chart. Rounded litre values remain rounded; museum specifications identify their stated example. Original kW, PS, HP and hp wording is preserved in the register.

| Variant | Published configuration / result | Important distinction |
| --- | --- | --- |
| 930 original | 3.0 L; 191 kW / 260 PS | Original road Turbo; separate from the later 3.3 L |
| 930, MY1978 | 3.3 L, charge cooler under rear spoiler; 221 kW at 5,500 rpm, 412 Nm | Published specification requires market/model-year context |
| 934, 1976 | 930-derived 3.0 L, approximately 357 kW / 485 PS | Group 4 racing modifications do not establish stock material grades |
| 935, 1976 → 1977 | 2.85 L single turbo, 434 kW → twin turbo, 463 kW | Later configuration has different boost architecture |
| 935 Baby, 1977 | 1.4 L turbo, 279 kW | Smaller racing derivative, not a 3.0 L component definition |
| 935/78 Moby Dick | 3,211 cm³; water-cooled multivalve heads; up to 621 kW | Water-cooled heads alone do not prove a wholly water-cooled engine |
| 936, 1976 / 1977 / 1978 | 2.1 L air/single turbo → twin turbo → four-valve water-cooled heads | Several distinct engine generations |
| 936, 1981 / early 956 | 2.65 L twin turbo, 456 kW; Indy-program origin | Fuel and calibration of the original Indy programme are distinct |
| 956 museum specification | 2,649 cm³, 456 kW | Does not describe every subsequent Group C revision |
| 962 IMSA | Air-cooled, single turbo; evolutions from 2.8 to 3.2 L | Cannot inherit 962 C cooling or turbo count |
| 962 C | 2.65 L and later fully water-cooled 3.0 L twin-turbo variants coexist | Exact race year and engine revision matter |
| 959 road | 2,849 cm³, aluminium-alloy block, air-cooled cylinders, water-cooled heads, sequential turbos | Generic aluminium family only; not the 993 parallel-K16 layout |
| 911 GT1-98 | Water-cooled mid-engine flat-six; museum example 3,220 cm³ / 404 kW | Named museum configuration; not every GT1 race or road specification |
| 996 Turbo / GT2 | Porsche explicitly links the Turbo to GT1 engine development | Family history does not prove identical GT3/Turbo internals |
| 997.1 Turbo / 997 GT2 | 3.6 L water-cooled generation with external dry sump | Distinct from the 997.2 Turbo direct-injected 3.8 L engine |

The principal racing source is [Porsche's 50 years of turbo technology dossier](https://newsroom.porsche.com/en/press-kits/50-years-porsche-turbo/Porsche-and-turbo-technology-in-motorsport--from-pioneer-to-world-champion.html), supported by individual museum entries and [Porsche's 959 cutaway description](https://newsroom.porsche.com/en/history/porsche-history-959-iaa-cut-away-model-12386.html). R001–R039 and W054–W065 retain the exact source sections.

## Factory water-cooled engine materials

The original Porsche brochures were read from public mirrors; their manufacturer colophons, editions, document codes and capture hashes are recorded. Raw brochures are not redistributed.

| Application | Material/process explicitly published | What remains unidentified |
| --- | --- | --- |
| 997.1 Turbo, edition 12/2005 | Forged aluminium pistons; aluminium cylinder liners with Nikasil; heat-resistant light-alloy heads; light-alloy two-section crankcase; forged rods | Piston aluminium grade, cylinder/head/case grades, rod metal, heat treatments and wall/coating thicknesses |
| 997 GT2, edition 03/2008 | Same explicitly stated material families and forging descriptions | No transfer to 993 parts or precise common geometry |
| 997 GT2 and GT2 RS exhaust | Titanium rear silencer and tailpipes | Titanium grade and wall thickness; this does not identify rod or turbine material |
| 997.1 GT3 / GT3 RS 3.6 L | Titanium rods, forged pistons, Nikasil bores; maximum engine speed 8,400 rpm | Titanium grade, component mass and dimensions; no transfer of rpm limit to Turbo |
| 997.2 GT3 3.8 L / shared GT3-RS section | Forged aluminium pistons, titanium rods, Nikasil bores; maximum engine speed 8,500 rpm | Exact grades and geometry. The cutaway is captioned GT3; GT3 and RS compression ratios differ |

See [997 Turbo brochure source](../../../catalog/sources/src-mezger-watercooled-porsche-997-turbo-brochure-2006.json), [GT2 source](../../../catalog/sources/src-mezger-watercooled-porsche-997-gt2-brochure-2008.json) and [GT3 source](../../../catalog/sources/src-mezger-watercooled-gt3-9972-brochure.json). W001–W047 and W066–W073 contain the detailed evidence. The approximately 1,000 °C gasoline-exhaust statement is thermal context, not a measured 993 temperature or an approved continuous turbine-inlet limit. Published boost figures whose gauge/absolute reference is unspecified retain that uncertainty.

## Identified aftermarket alloys and processes

| Product / precise application | Published material or dimension | Limit |
| --- | --- | --- |
| MAHLE PP102-012N, 993 Turbo 3.6 → 3.8 L | Forged aluminium **2618**, 102 mm bore; 31.8 mm compression height; 9.6 cm³ crown volume | Height and volume are not crown thickness; not the stock 100 mm piston alloy |
| Matching LN105-102/109 cylinder in MAHLE guide | 114.5 mm cylinder height, 109 mm case register | Neither value establishes a local wall thickness |
| MAHLE PP102-013, 964 Turbo / named conversion applications | **4032** | Different reference and application from PP102-012N |
| MAHLE PP98-012 / PP98-016 | **4032**, respectively 930 3.3 → 3.4 L and 3.0 → 3.2 L conversions | Original Porsche piston metallurgy remains unidentified |
| MAHLE PP100-010N, 930T 3.3 → 3.5 L | **2618**, hard-anodised top ring groove | Exact anodic thickness and treatment recipe unspecified |
| LN Nickies | Proprietary low-silicon extruded aluminium, CNC machining, electroplating and plateau honing | Grade is not disclosed; do not rename it 6061, 6063 or A356 |
| LN NSC finished bore coating | **0.004–0.005 inch per side after honing = 0.1016–0.127 mm**; SiC particles 1–3 µm, approximately 7–14% by volume in nickel matrix | Supplier process range, not OEM Nikasil thickness or a batch analysis |
| LN993BCH / LN930BCH billet heads | Stress-relieved wrought aluminium, CNC machined | 6061-T6/T651 and A356-T6 are comparison grades, not the product's disclosed alloy |
| Xtreme Porsche head programmes | **RR350**, lost-wax investment casting, HIP | Aftermarket manufacturer declaration; exact chemistry, HIP recipe and wall dimensions unknown |
| Pauter 993-230-580-1270F | **4340 chrome-moly**, centre distance 127.00 mm, total mass 535 g, big-end mass 373 g | Dimensions are supplier declarations. Not OEM material evidence or proof of a specific delivered forging route |
| Pauter custom titanium rod family | **6AL4V** bar stock; average claimed 33% lighter than steel counterparts | No confirmed custom 993 titanium part drawing or measured mass; do not calculate a supposed 993 titanium mass from the average |
| Kline 993 Turbo exhaust | **Inconel 625**; manifold with heat exchanger 2.9 kg each | Exact tube dimensions, wall thickness and weld specification are absent |
| Swindon M64 24-valve kit | 40/33 mm intake/exhaust valves, 95–102.7 mm bore range, 16.6 cm³ head volume | Reviewed public sheet does not disclose head grade or valve metal. 12,000 rpm is claimed valvetrain capability, not a stock Turbo engine limit |

Sources: [MAHLE 2024 application guide](https://www.us.mahle.com/media/usa/motorsports/2024-mahle-motorsport-porsche-application-guide-2.pdf), [LN material-source records](../../../catalog/sources/src-mezger-materials-ln-nsc-plating-faq.json), [Xtreme source](../../../catalog/sources/src-mezger-materials-xtreme-rr350-heads.json), [Pauter exact 993 product](https://pauter.com/shop/rods/porsche/porsche-993-993-turbo-rods/), [Kline source](../../../catalog/sources/src-kline-993-turbo-in625-manifolds.json), [Swindon product sheet](https://swindonpowertrain.com/wp-content/uploads/2025/10/M64-24V-Cylinder-Head-Kit-Product-Sheet-0923.pdf). The full tables and conditions are in M001–M033 and P001–P035.

LN's general 0.003–0.005 inch industry-coating range is a separate record; it is not silently merged with the expressly finished per-side NSC range. The LN993BCH page has a wrong 930 HTML metadata title, but its visible heading, SKU and 993RS port description identify a distinct 964/993 aftermarket product. That inconsistency is retained.

## Remaining documentary and measurement gaps

No source acquired in this increment defines the original M64/60 head, case, piston or cylinder's exact chemical grade and full metallurgical condition, or a local wall-thickness map. RR350 aftermarket heads, historical Alusil A390, generic supplier 4032 comments and GT3 titanium rods cannot fill those gaps.

A further 14 inspected Porsche articles are retained as [additional bibliographic readings](../../../catalog/reference/mezger-turbo-materials-20261003/additional-readings.json), without inventing extra component facts or training targets.

The next documentary targets and measurement distinctions are in [research-gaps.json](../../../catalog/reference/mezger-turbo-materials-20261003/research-gaps.json): model-specific Turbo Service Information Technik, Motorsport GT2/Evolution literature, homologation extensions, identified part drawings/material specifications and component metrology. FIA documents were not obtained because access returned 403. An external scan of a different racing head cannot identify hidden internal walls or alloy composition of the project engine.

Hans Mezger's [SAE 780718, Turbocharging Engines for Racing and Passenger Cars](https://saemobilus.sae.org/papers/turbocharging-engines-racing-passenger-cars-780718) is a useful primary-document lead: its publisher abstract and citation were read, its full text was not acquired. [SAE 830004](https://doi.org/10.4271/830004) discusses alloy 390 and earlier 911 experience, but its abstract does not identify the relevant 911 component. Both leads remain excluded from technical training.

For the greater-than-550-PS project, these records improve material identification and the list of measurements to obtain. They do not establish a unique original K16 map, the endurance of a hybrid turbo, or a qualified redesigned head. Existing geometry, evidence contracts, solver inputs and previously frozen training packs remain separate from this research increment.

## Data preparation and validation

The separate pack contains **200 CPT passages and 200 grounded SFT conversations**. Each format has 173 train, 18 validation and 9 test rows. Three records are excluded; five records explicitly teach the limits of the review. Application, component, original units, citations and caveats accompany every passage. Source-family and identical-reviewed-claim partitions respect the previous 993 pack. Pauter and independent Xtreme/Kline families are held out where compatible with those constraints.

These are authored factual summaries and supplied-record extraction examples. They are not copied manuals, an independent engineering benchmark, a tokenised corpus or a completed training run. The [training manifest](../../../training/mezger-turbo-materials-20261003/manifest.json) records counts and hashes. The [validation receipt](validation.json) records the actual checks and any environment limitations.
