cluster2600/porscheparts/parts/993-eng-carrier-0001/media/r9/README.md

# 993 titanium carrier — publication projection

This folder is the complete, narrow publication input prepared for the separately authorized English GitHub page update. Read only the files listed in `manifest.json`. No CAD transfer, supplier contact, fabrication order or publication is performed by this package. The project-generated render bytes are unchanged. They contain no third-party OEM photos or source pixels according to their frozen render receipts. User approval on 6 October 2026 covers public projection of these original project renders and factual results; this is not a claim that a repository-wide reuse licence has been established.

The part studied is Turbo carrier PET item 17, reference 99311502153. Item 18, 99311510352, is a separate bracket. OEM alloy, construction, actual dimensions and crack mechanism remain unverified. Cracking above 700 metric horsepower is a user concern, not a demonstrated threshold. Engine power alone does not determine carrier loads.

R9 is a frozen inspection reference with provisional interfaces. The main geometry render is the actual R8/R9 exported triangle comparison, not a generative image. The mechanical render contains actual numerical fields. The frozen verification render must accompany any stress comparison because the later fixed 3D regions expose unresolved maxima. Do not present 901.4 MPa, or the local R8-to-R9 change, as converged physical stress or a strength margin.

| Fixed 3D region | p MPa | h/2 MPa | h/4, moved cuts MPa | h/2 to h/4 |
|---|---:|---:|---:|---:|
| K1 | 267.2 | 335.0 | 419.2 | +25.1% |
| K2 | 455.7 | 670.9 | 1028.2 | +53.3% |
| K3 | 576.4 | 667.2 | 792.2 | +18.7% |

These comparisons use frozen 3D regions, not changing maxima across different regions. Moving the cuts changes these peaks by approximately 0.023%, 0.119% and 0.007%, respectively, but does not establish stress convergence. Reentrant faceted edges are present in the represented geometry. No finished minimum radius, actual mount stiffness, bolt preload/contact, fabrication process, static allowable or fatigue life has been qualified. This numerical behavior is consistent with a represented geometric singularity; it does not establish the OEM failure mechanism.

The illustrative common wrench is Fz=-3775.56025 N, Mx=425000 Nmm and My=-94389.00625 Nmm about the model origin. It derives from 350 kg engine mass, 55% rear share, effective 2g vertical acceleration, 850 Nm engine torque and 50% rear roll-torque share. The moment is transported once. Dense titanium reference elasticity is E=107 GPa, nu=0.31 and rho=4420 kg/m3; these are not LPBF strength or fatigue allowables.

The dense-volume mass is 1.03203685 kg in the native representation and 1.031119181886 kg from the oriented STL. Their 0.917668 g difference includes the representation difference. They are not measured fabricated masses.

Subsequent R10 reconstruction remains unadmitted. A local double export can meet the signed-normal gate while the same tessellation in world-coordinate binary32 STL fails it; this is a precision finding, not whole-part validation. Exact nominal T12 tool clearance conflicts with a regular C2 surface where its sharp cap-cylinder rim lies inside retained R9 material. Geometry gates remain closed, so no new whole-carrier FEM is started. No crack-free claim or manufacturing-ready status is supported.

Only the relative filenames and SHA256 hashes in this package may be copied. Personal paths, remote hostnames, private neighbouring studies, original OEM catalog photos, raw contact information and private receipts are excluded. Selected provenance hashes identify evidence without exposing its private storage paths.
