cluster2600/porscheparts/docs/PHASE1_SOURCE_INVENTORY.md

# Phase 1 — Source inventory

This document tracks Phase 1 progress. It hosts no protected content: it records
where a piece of information lives, how it was consulted, and what its legal
status permits.

## Batch 1 — Official catalogs, legally accessible manuals and measurements

Consulted on August 28, 2026. Every URL was opened before being entered; access
failures are kept on the same footing as successes.

### Official catalogs and documents

| Record | Content | Access | Reuse | Evidence |
|---|---|---|---|---|
| `SRC-PORSCHE-PET-993` | Porsche Classic Genuine Parts catalog | available | prohibited | A |
| `SRC-PORSCHE-NEWSROOM-993` | History dossier and model range | available | prohibited | A |
| `SRC-PORSCHE-NEWSROOM-993-30Y` | Press kit "30 years of the 993" | available | prohibited | A |
| `SRC-PORSCHE-SHOP-TECHLIT` | Official technical literature for purchase | available, empty catalog | prohibited | not rated |
| `SRC-PORSCHE-CLASSICSHOP-USA` | Former Classic shop (993 manuals) | out of service (DNS) | prohibited | not rated |

### Accessible manuals and technical data

| Record | Content | Access | Reuse | Evidence |
|---|---|---|---|---|
| `SRC-9XXTEILE-PET-DIAGRAMS` | Exploded views and part numbers | free | prohibited | C |
| `SRC-PCA-993-ALIGNMENT` | Factory suspension alignment settings | free | prohibited | C |
| `SRC-WIKIPEDIA-993` | Vehicle envelope and variants | free | attribution required | D |
| `SRC-STUTTCARS-993-PARTS` | Advertised PET diagrams | paid | unknown | not rated |
| `SRC-STUTTCARS-993-TORQUE` | Engine tightening torques | paid | unknown | not rated |
| `SRC-PORSCHEFANATICS-993-MANUAL-DATA` | Public index and data derived from the manual: 235 procedures, 195 torques and 111 technical values | available | reference only | C |

### Measurements and dimensional data

| Record | Content | Access | Reuse | Evidence |
|---|---|---|---|---|
| `SRC-CARGEOMETRY-993-BODY` | Body shell and underbody measuring points | purchase (20 USD) | prohibited | B |
| `SRC-WHEEL-SIZE-993` | Wheels, offsets, bolt pattern | free | unknown | C |
| `SRC-CARFOLIO-993` | Masses and dimensions by variant | free | prohibited | D |
| `SRC-ELFERCLASSIC-993-TECHNICAL-DATA` | German compilation: envelope of the 993 Carrera 2 ROW (4,245 × 1,735 × 1,300 mm), wheelbase, tracks, ground clearance and geometry references | access expired | not redistributable | C |
| `SRC-RENNLIST-993-FORUMS` | Community workshop measurements | blocked to bots | unknown | C |
| `SRC-PELICANPARTS-964-993-FORUM` | Community workshop measurements | blocked to bots | unknown | C |

## Rejected sources

Rejected without being entered in the registry. The reason is kept so they are
not re-examined.

| Source | Reason |
|---|---|
| Scribd, SlideShare, eManualOnline, eManuals, workshopcarmanuals | Redistribution of the Porsche workshop manual with no demonstrable right |
| GitHub mirror of the booklet `Technical Specifications 911 Carrera (993)` | The public copy makes the factory table "Dimensions for Floor System" (page 110) readable, but the hosting and reproduction rights are not established; no PDF is kept |
| Forum attachments containing dimensioned factory plates | Same protected document, republished by a third party |
| PDF aggregators with no identifiable publisher | Unverifiable provenance |

A rejected source can remain useful as a hint that a document exists. It never
becomes a catalog reference.

## Batch 1 findings

- No dimensioned factory drawing is legally and freely accessible. Exploded
  views document assembly and the bill of materials, not geometry.
- Usable dimensional data will come from direct measurement, supplemented by a
  purchased body shell reference (`SRC-CARGEOMETRY-993-BODY`).
- Part numbers are freely accessible, but redistributing them is not: they
  serve as working identifiers, not as published content.
- Two major forums refuse automated access; consulting them stays manual and
  every value taken from them must be re-measured.
- The community corpus frequently copies the same uncited origin; the rule
  "two copies do not make two confirmations" applies directly.
- The public mirror of the Porsche technical booklet `1st Edition, Status 8 1995`
  confirms that a floor pan check table exists: A/P21 440 ± 2 mm,
  B/P3 670 ± 0.5 mm, C/P5 770 ± 2 mm, D/P6 204 ± 2 mm, E/P18 1,330 ± 1 mm,
  F/P19 1,236 ± 1 mm, G/P12 278 ± 1 mm, H/P20 1,018 ± 1 mm, I/P13 935 ± 1.5 mm,
  K/P14 973 ± 1.5 mm and L/P22 640 ± 1 mm. The document states that dimensions
  are taken from the center of holes or screw points and that dimensions in
  parentheses are horizontal. These values are a lead for buying or consulting
  an authorized copy, not project measurements nor redistributable geometry.

## Batch 2 — 3D models and digital twins

Searched in English and German on August 28, 2026, across 3D marketplaces, scan
shops, digitization services and the technical press.

### The finding

**No freely reusable, verified digital twin of the 993 was found.** Commercial
body scans exist, but they are exterior-only, purchase-only, self-declared and
without a public metrology report. What exists falls into four categories:

| Category | Example | Level | What it is worth |
|---|---|---|---|
| Synthetic visual mesh | game models, 3D stock libraries, RWB Sketchfab | D | Silhouette, never an interface |
| Raw unscaled scan | `SRC-SKETCHFAB-993-GT2-RAW-SCAN` | E | Shape, not measurement |
| Commercial component scan | `SRC-BREMAR-3D-SCAN-STORE` | D | No 993 component |
| Commercial body scan | `SRC-WOLFE-993-TURBO-EXTERIOR-SCAN`, `SRC-SKETCHFAB-993-BARN-FIND-SCAN` | D | Exterior declared at 1.76–2 mm, with no verified dimensions and no redistribution license |

The only complete 993 body scan found with a declared open license remains the
raw GT2 scan, under CC BY 4.0. It was obtained by videogrammetry from 115 frames
taken from a YouTube video: no scale, no stated accuracy, and a rights chain
that is not watertight since it derives from images owned by a third party. By
contrast, the archive `SRC-RENN3DPARTS-993-OPEN-FILES` lists nine part files
under licenses declared per record (CC-BY, CC-BY-SA, CC-BY-NC, CC-BY-NC-SA or
public domain). These part meshes are neither a vehicle scan nor evidence of
interface accuracy; the primary license and the units must be confirmed before
redistribution. The
[supplementary German-language search](research/phase-1-recherche-allemande.md)
listed other community assets with declared licenses, to be confirmed on their
original publications. None of these assets is dimensionally qualified. The two
commercial body scans therefore remain leads for purchase and comparison, not
free substitutes.

### What exists, but out of reach

Porsche Classic already does exactly this work, in-house
(`SRC-PORSCHE-CLASSIC-3D-PRINTING`): SLM for steel, SLS for polymers, and "a 3D
scan of the component is enough as a basis to start production". Eight parts
produced, about twenty under study, checked by pressure testing, tomography and
fit checks on the vehicle.

It is both a validation of the approach and the bar to clear. The manufacturer
does not publish this data.

### The lead that would have scaled, and is closed

`SRC-CAR-CLOUDS-POINT-CLOUDS` sells laser point clouds of complete vehicles at
195 USD. A full-car scan would give the mounting environment of dozens of parts
at once, where a part measurement serves only one: it was the best answer to the
scale problem.

Catalog queried in full on August 28, 2026 — 906 products, five Porsches:

| Model | Price |
|---|---|
| Porsche 911 Cabriolet (996) 2001 | 195 USD |
| Porsche 911 2015 (991) | 195 USD |
| Porsche Cayenne 2019 and 2020 | 195 USD |
| Porsche Macan 2019 | 195 USD |

**No 993, and nothing air-cooled.** The closest is a 996: next generation,
entirely different body shell. It is not a substitute.

The deliverable is an E57 point cloud, interior included. The lead would only
reopen through a dedicated digitization order, at an entirely different price
level — or through another provider, yet to be identified.

## Batch 5 — German-language search, 993 measurements and scans

Consulted on August 29 and 30, 2026. The results are recorded in the source
registry; no forum image, protected attachment, raw digitization or third-party
CAD file is copied into the repository.

### Community measurements

| Record | Result | Level | Decision |
|---|---|---|---|
| `SRC-PFF-993-RS-LETTERING-MEASUREMENT` | Carrera RS script: 28.5 cm from each side, 6 cm from the lower edge, 33 cm long, 3 cm high | C | Lead to re-measure, no geometry published |
| `SRC-PFF-993-CABRIO-ROOF-BUSHING-MEASUREMENT` | Convertible top bushing: outer Ø 12 mm, inner Ø 10 mm, depth 9 mm, with flange | C | Lead to re-measure on a removed part; no interchangeability claim |
| `SRC-PFF-993-SPEAKER-DIAMETERS` | Speakers reported at 165 mm front and 130 mm rear on a 1997 Cabrio; depth unknown | C | Context for an audio bracket; also measure depth, opening and fasteners |
| `SRC-PFF-993-FRONT-SPEAKER-MEASUREMENT` | Another German thread reports 13 cm at the front without Sound-Paket, and a substantial modification to go to 16 cm | C | Contradicts the 165 mm reported on a Cabrio; separate audio variant, nominal diameter and opening by direct measurement |
| `SRC-PFF-993-SUNROOF-REVERSE-ENGINEERING` | Reconstruction of 993 sunroof parts in reinforced polymer | not rated | Interesting project to contact; no dimension or CAD published |
| `SRC-PFF-993-RS-SPRING-DATA` | RS spring wire diameters and rates reported by the forum | C | Documented, but excluded from manufacturing decisions: safety-critical suspension |
| `SRC-PFF-993-STABILIZER-BAR-DIAMETER` | Rear diameter declared at 18 mm on a 1995 C2 Tiptronic, within an 18–21 mm range | C | Direct measurement mandatory; safety-critical suspension, no manufacturing |
| `SRC-PFF-993-DISTRIBUTOR-BEARING-DIMENSIONS` | 964/993 distributor bearings declared at about Ø32 mm outer, Ø12.45 mm inner and 10 mm high | C | Community measurement with no instrument, repeats, variant or datum; identify and measure the removed part before any replacement |
| `SRC-PFF-993-BRAKE-LIGHT-SWITCH-TRAVEL` | Declared brake light switch travel: 6–16 mm, measured at the middle of the pedal rubber on a 993 Tiptronic | C | Safety adjustment with no instrument, repeats or year; check against workshop documentation and on the vehicle, no manufacturing or modification |
| `SRC-ELFERSZENE-993-VALVE-SPRING-INSTALLATION-LENGTH` | German procedure and declared installed lengths for 993 valve springs: intake 36.7 + 0.3 mm / exhaust 35.7 + 0.3 mm, or 37.2 + 0.3 mm / 35.8 + 0.3 mm for M64/20 RS | C | Page blocked, values taken from the index with no independent validation; highly loaded valvetrain, no reproduction or release without engineering review and fatigue validation |

These values are member claims, with no instrument, repeats, measurement datum
or independent validation. They serve to prepare a direct measurement, not to
mark a part "accurate", "fitted" or "tested".
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
