cluster2600/porscheparts/docs/917_MATERIAL_LPBF_QUALIFICATION_F49.md

# F49 — matière et procédé LPBF pour les culasses turbo 2V/4V

F49 sélectionne une **route d'éprouvettes**, pas une matière libérée. Le candidat
principal est **Aheadd CP1, couches de 50 µm sur Velo3D Sapphire, puis 400 °C
pendant 4 h**. A20X A205-T7 reste le candidat de repli si les essais montrent
que la résistance de CP1 à chaud est insuffisante. Cette décision s'applique de
la même manière aux variantes 2V et 4V.

Le lot ne crée aucune CAO, aucun maillage et aucune cote d'interface. Il lie par
SHA-256 les écrans F45, la politique interne F47 et les chargements F47. La
peau externe reste exclusivement celle des contours de scan F43, identique en
octets pour 2V et 4V : F49 interdit toute modification de forme, toute mise à
l'échelle uniforme ou directionnelle et toute réutilisation d'un ancien proxy.
Les cylindres analytiques circulaires restent limités aux fonctions internes
explicitement autorisées par F47. Les pressions et températures de
gaz F47 restent des enveloppes 0D non corrélées; elles ne définissent ni la
température du métal, ni une pression d'épreuve.

## Décision matière

| Route | Preuve publique utile | Lacune bloquante | Rôle F49 |
| --- | --- | --- | --- |
| Aheadd CP1, 400 °C/4 h | 323 MPa de Rp0,2, 342 MPa de Rm, 12,8 % d'allongement et 187 W/mK à l'ambiante; stabilité annoncée 250–300 °C | aucune courbe publique de traction, conductivité, fatigue, fluage ou relaxation à chaud pour la route exacte | premier candidat d'éprouvettes |
| A20X A205-T7 | Rp0,2 publiée de 311 MPa à 200 °C et 215 MPa à 250 °C | conductivité et gamme complète thermo-mécanique absentes; recette T7 propriétaire; domaine d'emploi annoncé seulement jusqu'à 190 °C | repli résistance à chaud |
| AlSi10Mg-T6 | procédé EOS M290 mature et conductivité ambiante 155–165 W/mK | carte chaude et tenue fatigue/TMF absentes; la fiche EOS avertit que T6 peut accroître la porosité | témoin de procédé mature |
| AlF357, famille AlSi7Mg | Rp0,2 265 MPa, Rm 330 MPa, A 11,5 % et 150 W/mK à l'ambiante | carte chaude, densité de la route et allowables de défaut absents | second témoin Al-Si |
| 2618-T61 usiné/forgé | nuance encore couverte par AMS4132J:2026; données historiques à chaud disponibles | ce n'est pas une poudre LPBF; les points NASA sont lus sur un graphe d'extrusion T6511 après 100 h, donc non transférables | référence conventionnelle seulement |

Sources primaires principales : [fiche CP1 Constellium](https://assets.foleon.com/eu-central-1/de-uploads-7e3kk3/41170/product_sheet_aheadd_cp1_nov_2021docx.e81a7d073ebf.pdf),
[fiche CP1 Velo3D](https://velo3d.com/wp-content/uploads/2025/04/Velo3D-Material-Datasheet-Aluminum-CP1.pdf),
[capacité CP1 de PWR](https://www.pwr.com.au/products/additive-manufacturing),
[A20X ECKART](https://www.eckart.net/en/download/document/view/id/51/),
[AlSi10Mg et AlF357 EOS](https://www.eos.info/metal-solutions/metal-materials/aluminium),
[AMS7074](https://saemobilus.sae.org/standards/ams7074-aluminum-alloy-powder-11zr-10fe-aheadd-cp1),
[AMS4132J](https://saemobilus.sae.org/standards/ams4132j-aluminum-alloy-die-hand-forgings-rolled-rings-23cu-16mg-11fe-10ni-018si-007ti-2618-t61-solution-precipitation-heat-trea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)
et [données NASA 2618](https://ntrs.nasa.gov/api/citations/19930022454/downloads/19930022454.pdf).

Les valeurs Velo3D proviennent d'une seule machine et de 56 éprouvettes
verticales usinées. Leurs minima à 20 °C — 297 MPa de Rp0,2, 331 MPa de Rm et
13,9 % d'allongement — sont un repère de réception si la route est reproduite à
l'identique, jamais un allowable de conception.

## Machine et placement à qualifier

La machine de référence est une **Velo3D Sapphire standard chez PWR**. Le
constructeur publie un volume cylindrique de 315 mm de diamètre sur 400 mm de
haut, deux lasers de 1 kW et un racleur sans contact. PWR publie l'emploi de CP1
en 50 et 100 µm. Aucun engagement du fournisseur pour cette pièce n'est acquis.

Le test d'encombrement utilise uniquement l'enveloppe minimale demandée
225 × 120 × 98 mm. Pour un roulis de criblage de 35° autour de l'axe long :

\[
W' = W\cos\phi + H\sin\phi,\qquad
H' = W\sin\phi + H\cos\phi
\]

\[
D_{requis}=\sqrt{L^2+W'^2}.
\]

Il donne 225 × 154,509 × 149,106 mm et
\(D_{requis}=272,943\) mm : l'enveloppe nue tient, avec 42,057 mm de jeu
diamétral et 250,894 mm en hauteur. Ce calcul exclut les surépaisseurs, le
plateau, les supports et la marge du racleur. `final_build_fit_verified` reste
donc faux. Le fournisseur doit comparer 25°, 35° et 45° dans Flow avant de
choisir l'orientation.
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
