cluster2600/porscheparts/docs/917_VALVETRAIN_MATERIAL_SCREEN_F45.md

# Criblage distribution et matière F45 — culasse 917/30 turbo

## Résultat

F45 fournit un **pré-dimensionnement analytique**, reproductible et fermé par
défaut, de deux architectures de recherche : 2 soupapes et 4 soupapes par
cylindre. Il ne libère ni une culasse, ni une distribution, ni une impression.

La contrainte géométrique est absolue dans ce sous-lot :

- alésage strictement circulaire de 90 mm, issu de l'autorité F45 ;
- composants fonctionnels circulaires uniquement ;
- enveloppe extérieure `scan-contour` conservée ;
- aucune ovalisation, mise à l'échelle anisotrope, surface de corps ou ailette
  synthétique ;
- aucune cote d'interface Porsche inventée.
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
