cluster2600/porscheparts/parts/m64-cooling-fan-0001/evidence/m64-cooling-fan-rotor.png

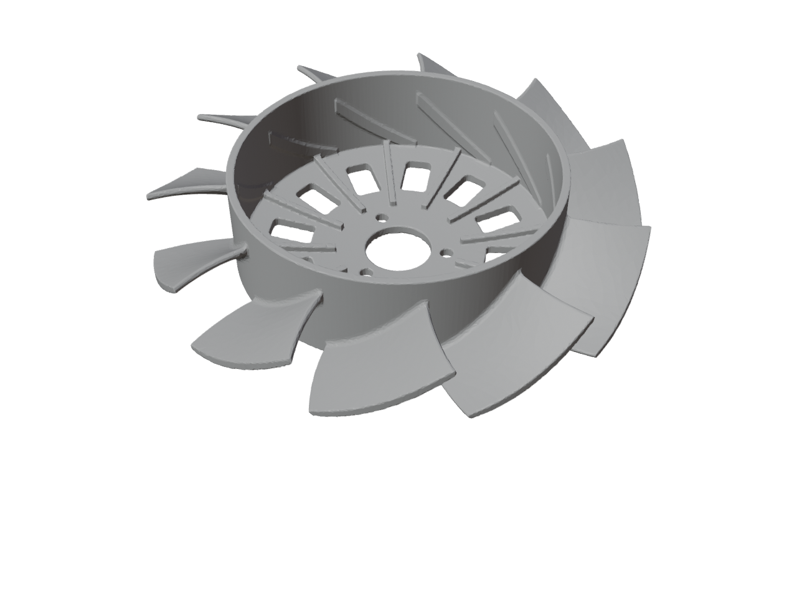
parts/m64-cooling-fan-0001/evidence/m64-cooling-fan-rotor.png
