cluster2600/porscheparts/parts/m64-cooling-fan-0001/evidence/m64-fan-housing-axon.png

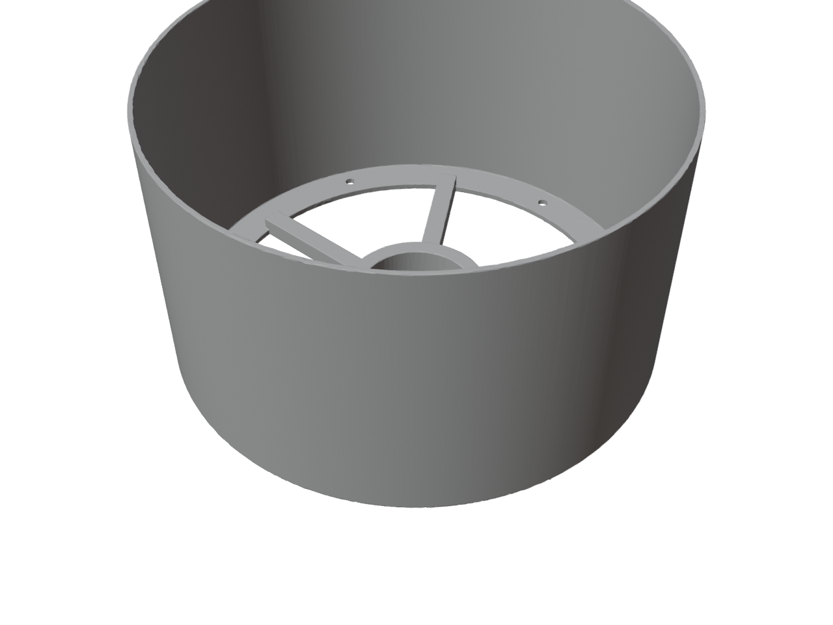
parts/m64-cooling-fan-0001/evidence/m64-fan-housing-axon.png
