cluster2600/porscheparts/parts/m64-cylinder-head-0001/evidence/m64-cylinder-head-axon.png

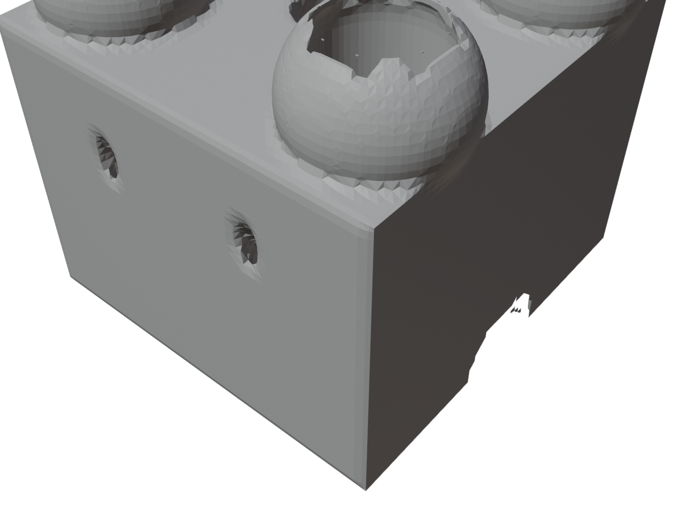
parts/m64-cylinder-head-0001/evidence/m64-cylinder-head-axon.png
