cluster2600/porscheparts/twins/reference-917-engine/evidence/f45-valvetrain/valvetrain-material-screen-f45.png

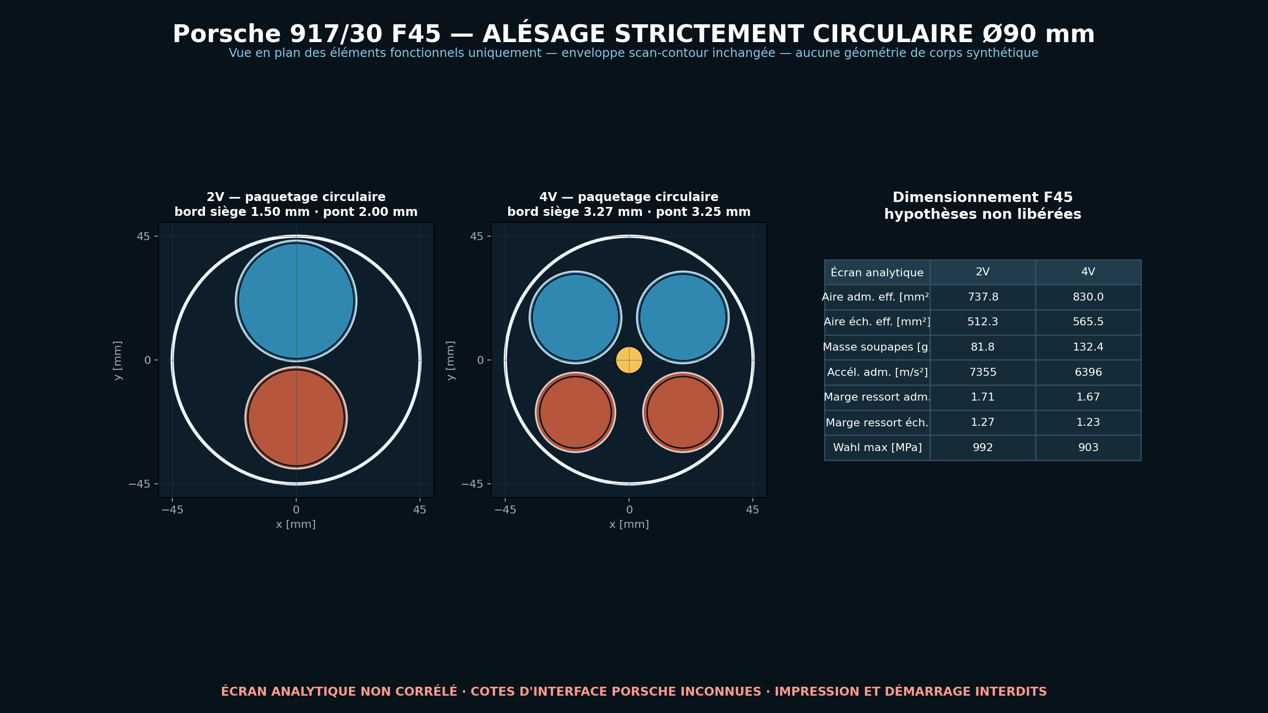
twins/reference-917-engine/evidence/f45-valvetrain/valvetrain-material-screen-f45.png
