cluster2600/porscheparts/docs/studies/993-air-oil-20261002/cad/component-01-context.stl

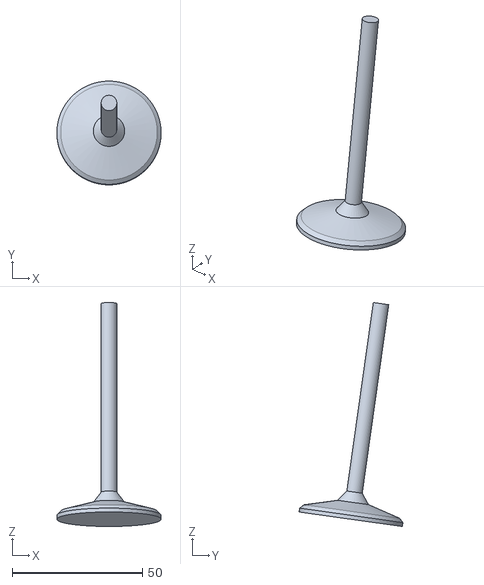
[picture p232: CAD file, 2026-10-02]
docs/studies/993-air-oil-20261002/cad/component-01-context.stl
40.0 x 39.8 x 85.9
