cluster2600/porscheparts/models/horizontal-fan-reconstruction/results/assembly/S1/geometry/support_stock_envelopes.step

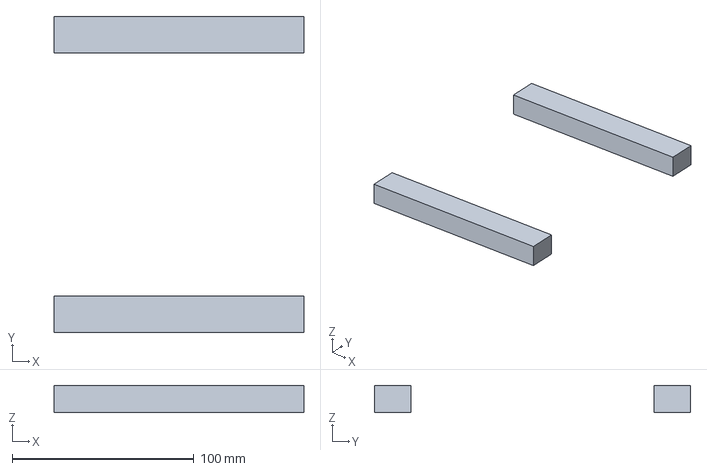
[picture p233: CAD file, 2026-10-05]
models/horizontal-fan-reconstruction/results/assembly/S1/geometry/support_stock_envelopes.step
137.5 x 174.0 x 15.0 mm
