cluster2600/porscheparts/parts/993-body-front-impact-support-alsi10mg-f0-0001/derived/front_impact_support_alsi10mg_f0-picogk.stl

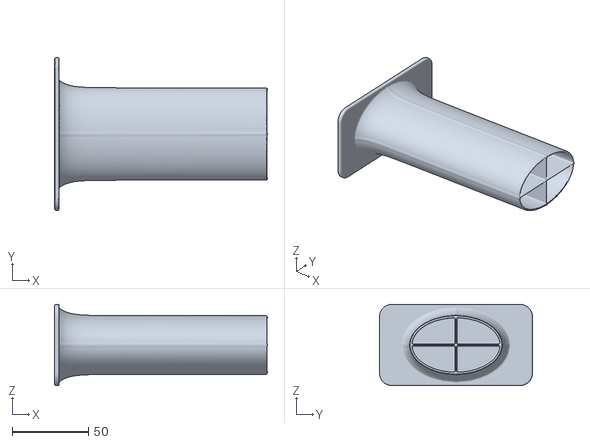
[picture p234: CAD file, 2026-10-09]
parts/993-body-front-impact-support-alsi10mg-f0-0001/derived/front_impact_support_alsi10mg_f0-picogk.stl
139.3 x 100.1 x 53.0
