cluster2600/porscheparts/parts/993-body-front-lid-0001/derived/front_lid_concept_f0-picogk.stl

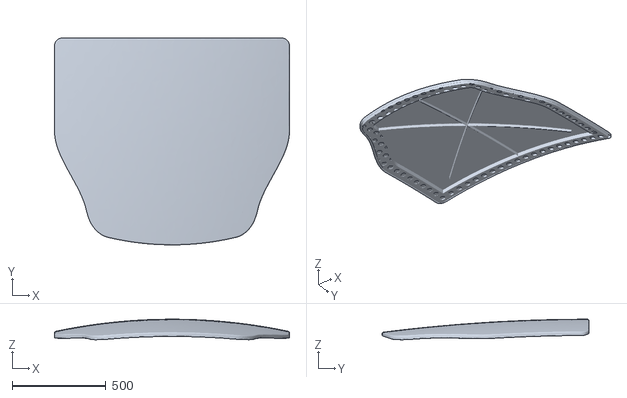
[picture p235: CAD file, 2026-10-09]
parts/993-body-front-lid-0001/derived/front_lid_concept_f0-picogk.stl
1250.3 x 1100.3 x 109.7
