cluster2600/porscheparts/parts/993-elec-headlamp-spring-hook-f0-0001/derived/headlamp_spring_hook_f0-picogk.stl

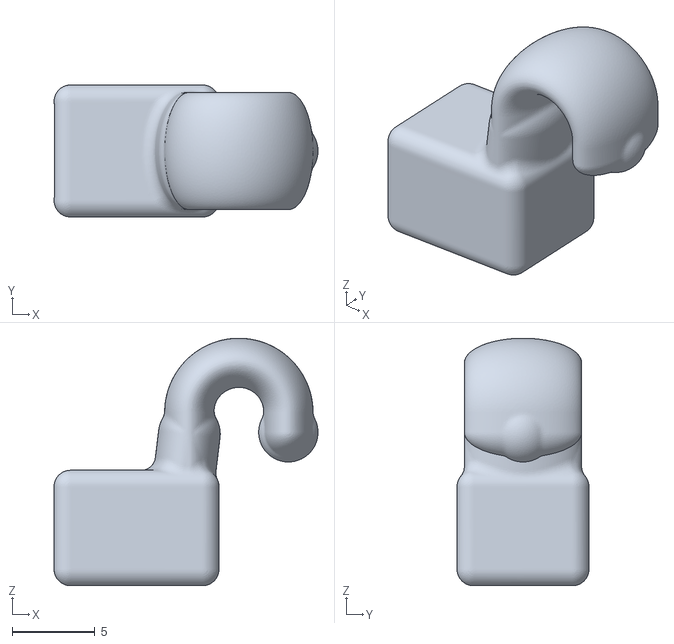
[picture p236: CAD file, 2026-10-09]
parts/993-elec-headlamp-spring-hook-f0-0001/derived/headlamp_spring_hook_f0-picogk.stl
16.0 x 8.00 x 15.0
