cluster2600/porscheparts/parts/993-eng-carrier-0001/derived/engine_carrier_concept_f0-picogk.stl

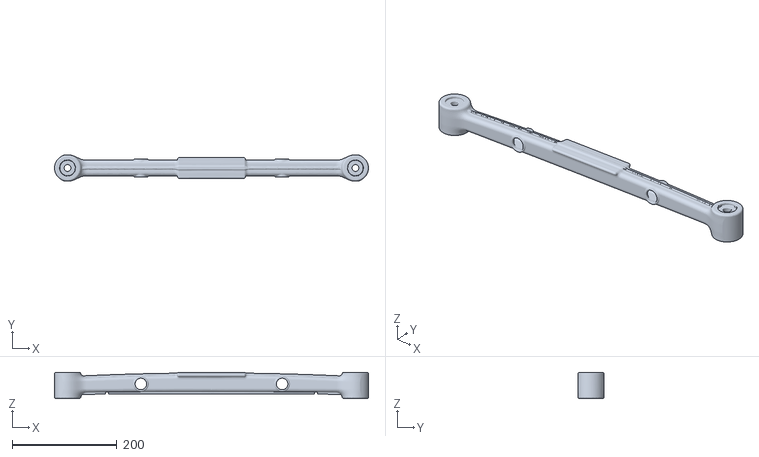
[picture p237: CAD file, 2026-10-09]
parts/993-eng-carrier-0001/derived/engine_carrier_concept_f0-picogk.stl
600.0 x 50.6 x 50.3
