cluster2600/porscheparts/parts/993-eng-carrier-0001/derived/qwen-concept-f1/carrier-concept.stl

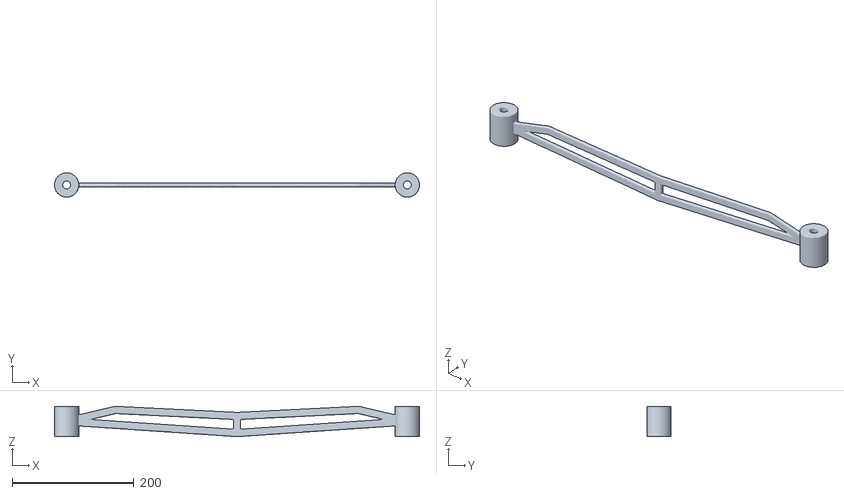
[picture p238: CAD file, 2026-10-02]
parts/993-eng-carrier-0001/derived/qwen-concept-f1/carrier-concept.stl
600.0 x 40.0 x 50.0
