cluster2600/porscheparts/parts/993-eng-chain-case-0001/derived/chain_case_concept_f0-picogk.stl

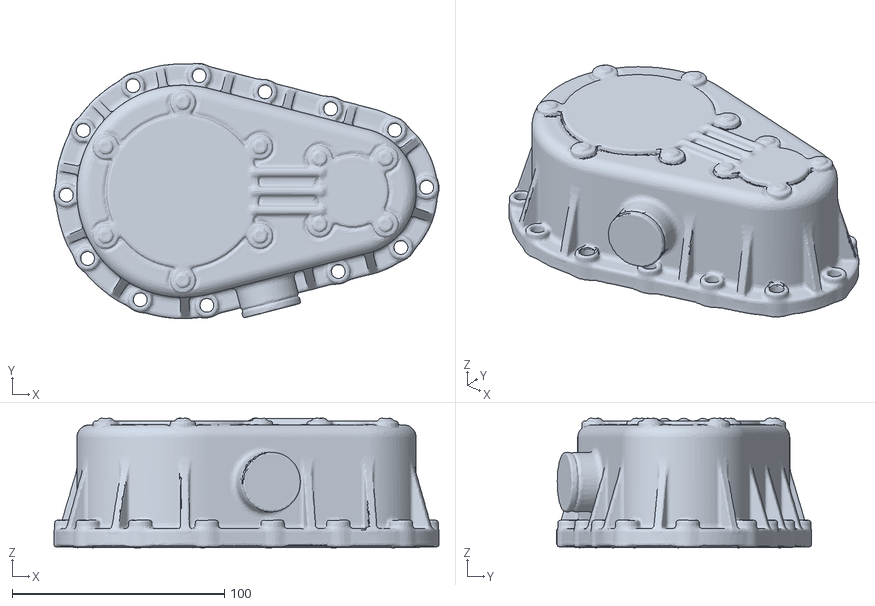
[picture p239: CAD file, 2026-10-09]
parts/993-eng-chain-case-0001/derived/chain_case_concept_f0-picogk.stl
181.5 x 120.4 x 61.1
