cluster2600/porscheparts/parts/993-eng-connecting-rod-ti64-f0-0001/derived/connecting_rod_ti64_f0-picogk.stl

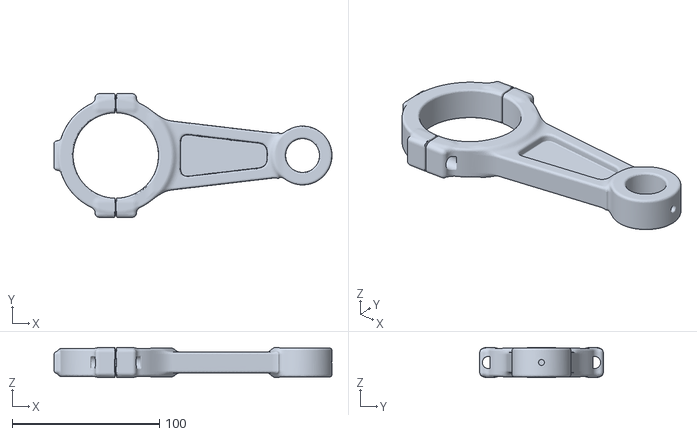
[picture p240: CAD file, 2026-10-09]
parts/993-eng-connecting-rod-ti64-f0-0001/derived/connecting_rod_ti64_f0-picogk.stl
189.0 x 84.1 x 20.4
