cluster2600/porscheparts/parts/993-eng-connecting-rod-ti64-f0-0001/print/connecting_rod_f0_mockup.step

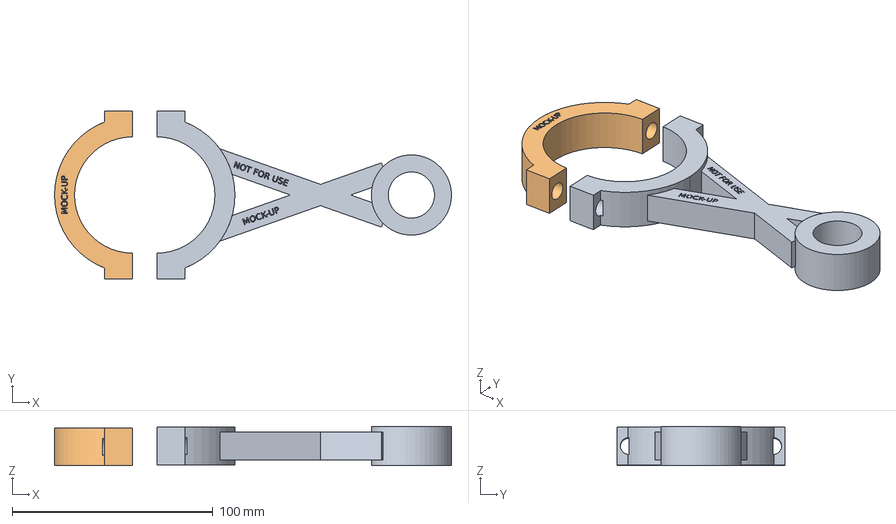
[picture p241: CAD file, 2026-09-25]
parts/993-eng-connecting-rod-ti64-f0-0001/print/connecting_rod_f0_mockup.step
198.0 x 84.0 x 19.6 mm
