cluster2600/porscheparts/parts/993-eng-cooling-impeller-alsi10mg-f0-0001/derived/cooling_impeller_alsi10mg_f0.step

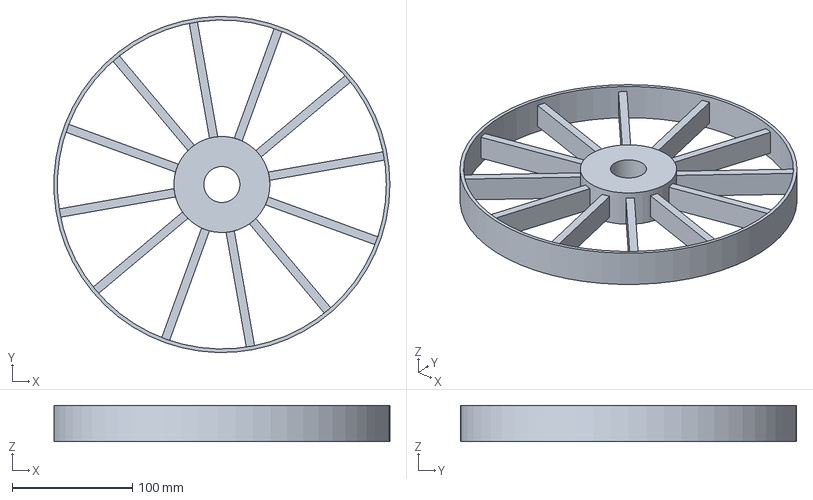
[picture p242: CAD file, 2026-09-08]
parts/993-eng-cooling-impeller-alsi10mg-f0-0001/derived/cooling_impeller_alsi10mg_f0.step
279.8 x 279.9 x 30.0 mm
