cluster2600/porscheparts/parts/993-eng-cooling-impeller-we43-f1-0001/derived/cooling_impeller_we43_f1-picogk.stl

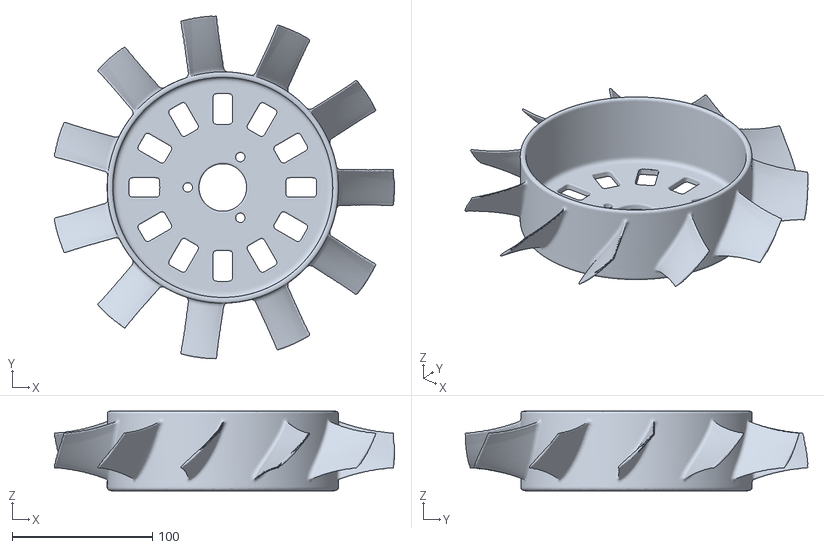
[picture p243: CAD file, 2026-10-09]
parts/993-eng-cooling-impeller-we43-f1-0001/derived/cooling_impeller_we43_f1-picogk.stl
242.8 x 244.9 x 56.9
