cluster2600/porscheparts/parts/993-eng-exhaust-manifold-in625-f0-0001/derived/exhaust_manifold_in625_f0-picogk.stl

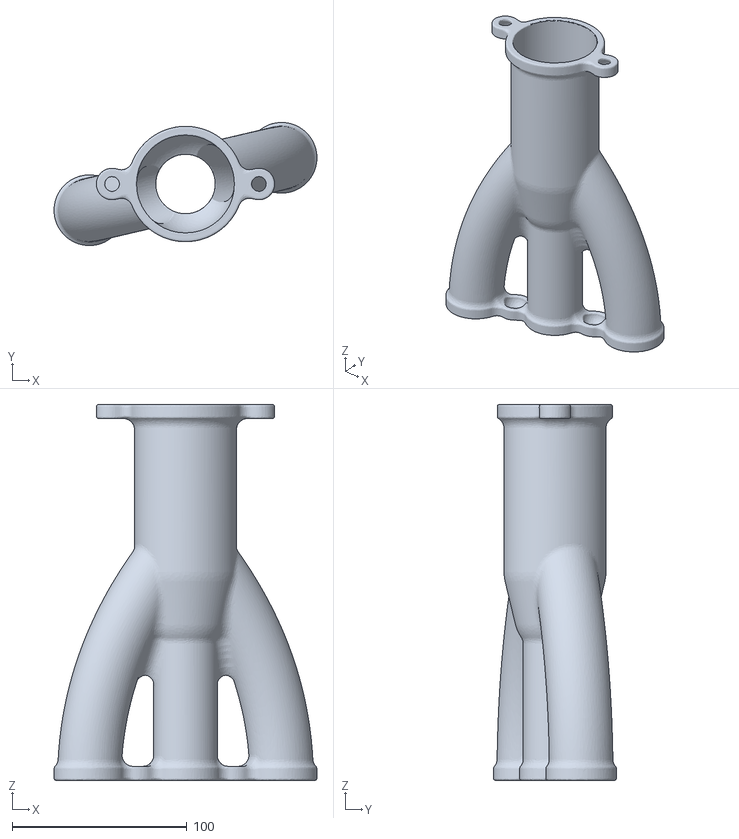
[picture p244: CAD file, 2026-10-09]
parts/993-eng-exhaust-manifold-in625-f0-0001/derived/exhaust_manifold_in625_f0-picogk.stl
150.4 x 70.4 x 215.1
