cluster2600/porscheparts/parts/993-eng-exhaust-valve-f1-0001/derived/993-carrera-exhaust-42_5-f1-picogk.stl

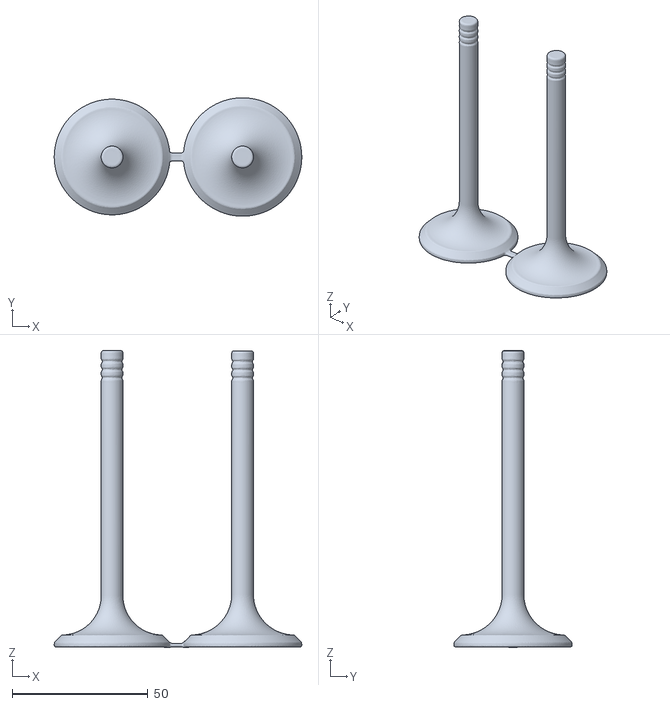
[picture p245: CAD file, 2026-10-09]
parts/993-eng-exhaust-valve-f1-0001/derived/993-carrera-exhaust-42_5-f1-picogk.stl
91.1 x 43.6 x 109.2
