cluster2600/porscheparts/parts/993-eng-fan-housing-alsi10mg-f0-0001/derived/fan_housing_alsi10mg_f0-picogk.stl

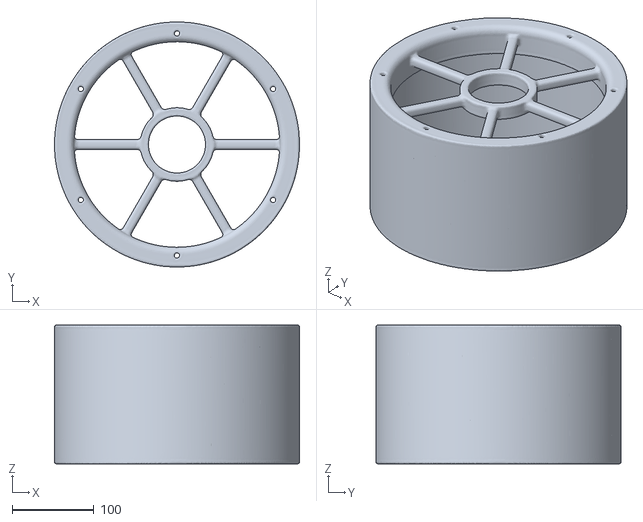
[picture p246: CAD file, 2026-10-09]
parts/993-eng-fan-housing-alsi10mg-f0-0001/derived/fan_housing_alsi10mg_f0-picogk.stl
300.2 x 300.2 x 170.3
