cluster2600/porscheparts/parts/993-eng-fan-stator-alsi10mg-f1-0001/derived/fan_stator_alsi10mg_f1-picogk.stl

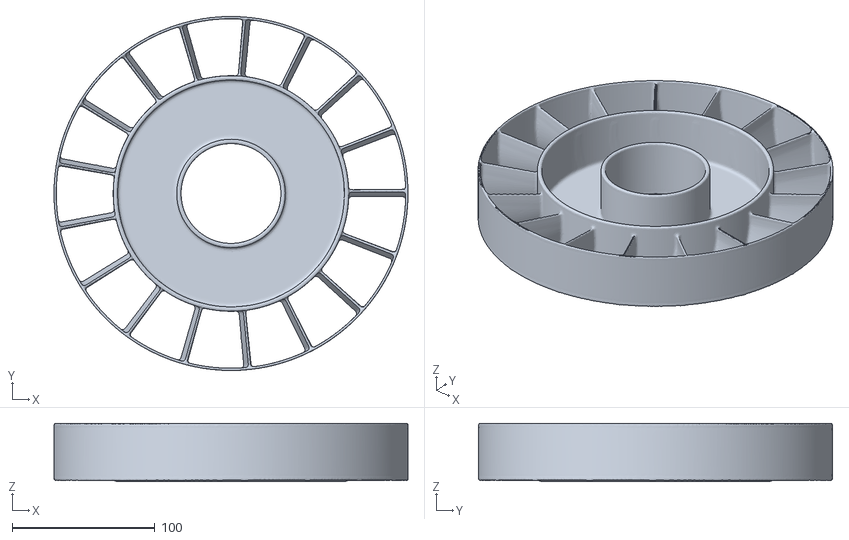
[picture p247: CAD file, 2026-10-09]
parts/993-eng-fan-stator-alsi10mg-f1-0001/derived/fan_stator_alsi10mg_f1-picogk.stl
248.1 x 248.1 x 40.9
