cluster2600/porscheparts/parts/993-eng-intake-valve-f1-0001/derived/993-intake-49-f1-picogk.stl

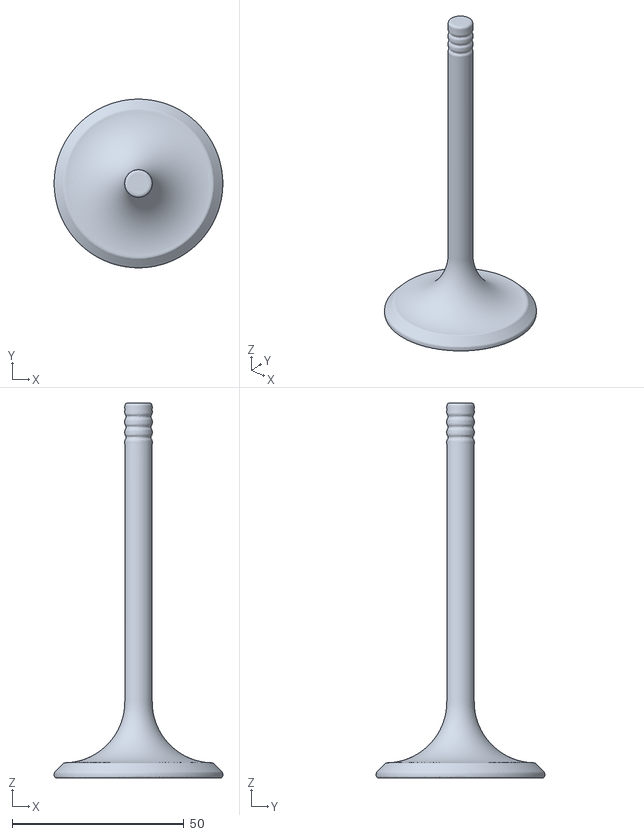
[picture p248: CAD file, 2026-10-09]
parts/993-eng-intake-valve-f1-0001/derived/993-intake-49-f1-picogk.stl
49.1 x 49.1 x 109.0
