cluster2600/porscheparts/parts/993-eng-intake-valve-ti64-hollow-f0-0001/derived/intake_valve_ti64_hollow_f0-picogk.stl

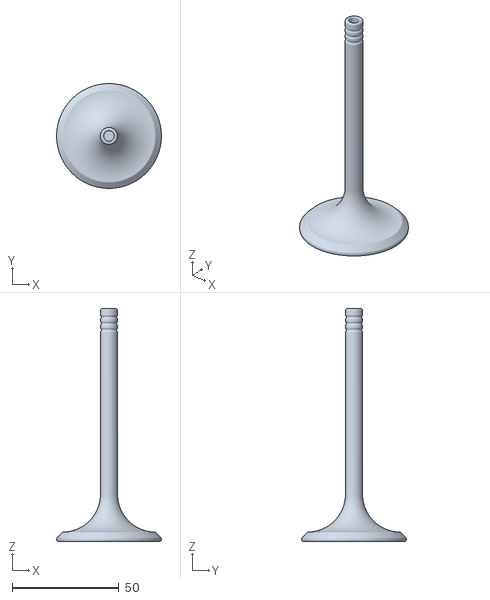
[picture p249: CAD file, 2026-10-09]
parts/993-eng-intake-valve-ti64-hollow-f0-0001/derived/intake_valve_ti64_hollow_f0-picogk.stl
49.1 x 49.1 x 109.1
