cluster2600/porscheparts/parts/993-eng-intercooler-bracket-ti-f0-0001/derived/intercooler_bracket_ti_f0-picogk.stl

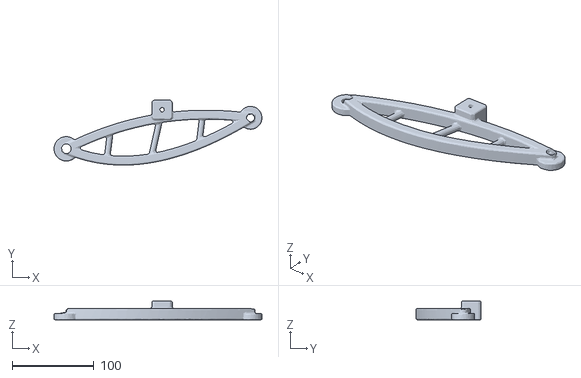
[picture p250: CAD file, 2026-10-09]
parts/993-eng-intercooler-bracket-ti-f0-0001/derived/intercooler_bracket_ti_f0-picogk.stl
255.1 x 79.9 x 23.0
