cluster2600/porscheparts/parts/993-eng-intercooler-end-tank-alsi10mg-f0-0001/derived/end_tank_alsi10mg_f0-picogk.stl

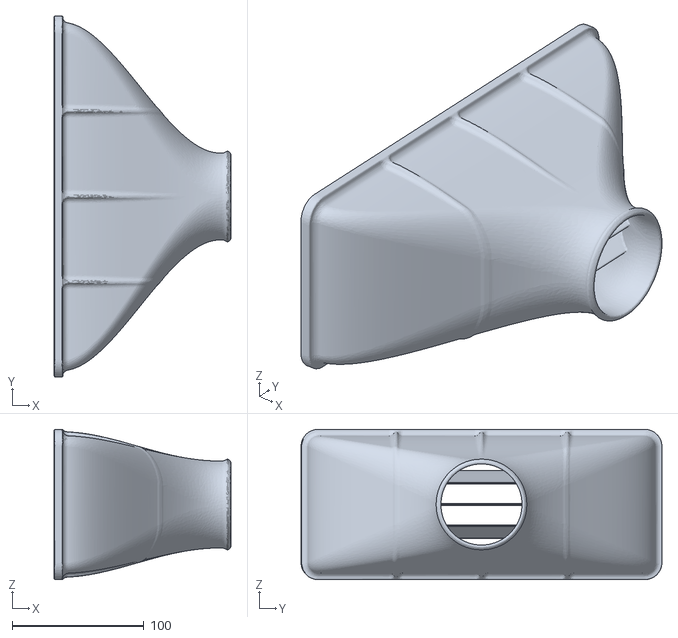
[picture p251: CAD file, 2026-10-09]
parts/993-eng-intercooler-end-tank-alsi10mg-f0-0001/derived/end_tank_alsi10mg_f0-picogk.stl
134.1 x 274.1 x 114.1
