cluster2600/porscheparts/parts/993-eng-k16-compressor-wheel-al2139-f1-0001/derived/compressor_wheel_al2139_f1-picogk.stl

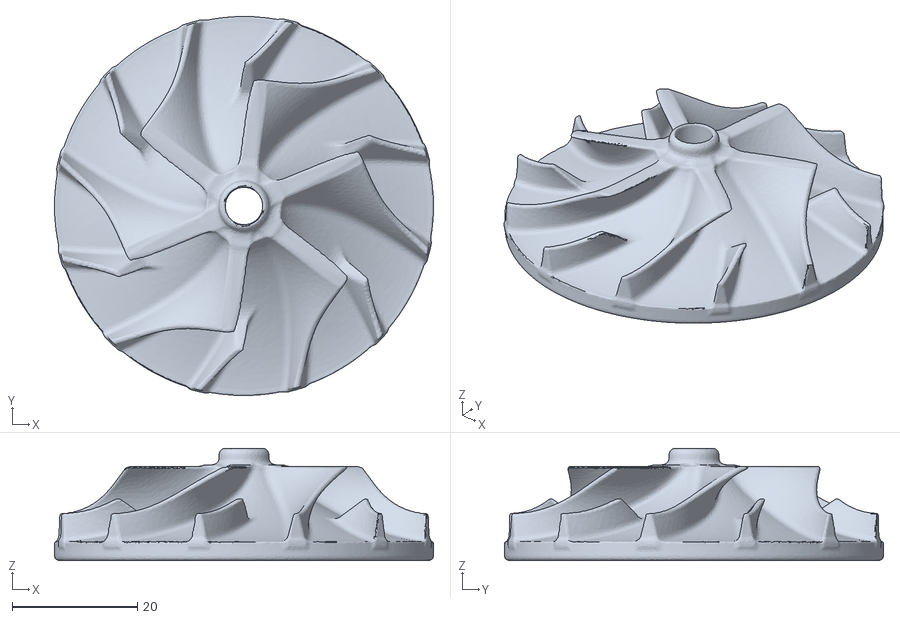
[picture p252: CAD file, 2026-10-09]
parts/993-eng-k16-compressor-wheel-al2139-f1-0001/derived/compressor_wheel_al2139_f1-picogk.stl
60.5 x 60.5 x 17.9
