cluster2600/porscheparts/parts/993-eng-k16-compressor-wheel-al2139-f1-0001/print/k16_compressor_wheel_mockup.stl

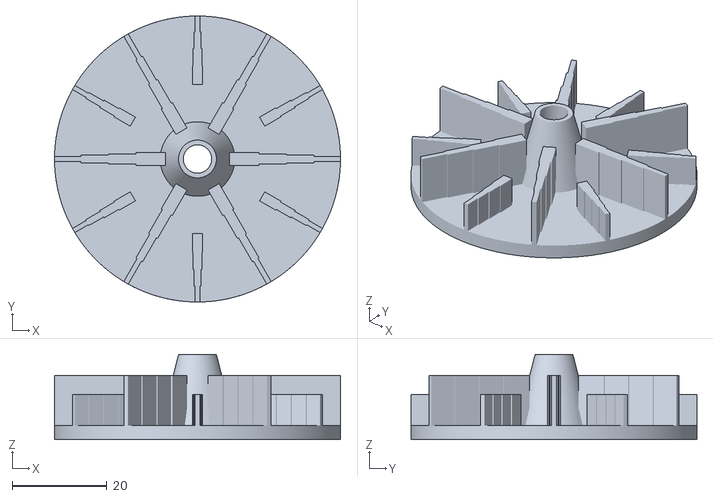
[picture p253: CAD file, 2026-09-25]
parts/993-eng-k16-compressor-wheel-al2139-f1-0001/print/k16_compressor_wheel_mockup.stl
60.5 x 60.5 x 18.0
