cluster2600/porscheparts/parts/993-eng-k16-compressor-wheel-alsi10mg-f0-0001/derived/compressor_wheel_alsi10mg_f0-picogk.stl

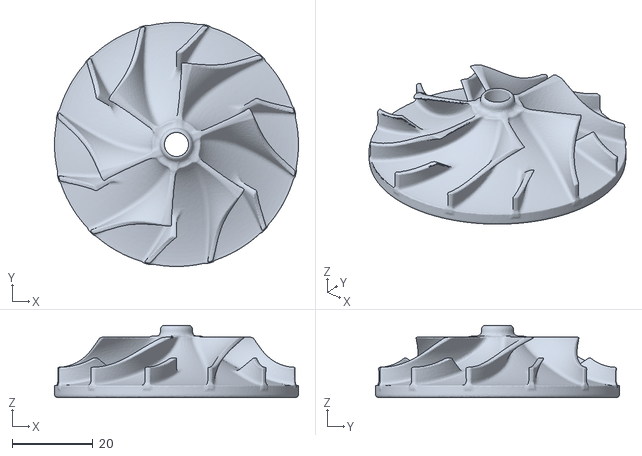
[picture p254: CAD file, 2026-10-09]
parts/993-eng-k16-compressor-wheel-alsi10mg-f0-0001/derived/compressor_wheel_alsi10mg_f0-picogk.stl
60.5 x 60.5 x 17.9
