cluster2600/porscheparts/parts/993-eng-k16-turbine-wheel-in718-f0-0001/derived/turbine_wheel_in718_f0-picogk.stl

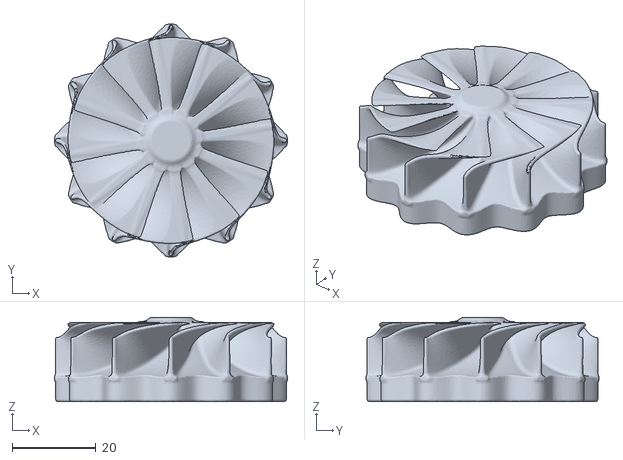
[picture p255: CAD file, 2026-10-09]
parts/993-eng-k16-turbine-wheel-in718-f0-0001/derived/turbine_wheel_in718_f0-picogk.stl
55.5 x 55.5 x 20.0
