cluster2600/porscheparts/parts/993-eng-k16-turbine-wheel-in718-f0-0001/print/k16_turbine_wheel_mockup.stl

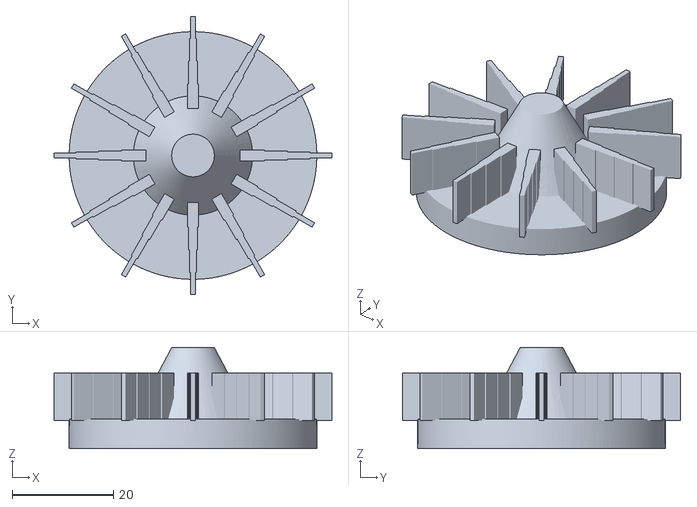
[picture p256: CAD file, 2026-09-25]
parts/993-eng-k16-turbine-wheel-in718-f0-0001/print/k16_turbine_wheel_mockup.stl
55.0 x 55.0 x 20.0
