cluster2600/porscheparts/parts/993-eng-oil-filter-console-alsi10mg-f0-0001/derived/oil_filter_console_alsi10mg_f0-picogk.stl

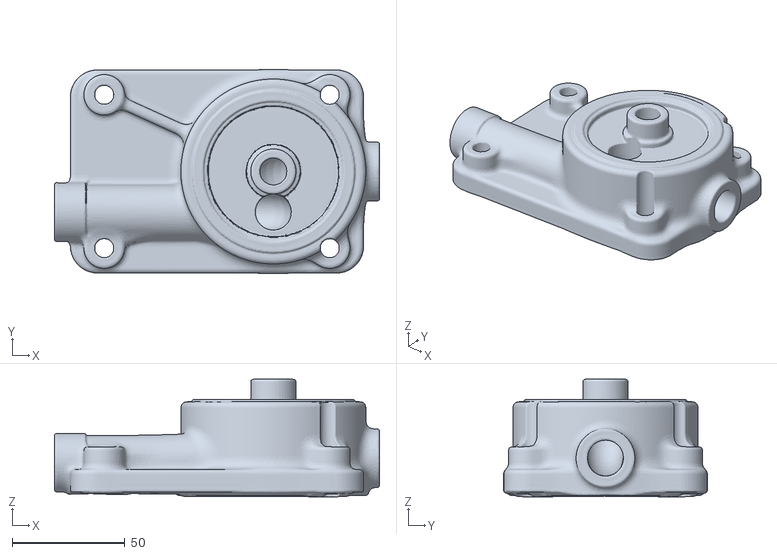
[picture p257: CAD file, 2026-10-09]
parts/993-eng-oil-filter-console-alsi10mg-f0-0001/derived/oil_filter_console_alsi10mg_f0-picogk.stl
144.1 x 90.4 x 52.2
