cluster2600/porscheparts/parts/993-eng-piston-cp1-gallery-f0-0001/derived/piston_cp1_gallery_f0-picogk.stl

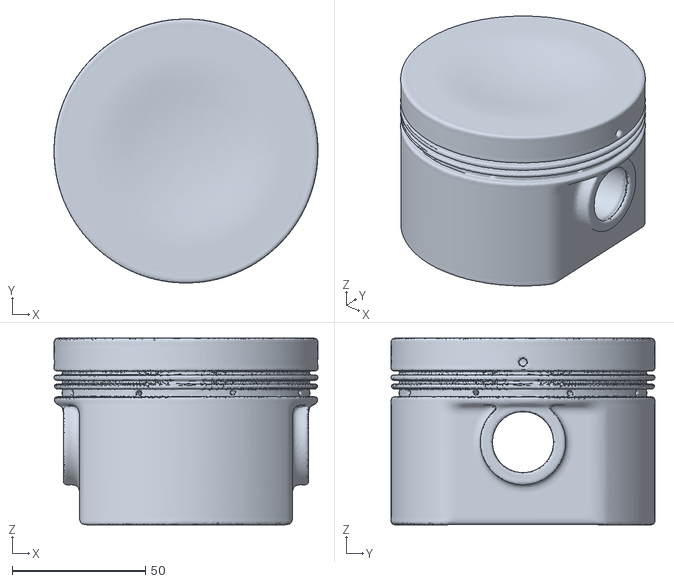
[picture p258: CAD file, 2026-10-09]
parts/993-eng-piston-cp1-gallery-f0-0001/derived/piston_cp1_gallery_f0-picogk.stl
99.1 x 99.1 x 70.1
