cluster2600/porscheparts/parts/993-eng-three-runner-intake-alsi10mg-f0-0001/derived/three_runner_intake_alsi10mg_f0-picogk.stl

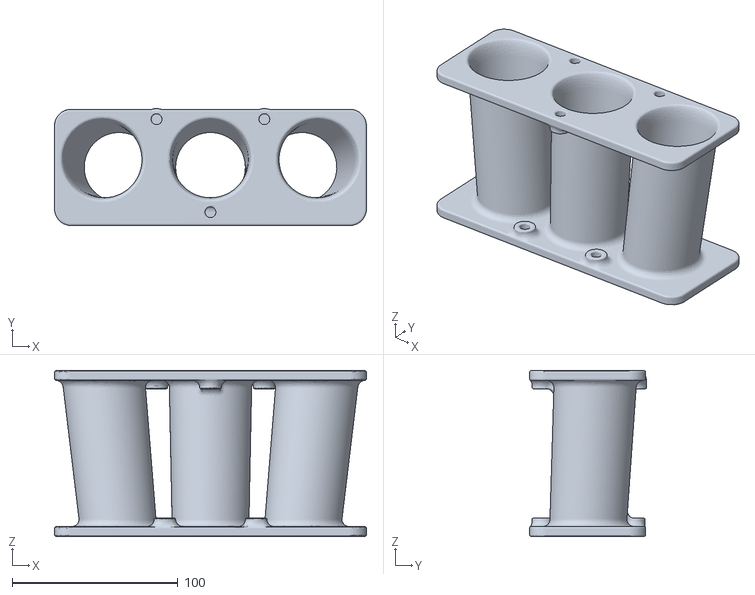
[picture p259: CAD file, 2026-10-09]
parts/993-eng-three-runner-intake-alsi10mg-f0-0001/derived/three_runner_intake_alsi10mg_f0-picogk.stl
188.0 x 70.5 x 100.1
