cluster2600/porscheparts/parts/993-eng-turbo-heat-shield-in625-f0-0001/derived/turbo_heat_shield_in625_f0-picogk.stl

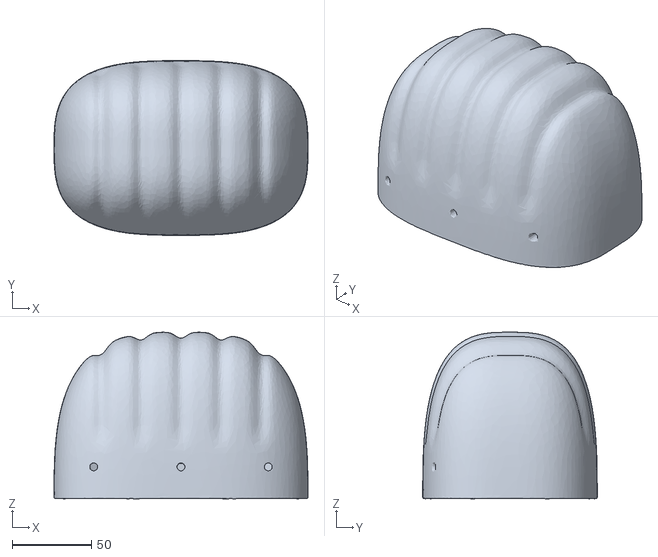
[picture p260: CAD file, 2026-10-09]
parts/993-eng-turbo-heat-shield-in625-f0-0001/derived/turbo_heat_shield_in625_f0-picogk.stl
160.0 x 110.1 x 105.0
