cluster2600/porscheparts/parts/993-eng-turbo-oil-return-line-in625-f0-0001/derived/turbo_oil_return_line_in625_f0-picogk.stl

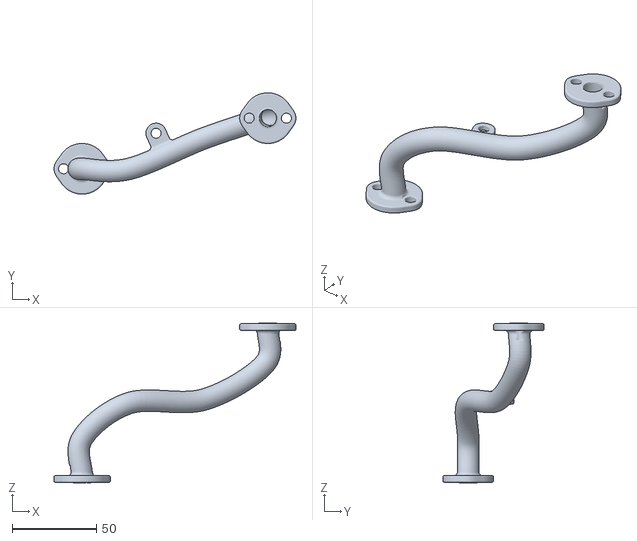
[picture p261: CAD file, 2026-10-09]
parts/993-eng-turbo-oil-return-line-in625-f0-0001/derived/turbo_oil_return_line_in625_f0-picogk.stl
143.4 x 60.0 x 94.6
