cluster2600/porscheparts/parts/993-eng-upper-valve-cover-alsi10mg-f0-0001/derived/upper_valve_cover_alsi10mg_f0-picogk.stl

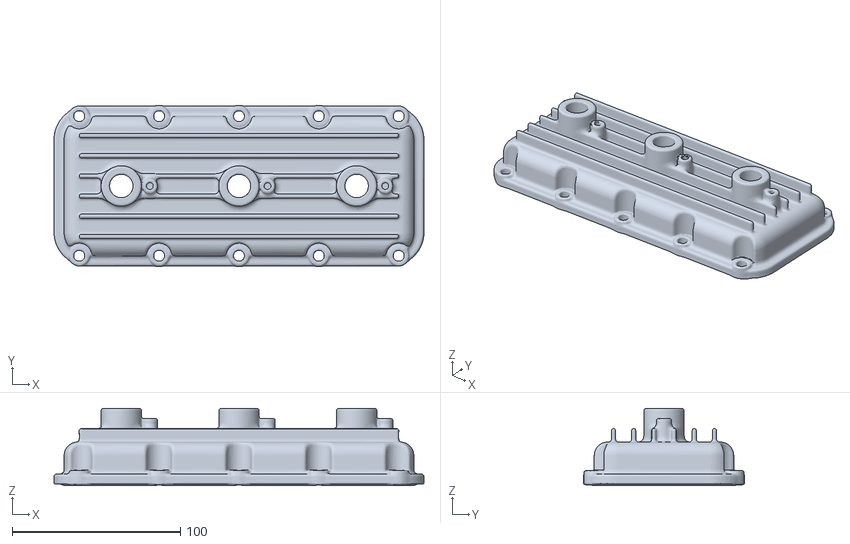
[picture p262: CAD file, 2026-10-09]
parts/993-eng-upper-valve-cover-alsi10mg-f0-0001/derived/upper_valve_cover_alsi10mg_f0-picogk.stl
220.1 x 95.8 x 46.0
