cluster2600/porscheparts/parts/993-exh-oval-tip-in625-f0-0001/derived/oval_exhaust_tip_in625_f0-picogk.stl

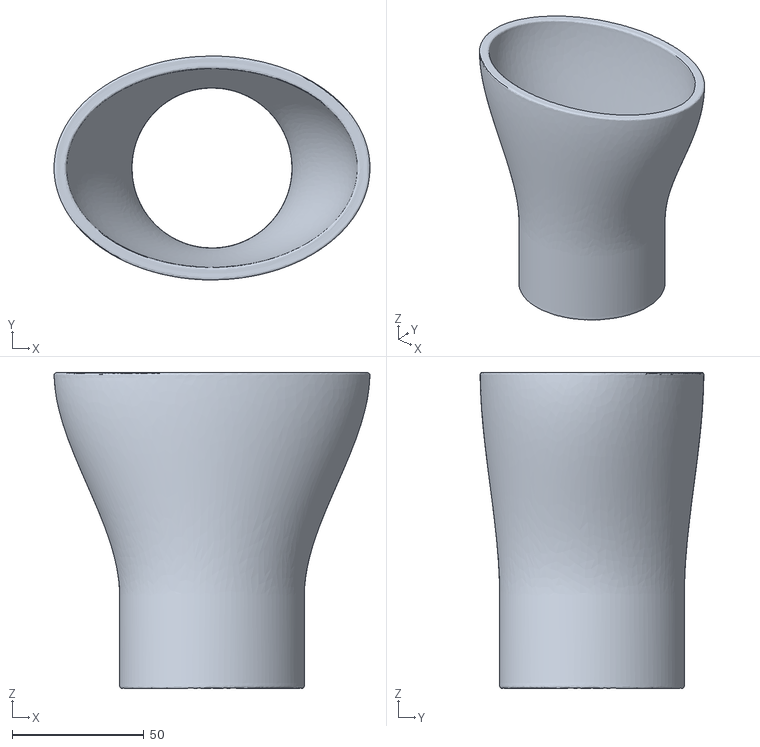
[picture p263: CAD file, 2026-10-09]
parts/993-exh-oval-tip-in625-f0-0001/derived/oval_exhaust_tip_in625_f0-picogk.stl
120.1 x 85.1 x 120.1
