cluster2600/porscheparts/parts/993-int-dashboard-trim-0001/derived/dashboard_trim_concept_f0-picogk.stl

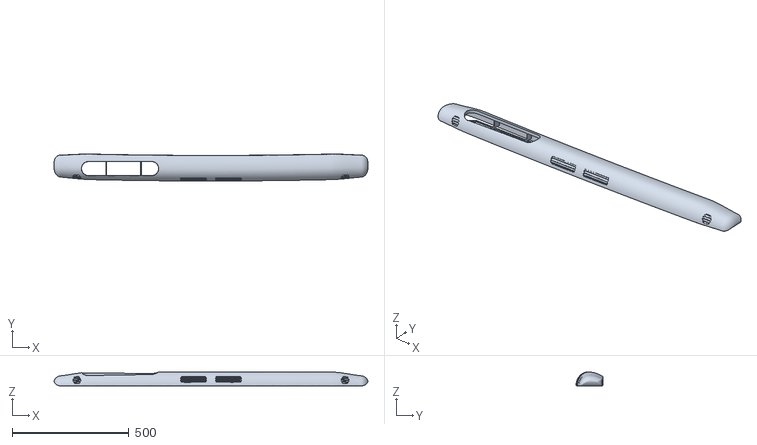
[picture p264: CAD file, 2026-10-09]
parts/993-int-dashboard-trim-0001/derived/dashboard_trim_concept_f0-picogk.stl
1346.7 x 115.7 x 60.2
