cluster2600/porscheparts/parts/993-int-door-opener-lever-f0-0001/derived/door_opener_lever_f0-picogk.stl

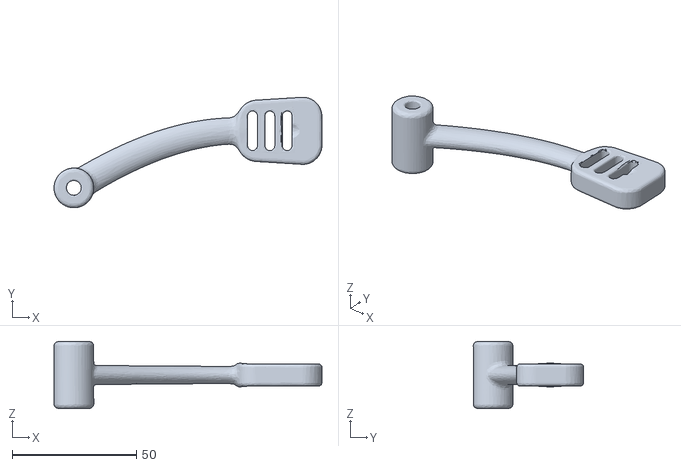
[picture p265: CAD file, 2026-10-09]
parts/993-int-door-opener-lever-f0-0001/derived/door_opener_lever_f0-picogk.stl
108.0 x 44.5 x 27.1
