cluster2600/porscheparts/parts/993-int-door-pull-0001/derived/door_pull_concept_f0-picogk.stl

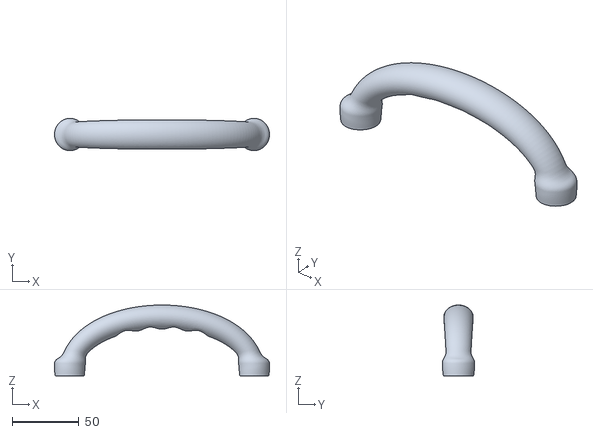
[picture p266: CAD file, 2026-10-09]
parts/993-int-door-pull-0001/derived/door_pull_concept_f0-picogk.stl
160.7 x 24.1 x 53.0
