cluster2600/porscheparts/parts/993-int-seat-rail-cover-0001/derived/seat_rail_cover_concept_f0-picogk.stl

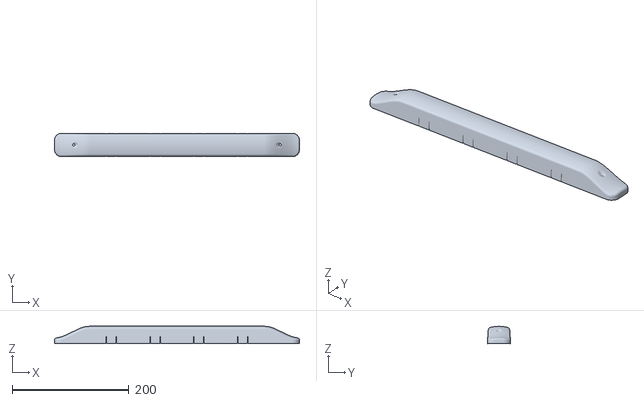
[picture p267: CAD file, 2026-10-09]
parts/993-int-seat-rail-cover-0001/derived/seat_rail_cover_concept_f0-picogk.stl
420.0 x 40.0 x 30.0
