cluster2600/porscheparts/parts/993-int-switch-blank-0001/derived/switch_blank_concept_f0-picogk.stl

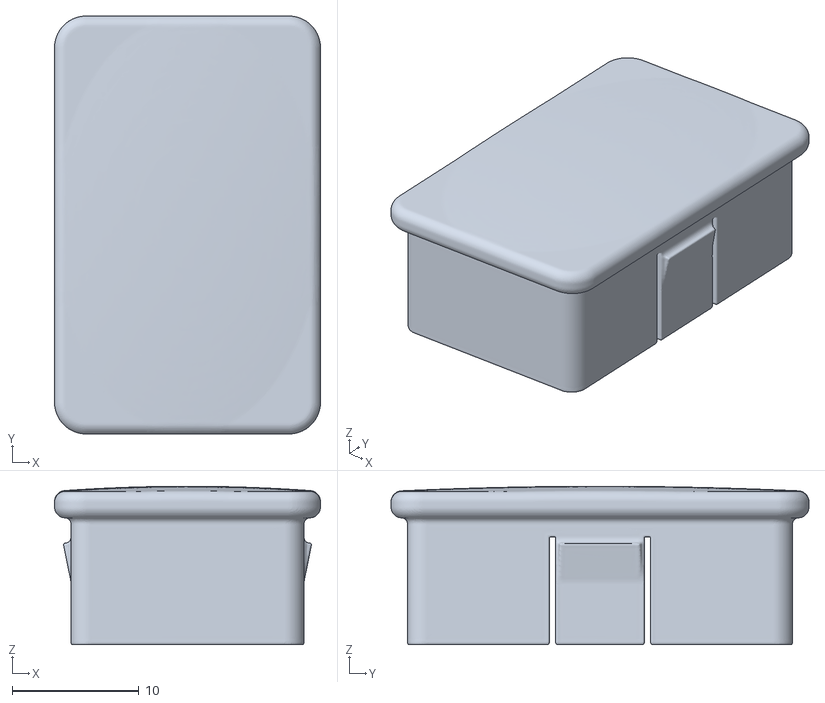
[picture p268: CAD file, 2026-10-09]
parts/993-int-switch-blank-0001/derived/switch_blank_concept_f0-picogk.stl
21.0 x 33.0 x 12.5
