cluster2600/porscheparts/parts/993-int-switch-blank-0001/print/switch_blank_fit_3.stl

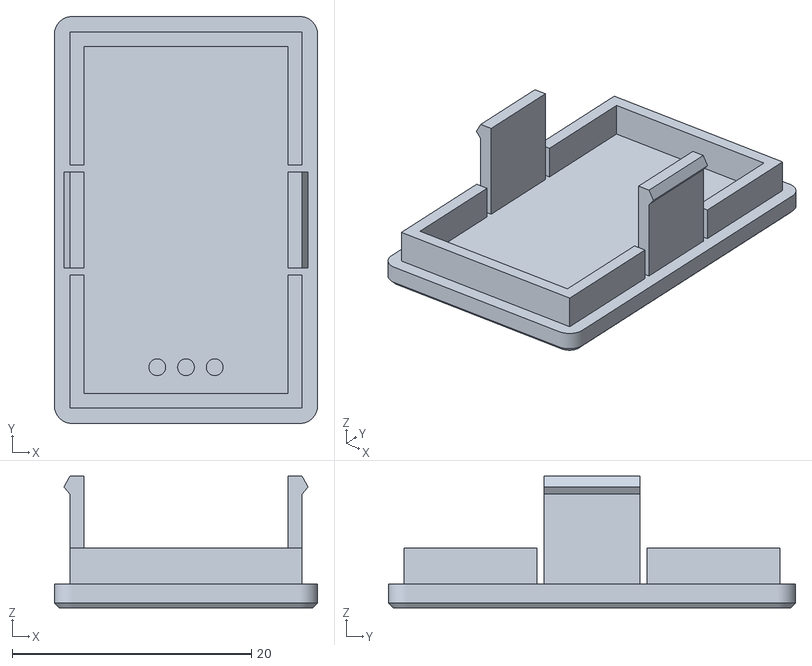
[picture p269: CAD file, 2026-09-25]
parts/993-int-switch-blank-0001/print/switch_blank_fit_3.stl
22.0 x 34.0 x 11.0
