cluster2600/porscheparts/parts/993-int-switch-trim-ring-f1-0001/derived/switch_trim_ring_f1-picogk.stl

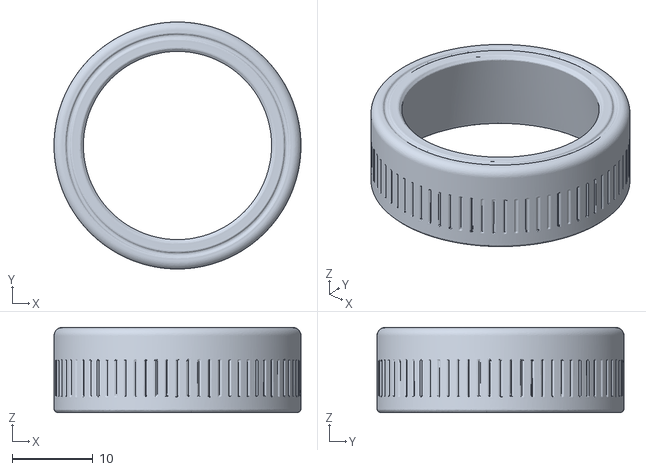
[picture p270: CAD file, 2026-10-09]
parts/993-int-switch-trim-ring-f1-0001/derived/switch_trim_ring_f1-picogk.stl
30.5 x 30.5 x 10.5
