cluster2600/porscheparts/parts/993-int-switch-trim-ring-f1-0001/print/switch_trim_ring_f1.3mf

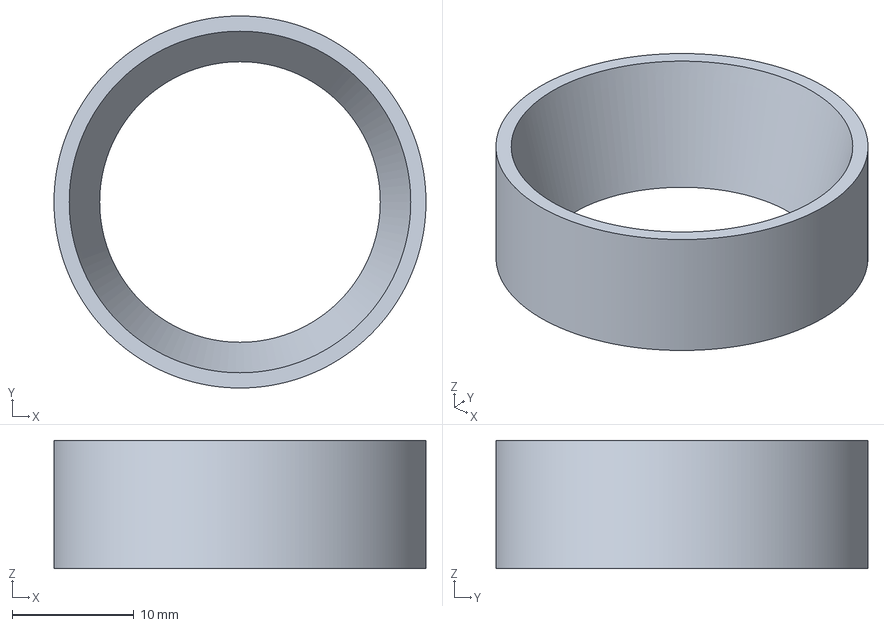
[picture p271: CAD file, 2026-09-25]
parts/993-int-switch-trim-ring-f1-0001/print/switch_trim_ring_f1.3mf
30.5 x 30.5 x 10.5 mm
