cluster2600/porscheparts/parts/993-turbocharger-k16-pair-0001/derived/k16_pair_concept_f0-picogk.stl

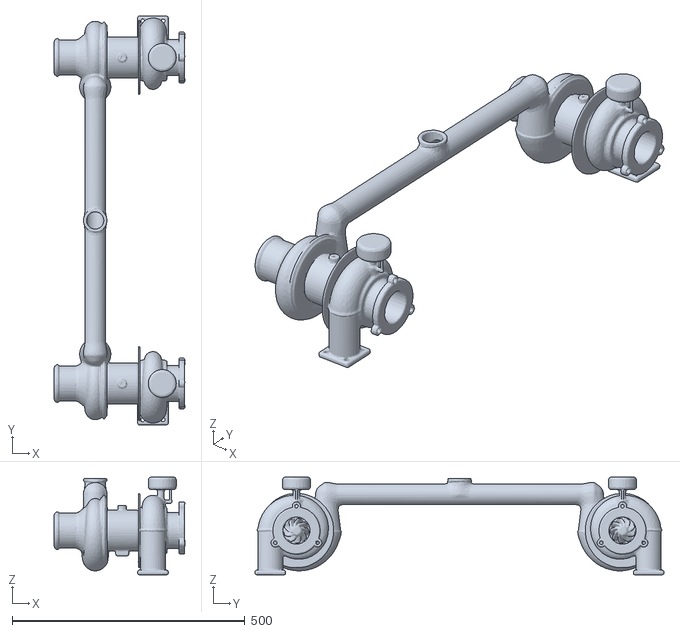
[picture p272: CAD file, 2026-10-09]
parts/993-turbocharger-k16-pair-0001/derived/k16_pair_concept_f0-picogk.stl
280.8 x 878.0 x 210.3
