cluster2600/porscheparts/parts/993-whl-center-cap-alsi10mg-f0-0001/derived/wheel_center_cap_alsi10mg_f0-picogk.stl

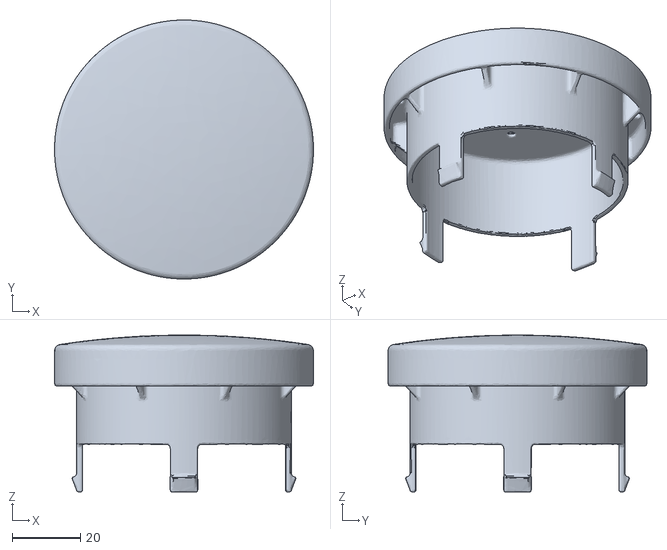
[picture p273: CAD file, 2026-10-09]
parts/993-whl-center-cap-alsi10mg-f0-0001/derived/wheel_center_cap_alsi10mg_f0-picogk.stl
76.0 x 76.0 x 46.0
