cluster2600/porscheparts/parts/m64-cooling-fan-0001/export/derived/m64-cooling-fan.step

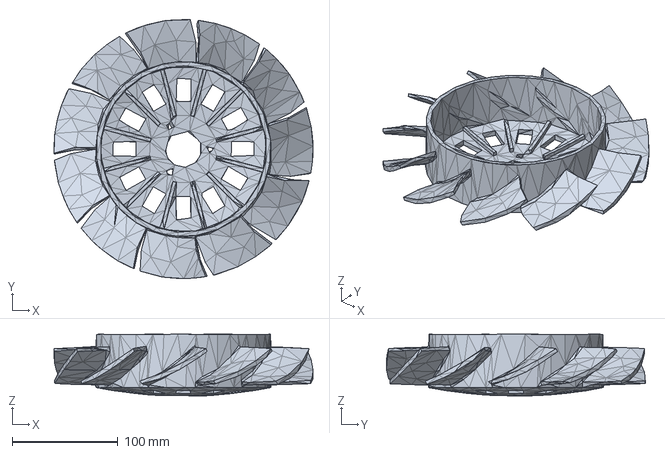
[picture p274: CAD file, 2026-09-29]
parts/m64-cooling-fan-0001/export/derived/m64-cooling-fan.step
244.9 x 245.1 x 58.5 mm
