cluster2600/porscheparts/parts/m64-cylinder-head-0001/export/m64-cylinder-head.step

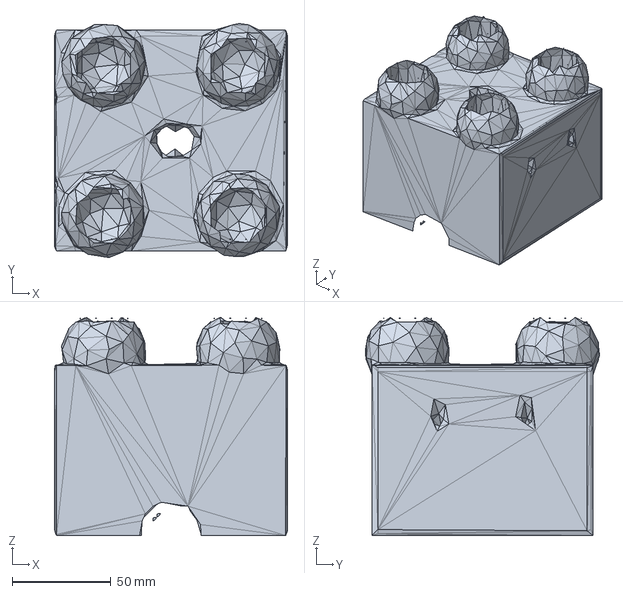
[picture p275: CAD file, 2026-09-29]
parts/m64-cylinder-head-0001/export/m64-cylinder-head.step
118.0 x 118.5 x 110.6 mm
