cluster2600/porscheparts/parts/m64-valvetrain-0001/validation/run/camshaft-parametric-proxy.stl

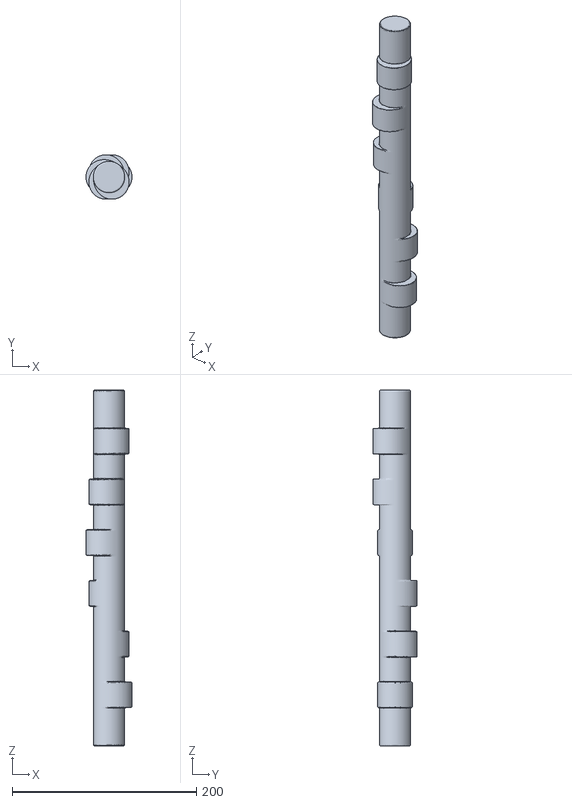
[picture p276: CAD file, 2026-09-29]
parts/m64-valvetrain-0001/validation/run/camshaft-parametric-proxy.stl
50.0 x 48.2 x 386.0
