cluster2600/porscheparts/twins/964-chassis/monocoque/derived/monocoque-shell.ply

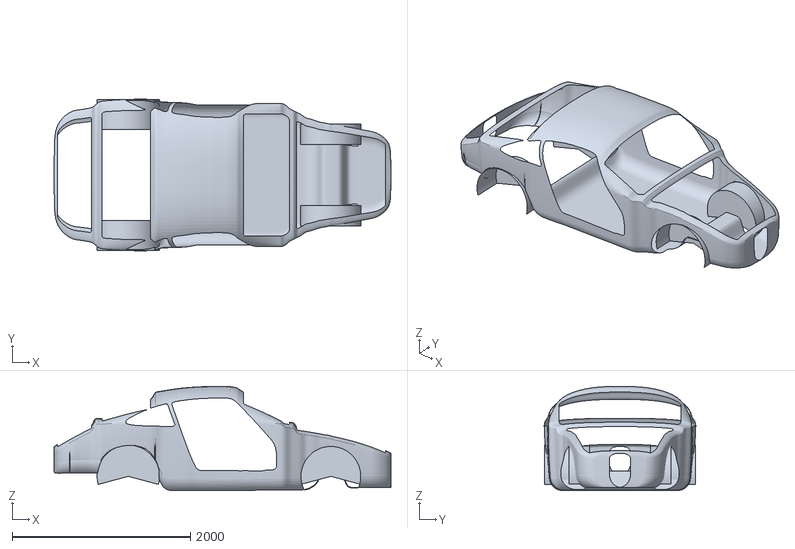
[picture p277: CAD file, 2026-10-08]
twins/964-chassis/monocoque/derived/monocoque-shell.ply
3780.0 x 1699.6 x 1168.9
