cluster2600/porscheparts/twins/m64-cylinder-head/evidence/four-valve-design-v2-20260907/closed.step

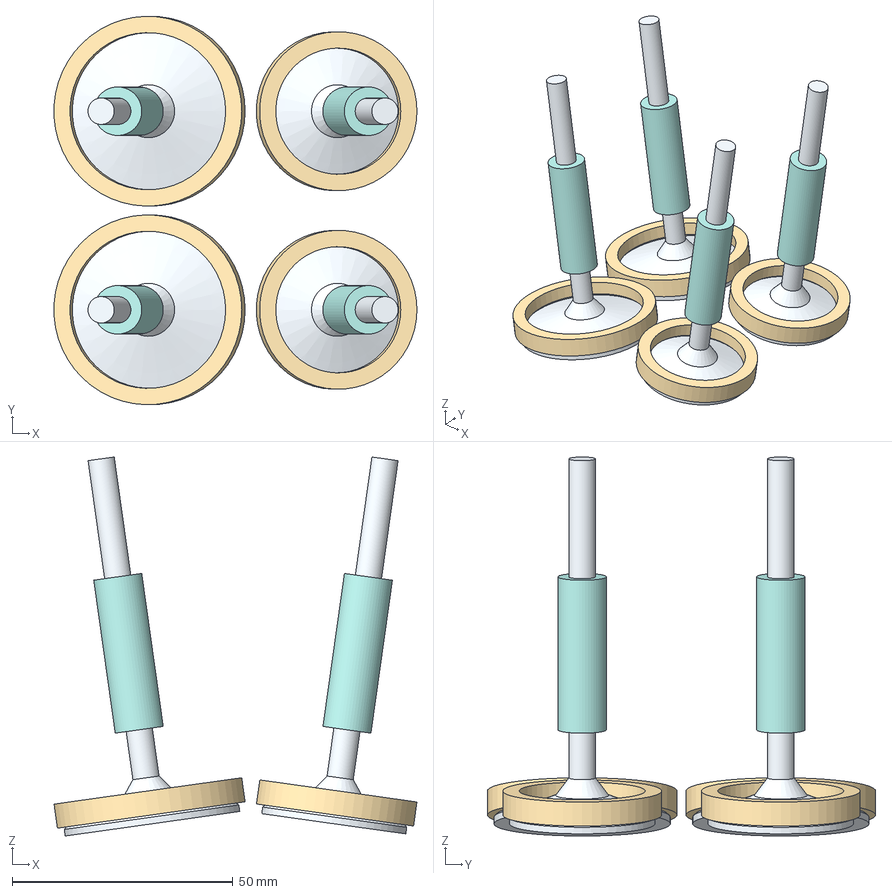
[picture p279: CAD file, 2026-09-14]
twins/m64-cylinder-head/evidence/four-valve-design-v2-20260907/closed.step
82.2 x 88.0 x 85.9 mm
intake_1_valve
intake_1_seat
intake_1_guide
intake_2_valve
intake_2_seat
intake_2_guide
exhaust_1_valve
exhaust_1_seat
exhaust_1_guide
exhaust_2_valve
exhaust_2_seat
exhaust_2_guide
