cluster2600/porscheparts/twins/m64-cylinder-head/evidence/g1-parametric-20260914/m64-head-skeleton.step

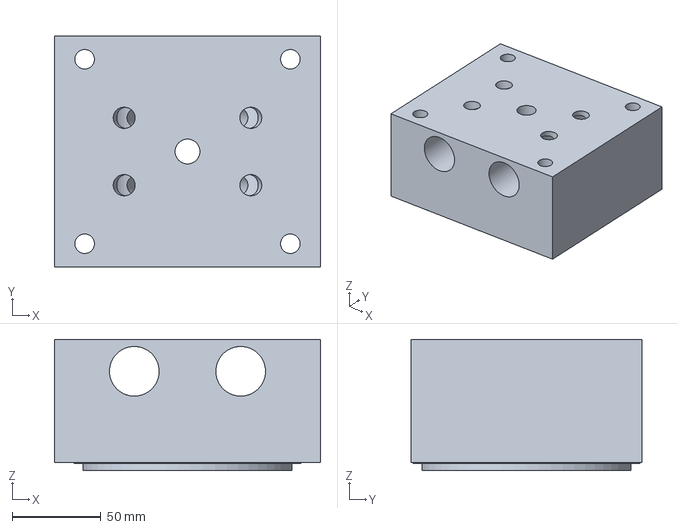
[picture p280: CAD file, 2026-09-14]
twins/m64-cylinder-head/evidence/g1-parametric-20260914/m64-head-skeleton.step
150.0 x 130.0 x 74.0 mm
