cluster2600/porscheparts/twins/m64-cylinder-head/evidence/g2-head-features-20260916/twin-spring_gsc5092.step

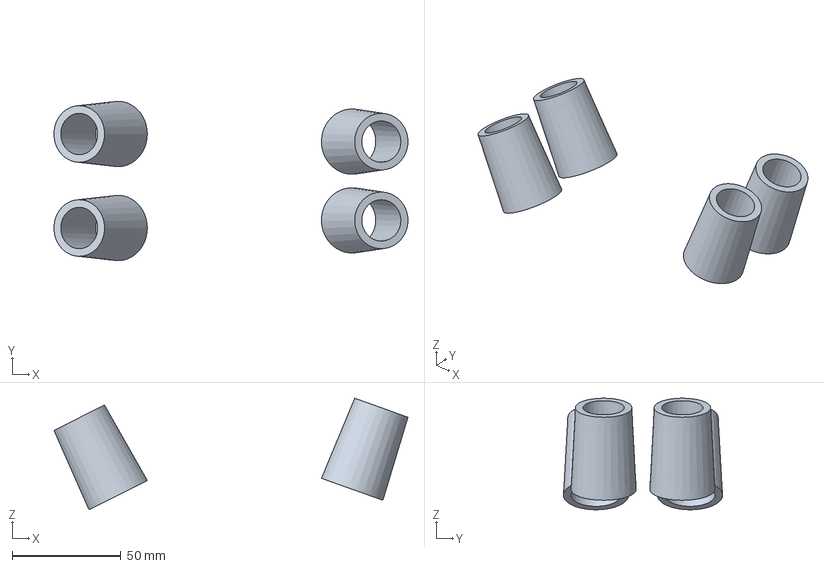
[picture p281: CAD file, 2026-09-16]
twins/m64-cylinder-head/evidence/g2-head-features-20260916/twin-spring_gsc5092.step
162.6 x 73.2 x 51.2 mm
