cluster2600/porscheparts/twins/m64-cylinder-head/evidence/g2-spark-plug-packaging-20260924/spark-plug-envelopes.step

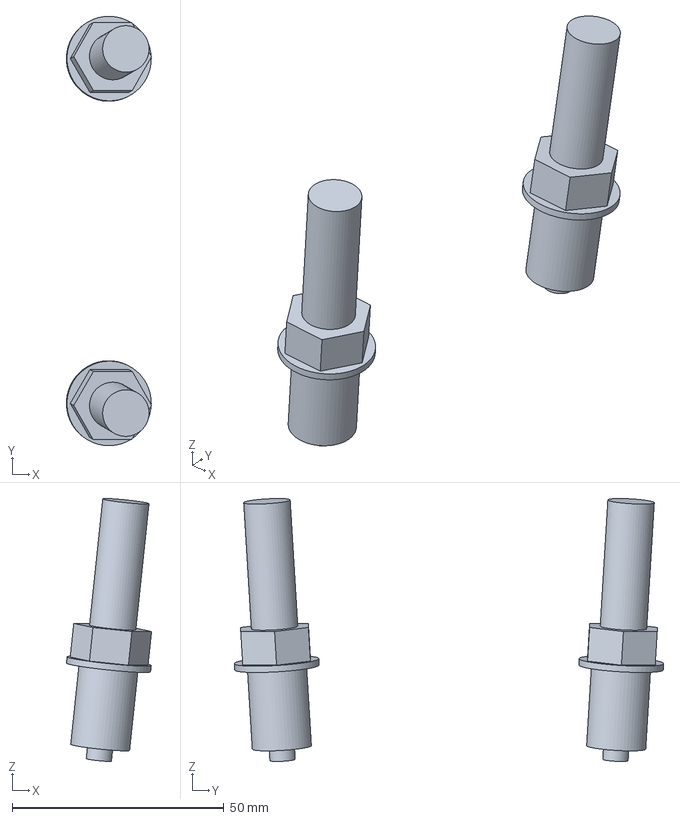
[picture p282: CAD file, 2026-09-25]
twins/m64-cylinder-head/evidence/g2-spark-plug-packaging-20260924/spark-plug-envelopes.step
20.1 x 101.3 x 62.1 mm
