cluster2600/porscheparts/twins/m64-cylinder-head/evidence/g3-seat-contact-20260925/four-valves-and-seats.step

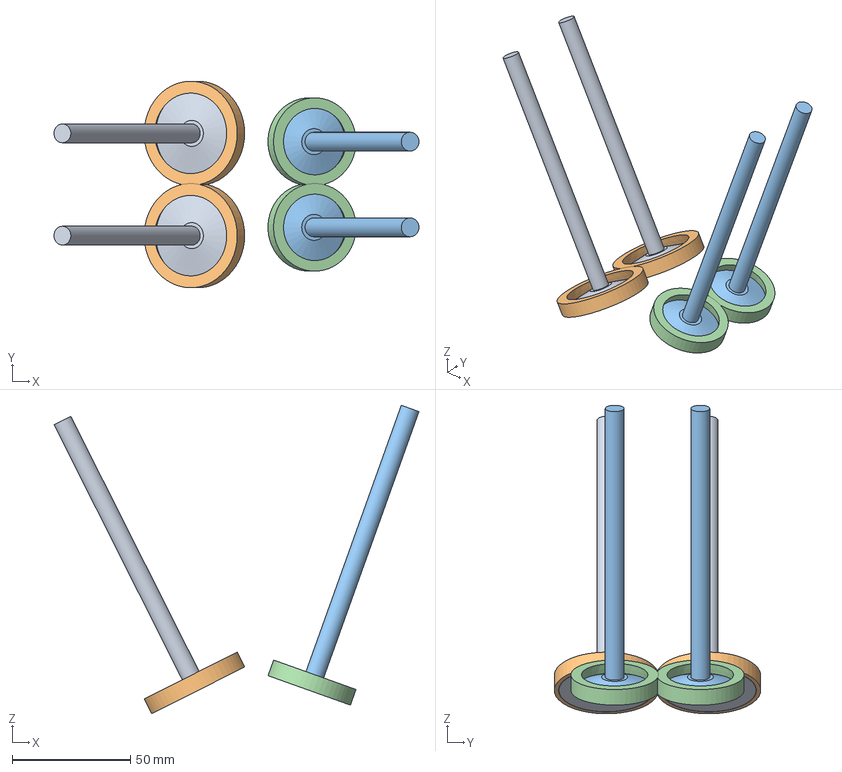
[picture p283: CAD file, 2026-09-25]
twins/m64-cylinder-head/evidence/g3-seat-contact-20260925/four-valves-and-seats.step
154.1 x 87.2 x 130.2 mm
