cluster2600/porscheparts/twins/m64-cylinder-head/evidence/g5-rocker-train-20260925/rockers-rollers-and-shafts.step

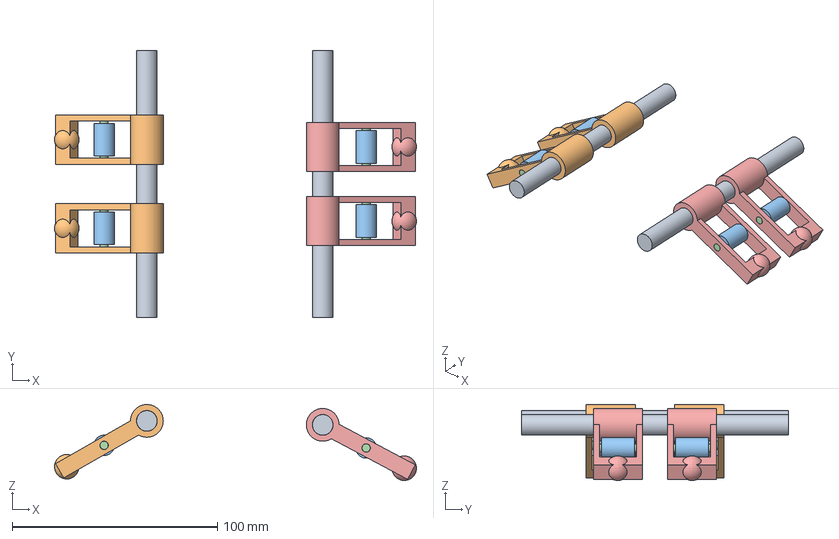
[picture p284: CAD file, 2026-09-25]
twins/m64-cylinder-head/evidence/g5-rocker-train-20260925/rockers-rollers-and-shafts.step
176.5 x 130.0 x 37.1 mm
