cluster2600/porscheparts/twins/m64-engine-system/picogk/out/m64-engine-layout.stl

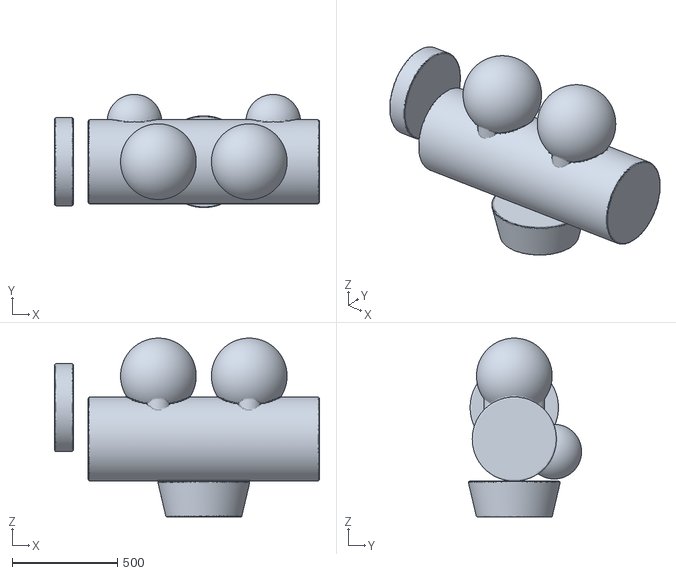
[picture p285: CAD file, 2026-09-29]
twins/m64-engine-system/picogk/out/m64-engine-layout.stl
1260.0 x 538.1 x 849.9
