cluster2600/porscheparts/twins/picogk-station-demo/qualification/build/cad-coupon/cad-coupon.step

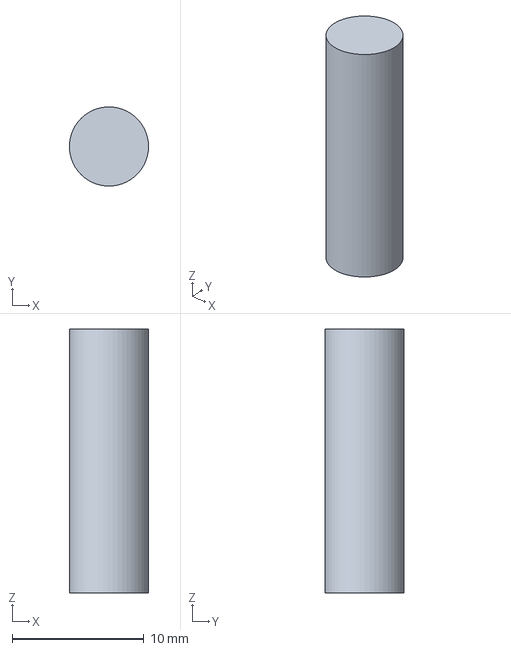
[picture p286: CAD file, 2026-09-29]
twins/picogk-station-demo/qualification/build/cad-coupon/cad-coupon.step
5.99 x 6.00 x 20.0 mm
