cluster2600/porscheparts/twins/picogk-station-demo/qualification/build/station-demo-cpu/geometry/coupon-thin.stl

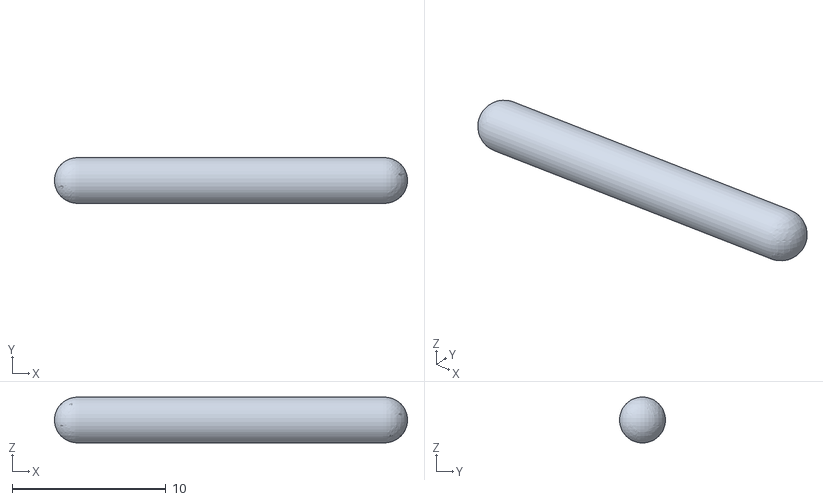
[picture p287: CAD file, 2026-09-29]
twins/picogk-station-demo/qualification/build/station-demo-cpu/geometry/coupon-thin.stl
23.0 x 2.98 x 2.98
