cluster2600/porscheparts/twins/picogk-station-demo/qualification/runtime/native-witness/sphere-radius5mm-voxel0.5mm.stl

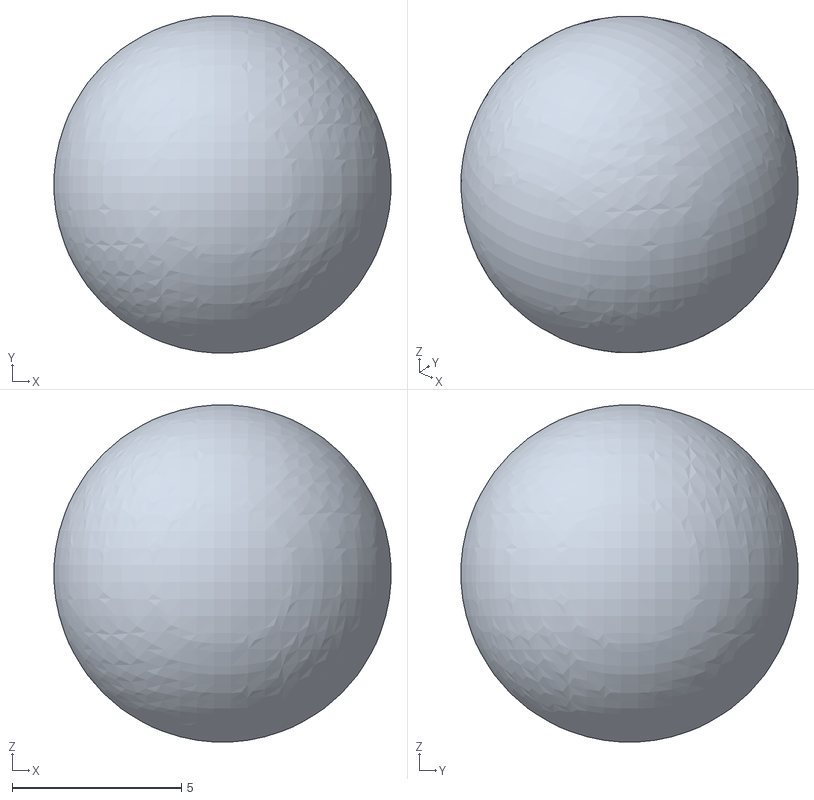
[picture p288: CAD file, 2026-09-29]
twins/picogk-station-demo/qualification/runtime/native-witness/sphere-radius5mm-voxel0.5mm.stl
9.95 x 9.95 x 9.95
