cluster2600/porscheparts/docs/studies/993-air-oil-20261002/cad/component-09-context.stl

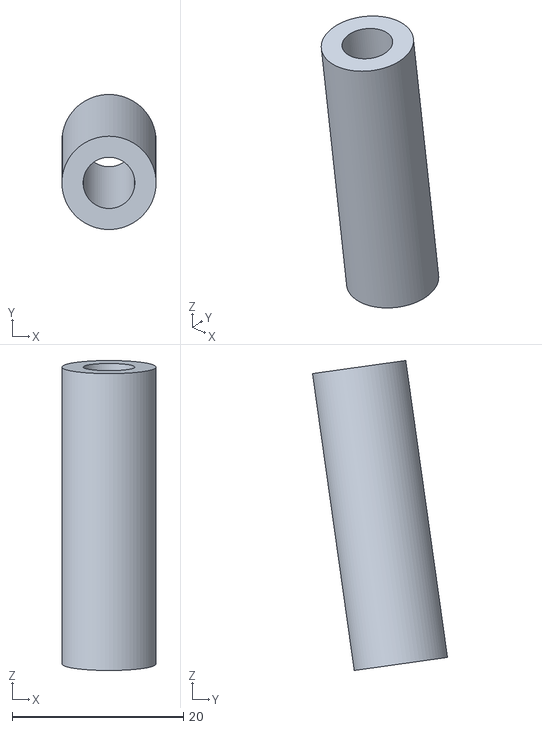
[picture p289: CAD file, 2026-10-02]
docs/studies/993-air-oil-20261002/cad/component-09-context.stl
11.0 x 15.8 x 36.2
