cluster2600/porscheparts/parts/993-body-front-impact-support-alsi10mg-f0-0001/derived/front_impact_support_alsi10mg_f0.step

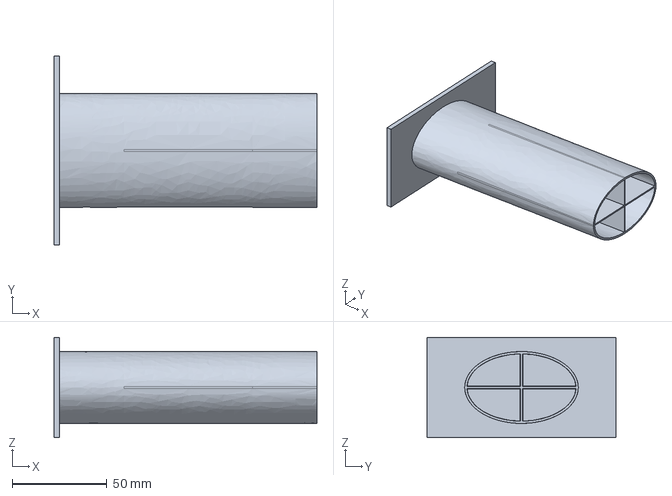
[picture p290: CAD file, 2026-09-07]
parts/993-body-front-impact-support-alsi10mg-f0-0001/derived/front_impact_support_alsi10mg_f0.step
139.0 x 100.0 x 53.0 mm
