cluster2600/porscheparts/parts/993-body-front-lid-0001/derived/front_lid_concept_f0.step

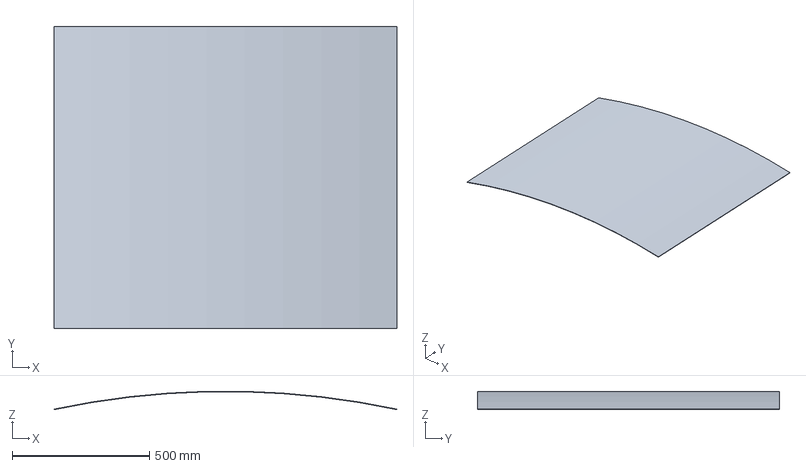
[picture p291: CAD file, 2026-09-15]
parts/993-body-front-lid-0001/derived/front_lid_concept_f0.step
1250.0 x 1100.0 x 67.0 mm
