cluster2600/porscheparts/parts/993-eng-carrier-0001/derived/engine_carrier_concept_f0.step

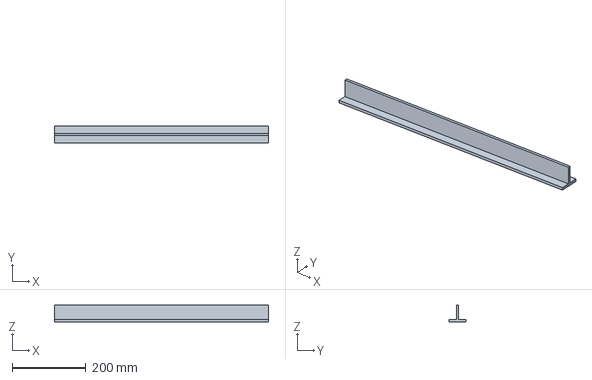
[picture p293: CAD file, 2026-09-15]
parts/993-eng-carrier-0001/derived/engine_carrier_concept_f0.step
580.0 x 45.0 x 45.0 mm
