cluster2600/porscheparts/parts/993-eng-chain-case-0001/derived/chain_case_concept_f0.step

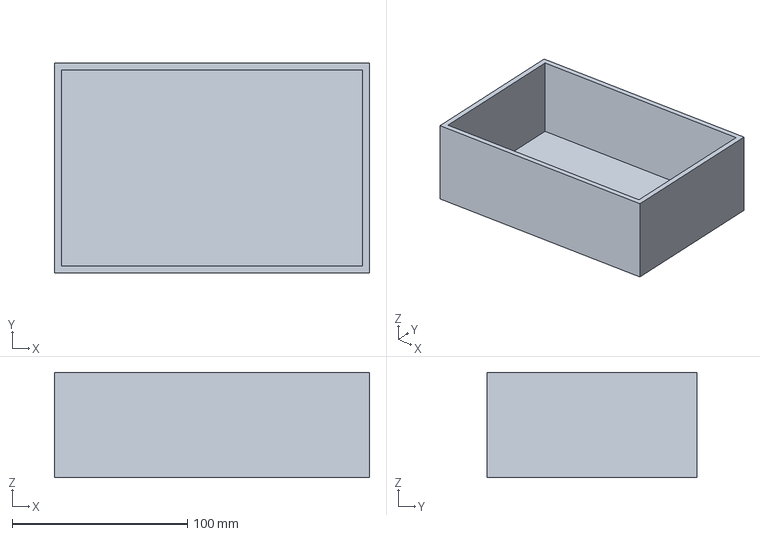
[picture p294: CAD file, 2026-09-15]
parts/993-eng-chain-case-0001/derived/chain_case_concept_f0.step
180.0 x 120.0 x 60.0 mm
