cluster2600/porscheparts/parts/993-eng-cooling-impeller-we43-f1-0001/derived/cooling_impeller_we43_f1.step

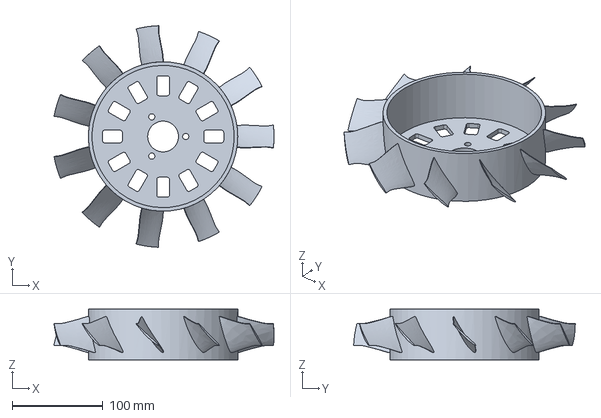
[picture p295: CAD file, 2026-10-08]
parts/993-eng-cooling-impeller-we43-f1-0001/derived/cooling_impeller_we43_f1.step
243.0 x 244.8 x 56.0 mm
