cluster2600/porscheparts/parts/993-eng-exhaust-manifold-in625-f0-0001/derived/exhaust_manifold_in625_f0.step

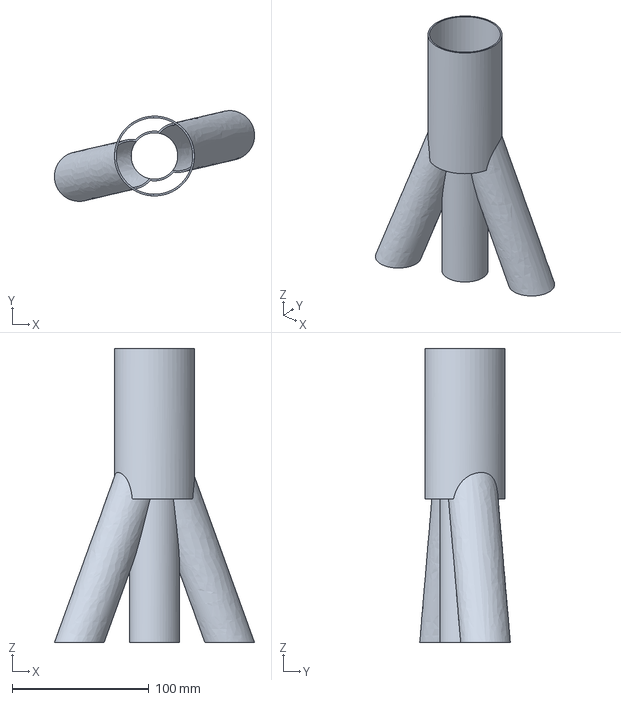
[picture p296: CAD file, 2026-09-07]
parts/993-eng-exhaust-manifold-in625-f0-0001/derived/exhaust_manifold_in625_f0.step
146.4 x 66.4 x 215.0 mm
