cluster2600/porscheparts/parts/993-eng-exhaust-valve-f1-0001/derived/993-turbo-exhaust-43_5-f1.step

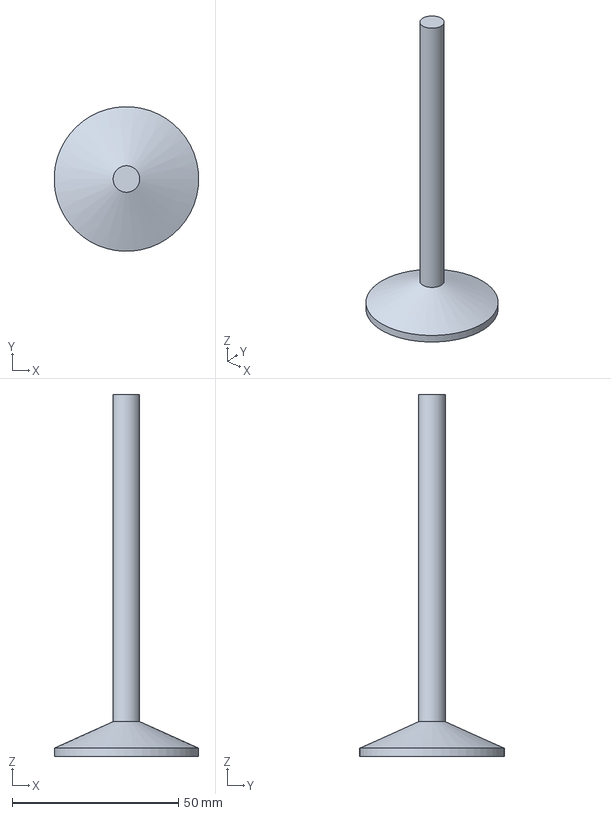
[picture p297: CAD file, 2026-09-15]
parts/993-eng-exhaust-valve-f1-0001/derived/993-turbo-exhaust-43_5-f1.step
43.5 x 43.5 x 108.9 mm
