cluster2600/porscheparts/parts/993-eng-fan-housing-alsi10mg-f0-0001/derived/fan_housing_alsi10mg_f0.step

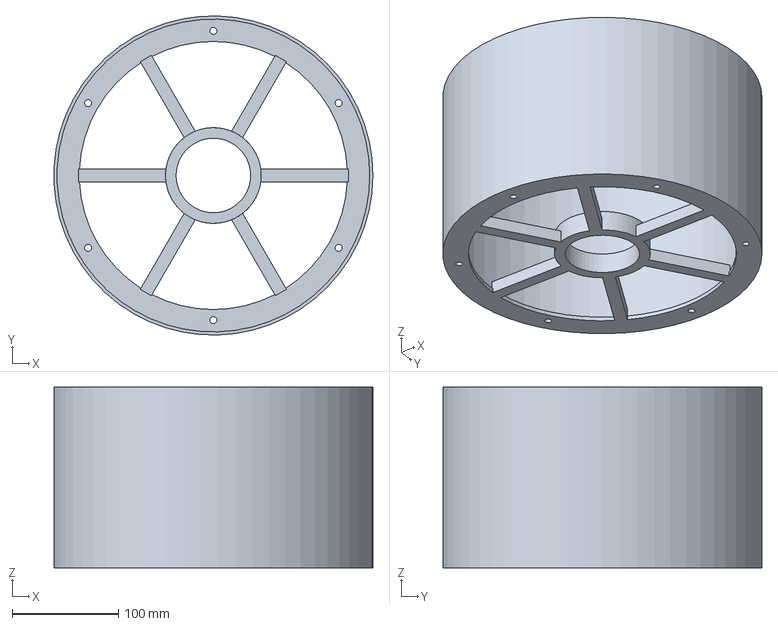
[picture p298: CAD file, 2026-09-08]
parts/993-eng-fan-housing-alsi10mg-f0-0001/derived/fan_housing_alsi10mg_f0.step
299.8 x 299.9 x 170.0 mm
