cluster2600/porscheparts/parts/993-eng-fan-stator-alsi10mg-f1-0001/derived/fan_stator_alsi10mg_f1.step

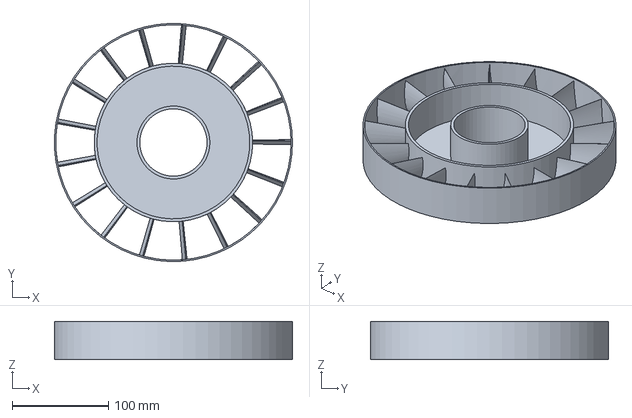
[picture p299: CAD file, 2026-10-07]
parts/993-eng-fan-stator-alsi10mg-f1-0001/derived/fan_stator_alsi10mg_f1.step
247.8 x 247.9 x 40.0 mm
