cluster2600/porscheparts/parts/993-eng-intake-valve-f1-0001/derived/993-intake-49-f1.step

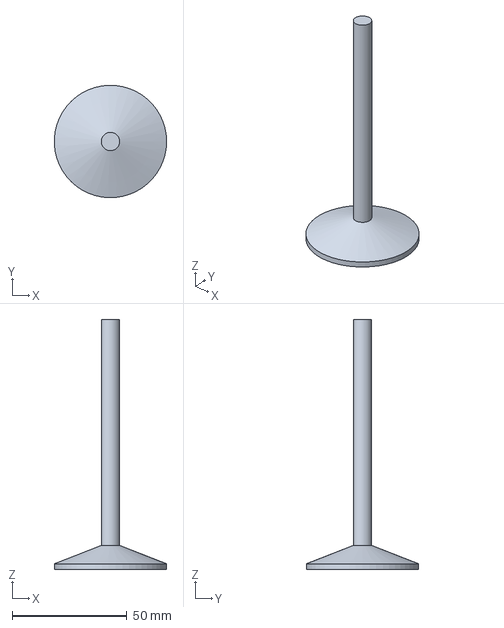
[picture p300: CAD file, 2026-09-15]
parts/993-eng-intake-valve-f1-0001/derived/993-intake-49-f1.step
49.0 x 49.0 x 109.0 mm
