cluster2600/porscheparts/parts/993-eng-intake-valve-ti64-hollow-f0-0001/derived/intake_valve_ti64_hollow_f0.step

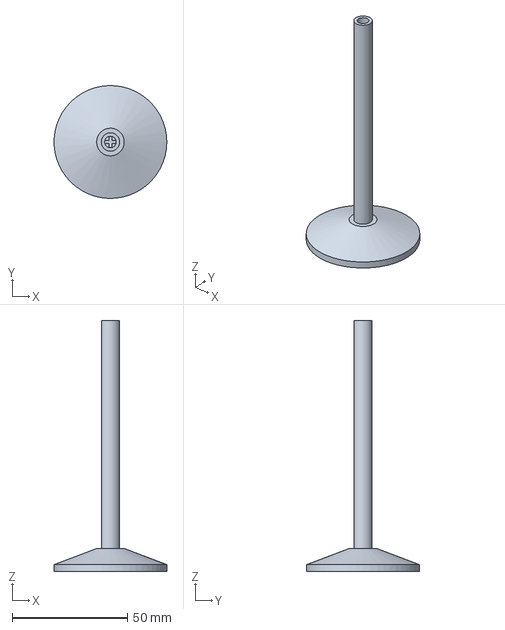
[picture p301: CAD file, 2026-09-08]
parts/993-eng-intake-valve-ti64-hollow-f0-0001/derived/intake_valve_ti64_hollow_f0.step
49.0 x 49.0 x 109.0 mm
