cluster2600/porscheparts/parts/993-eng-intercooler-bracket-ti-f0-0001/derived/intercooler_bracket_ti_f0.step

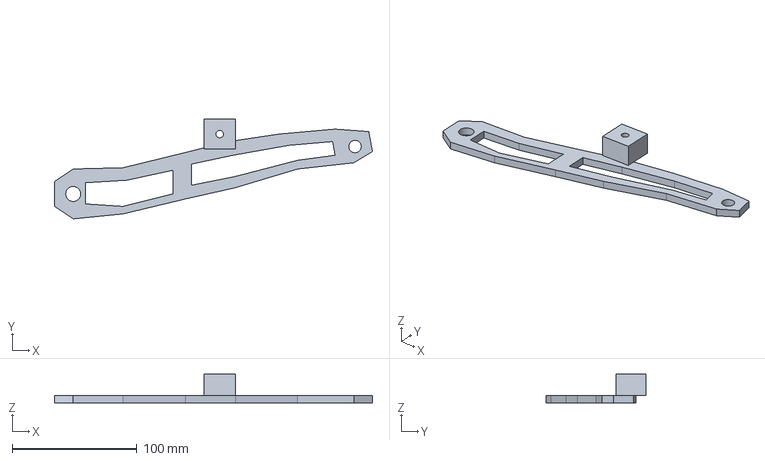
[picture p302: CAD file, 2026-09-07]
parts/993-eng-intercooler-bracket-ti-f0-0001/derived/intercooler_bracket_ti_f0.step
255.0 x 80.0 x 23.0 mm
