cluster2600/porscheparts/parts/993-eng-k16-compressor-wheel-al2139-f1-0001/derived/compressor_wheel_al2139_f1.step

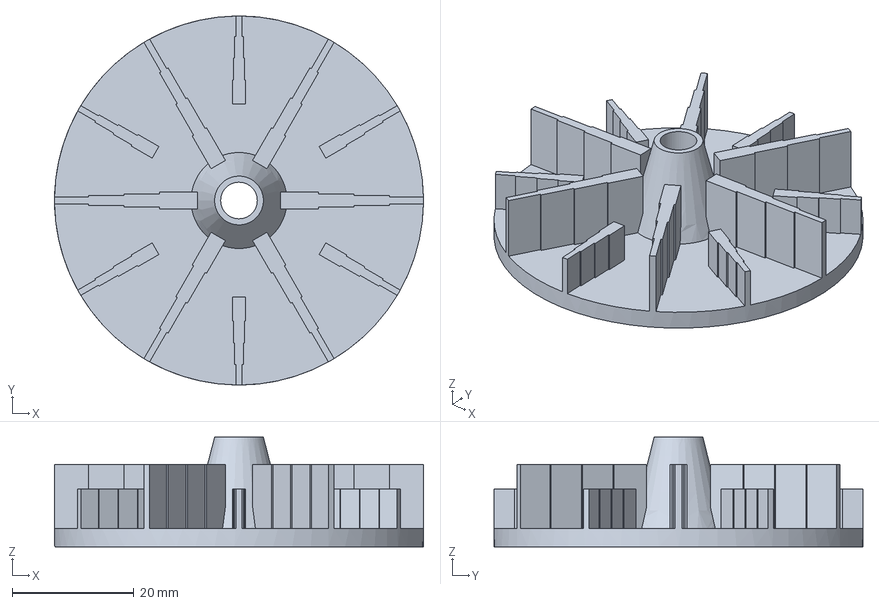
[picture p303: CAD file, 2026-09-08]
parts/993-eng-k16-compressor-wheel-al2139-f1-0001/derived/compressor_wheel_al2139_f1.step
60.5 x 60.5 x 18.0 mm
