cluster2600/porscheparts/parts/993-eng-k16-compressor-wheel-al2139-f1-0001/print/k16_display_stand.stl

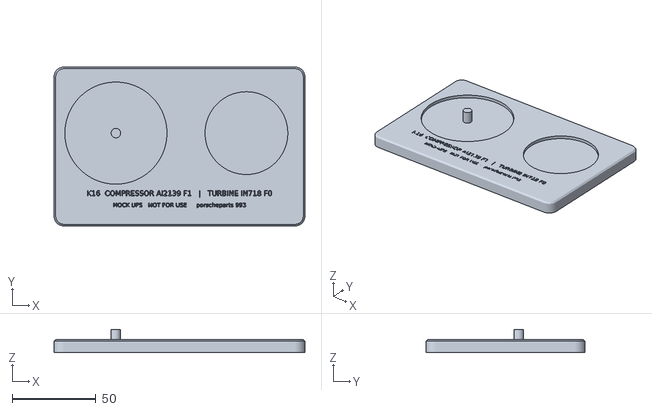
[picture p304: CAD file, 2026-09-25]
parts/993-eng-k16-compressor-wheel-al2139-f1-0001/print/k16_display_stand.stl
150.0 x 95.0 x 14.0
