cluster2600/porscheparts/parts/993-eng-k16-turbine-wheel-in718-f0-0001/derived/turbine_wheel_in718_f0.step

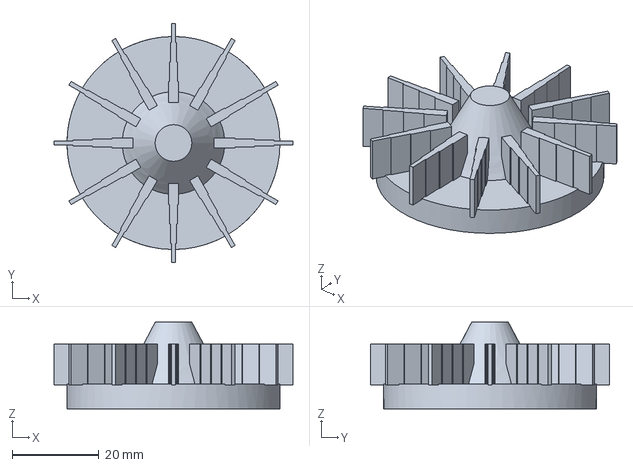
[picture p305: CAD file, 2026-09-08]
parts/993-eng-k16-turbine-wheel-in718-f0-0001/derived/turbine_wheel_in718_f0.step
55.0 x 55.0 x 20.0 mm
