cluster2600/porscheparts/parts/993-eng-oil-filter-console-alsi10mg-f0-0001/derived/oil_filter_console_alsi10mg_f0.step

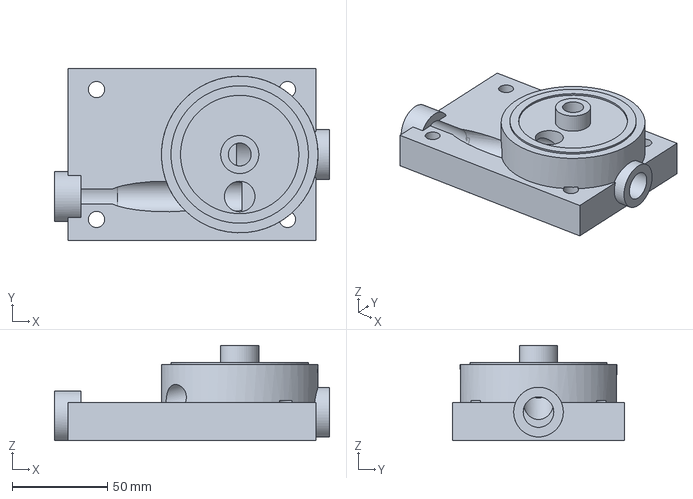
[picture p306: CAD file, 2026-09-08]
parts/993-eng-oil-filter-console-alsi10mg-f0-0001/derived/oil_filter_console_alsi10mg_f0.step
144.0 x 90.0 x 50.0 mm
