cluster2600/porscheparts/parts/993-eng-piston-cp1-gallery-f0-0001/derived/piston_cp1_gallery_f0.step

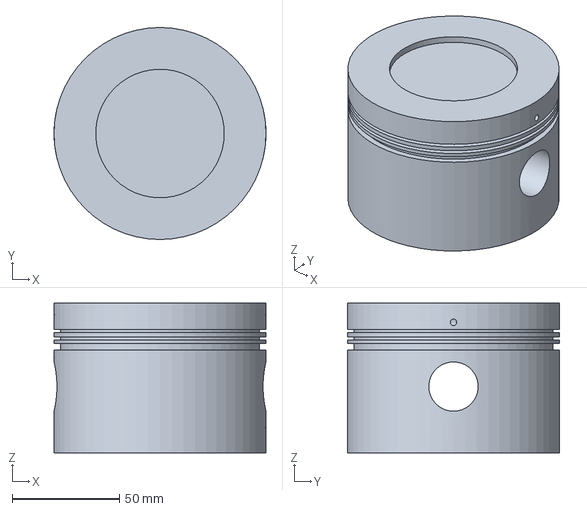
[picture p307: CAD file, 2026-09-07]
parts/993-eng-piston-cp1-gallery-f0-0001/derived/piston_cp1_gallery_f0.step
99.0 x 99.0 x 70.0 mm
