cluster2600/porscheparts/parts/993-eng-three-runner-intake-alsi10mg-f0-0001/derived/three_runner_intake_alsi10mg_f0.step

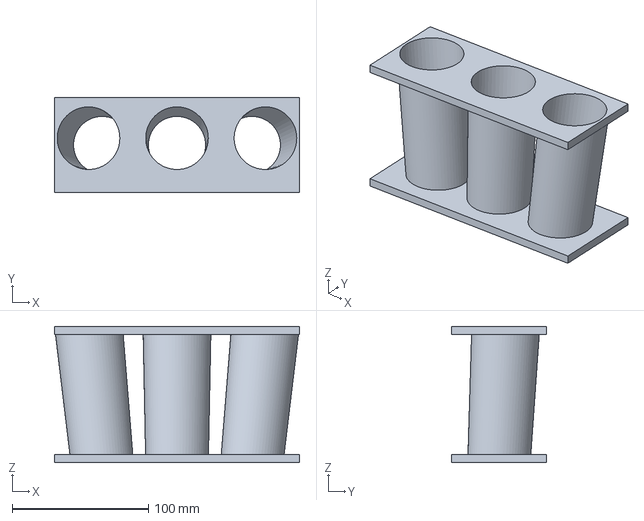
[picture p308: CAD file, 2026-09-07]
parts/993-eng-three-runner-intake-alsi10mg-f0-0001/derived/three_runner_intake_alsi10mg_f0.step
180.0 x 70.0 x 100.0 mm
