cluster2600/porscheparts/parts/993-eng-turbo-heat-shield-in625-f0-0001/derived/turbo_heat_shield_in625_f0.step

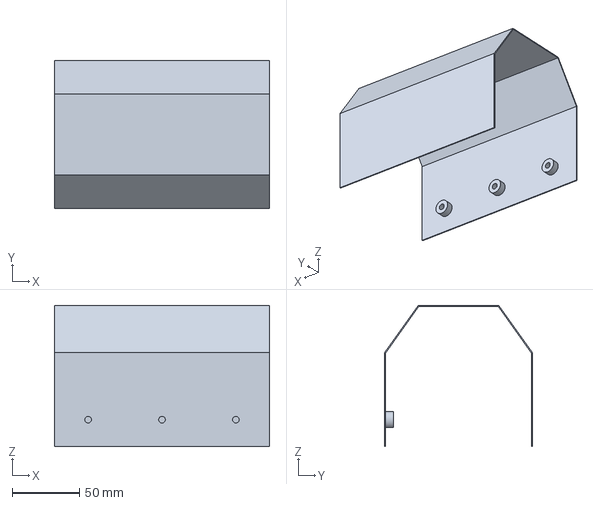
[picture p309: CAD file, 2026-09-07]
parts/993-eng-turbo-heat-shield-in625-f0-0001/derived/turbo_heat_shield_in625_f0.step
160.0 x 110.0 x 105.0 mm
