cluster2600/porscheparts/parts/993-eng-turbo-oil-return-line-in625-f0-0001/derived/turbo_oil_return_line_in625_f0.step

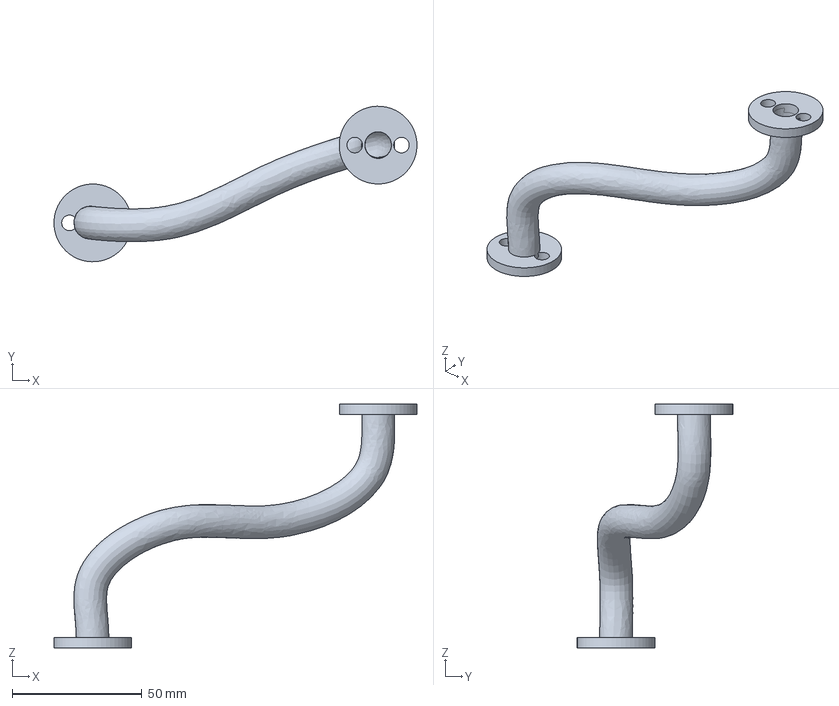
[picture p310: CAD file, 2026-09-08]
parts/993-eng-turbo-oil-return-line-in625-f0-0001/derived/turbo_oil_return_line_in625_f0.step
140.0 x 60.0 x 94.0 mm
