cluster2600/porscheparts/parts/993-eng-upper-valve-cover-alsi10mg-f0-0001/derived/upper_valve_cover_alsi10mg_f0.step

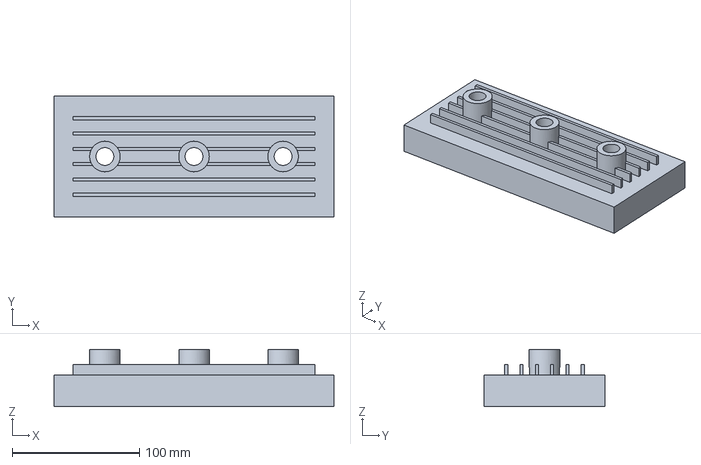
[picture p311: CAD file, 2026-09-08]
parts/993-eng-upper-valve-cover-alsi10mg-f0-0001/derived/upper_valve_cover_alsi10mg_f0.step
220.0 x 95.0 x 45.0 mm
