cluster2600/porscheparts/parts/993-int-dashboard-trim-0001/derived/dashboard_trim_concept_f0.step

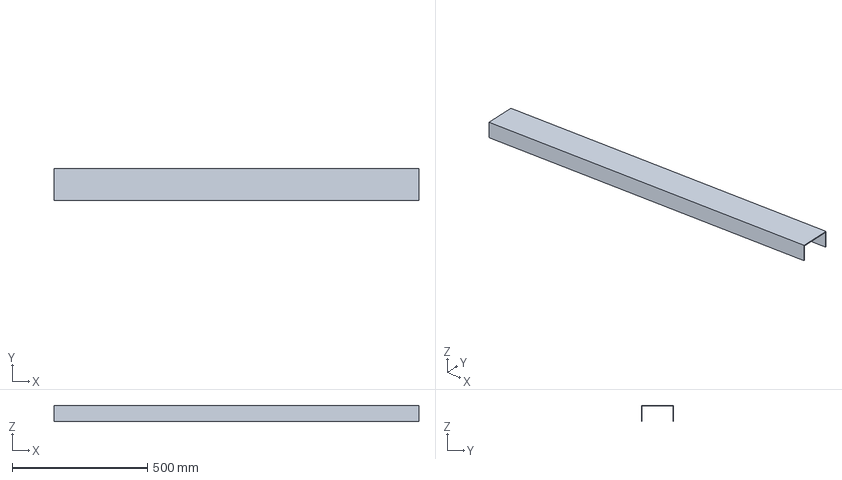
[picture p312: CAD file, 2026-09-15]
parts/993-int-dashboard-trim-0001/derived/dashboard_trim_concept_f0.step
1350.0 x 120.0 x 60.0 mm
