cluster2600/porscheparts/parts/993-int-door-opener-lever-f0-0001/derived/door_opener_lever_f0.step

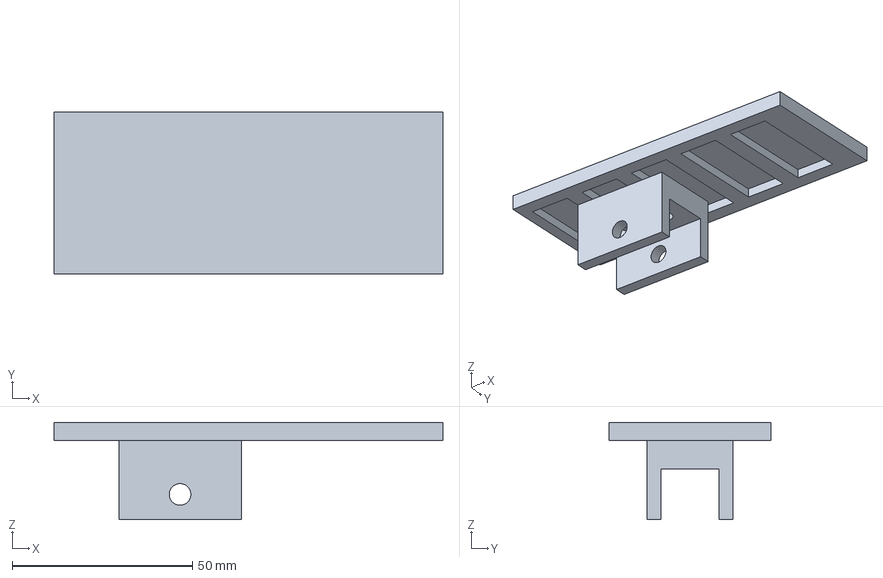
[picture p313: CAD file, 2026-09-09]
parts/993-int-door-opener-lever-f0-0001/derived/door_opener_lever_f0.step
108.0 x 45.0 x 27.0 mm
