cluster2600/porscheparts/parts/993-int-door-pull-0001/derived/door_pull_concept_f0.step

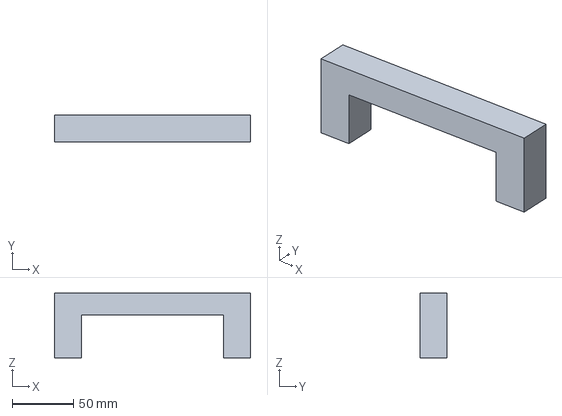
[picture p314: CAD file, 2026-09-15]
parts/993-int-door-pull-0001/derived/door_pull_concept_f0.step
160.0 x 22.0 x 53.0 mm
