cluster2600/porscheparts/parts/993-int-seat-rail-cover-0001/derived/seat_rail_cover_concept_f0.step

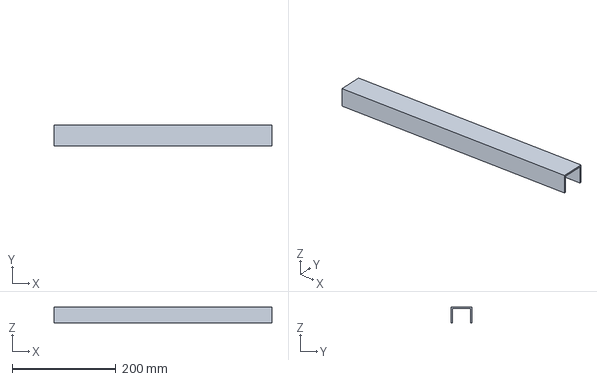
[picture p315: CAD file, 2026-09-15]
parts/993-int-seat-rail-cover-0001/derived/seat_rail_cover_concept_f0.step
420.0 x 40.0 x 30.0 mm
