cluster2600/porscheparts/parts/993-int-switch-blank-0001/derived/switch_blank_concept_f0.step

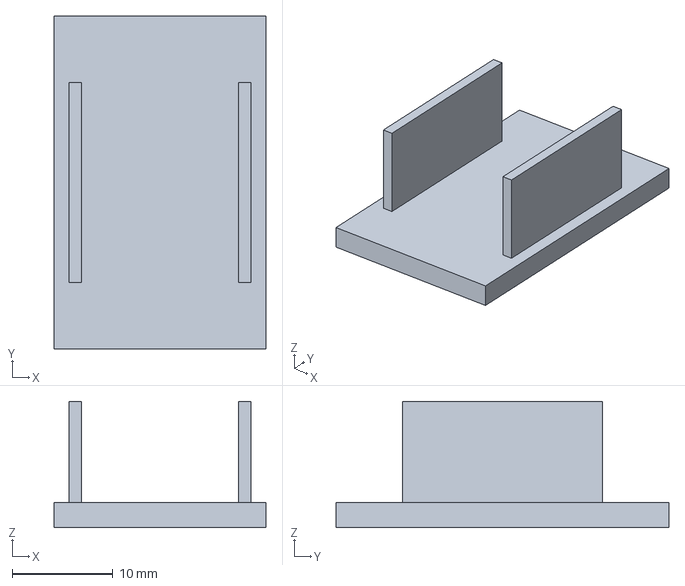
[picture p316: CAD file, 2026-09-15]
parts/993-int-switch-blank-0001/derived/switch_blank_concept_f0.step
21.0 x 33.0 x 12.5 mm
