cluster2600/porscheparts/parts/993-turbocharger-k16-pair-0001/derived/k16_pair_concept_f0.step

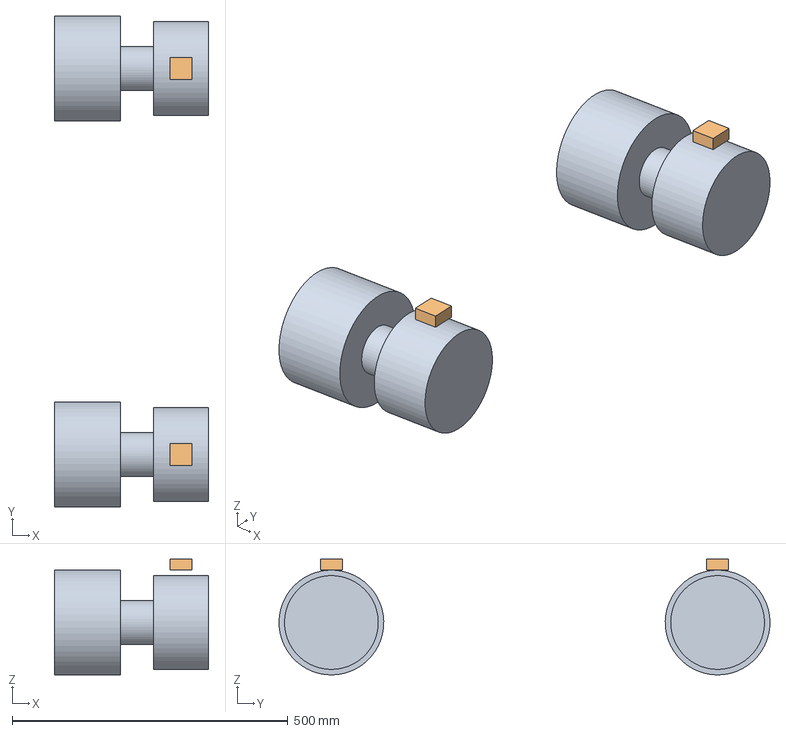
[picture p317: CAD file, 2026-09-15]
parts/993-turbocharger-k16-pair-0001/derived/k16_pair_concept_f0.step
280.0 x 889.9 x 210.0 mm
