cluster2600/porscheparts/parts/993-whl-center-cap-alsi10mg-f0-0001/derived/wheel_center_cap_alsi10mg_f0.step

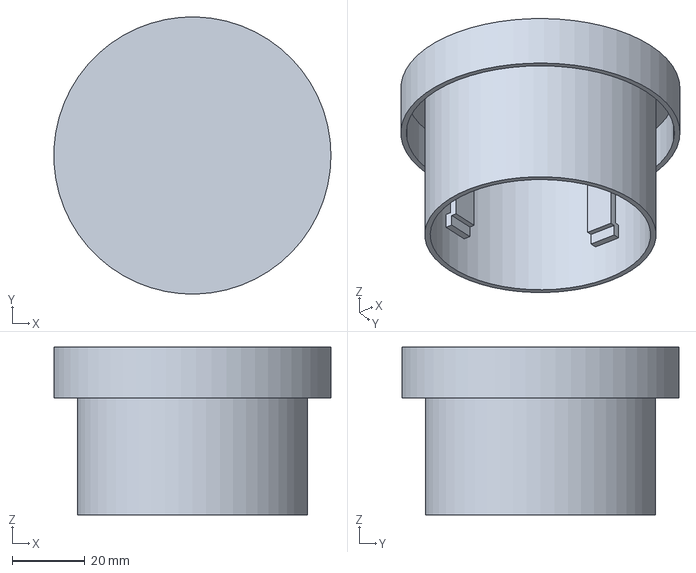
[picture p318: CAD file, 2026-09-07]
parts/993-whl-center-cap-alsi10mg-f0-0001/derived/wheel_center_cap_alsi10mg_f0.step
75.9 x 76.0 x 46.0 mm
