cluster2600/porscheparts/parts/m64-cooling-fan-0001/export/derived/m64-rotor-decim.stl

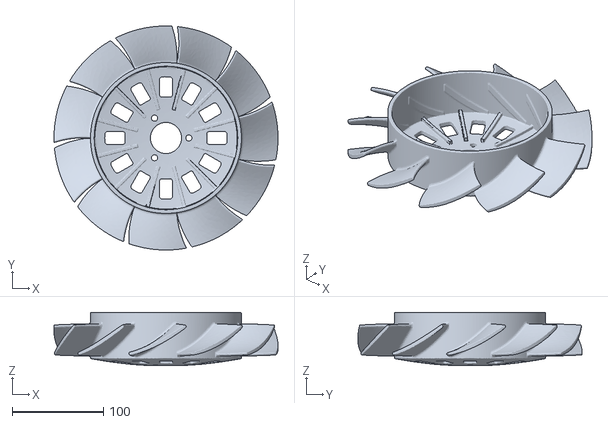
[picture p319: CAD file, 2026-09-29]
parts/m64-cooling-fan-0001/export/derived/m64-rotor-decim.stl
245.0 x 245.0 x 58.2
