cluster2600/porscheparts/parts/m64-valvetrain-0001/validation/run/spring-seat-proxy.stl

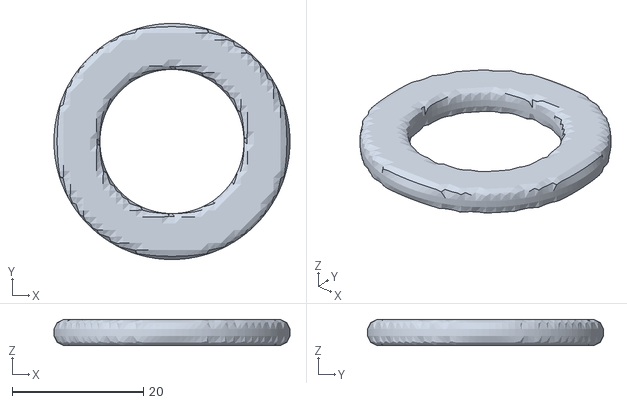
[picture p320: CAD file, 2026-09-29]
parts/m64-valvetrain-0001/validation/run/spring-seat-proxy.stl
36.0 x 36.0 x 4.00
