cluster2600/porscheparts/twins/m64-cylinder-head/evidence/g1-four-valve-20260914/twin-head.step

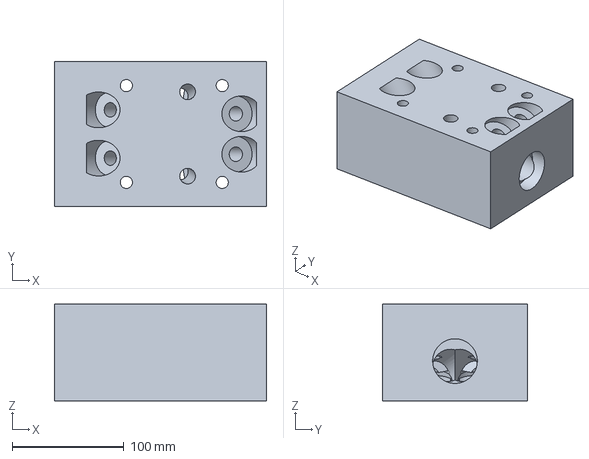
[picture p321: CAD file, 2026-09-15]
twins/m64-cylinder-head/evidence/g1-four-valve-20260914/twin-head.step
189.7 x 130.0 x 86.5 mm
