cluster2600/porscheparts/twins/m64-cylinder-head/evidence/g2-head-features-20260916/twin-guide_seat_retainer.step

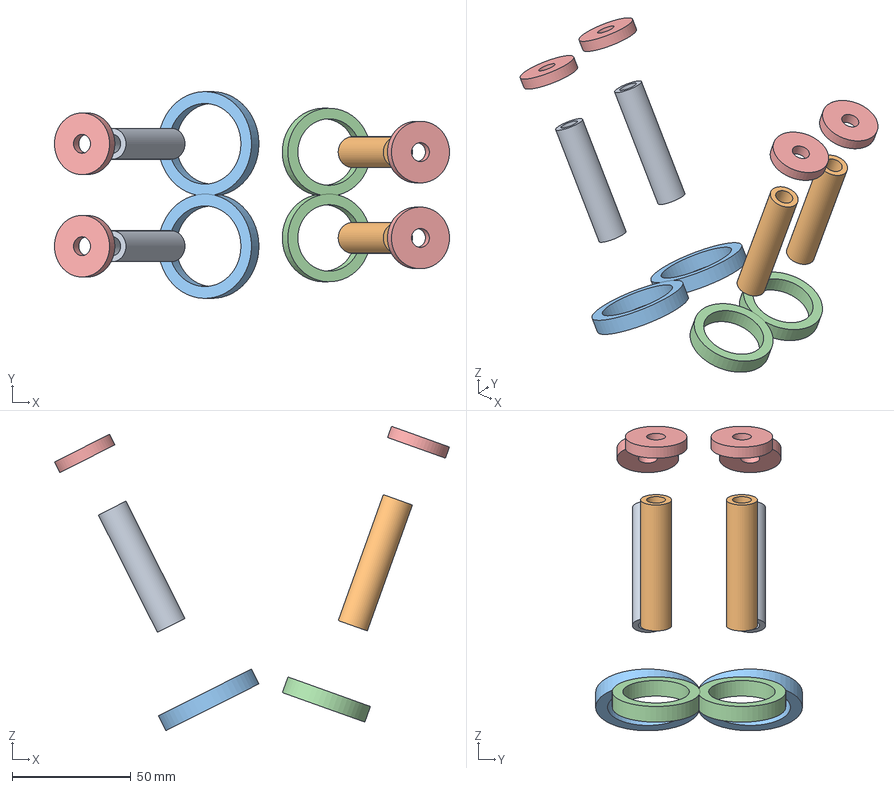
[picture p322: CAD file, 2026-09-16]
twins/m64-cylinder-head/evidence/g2-head-features-20260916/twin-guide_seat_retainer.step
166.5 x 87.2 x 128.4 mm
