cluster2600/porscheparts/twins/picogk-station-demo/qualification/build/station-demo-cpu/geometry/bracket-witness.stl

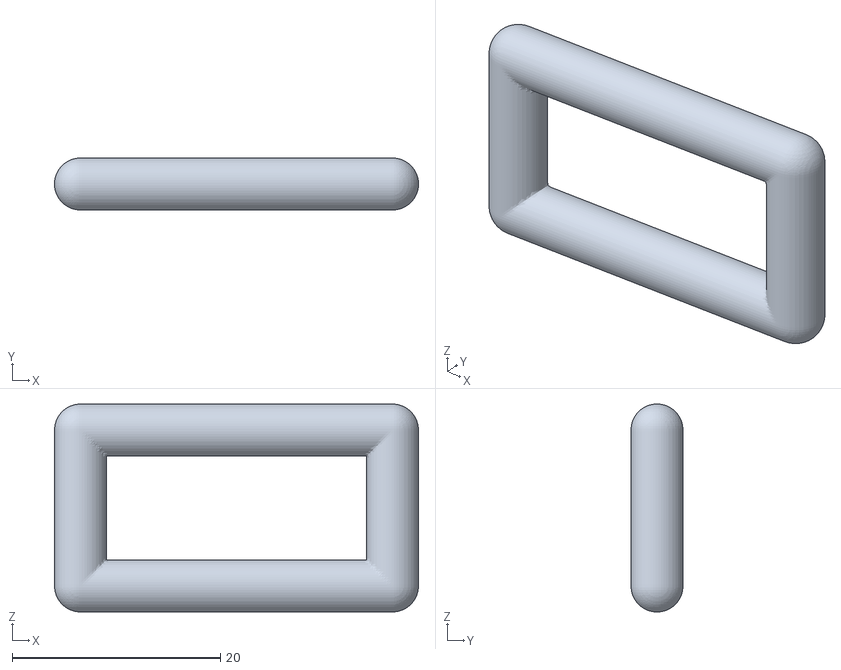
[picture p323: CAD file, 2026-09-29]
twins/picogk-station-demo/qualification/build/station-demo-cpu/geometry/bracket-witness.stl
35.0 x 4.99 x 20.0
