cluster2600/porscheparts/docs/studies/993-air-oil-20261002/cad/component-10-context.stl

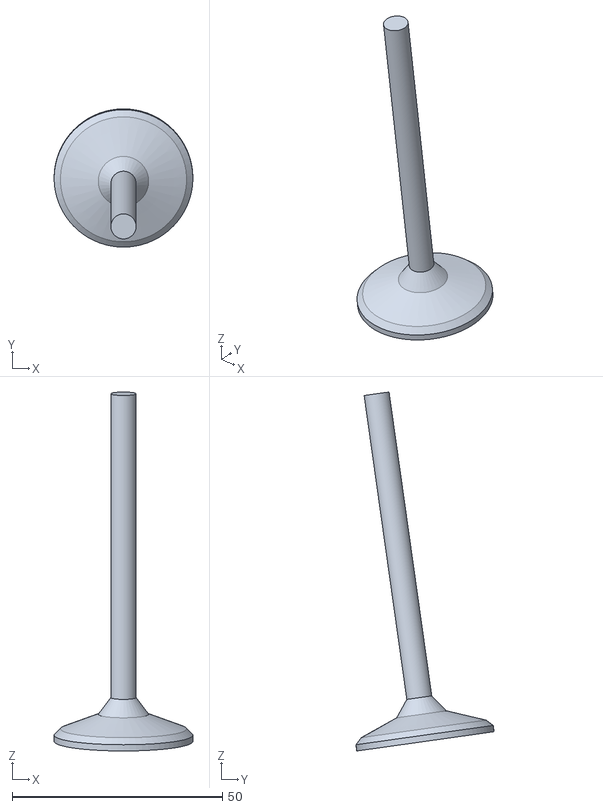
[picture p324: CAD file, 2026-10-02]
docs/studies/993-air-oil-20261002/cad/component-10-context.stl
33.0 x 32.9 x 85.4
