cluster2600/porscheparts/models/horizontal-fan-reconstruction/results/assembly/S1/geometry/belt_pitch_path_envelope_solid3.stl

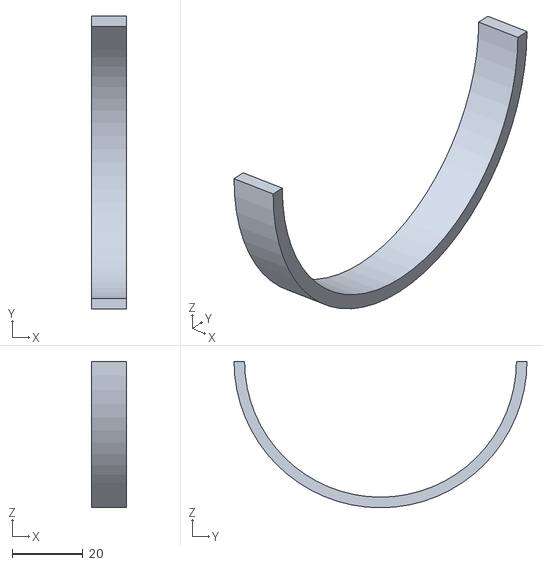
[picture p325: CAD file, 2026-10-05]
models/horizontal-fan-reconstruction/results/assembly/S1/geometry/belt_pitch_path_envelope_solid3.stl
10.0 x 83.0 x 41.5
