cluster2600/porscheparts/parts/993-eng-exhaust-valve-f1-0001/derived/993-carrera-exhaust-42_5-f1.step

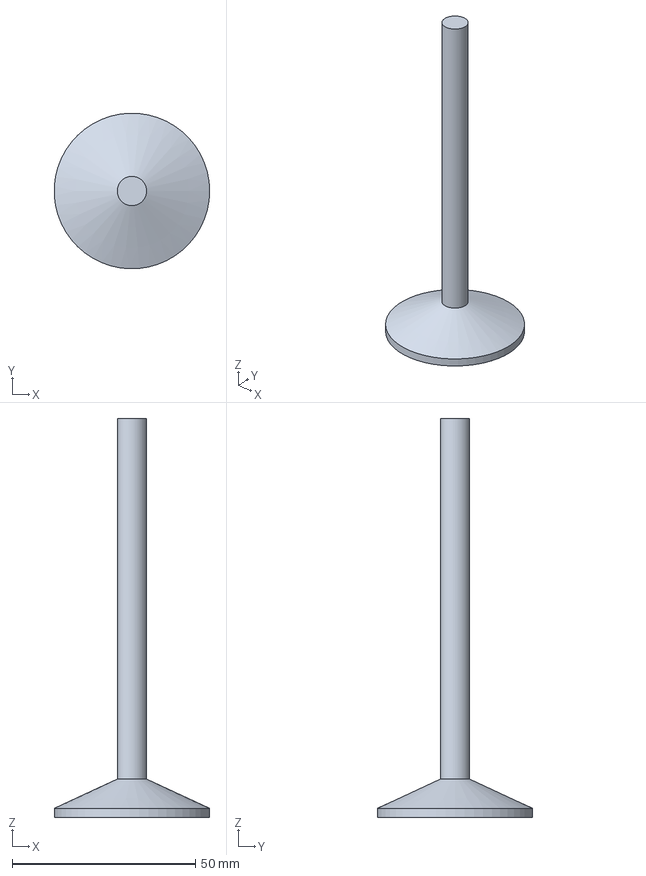
[picture p326: CAD file, 2026-09-15]
parts/993-eng-exhaust-valve-f1-0001/derived/993-carrera-exhaust-42_5-f1.step
42.5 x 42.5 x 109.0 mm
