cluster2600/porscheparts/parts/993-eng-k16-compressor-wheel-al2139-f1-0001/print/k16_display_pair_plate.step

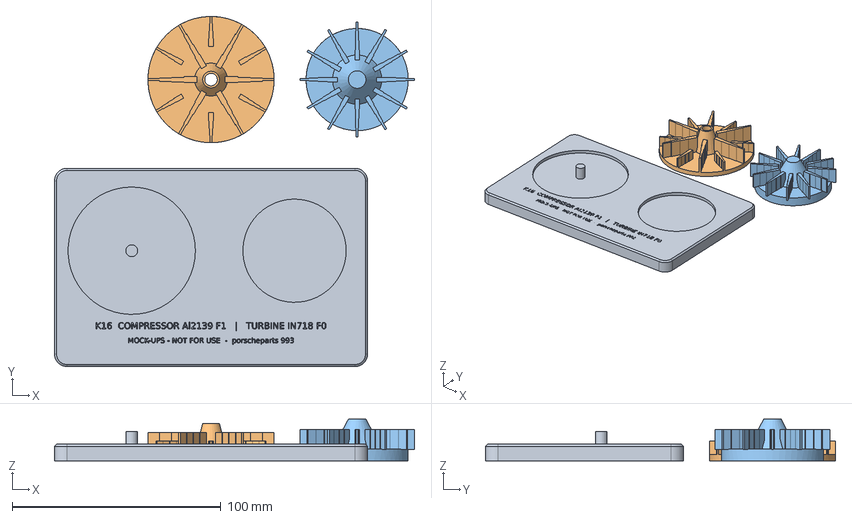
[picture p327: CAD file, 2026-09-25]
parts/993-eng-k16-compressor-wheel-al2139-f1-0001/print/k16_display_pair_plate.step
172.5 x 167.7 x 20.0 mm
