cluster2600/porscheparts/parts/m64-valvetrain-0001/validation/run/cam-follower-bucket-proxy.stl

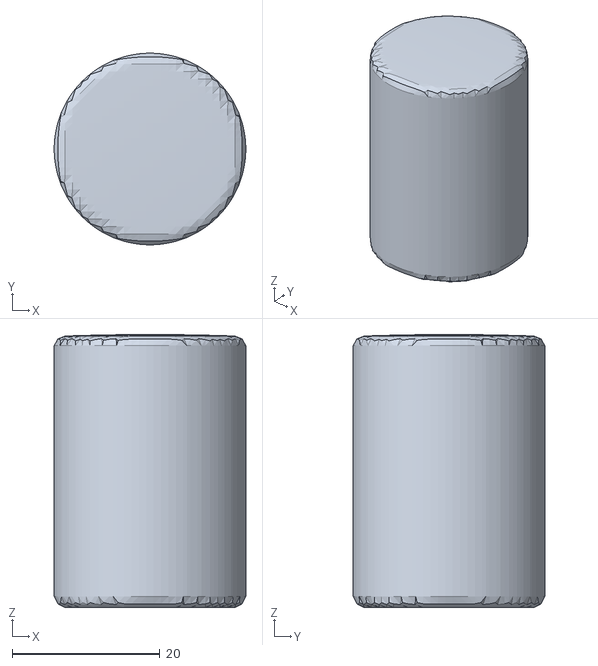
[picture p328: CAD file, 2026-09-29]
parts/m64-valvetrain-0001/validation/run/cam-follower-bucket-proxy.stl
26.0 x 26.0 x 37.0
