cluster2600/porscheparts/twins/m64-cylinder-head/evidence/g2-head-features-20260916/twin-valve_intake.step

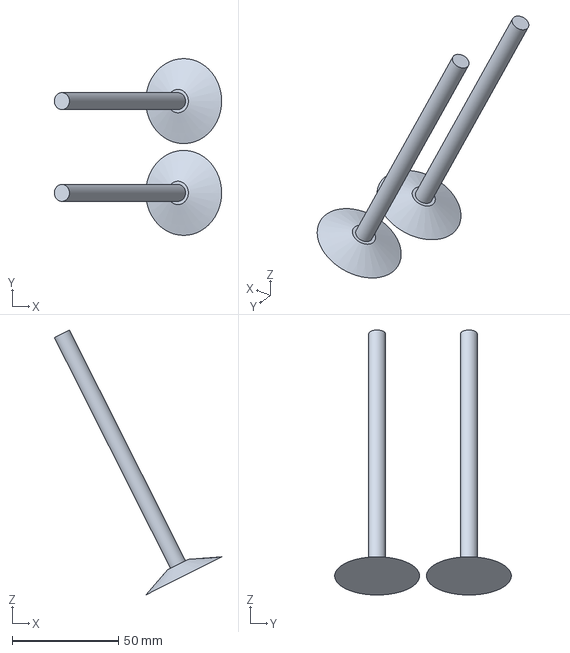
[picture p329: CAD file, 2026-09-16]
twins/m64-cylinder-head/evidence/g2-head-features-20260916/twin-valve_intake.step
78.7 x 83.2 x 124.7 mm
