cluster2600/porscheparts/twins/picogk-station-demo/qualification/build/station-demo-cpu/geometry/coupon-thick.stl

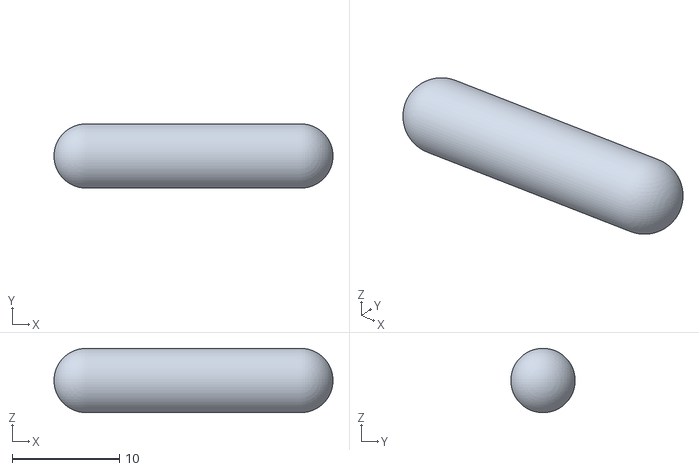
[picture p330: CAD file, 2026-09-29]
twins/picogk-station-demo/qualification/build/station-demo-cpu/geometry/coupon-thick.stl
26.0 x 5.99 x 5.99
