cluster2600/porscheparts/docs/studies/993-air-oil-20261002/cad/component-08-context.stl

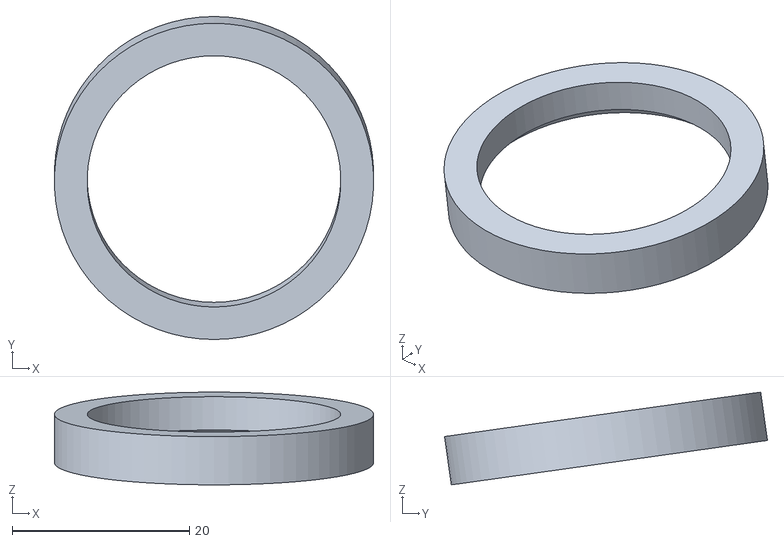
[picture p331: CAD file, 2026-10-02]
docs/studies/993-air-oil-20261002/cad/component-08-context.stl
36.0 x 36.4 x 10.5
