cluster2600/porscheparts/parts/m64-valvetrain-0001/validation/run/valve-intake-49-proxy.stl

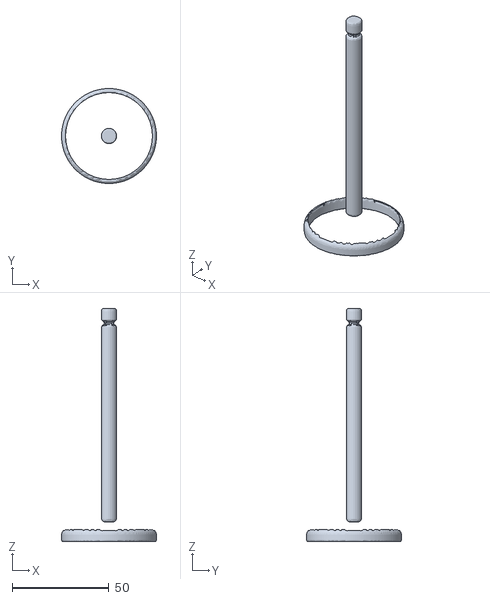
[picture p333: CAD file, 2026-09-29]
parts/m64-valvetrain-0001/validation/run/valve-intake-49-proxy.stl
49.0 x 49.0 x 120.3
