cluster2600/porscheparts/twins/m64-cylinder-head/evidence/g2-head-features-20260916/twin-studs.step

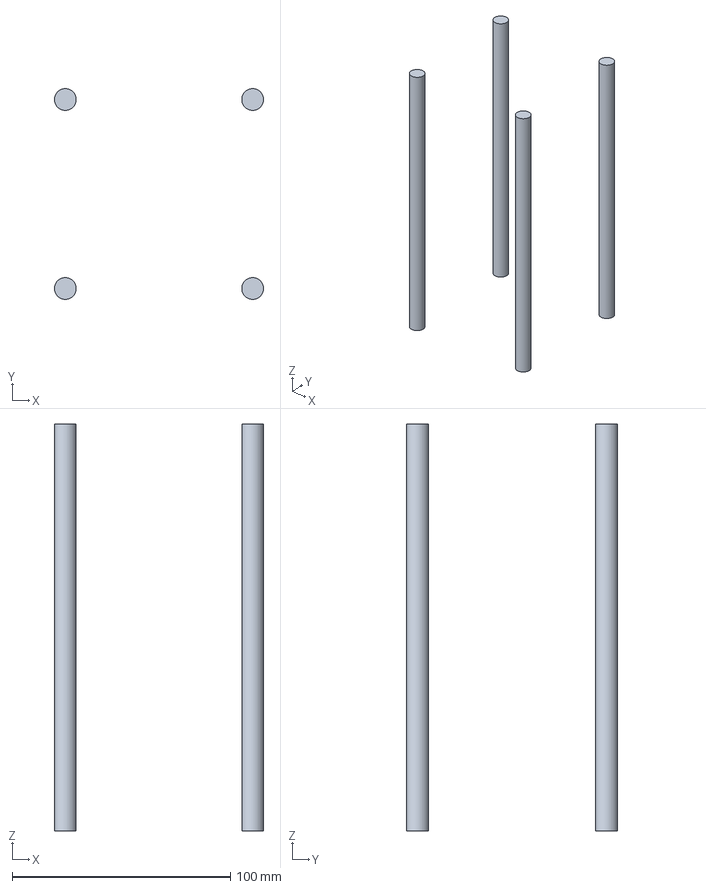
[picture p334: CAD file, 2026-09-16]
twins/m64-cylinder-head/evidence/g2-head-features-20260916/twin-studs.step
95.8 x 96.6 x 186.5 mm
