cluster2600/porscheparts/models/horizontal-fan-reconstruction/V5-rotor.step

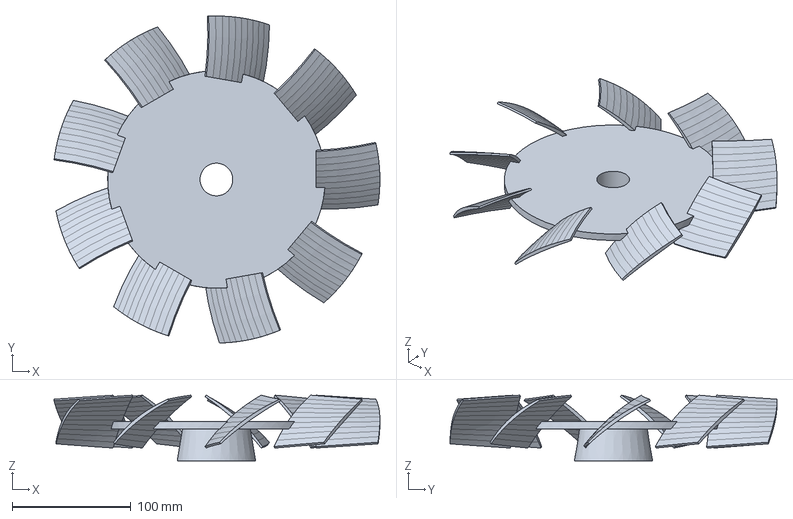
[picture p335: CAD file, 2026-10-04]
models/horizontal-fan-reconstruction/V5-rotor.step
274.0 x 275.0 x 55.2 mm
