cluster2600/porscheparts/parts/m64-valvetrain-0001/validation/run/valve-exhaust-43_5-turbo-proxy.stl

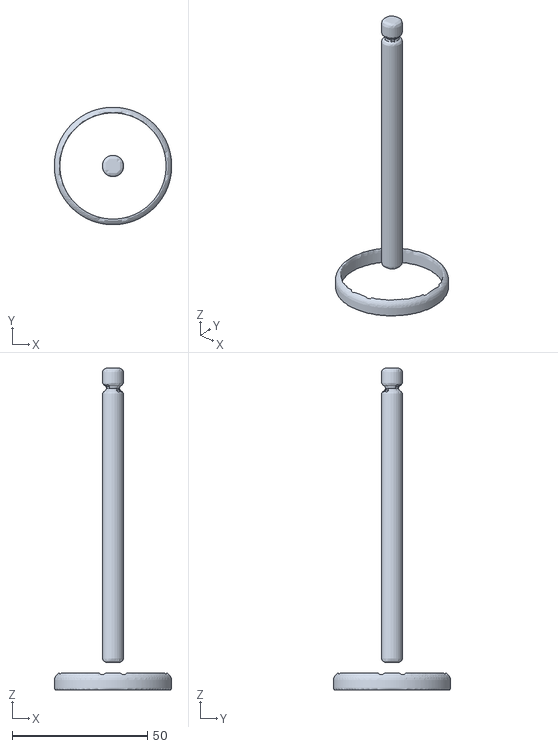
[picture p336: CAD file, 2026-09-29]
parts/m64-valvetrain-0001/validation/run/valve-exhaust-43_5-turbo-proxy.stl
43.5 x 43.5 x 119.2
