cluster2600/porscheparts/parts/993-eng-k16-turbine-wheel-in718-f0-0001/print/README.md

# Print it: K16 turbine wheel, display mock-up

K16 turbine and compressor wheel mock-ups on their display stand

> [!CAUTION]
> **Display mock-up only — never in a turbocharger.** The turbine wheel is
> `prohibited_pending_engineering`; MOCK-UP / NOT FOR USE is engraved into its
> back ([decision 0011](../../../docs/decisions/0011-printable-display-mockups-of-prohibited-parts.md)).

This wheel is printed as a pair with the K16 compressor wheel, on a shared
display stand. Everything — the plate, the stand, settings and instructions —
is in the compressor wheel's folder:
**[`993-eng-k16-compressor-wheel-al2139-f1-0001/print/`](../../993-eng-k16-compressor-wheel-al2139-f1-0001/print/README.md)**.

| file | use |
|---|---|
| [`k16_turbine_wheel_mockup.stl`](k16_turbine_wheel_mockup.stl) | this wheel alone: Ø55 × 20 mm, 1 h 45, 10.0 cm³, supports under the blade rim |
| [`print.json`](print.json) | provenance: master and its SHA-256, engraving |
