cluster2600/porscheparts/twins/reference-917-engine/evidence/f50-additive-print/README.md

# F50 — preuves publiques de qualification additive

Ce dossier ne contient aucune géométrie de culasse. `geometry-2v/` et
`geometry-4v/` publient les métriques agrégées des 4 111 couches de la
tessellation privée correspondant aux maîtres natifs F50. Les coordonnées des
triangles et des contours de tranche restent privées.

`additivefoam-coupons/` publie les agrégats des témoins locaux OpenFOAM 14 /
AdditiveFOAM. Ces coupons ne contiennent ni n'approximent la peau de la culasse.
`media/` montre le déroulement des métriques de procédé ; la vidéo ne représente
ni un moteur en fonctionnement, ni une impression physique.

Les empreintes de tous les fichiers sont regroupées dans `manifest.json`.
L'impression métal et le démarrage moteur restent interdits.
