cluster2600/porscheparts/catalog/templates/manufacturing-request-titanium.md

# Titanium manufacturing request — PART_ID / REVISION

## Definition

- STEP file and SHA-256 digest:
- PDF drawing and revision:
- Units: mm
- Quantity:
- Declared use:
- Safety class:

## Material and process

- Alloy: Ti-6Al-4V Grade 5 / other, to be justified
- Requested material standard:
- Process: LPBF
- Machine and qualified parameter set:
- Traceable powder lot: yes / no
- Witness specimens:

## Build

- Proposed orientation:
- Support-free zones:
- Machining allowances:
- Cavities and powder removal:
- Distortion compensation:

## Post-processing

- Stress relief:
- Heat treatment:
- HIP: required / not required / to be justified
- Support removal:
- Shot peening or polishing:
- Anti-galling protection:
- Planned galvanic isolation:

## Machining

| Surface | Operation | Tolerance | Roughness |
|---|---|---|---|
| | | | |

## Inspection

- Dimensional report:
- Dye penetrant testing:
- CT scan:
- Density:
- Mechanical coupons:
- Material certificate:
- Nonconformance report:

## Acceptance

The part cannot be installed before the reports are reviewed, the revision is
identified and the nonconformances are closed.
