cluster2600/porscheparts/twins/reference-917-engine/evidence/f50-additive-print/geometry-4v/917-head-f50-4v-layer-metrics.csv

layer_index | z_mm | part_area_mm2 | part_perimeter_mm | part_component_count | new_island_count | unsupported_area_mm2 | support_area_mm2 | support_perimeter_mm
0 | 0.025 | 16.18093597 | 16.90566775 | 1 | 0 | 0.0 | 5547.5 | 3131.0
1 | 0.075 | 22.39304766 | 23.09331022 | 1 | 0 | 5.35911366 | 5540.75 | 3137.0
2 | 0.125 | 28.42126955 | 26.05325095 | 1 | 0 | 4.86754591 | 5533.5 | 3141.0
3 | 0.175 | 34.62894273 | 27.98075944 | 1 | 0 | 4.90326374 | 5526.75 | 3143.0
4 | 0.225 | 40.4664955 | 29.06324178 | 1 | 0 | 4.44119021 | 5521.0 | 3142.0
5 | 0.275 | 46.2192439 | 30.20581909 | 1 | 0 | 4.30408089 | 5514.75 | 3145.0
6 | 0.325 | 51.69073686 | 31.45141444 | 1 | 0 | 3.96605699 | 5508.75 | 3145.0
7 | 0.375 | 57.13910379 | 32.7504262 | 1 | 0 | 3.88122173 | 5502.5 | 3146.0
8 | 0.425 | 62.19974193 | 34.01631682 | 1 | 0 | 3.42901969 | 5497.75 | 3148.0
9 | 0.475 | 67.15631684 | 35.29375277 | 1 | 0 | 3.26209932 | 5493.5 | 3148.0
10 | 0.525 | 72.33801871 | 36.60044866 | 1 | 0 | 3.42407777 | 5486.0 | 3149.0
11 | 0.575 | 77.71668941 | 37.94616678 | 1 | 0 | 3.55643576 | 5482.0 | 3150.0
12 | 0.625 | 83.28160289 | 39.33735149 | 1 | 0 | 3.67572013 | 5474.5 | 3151.0
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
