cluster2600/porscheparts/twins/picogk-station-demo/qualification/build/station-demo-cpu/bracket-witness/station-bracket-witness-layer-metrics.csv

layer_index | z_mm | part_area_mm2 | part_perimeter_mm | part_component_count | new_island_count | unsupported_area_mm2 | support_area_mm2 | support_perimeter_mm
0 | 0.015 | 0.19231728 | 1.67074243 | 1 | 0 | 0.0 | 7.0 | 33.0
1 | 0.045 | 0.66636799 | 2.93487781 | 1 | 0 | 0.4211148 | 6.5 | 32.0
2 | 0.075 | 1.10381633 | 3.75285296 | 1 | 0 | 0.34658075 | 6.0 | 31.0
3 | 0.105 | 1.55401544 | 4.44474828 | 1 | 0 | 0.33479264 | 6.0 | 31.0
4 | 0.135 | 2.00887325 | 5.06046893 | 1 | 0 | 0.31869529 | 5.5 | 30.0
5 | 0.165 | 2.47348095 | 5.60879 | 1 | 0 | 0.30997423 | 5.5 | 30.0
6 | 0.195 | 2.91711705 | 6.09618301 | 1 | 0 | 0.27256035 | 5.0 | 28.0
7 | 0.225 | 3.33324847 | 6.51209859 | 1 | 0 | 0.2304347 | 4.25 | 25.0
8 | 0.255 | 3.74283505 | 6.88482764 | 1 | 0 | 0.21141265 | 4.0 | 24.0
9 | 0.285 | 4.15436966 | 7.24662637 | 1 | 0 | 0.20217432 | 4.0 | 24.0
10 | 0.315 | 4.57139807 | 7.60876828 | 1 | 0 | 0.19681055 | 4.0 | 24.0
11 | 0.345 | 4.99776242 | 7.96143903 | 1 | 0 | 0.19528455 | 4.0 | 24.0
12 | 0.375 | 5.39825376 | 8.26643669 | 1 | 0 | 0.15883064 | 3.5 | 22.0
13 | 0.405 | 5.78107087 | 8.54414544 | 1 | 0 | 0.13200644 | 2.75 | 19.0
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
