cluster2600/porscheparts/twins/picogk-station-demo/qualification/build/station-demo-cpu/coupon-thick/station-coupon-thick-layer-metrics.csv

layer_index | z_mm | part_area_mm2 | part_perimeter_mm | part_component_count | new_island_count | unsupported_area_mm2 | support_area_mm2 | support_perimeter_mm
0 | 0.015 | 0.30408853 | 2.00805483 | 1 | 0 | 0.0 | 9.5 | 42.0
1 | 0.045 | 0.86011848 | 3.32549026 | 1 | 0 | 0.49296544 | 7.5 | 34.0
2 | 0.075 | 1.42404877 | 4.24829651 | 1 | 0 | 0.46134289 | 7.5 | 34.0
3 | 0.105 | 1.95369855 | 4.97286022 | 1 | 0 | 0.3993792 | 7.0 | 34.0
4 | 0.135 | 2.50804072 | 5.63446883 | 1 | 0 | 0.40233389 | 7.0 | 34.0
5 | 0.165 | 3.03997828 | 6.19525807 | 1 | 0 | 0.36008093 | 7.0 | 34.0
6 | 0.195 | 3.59100632 | 6.73165548 | 1 | 0 | 0.36234854 | 7.0 | 34.0
7 | 0.225 | 4.14986317 | 7.24184251 | 1 | 0 | 0.35408542 | 5.0 | 28.0
8 | 0.255 | 4.67032769 | 7.67968503 | 1 | 0 | 0.30039068 | 5.0 | 28.0
9 | 0.285 | 5.14400286 | 8.05315247 | 1 | 0 | 0.24046534 | 5.0 | 28.0
10 | 0.315 | 5.6280403 | 8.42023256 | 1 | 0 | 0.23962059 | 5.0 | 28.0
11 | 0.345 | 6.12276726 | 8.78365761 | 1 | 0 | 0.23929772 | 5.0 | 28.0
12 | 0.375 | 6.61586606 | 9.12905549 | 1 | 0 | 0.22676637 | 5.0 | 28.0
13 | 0.405 | 7.11781152 | 9.46623414 | 1 | 0 | 0.2252508 | 3.5 | 24.0
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
