cluster2600/porscheparts/twins/picogk-station-demo/qualification/build/station-demo-cpu/coupon-thin/station-coupon-thin-layer-metrics.csv

layer_index | z_mm | part_area_mm2 | part_perimeter_mm | part_component_count | new_island_count | unsupported_area_mm2 | support_area_mm2 | support_perimeter_mm
0 | 0.015 | 0.16333284 | 1.48716545 | 1 | 0 | 0.0 | 1.25 | 6.0
1 | 0.045 | 0.44868949 | 2.44070307 | 1 | 0 | 0.23791893 | 1.25 | 6.0
2 | 0.075 | 0.69779441 | 2.98581196 | 1 | 0 | 0.17306078 | 1.25 | 6.0
3 | 0.105 | 0.94846824 | 3.48619315 | 1 | 0 | 0.15827641 | 0.25 | 2.0
4 | 0.135 | 1.22253761 | 3.94929507 | 1 | 0 | 0.16666059 | 0.25 | 2.0
5 | 0.165 | 1.49031224 | 4.34464095 | 1 | 0 | 0.14647304 | 0.25 | 2.0
6 | 0.195 | 1.77199283 | 4.74352369 | 1 | 0 | 0.14851863 | 0.25 | 2.0
7 | 0.225 | 2.02855594 | 5.10038543 | 1 | 0 | 0.11145845 | 0.0 | 0.0
8 | 0.255 | 2.24140525 | 5.35536424 | 1 | 0 | 0.05703923 | 0.0 | 0.0
9 | 0.285 | 2.44641757 | 5.57669231 | 1 | 0 | 0.03713524 | 0.0 | 0.0
10 | 0.315 | 2.648585 | 5.79600149 | 1 | 0 | 0.03050202 | 0.0 | 0.0
11 | 0.345 | 2.85793471 | 6.00942011 | 1 | 0 | 0.03266833 | 0.0 | 0.0
12 | 0.375 | 3.07547848 | 6.2409867 | 1 | 0 | 0.0 | 0.0 | 0.0
13 | 0.405 | 3.29811085 | 6.47472299 | 1 | 0 | 0.0 | 0.0 | 0.0
14 | 0.435 | 3.52459667 | 6.70366229 | 1 | 0 | 0.0 | 0.0 | 0.0
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
