cluster2600/porscheparts/parts/993-eng-cooling-impeller-we43-f1-0001/media/print-simulation/build-plate.png

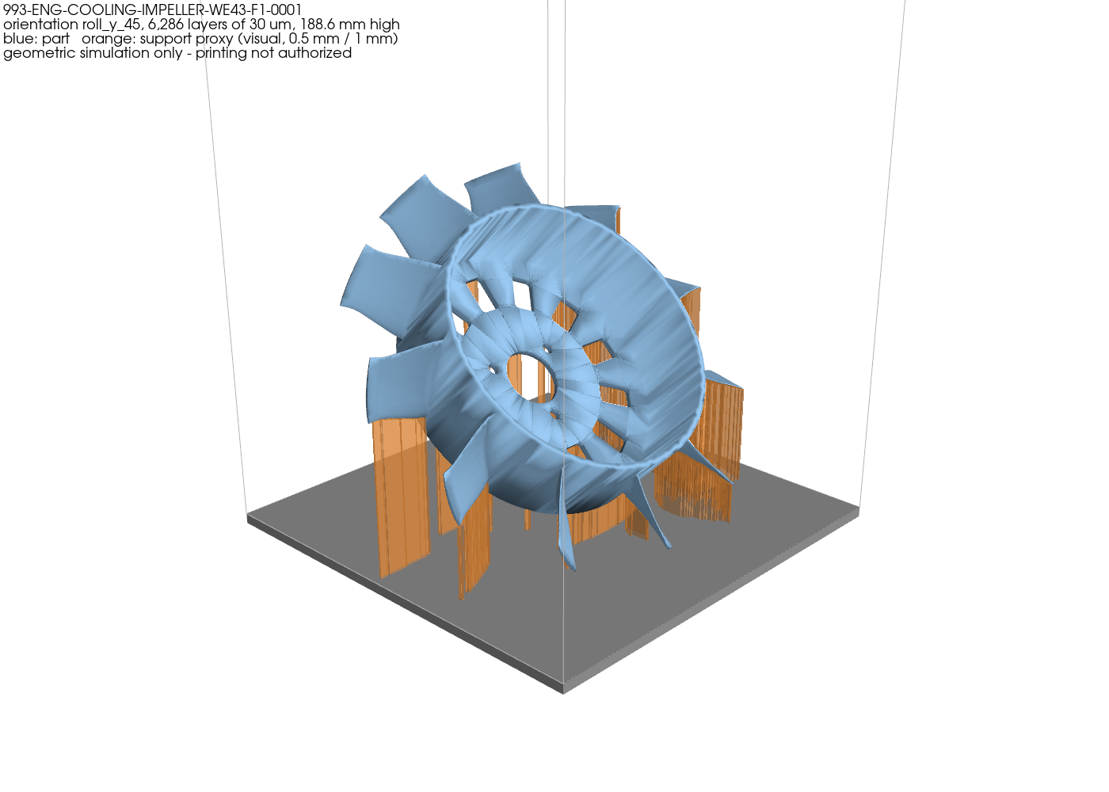
parts/993-eng-cooling-impeller-we43-f1-0001/media/print-simulation/build-plate.png
