cluster2600/porscheparts/parts/993-eng-fan-stator-alsi10mg-f1-0001/media/print-simulation/layers.png

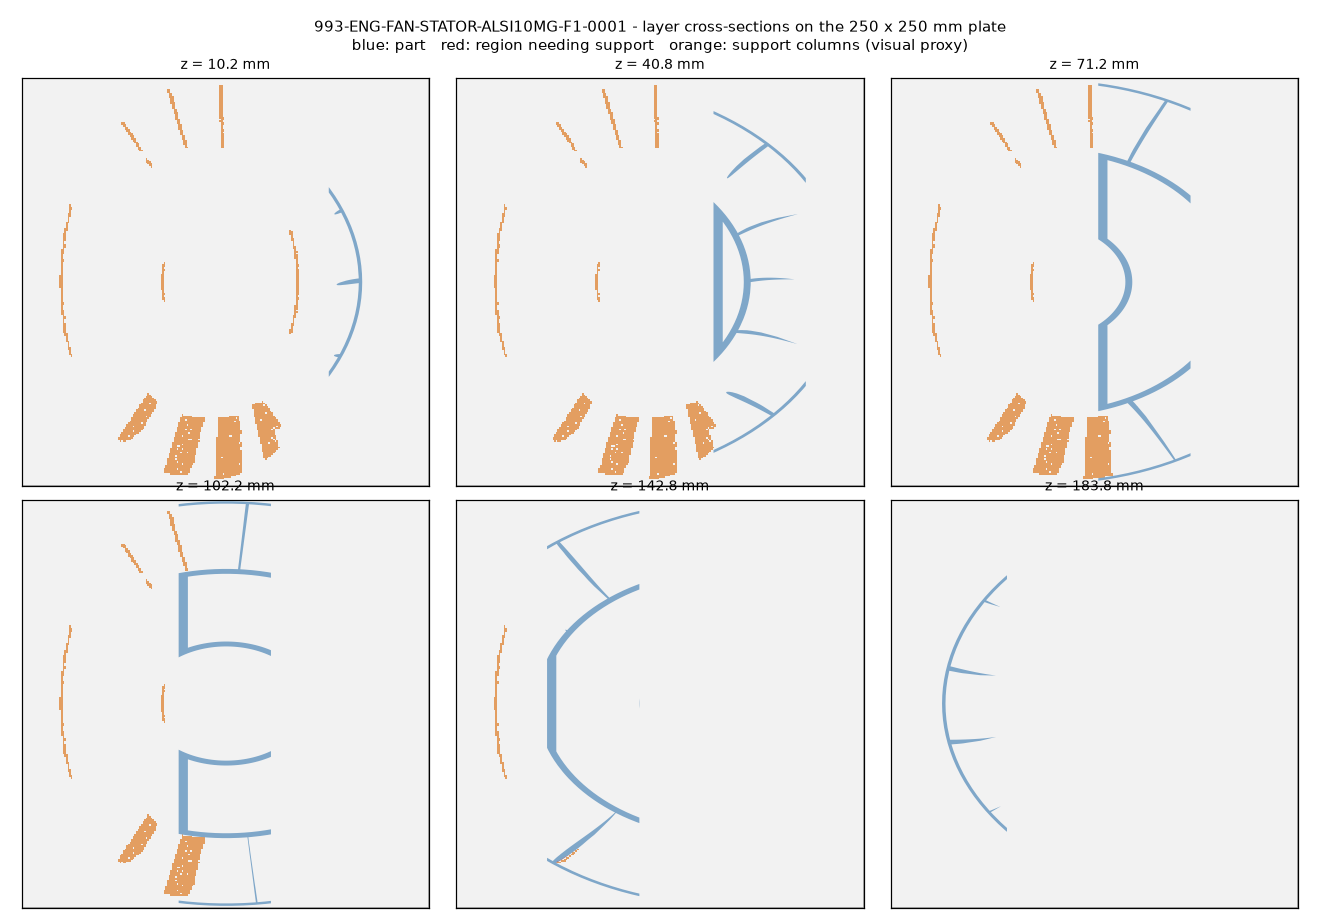
parts/993-eng-fan-stator-alsi10mg-f1-0001/media/print-simulation/layers.png
