cluster2600/porscheparts/twins/993-engine-cooling-fan-system-f0/results/omniverse/assembly.png

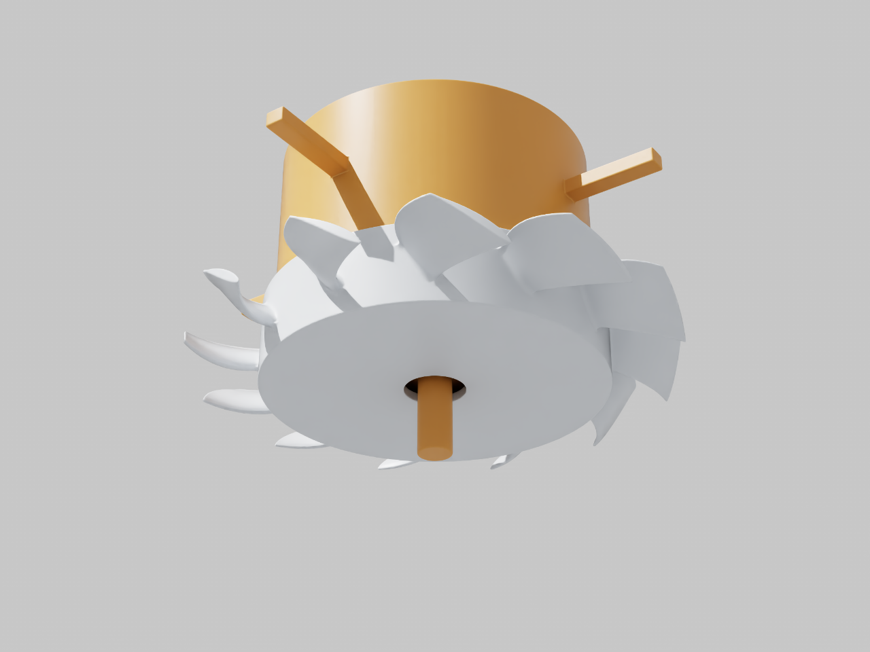
twins/993-engine-cooling-fan-system-f0/results/omniverse/assembly.png
