cluster2600/porscheparts/twins/picogk-station-demo/qualification/build/station-demo-cpu/coupon-thin/station-coupon-thin-lpbf-geometry-screen.png

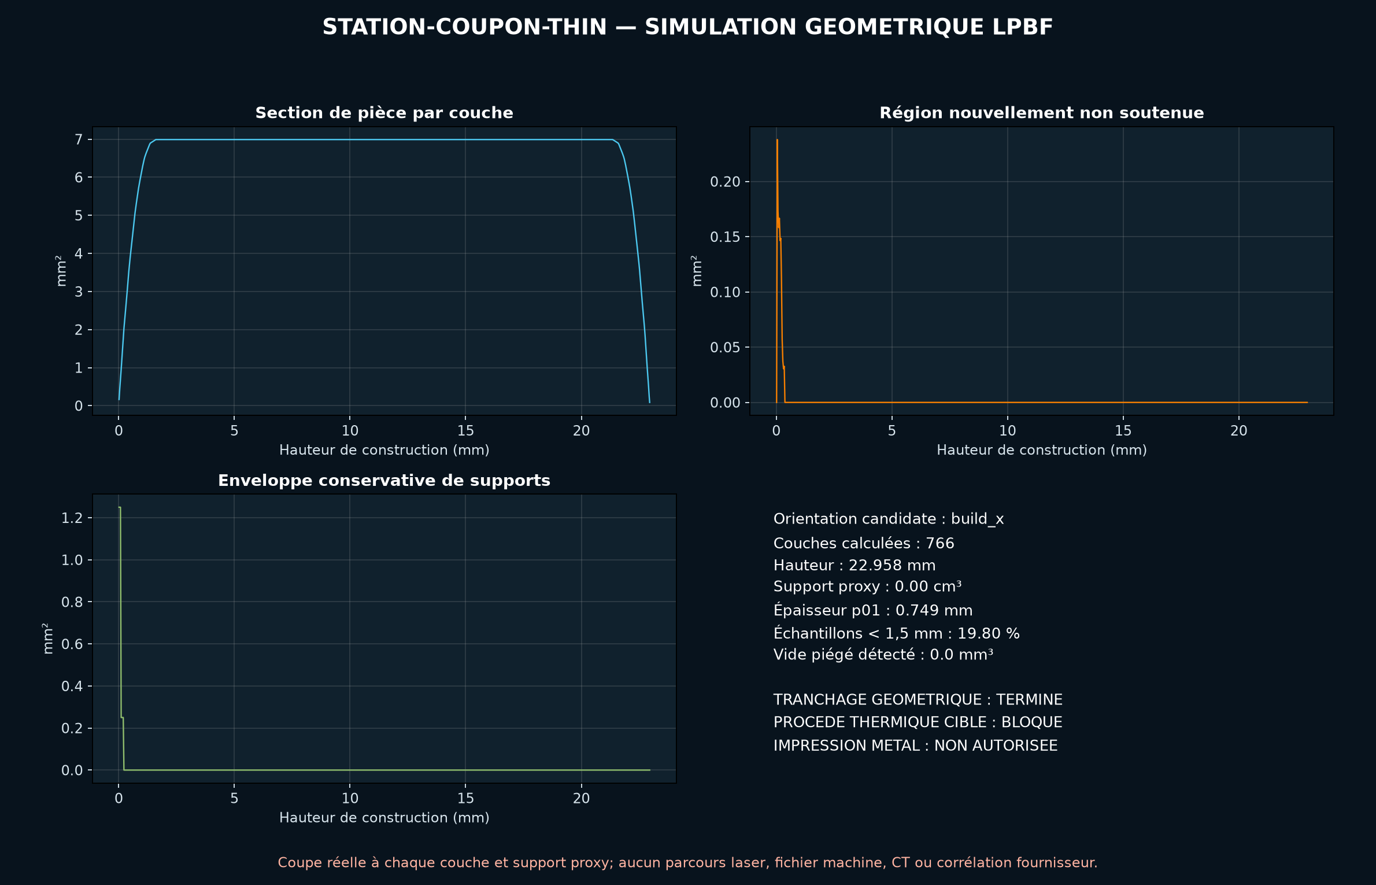
twins/picogk-station-demo/qualification/build/station-demo-cpu/coupon-thin/station-coupon-thin-lpbf-geometry-screen.png
