cluster2600/porscheparts/twins/reference-917-engine/evidence/f50-additive-print/additivefoam-coupons/917-head-f50-additivefoam-coupons.png

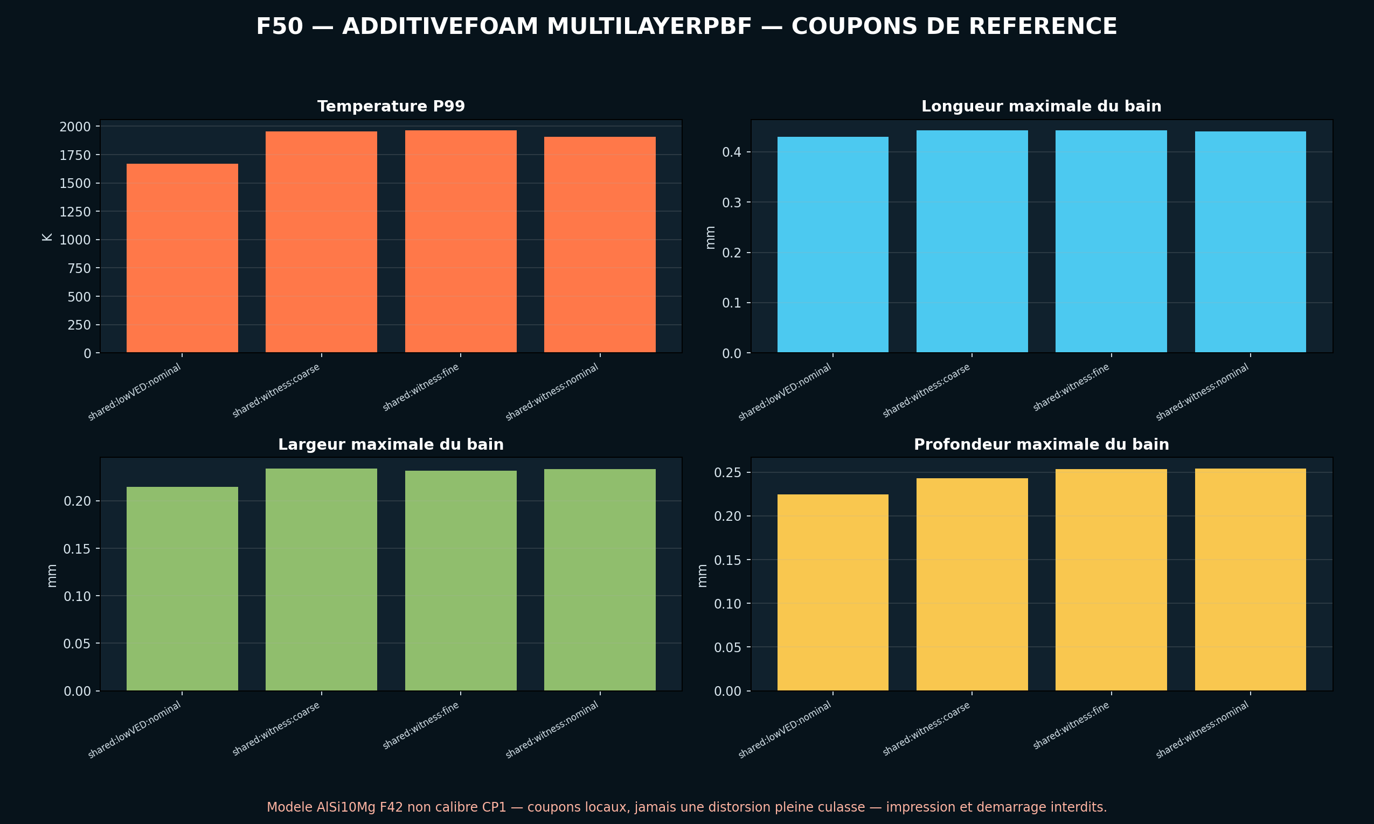
twins/reference-917-engine/evidence/f50-additive-print/additivefoam-coupons/917-head-f50-additivefoam-coupons.png
