cluster2600/porscheparts/twins/reference-917-engine/evidence/f50-additive-print/geometry-2v/917-head-f50-2v-lpbf-geometry-audit.png

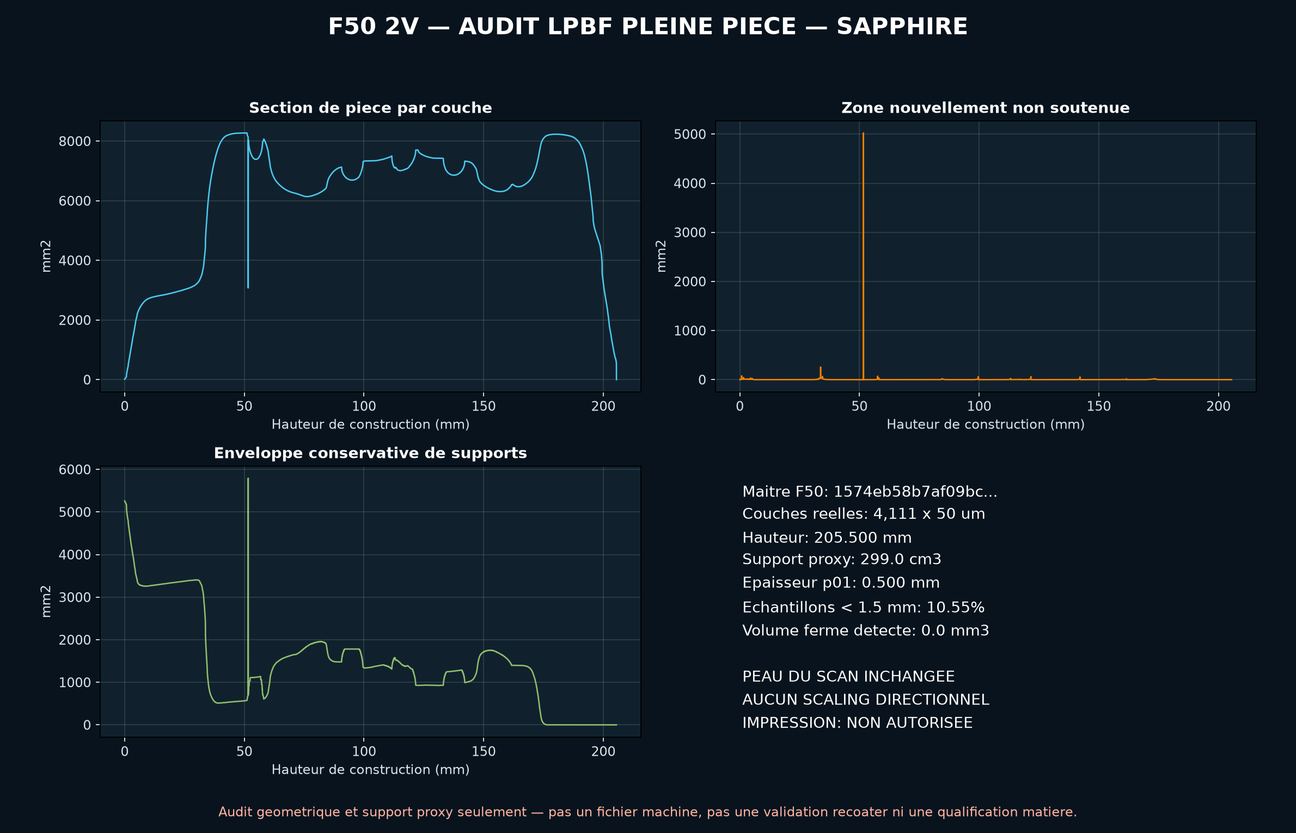
twins/reference-917-engine/evidence/f50-additive-print/geometry-2v/917-head-f50-2v-lpbf-geometry-audit.png
