cluster2600/porscheparts/twins/reference-917-engine/evidence/f50-additive-print/media/917-head-f50-lpbf-process-dashboard.png

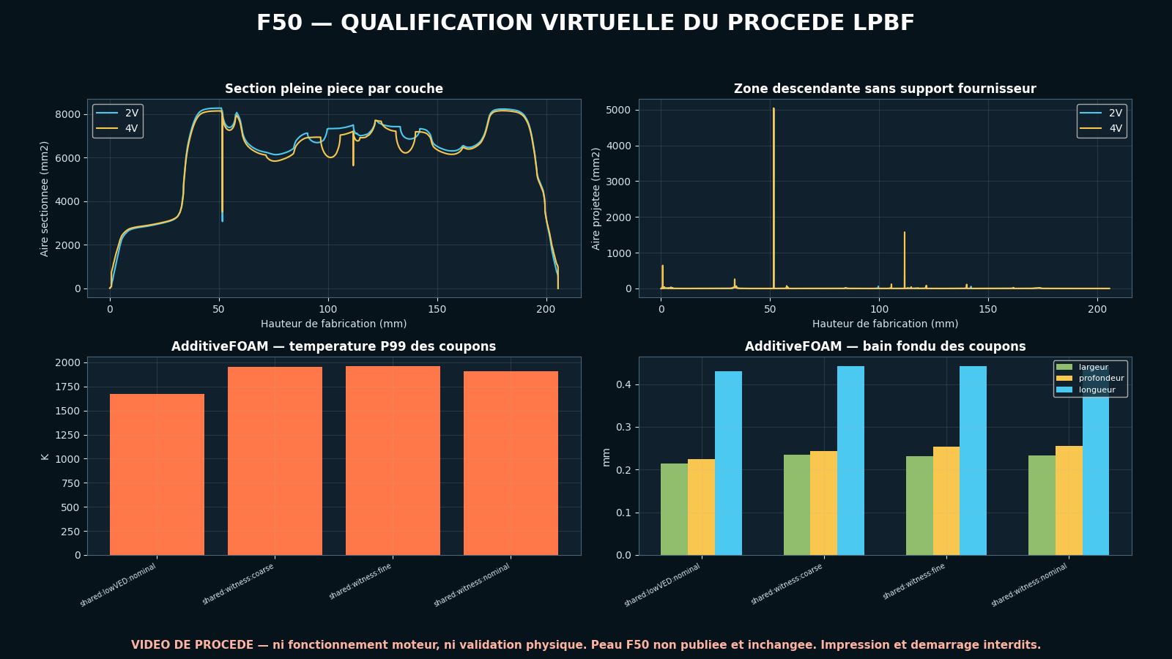
twins/reference-917-engine/evidence/f50-additive-print/media/917-head-f50-lpbf-process-dashboard.png
