cluster2600/porscheparts/catalog/templates/measurement-plan.md

# Measurement plan — PART_ID

## Purpose

- Part:
- Porsche part number:
- Variant and year:
- Vehicle or part measured:
- Owner:
- Date:

## Instruments

| Instrument | Range | Resolution | Known calibration |
|---|---:|---:|---|
| Caliper | | | |

## Datums

Define the origin, the axes and the reference planes. Add a photograph or a
diagram carrying the same identifiers as the measurements.

## Critical dimensions

| ID | Description | Value mm | Uncertainty mm | Method | Repeats |
|---|---|---:|---:|---|---:|
| D01 | | | | | 3 |

## Interfaces

- Holes, axes and threads:
- Contact planes:
- Functional clearances:
- Neighboring parts:
- Motion or travel:

## 3D acquisition

- Method:
- Scale or reference bars:
- Lighting and surface conditions:
- Raw format:
- Alignment and cleanup:
- Scan vs. critical measurement deviation:

## Result

- Measurements accepted: yes / no
- Contradictions:
- Missing measurements:
- Evidence files:
