cluster2600/porscheparts/training/qwen-metal-additive-20261002/runs/qwen3-condition-development-001/RESULTS.md

# Condition fidelity v12: rejected during development

The first answer still merges room-temperature quasi-static strength with
elevated-temperature stress rupture. Other generated retired development
answers are retained, but no completed-development score is claimed. The run
was stopped after the scientific error. No fidelity final prediction was
generated. Independent scientific/translation review remains pending.
