cluster2600/porscheparts/training/qwen-metal-additive-20261002/runs/qwen3-fidelity-development-001/RESULTS.md

# Fidelity profile v11: rejected during development

Three retired development answers were generated, before any fidelity final
prediction. The second answer conflates room-temperature quasi-static strength
with elevated-temperature stress rupture and introduces fatigue without source
support. The run was stopped and rejected. Raw partial work is retained.
These development prompts were already retired. The third registered final and
supplemental benchmark remain untouched. Independent expert review is pending.
