cluster2600/porscheparts/containers/m64-leap71/geometry-qa-requirements.txt

# Python 3.11 on Debian 12; top-level versions fixed, resolved transitive
# versions recorded in /opt/provenance/geometry-qa-resolved.txt.
numpy==2.3.5
scipy==1.16.3
trimesh==5.1.0
rtree==1.4.1
networkx==3.6.1
matplotlib==3.11.1
pyvista==0.48.4
vtk==9.6.2
