cluster2600/porscheparts/training/qwen-metal-additive-20261002/runs/qwen3-precision-development-001/RESULTS.md

# Precision SFT: rejected on development

Actual Qwen3 4B CPU BF16 LoRA trained 59 factual examples across seven languages,
30 optimizer steps and one epoch in 1642.87 seconds. Mean training loss:2.15966.
The 144 tensors (2,949,120 parameters) are finite and all72 LoRA B tensors are
nonzero. Adapter SHA-256:39dc305a84989261236e62edb1e818c4fc57dd86324ed1bf8c6c736184d7422e.

Despite lower training loss, development answers are less useful: several
become bare refusals and the model selects deposited height instead of substrate
thickness. These raw outputs are retained. This candidate is rejected; no
response on the newly registered precision final or domain tests was generated.
The earlier retired tests used here are development only, and three retired
training-family paragraphs enter the correction curriculum. No source-held-out
article or new test paragraph enters SFT.

A change in learning rate and curriculum accompanies this result; this does
not isolate either as the cause. Independent scientific/translation review is
pending. This trial is not recommended and does not qualify a physical part.
