cluster2600/porscheparts/training/qwen-metal-additive-20261002/runs/qwen3-quote-development-001/RESULTS.md

# Quote-first v13: rejected during development

The known Laves question produces an incomplete passage copy at the 192-token
limit, without a French answer or final citation. The run is stopped and
rejected. Other generated retired answers are retained, but no completed
development or final score is claimed. Fidelity final remains untouched.
Independent scientific/translation review is pending.
