cluster2600/porscheparts/training/qwen-metal-additive-20261002/runs/qwen3-source-profile-001/RESULTS.md

# Source profile: rejected early

The unchanged conservative Qwen3 adapter was evaluated with source-v10 after
passing twelve retired development questions. Twelve paired base predictions
and two adapter primary predictions were generated. Both adapter answers add
unsupported restrictions or property comparisons. With two primary failures,
the registered requirement of at least 11/12 is already impossible. The run was
stopped; no supplemental prediction was generated. No full-test score is claimed.

Raw partial files and the frozen selection are retained. The entire registered
precision benchmark is excluded from subsequent final evaluation. These two
failed questions and a third failed base question enter later development only.
Independent scientific/translation review remains pending.
