cluster2600/porscheparts/models/horizontal-fan-reconstruction/results/lpbf/R0-upright-layers.csv

layer | z_mm | cross_section_area_mm2 | intersection_segments
0 | 0.025 | 2822.5792477858936 | 245
1 | 0.07500000000000001 | 2820.85283868236 | 245
2 | 0.12500000000000003 | 2819.1255772643003 | 245
3 | 0.17500000000000004 | 2817.397463531713 | 245
4 | 0.22500000000000003 | 2815.6684974845994 | 245
5 | 0.275 | 2813.938679122959 | 245
6 | 0.32500000000000007 | 2812.2080084467925 | 245
7 | 0.37500000000000006 | 2810.4764854560976 | 245
8 | 0.4250000000000001 | 2808.744110150878 | 245
9 | 0.4750000000000001 | 2807.01088253113 | 245
10 | 0.5250000000000001 | 2805.2768025968553 | 245
11 | 0.5750000000000001 | 2803.5418703480545 | 245
12 | 0.6250000000000001 | 2801.806085784726 | 245
13 | 0.6750000000000002 | 2800.069448906872 | 245
14 | 0.7250000000000001 | 2798.3319597144896 | 245
15 | 0.7750000000000001 | 2796.5936182075816 | 245
16 | 0.8250000000000002 | 2794.854424386145 | 245
17 | 0.8750000000000002 | 2793.114378250185 | 245
18 | 0.9250000000000002 | 2791.3734797996963 | 245
19 | 0.9750000000000002 | 2789.6317290346797 | 245
20 | 1.0250000000000001 | 2787.8891259551383 | 245
21 | 1.0750000000000002 | 2786.1456705610685 | 245
22 | 1.1250000000000002 | 2784.401362852473 | 245
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
