cluster2600/porscheparts/simulation/m64-virtual-bench/results/sweep_partload.csv

rpm | thr | pr | p_man_pa | t_man_k | rho_man_kg_m3 | ve | m_dot_air_kg_s | m_dot_air_per_turbo_kg_s | flow_anchor_check | m_dot_fuel_kg_s | p_chem_kw | eta_brake | power_kw | torque_nm | bsfc_g_kwh | bmep_bar | t2_actual_k | w_comp_shaft_total_kw | q_intercooler_kw_per_turbo | intercooler_effectiveness | q_cooling_air_kw | q_oil_kw | q_exhaust_kw | fan_mass_flow_kg_s | fan_flow_l_s | cooling_air_dt_k | cooling_air_dt_implied_k | cooling_air_exergy_destroyed_kw | bank_metal_rise_k | oil_flow_required_l_min | oil_flow_available_assumed_l_min | oil_flow_headroom_l_min | oil_pump_shaft_w_assumed | ignition_w | injection_w | starter_w | total_electrical_w | p_accessory_kw | p_trans_loss_kw | p_wheel_kw | driveline_efficiency
1500 | 0.25 | 1.01875 | 103225 | 303.269 | 1.18577 | 0.83 | 0.0442884 | 0.0221442 | 0.14195 | 0.00301281 | 132.564 | 0.186323 | 24.6996 | 157.243 | 439.121 | 5.48881 | 305.632 | 0.11047 | 0.0111678 | 0.808745 | 39.7692 | 13.2564 | 72.9101 | 0.289191 | 248.361 | 23.6393 | 228.058 | 2.87683 | 23.6393 | 14.4 | 82.1667 | 67.7667 | 106.667 | 66.0345 | 92.5785 | 0 | 158.613 | 0.55 | 0.721289 | 23.3217 | 0.944211
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
