cluster2600/porscheparts/simulation/m64-virtual-bench/results/sweep_wot.csv

rpm | thr | pr | p_man_pa | t_man_k | rho_man_kg_m3 | ve | m_dot_air_kg_s | m_dot_air_per_turbo_kg_s | flow_anchor_check | m_dot_fuel_kg_s | p_chem_kw | eta_brake | power_kw | torque_nm | bsfc_g_kwh | bmep_bar | t2_actual_k | w_comp_shaft_total_kw | q_intercooler_kw_per_turbo | intercooler_effectiveness | q_cooling_air_kw | q_oil_kw | q_exhaust_kw | fan_mass_flow_kg_s | fan_flow_l_s | cooling_air_dt_k | cooling_air_dt_implied_k | cooling_air_exergy_destroyed_kw | bank_metal_rise_k | oil_flow_required_l_min | oil_flow_available_assumed_l_min | oil_flow_headroom_l_min | oil_pump_shaft_w_assumed | ignition_w | injection_w | starter_w | total_electrical_w | p_accessory_kw | p_trans_loss_kw | p_wheel_kw | driveline_efficiency
1000 | 1 | 1 | 101325 | 303.15 | 1.1644 | 0.78 | 0.0272469 | 0.0136235 | 0.0873299 | 0.00227058 | 99.9054 | 0.144984 | 14.4847 | 138.319 | 564.324 | 4.82824 | 303.15 | 0 | 0 | 0 | 29.9716 | 9.99054 | 54.9479 | 0.192794 | 165.574 | 22 | 257.81 | 2.02791 | 22 | 14.4 | 66.3333 | 51.9333 | 106.667 | 60 | 91.9433 | 0 | 151.943 | 0.3 | 0.422342 | 13.6557 | 0.942767
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
