cluster2600/porscheparts/docs/media/diagrams/m64-validation.png

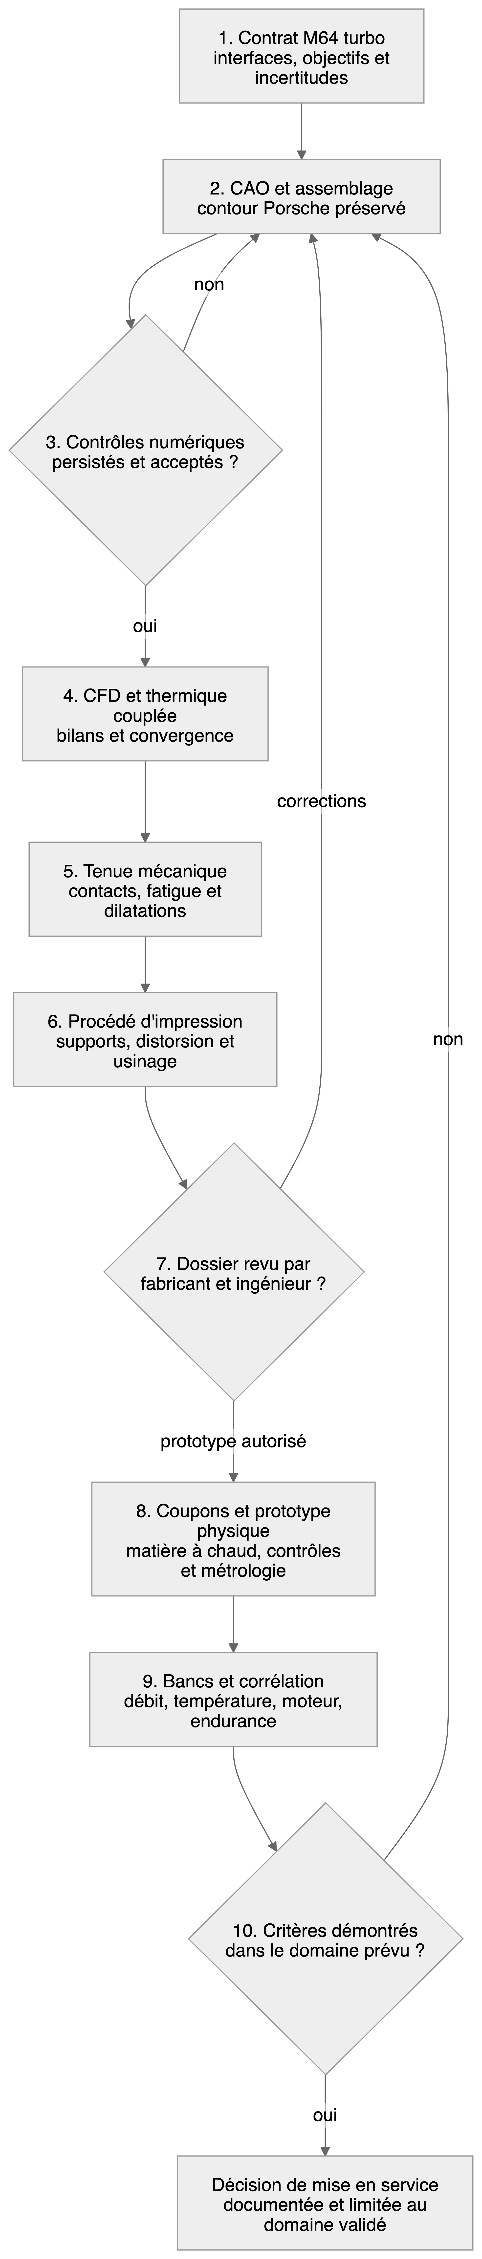
docs/media/diagrams/m64-validation.png
