cluster2600/porscheparts/twins/993-engine-cooling-fan-system-f0/results/omniverse/rotation-17ms.png

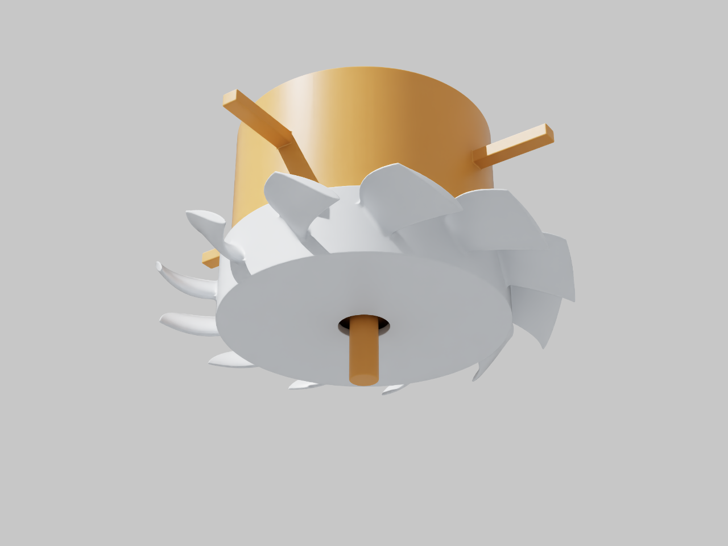
twins/993-engine-cooling-fan-system-f0/results/omniverse/rotation-17ms.png
