cluster2600/porscheparts/twins/993-engine-cooling-fan-system-f0/results/organic/flow/e-coarse/velocity-plane.png

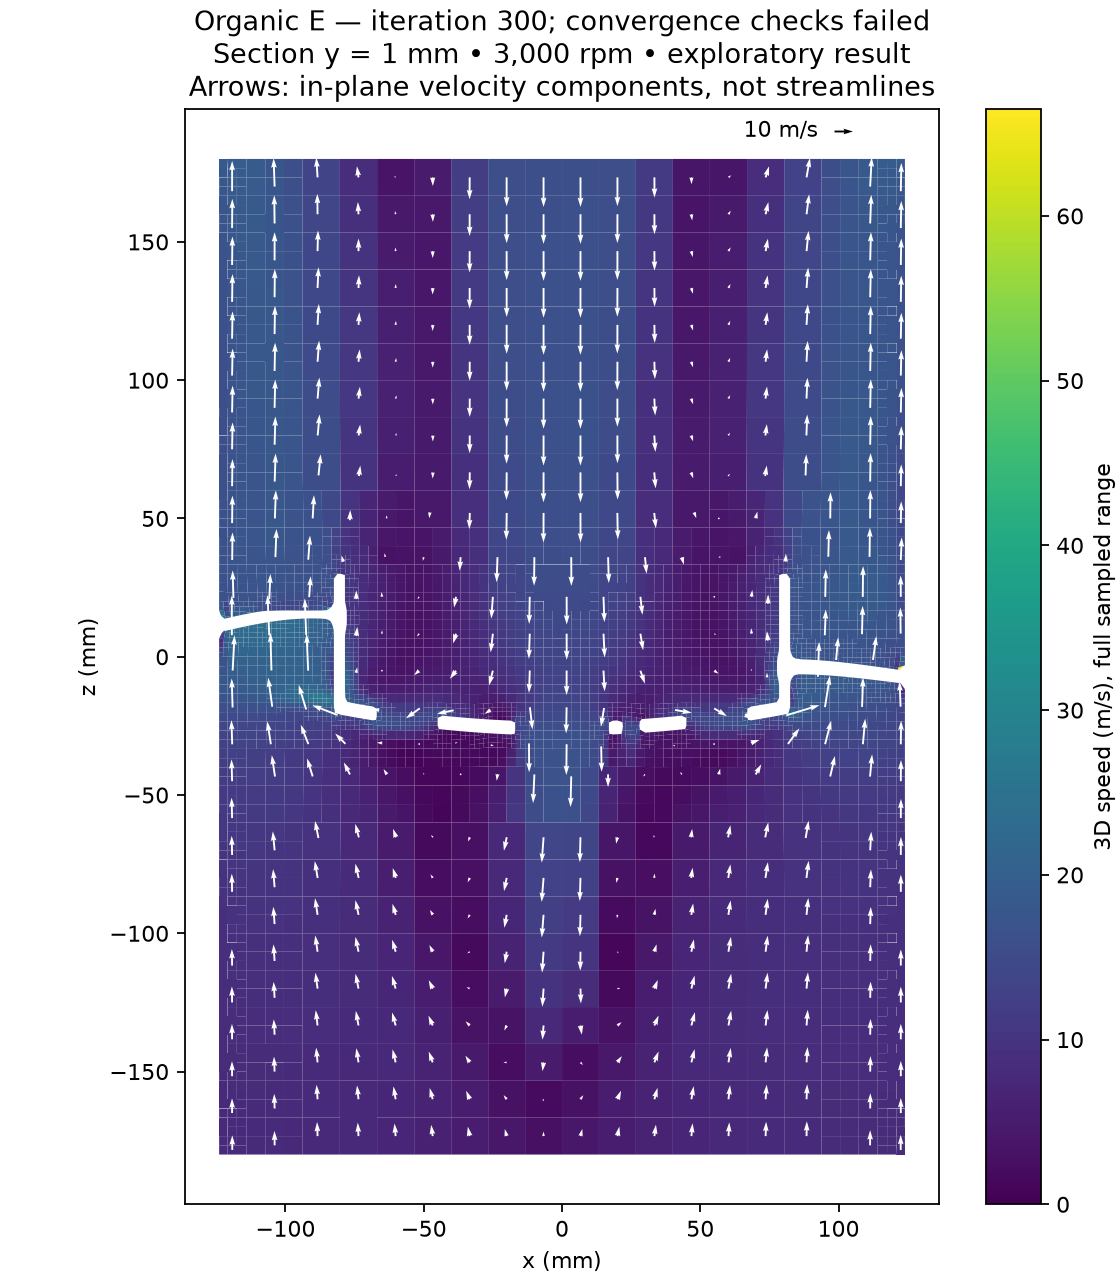
twins/993-engine-cooling-fan-system-f0/results/organic/flow/e-coarse/velocity-plane.png
