cluster2600/porscheparts/twins/993-engine-cooling-fan-system-f0/results/organic/study-results.png

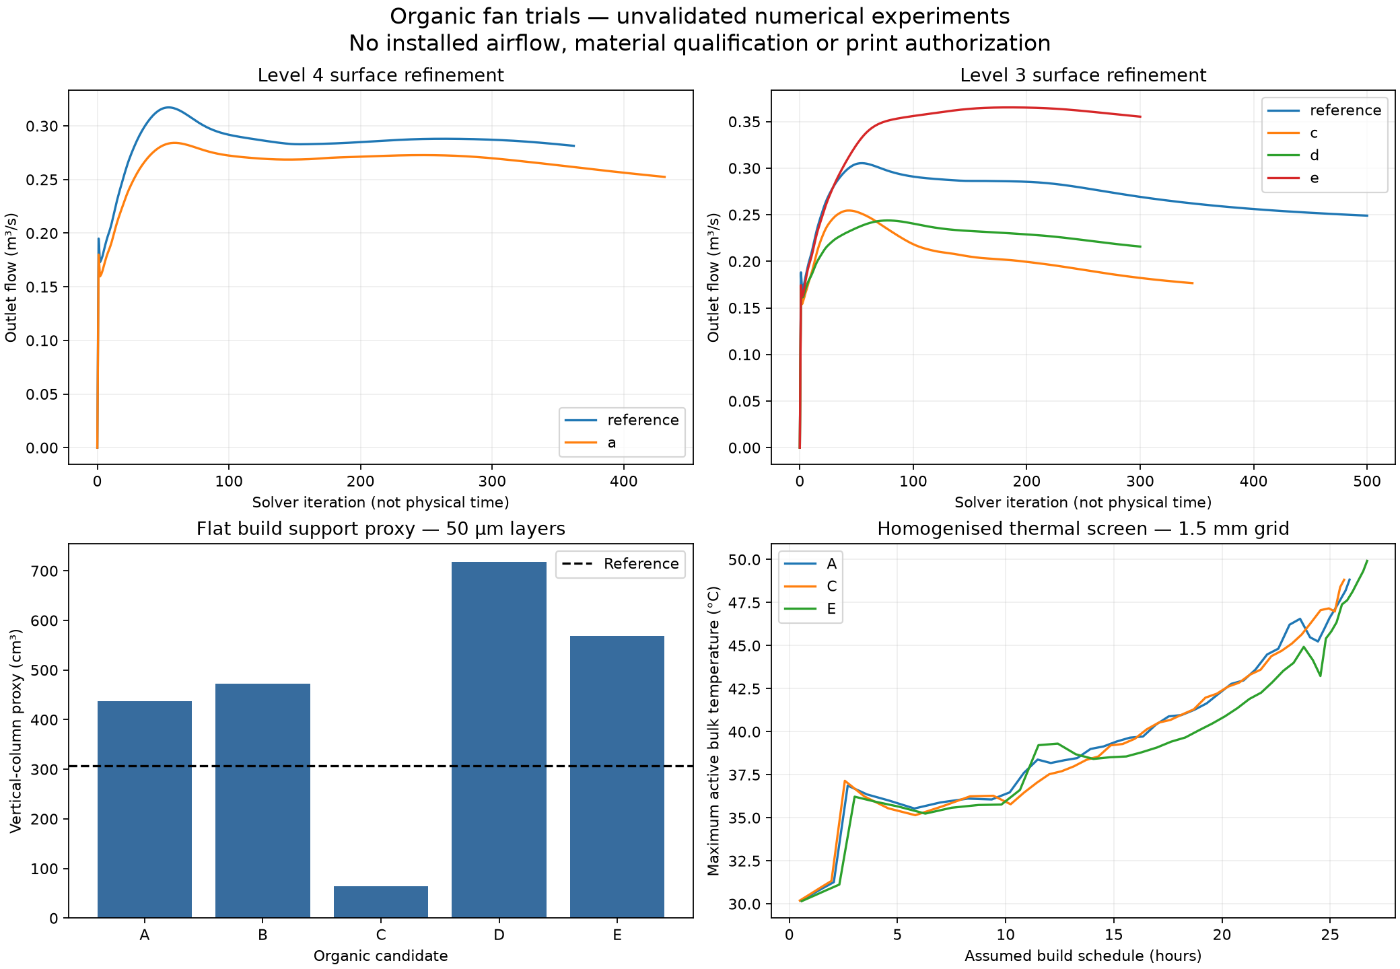
twins/993-engine-cooling-fan-system-f0/results/organic/study-results.png
