cluster2600/porscheparts/docs/projects/993-programmable-rear-panel/electronics/kicad/coupon-e0.kicad_sch

## KiCad design docs/projects/993-programmable-rear-panel/electronics/kicad/coupon-e0.kicad_sch (2026-10-04)

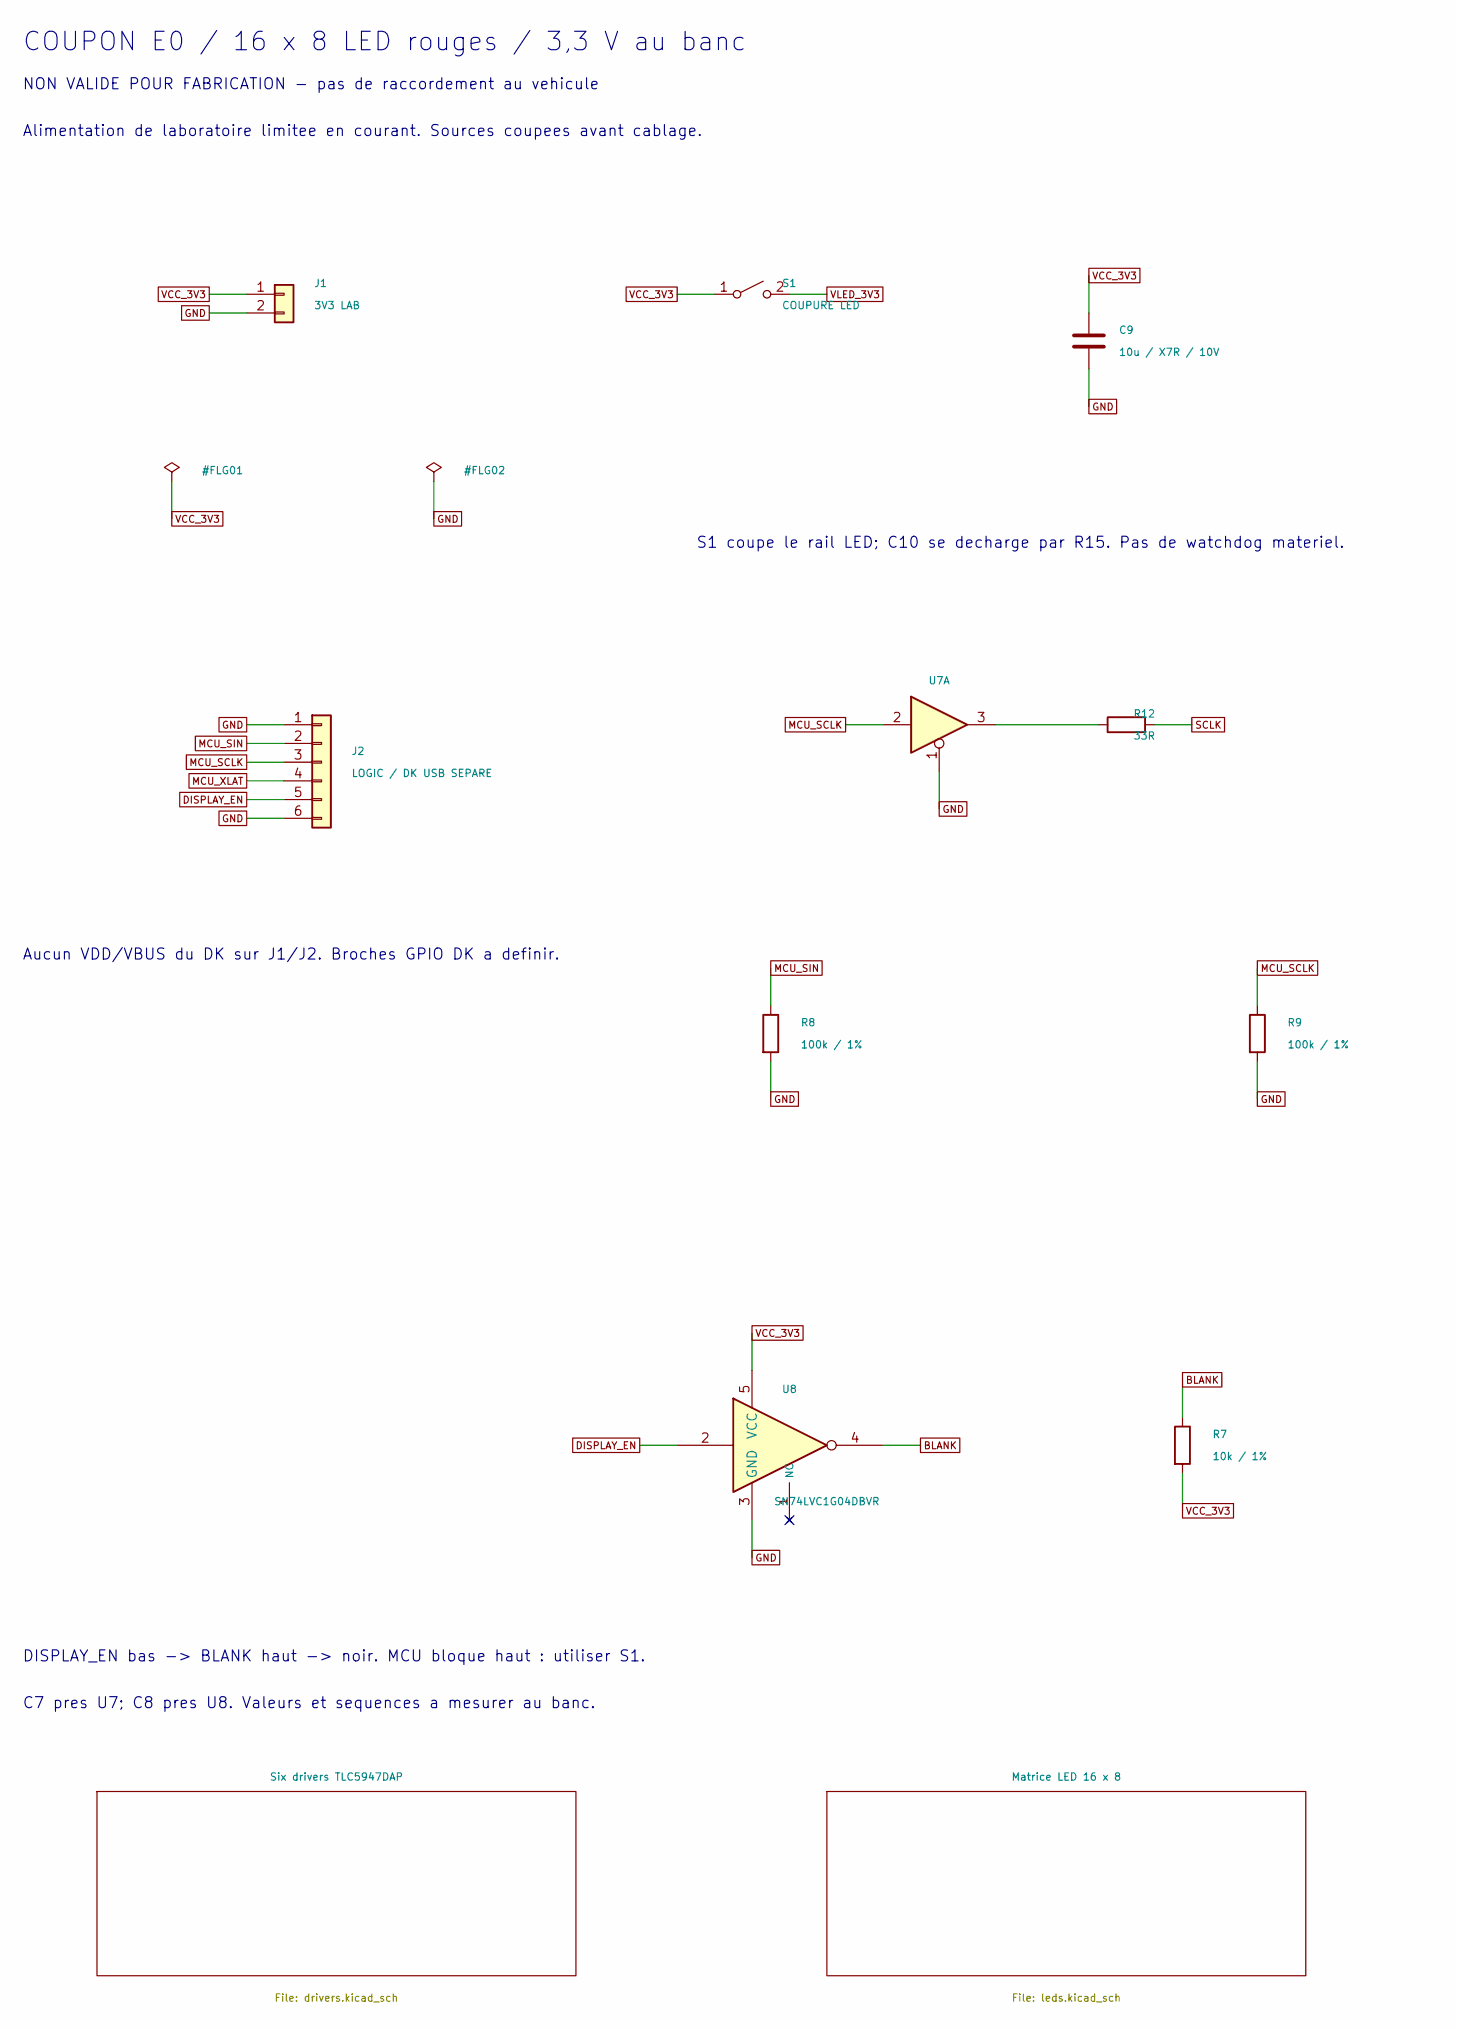
[picture p382: schematic coupon-e0.kicad_sch, part in row 1, column 1]

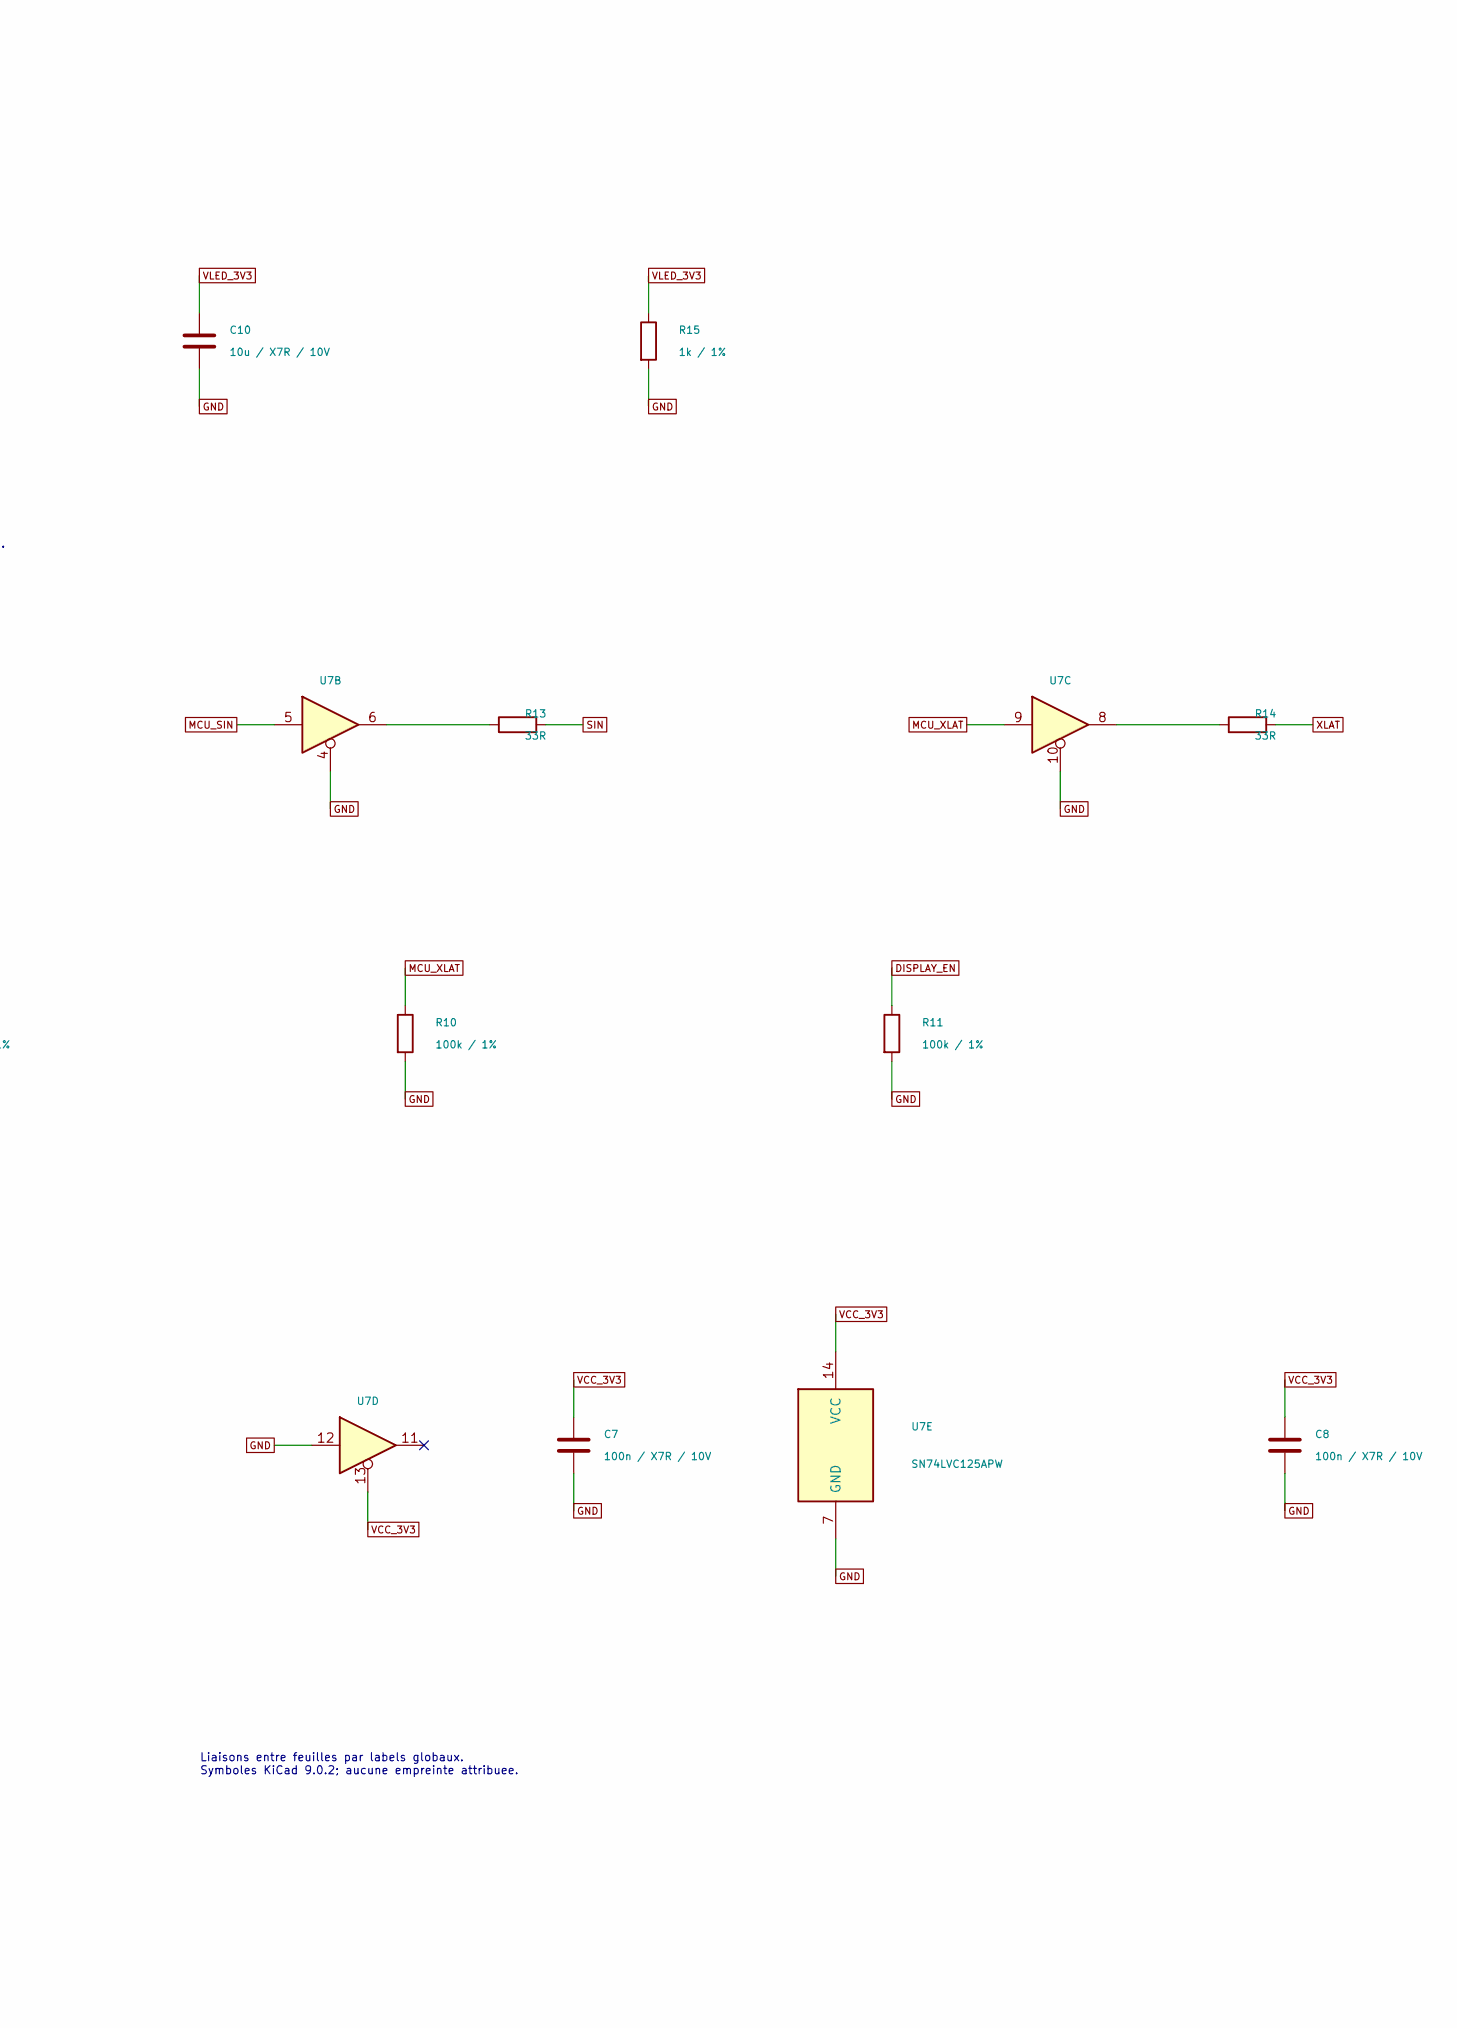
[picture p383: schematic coupon-e0.kicad_sch, part in row 1, column 2]

Parts:
C7, C8: 100n / X7R / 10V
C9, C10: 10u / X7R / 10V
J1: 3V3 LAB
J2: LOGIC / DK USB SEPARE
R7: 10k / 1%
R8, R9, R10, R11: 100k / 1%
R12, R13, R14: 33R
R15: 1k / 1%
S1: COUPURE LED
U7: SN74LVC125APW
U8: SN74LVC1G04DBVR

Connections:
BLANK: R7.1, U8.4
DISPLAY_EN: J2.5, R11.1, U8.2
GND: C7.2, C8.2, C9.2, C10.2, J1.2, J2.1, J2.6, R8.2, R9.2, R10.2, R11.2, R15.2, U7.1, U7.4, U7.7 (GND), U7.10, U7.12, U8.3 (GND)
MCU_SCLK: J2.3, R9.1, U7.2
MCU_SIN: J2.2, R8.1, U7.5
MCU_XLAT: J2.4, R10.1, U7.9
unnamed: R12.1, U7.3
unnamed: R13.1, U7.6
unnamed: R14.1, U7.8
SCLK: R12.2
SIN: R13.2
VCC_3V3: C7.1, C8.1, C9.1, J1.1, R7.2, S1.1 (A), U7.13, U7.14 (VCC), U8.5 (VCC)
VLED_3V3: C10.1, R15.1, S1.2 (B)
XLAT: R14.2

Notes on the sheet:
COUPON E0 / 16 x 8 LED rouges / 3,3 V au banc
NON VALIDE POUR FABRICATION - pas de raccordement au vehicule
Alimentation de laboratoire limitee en courant. Sources coupees avant cablage.
S1 coupe le rail LED; C10 se decharge par R15. Pas de watchdog materiel.
Aucun VDD/VBUS du DK sur J1/J2. Broches GPIO DK a definir.
DISPLAY_EN bas -> BLANK haut -> noir. MCU bloque haut : utiliser S1.
C7 pres U7; C8 pres U8. Valeurs et sequences a mesurer au banc.
Liaisons entre feuilles par labels globaux. Symboles KiCad 9.0.2; aucune empreinte attribuee.
