cluster2600/porscheparts/docs/projects/993-programmable-rear-panel/electronics/kicad/drivers.kicad_sch

## KiCad design docs/projects/993-programmable-rear-panel/electronics/kicad/drivers.kicad_sch (2026-10-04)

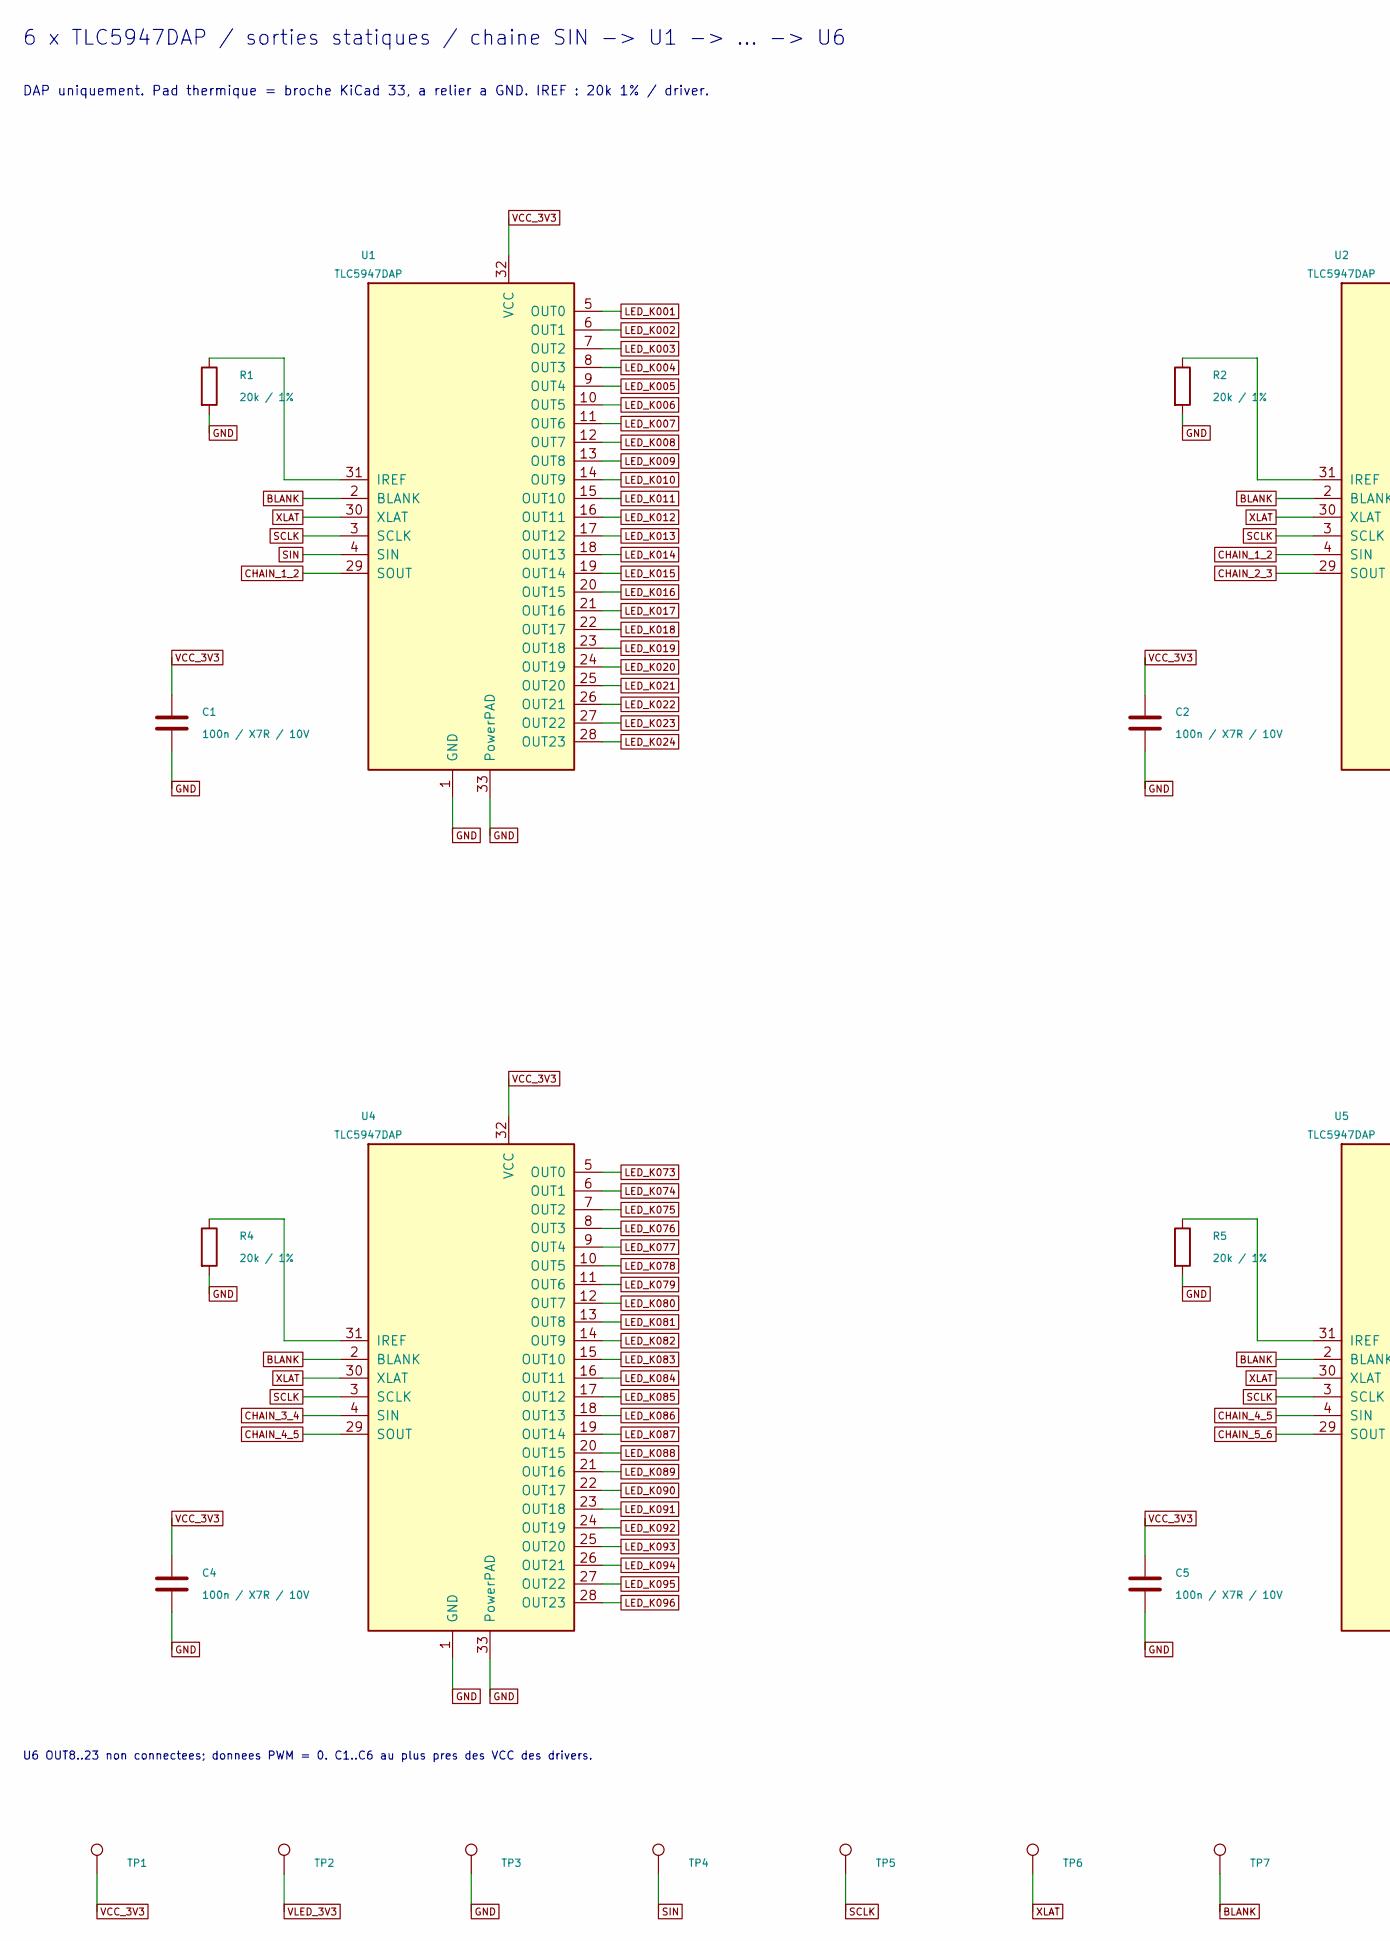
[picture p384: schematic drivers.kicad_sch, part in row 1, column 1]

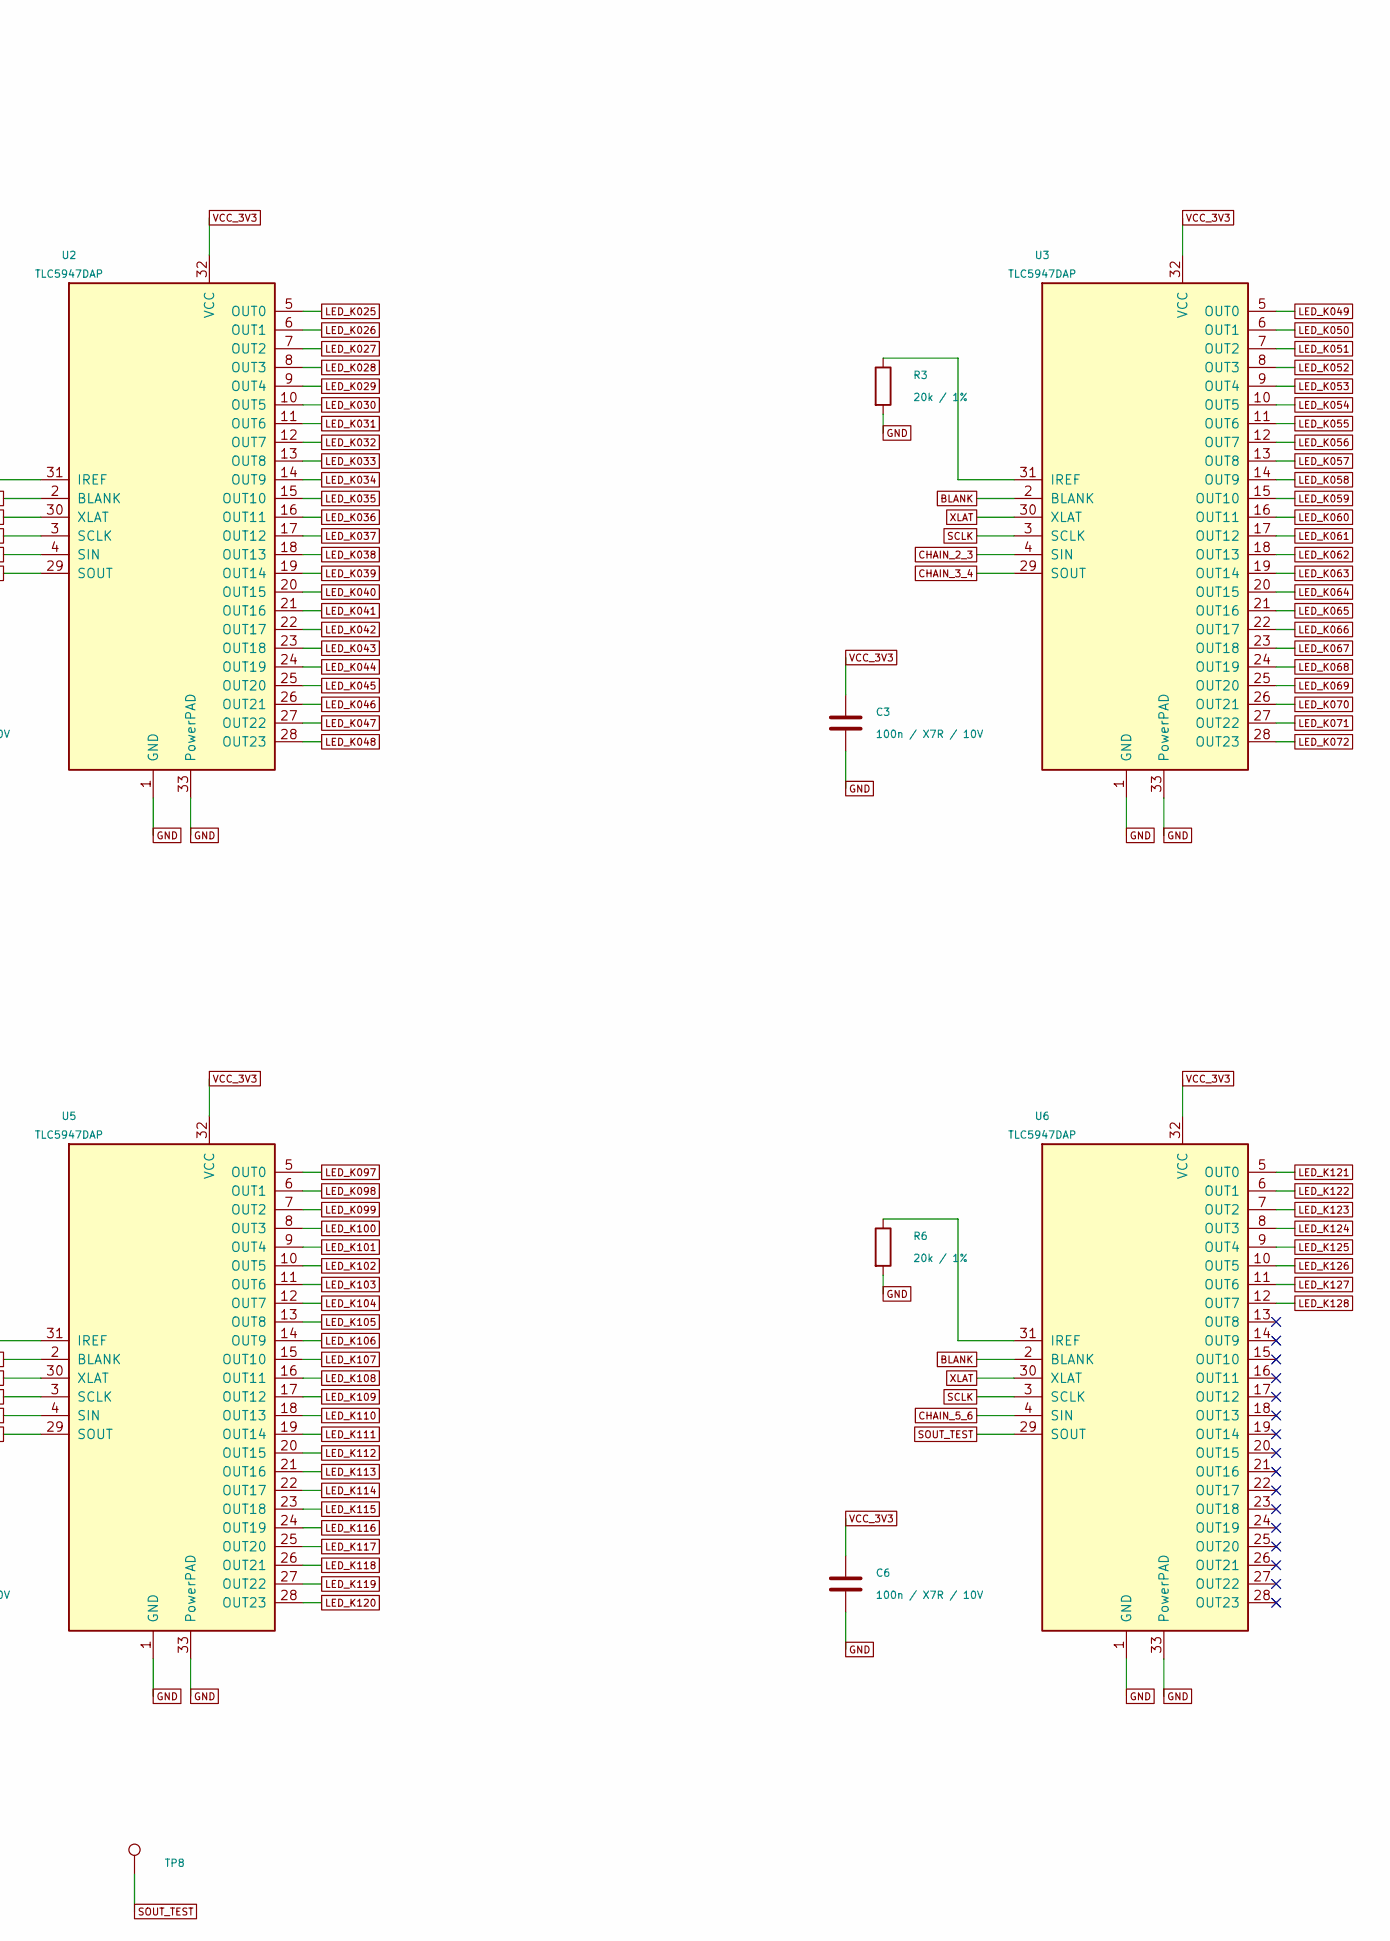
[picture p385: schematic drivers.kicad_sch, part in row 1, column 2]

Parts:
C1, C2, C3, C4, C5, C6: 100n / X7R / 10V
R1, R2, R3, R4, R5, R6: 20k / 1%
TP1: VCC_3V3
TP2: VLED_3V3
TP3: GND
TP4: SIN
TP5: SCLK
TP6: XLAT
TP7: BLANK
TP8: SOUT_TEST
U1, U2, U3, U4, U5, U6: TLC5947DAP

Connections:
BLANK: TP7.1, U1.2 (BLANK), U2.2 (BLANK), U3.2 (BLANK), U4.2 (BLANK), U5.2 (BLANK), U6.2 (BLANK)
CHAIN_1_2: U1.29 (SOUT), U2.4 (SIN)
CHAIN_2_3: U2.29 (SOUT), U3.4 (SIN)
CHAIN_3_4: U3.29 (SOUT), U4.4 (SIN)
CHAIN_4_5: U4.29 (SOUT), U5.4 (SIN)
CHAIN_5_6: U5.29 (SOUT), U6.4 (SIN)
GND: C1.2, C2.2, C3.2, C4.2, C5.2, C6.2, R1.2, R2.2, R3.2, R4.2, R5.2, R6.2, TP3.1, U1.1 (GND), U1.33 (PowerPAD), U2.1 (GND), U2.33 (PowerPAD), U3.1 (GND), U3.33 (PowerPAD), U4.1 (GND), U4.33 (PowerPAD), U5.1 (GND), U5.33 (PowerPAD), U6.1 (GND), U6.33 (PowerPAD)
LED_K001: U1.5 (OUT0)
LED_K002: U1.6 (OUT1)
LED_K003: U1.7 (OUT2)
LED_K004: U1.8 (OUT3)
LED_K005: U1.9 (OUT4)
LED_K006: U1.10 (OUT5)
LED_K007: U1.11 (OUT6)
LED_K008: U1.12 (OUT7)
LED_K009: U1.13 (OUT8)
LED_K010: U1.14 (OUT9)
LED_K011: U1.15 (OUT10)
LED_K012: U1.16 (OUT11)
LED_K013: U1.17 (OUT12)
LED_K014: U1.18 (OUT13)
LED_K015: U1.19 (OUT14)
LED_K016: U1.20 (OUT15)
LED_K017: U1.21 (OUT16)
LED_K018: U1.22 (OUT17)
LED_K019: U1.23 (OUT18)
LED_K020: U1.24 (OUT19)
LED_K021: U1.25 (OUT20)
LED_K022: U1.26 (OUT21)
LED_K023: U1.27 (OUT22)
LED_K024: U1.28 (OUT23)
LED_K025: U2.5 (OUT0)
LED_K026: U2.6 (OUT1)
LED_K027: U2.7 (OUT2)
LED_K028: U2.8 (OUT3)
LED_K029: U2.9 (OUT4)
LED_K030: U2.10 (OUT5)
LED_K031: U2.11 (OUT6)
LED_K032: U2.12 (OUT7)
LED_K033: U2.13 (OUT8)
LED_K034: U2.14 (OUT9)
LED_K035: U2.15 (OUT10)
LED_K036: U2.16 (OUT11)
LED_K037: U2.17 (OUT12)
LED_K038: U2.18 (OUT13)
LED_K039: U2.19 (OUT14)
LED_K040: U2.20 (OUT15)
LED_K041: U2.21 (OUT16)
LED_K042: U2.22 (OUT17)
LED_K043: U2.23 (OUT18)
LED_K044: U2.24 (OUT19)
LED_K045: U2.25 (OUT20)
LED_K046: U2.26 (OUT21)
LED_K047: U2.27 (OUT22)
LED_K048: U2.28 (OUT23)
LED_K049: U3.5 (OUT0)
LED_K050: U3.6 (OUT1)
LED_K051: U3.7 (OUT2)
LED_K052: U3.8 (OUT3)
LED_K053: U3.9 (OUT4)
LED_K054: U3.10 (OUT5)
LED_K055: U3.11 (OUT6)
LED_K056: U3.12 (OUT7)
LED_K057: U3.13 (OUT8)
LED_K058: U3.14 (OUT9)
LED_K059: U3.15 (OUT10)
LED_K060: U3.16 (OUT11)
LED_K061: U3.17 (OUT12)
LED_K062: U3.18 (OUT13)
LED_K063: U3.19 (OUT14)
LED_K064: U3.20 (OUT15)
LED_K065: U3.21 (OUT16)
LED_K066: U3.22 (OUT17)
LED_K067: U3.23 (OUT18)
LED_K068: U3.24 (OUT19)
LED_K069: U3.25 (OUT20)
LED_K070: U3.26 (OUT21)
LED_K071: U3.27 (OUT22)
LED_K072: U3.28 (OUT23)
LED_K073: U4.5 (OUT0)
LED_K074: U4.6 (OUT1)
LED_K075: U4.7 (OUT2)
LED_K076: U4.8 (OUT3)
LED_K077: U4.9 (OUT4)
LED_K078: U4.10 (OUT5)
LED_K079: U4.11 (OUT6)
LED_K080: U4.12 (OUT7)
LED_K081: U4.13 (OUT8)
LED_K082: U4.14 (OUT9)
LED_K083: U4.15 (OUT10)
LED_K084: U4.16 (OUT11)
LED_K085: U4.17 (OUT12)
LED_K086: U4.18 (OUT13)
LED_K087: U4.19 (OUT14)
LED_K088: U4.20 (OUT15)
LED_K089: U4.21 (OUT16)
LED_K090: U4.22 (OUT17)
LED_K091: U4.23 (OUT18)
LED_K092: U4.24 (OUT19)
LED_K093: U4.25 (OUT20)
LED_K094: U4.26 (OUT21)
LED_K095: U4.27 (OUT22)
LED_K096: U4.28 (OUT23)
LED_K097: U5.5 (OUT0)
LED_K098: U5.6 (OUT1)
LED_K099: U5.7 (OUT2)
LED_K100: U5.8 (OUT3)
LED_K101: U5.9 (OUT4)
LED_K102: U5.10 (OUT5)
LED_K103: U5.11 (OUT6)
LED_K104: U5.12 (OUT7)
LED_K105: U5.13 (OUT8)
LED_K106: U5.14 (OUT9)
LED_K107: U5.15 (OUT10)
LED_K108: U5.16 (OUT11)
LED_K109: U5.17 (OUT12)
LED_K110: U5.18 (OUT13)
LED_K111: U5.19 (OUT14)
LED_K112: U5.20 (OUT15)
LED_K113: U5.21 (OUT16)
LED_K114: U5.22 (OUT17)
LED_K115: U5.23 (OUT18)
LED_K116: U5.24 (OUT19)
LED_K117: U5.25 (OUT20)
LED_K118: U5.26 (OUT21)
LED_K119: U5.27 (OUT22)
LED_K120: U5.28 (OUT23)
LED_K121: U6.5 (OUT0)
LED_K122: U6.6 (OUT1)
LED_K123: U6.7 (OUT2)
LED_K124: U6.8 (OUT3)
LED_K125: U6.9 (OUT4)
LED_K126: U6.10 (OUT5)
LED_K127: U6.11 (OUT6)
LED_K128: U6.12 (OUT7)
unnamed: R1.1, U1.31 (IREF)
unnamed: R2.1, U2.31 (IREF)
unnamed: R3.1, U3.31 (IREF)
unnamed: R4.1, U4.31 (IREF)
unnamed: R5.1, U5.31 (IREF)
unnamed: R6.1, U6.31 (IREF)
SCLK: TP5.1, U1.3 (SCLK), U2.3 (SCLK), U3.3 (SCLK), U4.3 (SCLK), U5.3 (SCLK), U6.3 (SCLK)
SIN: TP4.1, U1.4 (SIN)
SOUT_TEST: TP8.1, U6.29 (SOUT)
VCC_3V3: C1.1, C2.1, C3.1, C4.1, C5.1, C6.1, TP1.1, U1.32 (VCC), U2.32 (VCC), U3.32 (VCC), U4.32 (VCC), U5.32 (VCC), U6.32 (VCC)
VLED_3V3: TP2.1
XLAT: TP6.1, U1.30 (XLAT), U2.30 (XLAT), U3.30 (XLAT), U4.30 (XLAT), U5.30 (XLAT), U6.30 (XLAT)

Notes on the sheet:
6 x TLC5947DAP / sorties statiques / chaine SIN -> U1 -> ... -> U6
DAP uniquement. Pad thermique = broche KiCad 33, a relier a GND. IREF : 20k 1% / driver.
U6 OUT8..23 non connectees; donnees PWM = 0. C1..C6 au plus pres des VCC des drivers.
