cluster2600/porscheparts/docs/projects/993-programmable-rear-panel/electronics/kicad/leds.kicad_sch

## KiCad design docs/projects/993-programmable-rear-panel/electronics/kicad/leds.kicad_sch (2026-10-04)

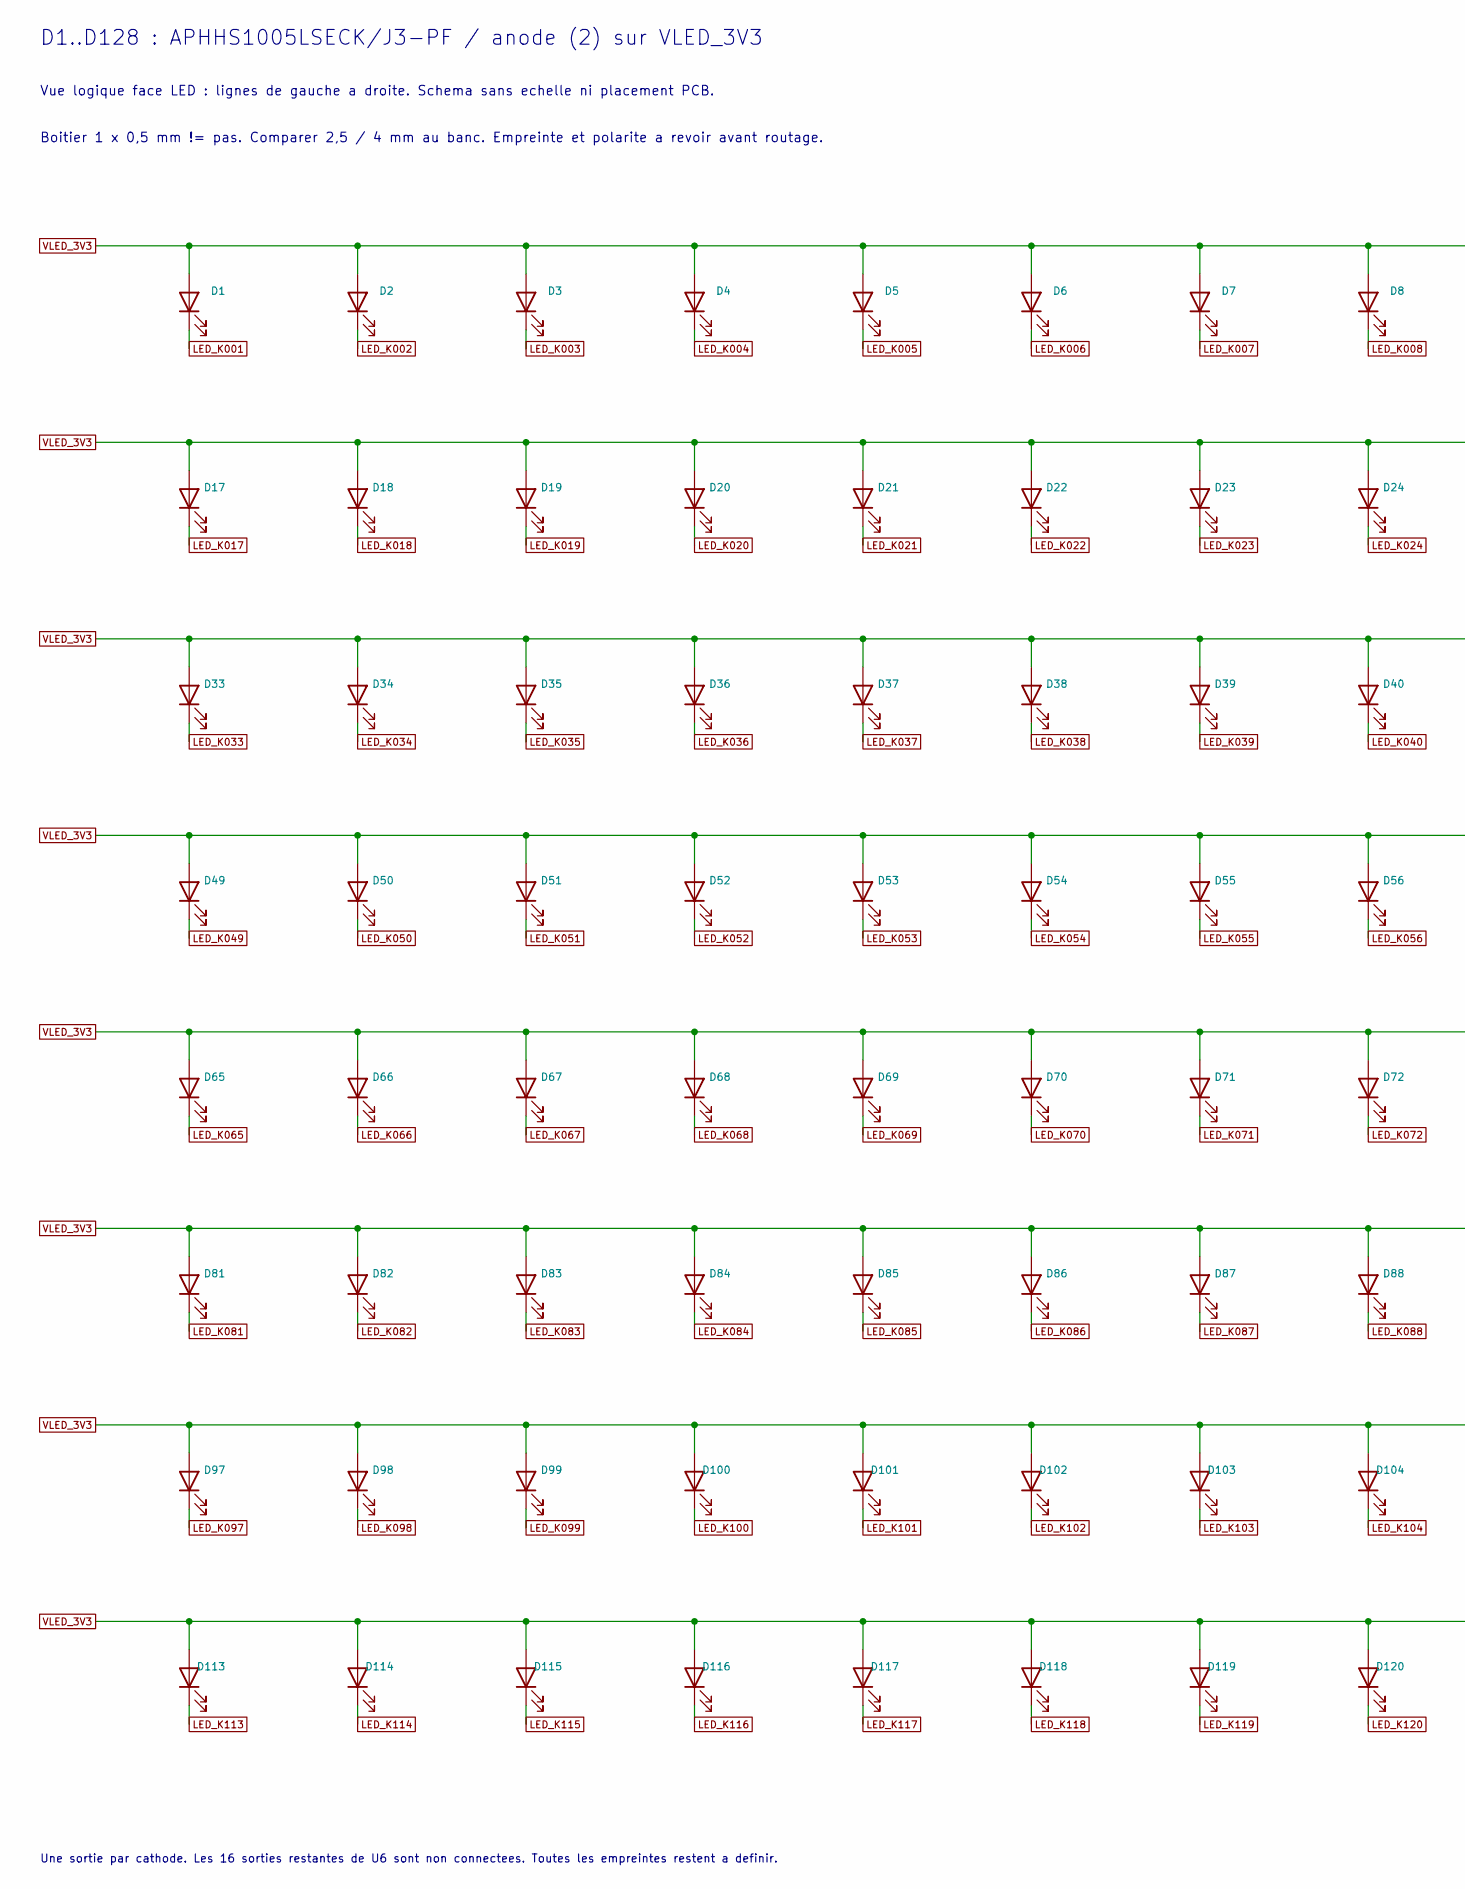
[picture p386: schematic leds.kicad_sch, part in row 1, column 1]

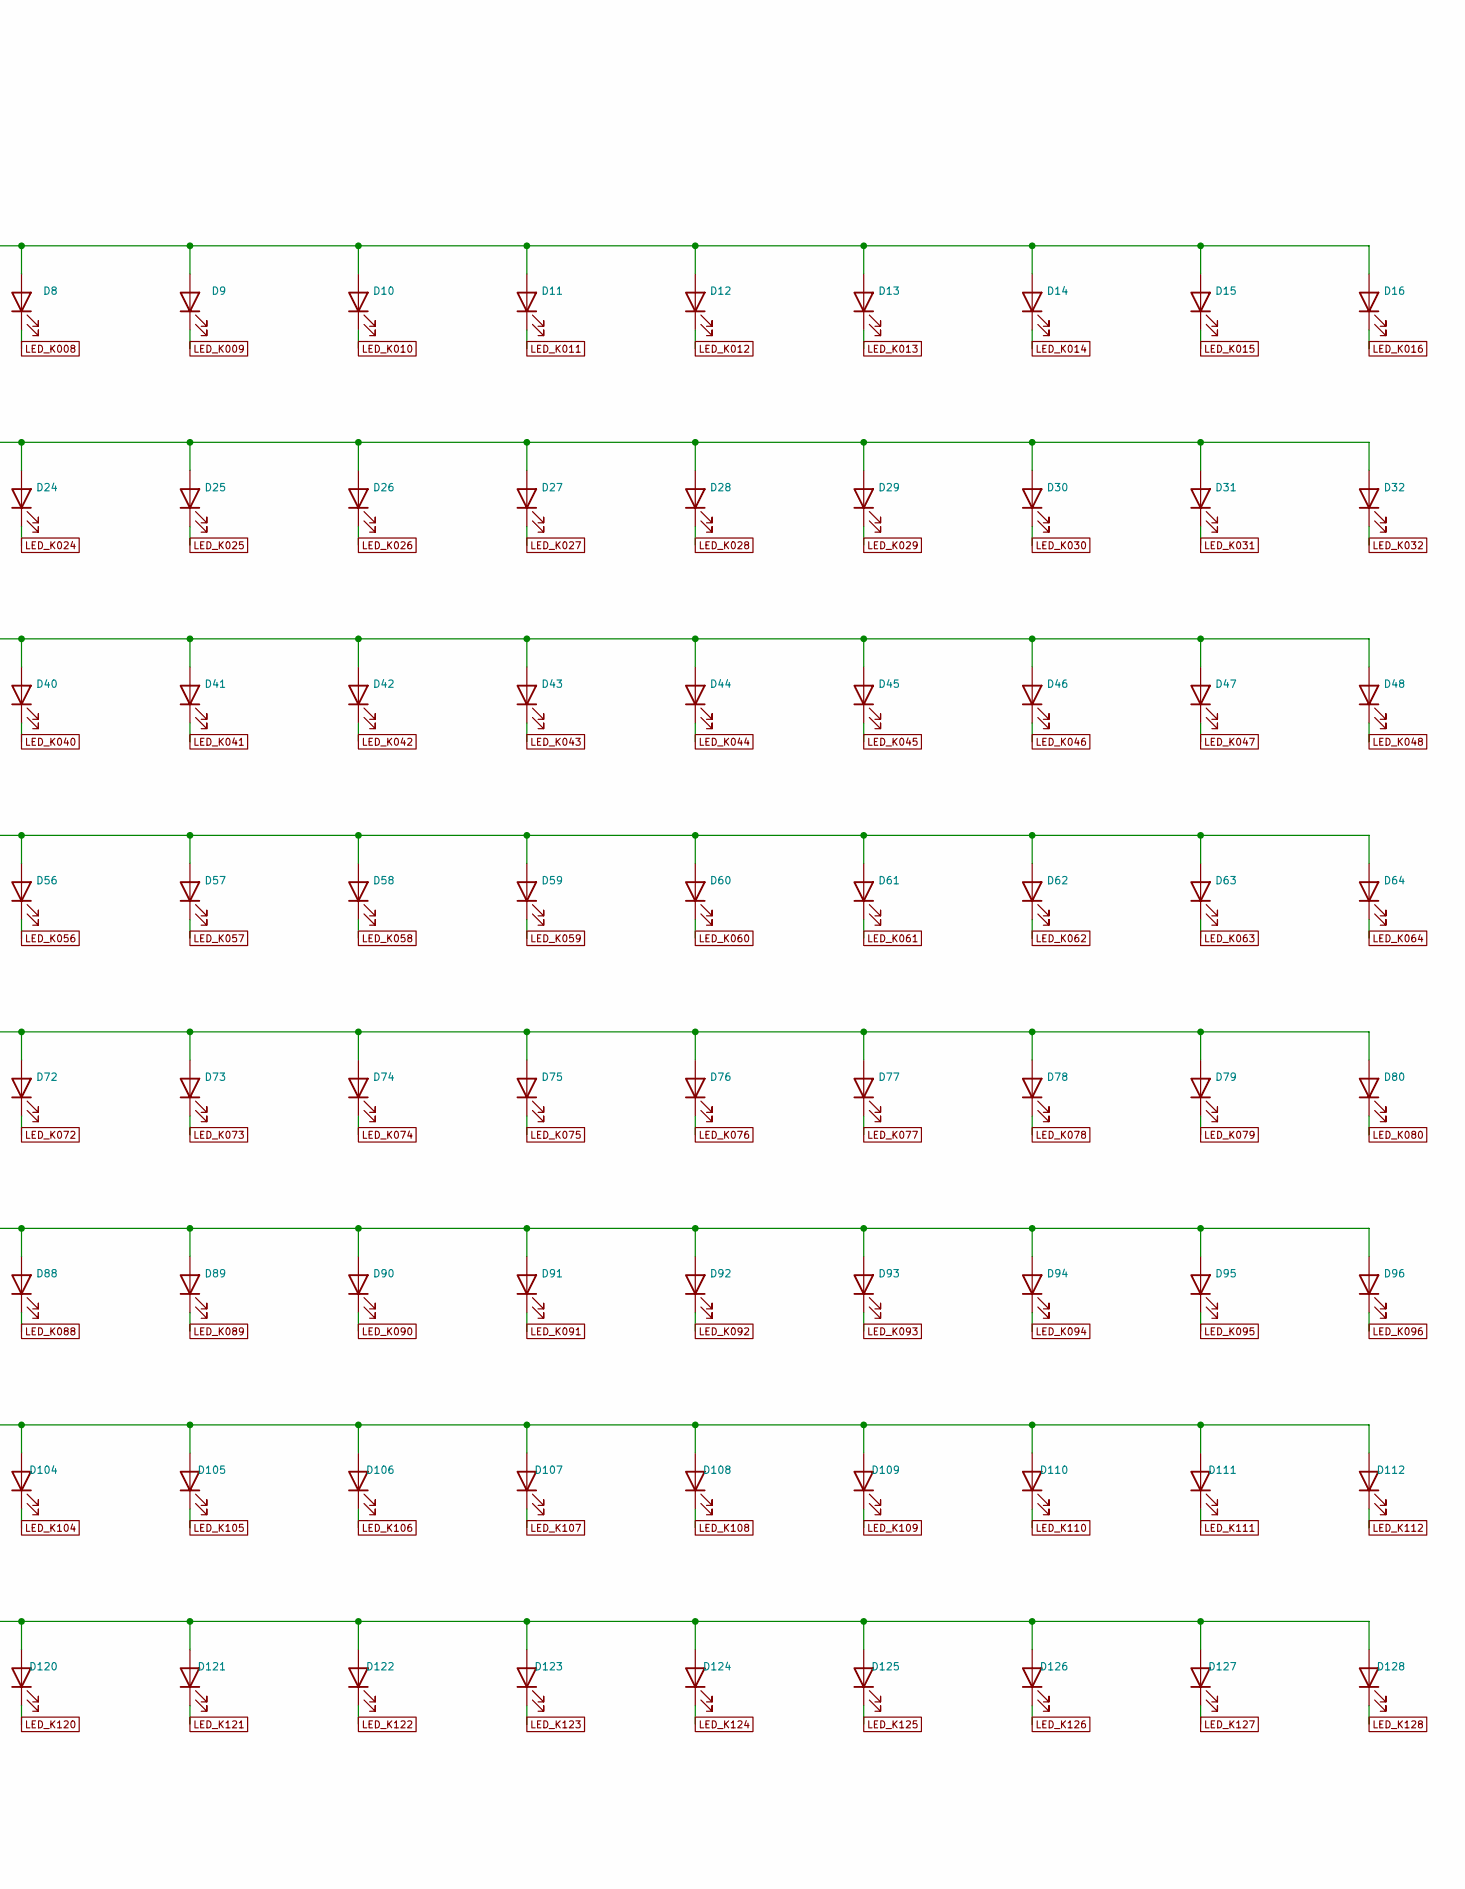
[picture p387: schematic leds.kicad_sch, part in row 1, column 2]

Parts:
D1, D2, D3, D4, D5, D6, D7, D8, D9, D10, D11, D12, D13, D14, D15, D16, D17, D18, D19, D20, D21, D22, D23, D24, D25, D26, D27, D28, D29, D30, D31, D32, D33, D34, D35, D36, D37, D38, D39, D40, D41, D42, D43, D44, D45, D46, D47, D48, D49, D50, D51, D52, D53, D54, D55, D56, D57, D58, D59, D60, D61, D62, D63, D64, D65, D66, D67, D68, D69, D70, D71, D72, D73, D74, D75, D76, D77, D78, D79, D80, D81, D82, D83, D84, D85, D86, D87, D88, D89, D90, D91, D92, D93, D94, D95, D96, D97, D98, D99, D100, D101, D102, D103, D104, D105, D106, D107, D108, D109, D110, D111, D112, D113, D114, D115, D116, D117, D118, D119, D120, D121, D122, D123, D124, D125, D126, D127, D128: APHHS1005LSECK/J3-PF

Connections:
LED_K001: D1.1 (K)
LED_K002: D2.1 (K)
LED_K003: D3.1 (K)
LED_K004: D4.1 (K)
LED_K005: D5.1 (K)
LED_K006: D6.1 (K)
LED_K007: D7.1 (K)
LED_K008: D8.1 (K)
LED_K009: D9.1 (K)
LED_K010: D10.1 (K)
LED_K011: D11.1 (K)
LED_K012: D12.1 (K)
LED_K013: D13.1 (K)
LED_K014: D14.1 (K)
LED_K015: D15.1 (K)
LED_K016: D16.1 (K)
LED_K017: D17.1 (K)
LED_K018: D18.1 (K)
LED_K019: D19.1 (K)
LED_K020: D20.1 (K)
LED_K021: D21.1 (K)
LED_K022: D22.1 (K)
LED_K023: D23.1 (K)
LED_K024: D24.1 (K)
LED_K025: D25.1 (K)
LED_K026: D26.1 (K)
LED_K027: D27.1 (K)
LED_K028: D28.1 (K)
LED_K029: D29.1 (K)
LED_K030: D30.1 (K)
LED_K031: D31.1 (K)
LED_K032: D32.1 (K)
LED_K033: D33.1 (K)
LED_K034: D34.1 (K)
LED_K035: D35.1 (K)
LED_K036: D36.1 (K)
LED_K037: D37.1 (K)
LED_K038: D38.1 (K)
LED_K039: D39.1 (K)
LED_K040: D40.1 (K)
LED_K041: D41.1 (K)
LED_K042: D42.1 (K)
LED_K043: D43.1 (K)
LED_K044: D44.1 (K)
LED_K045: D45.1 (K)
LED_K046: D46.1 (K)
LED_K047: D47.1 (K)
LED_K048: D48.1 (K)
LED_K049: D49.1 (K)
LED_K050: D50.1 (K)
LED_K051: D51.1 (K)
LED_K052: D52.1 (K)
LED_K053: D53.1 (K)
LED_K054: D54.1 (K)
LED_K055: D55.1 (K)
LED_K056: D56.1 (K)
LED_K057: D57.1 (K)
LED_K058: D58.1 (K)
LED_K059: D59.1 (K)
LED_K060: D60.1 (K)
LED_K061: D61.1 (K)
LED_K062: D62.1 (K)
LED_K063: D63.1 (K)
LED_K064: D64.1 (K)
LED_K065: D65.1 (K)
LED_K066: D66.1 (K)
LED_K067: D67.1 (K)
LED_K068: D68.1 (K)
LED_K069: D69.1 (K)
LED_K070: D70.1 (K)
LED_K071: D71.1 (K)
LED_K072: D72.1 (K)
LED_K073: D73.1 (K)
LED_K074: D74.1 (K)
LED_K075: D75.1 (K)
LED_K076: D76.1 (K)
LED_K077: D77.1 (K)
LED_K078: D78.1 (K)
LED_K079: D79.1 (K)
LED_K080: D80.1 (K)
LED_K081: D81.1 (K)
LED_K082: D82.1 (K)
LED_K083: D83.1 (K)
LED_K084: D84.1 (K)
LED_K085: D85.1 (K)
LED_K086: D86.1 (K)
LED_K087: D87.1 (K)
LED_K088: D88.1 (K)
LED_K089: D89.1 (K)
LED_K090: D90.1 (K)
LED_K091: D91.1 (K)
LED_K092: D92.1 (K)
LED_K093: D93.1 (K)
LED_K094: D94.1 (K)
LED_K095: D95.1 (K)
LED_K096: D96.1 (K)
LED_K097: D97.1 (K)
LED_K098: D98.1 (K)
LED_K099: D99.1 (K)
LED_K100: D100.1 (K)
LED_K101: D101.1 (K)
LED_K102: D102.1 (K)
LED_K103: D103.1 (K)
LED_K104: D104.1 (K)
LED_K105: D105.1 (K)
LED_K106: D106.1 (K)
LED_K107: D107.1 (K)
LED_K108: D108.1 (K)
LED_K109: D109.1 (K)
LED_K110: D110.1 (K)
LED_K111: D111.1 (K)
LED_K112: D112.1 (K)
LED_K113: D113.1 (K)
LED_K114: D114.1 (K)
LED_K115: D115.1 (K)
LED_K116: D116.1 (K)
LED_K117: D117.1 (K)
LED_K118: D118.1 (K)
LED_K119: D119.1 (K)
LED_K120: D120.1 (K)
LED_K121: D121.1 (K)
LED_K122: D122.1 (K)
LED_K123: D123.1 (K)
LED_K124: D124.1 (K)
LED_K125: D125.1 (K)
LED_K126: D126.1 (K)
LED_K127: D127.1 (K)
LED_K128: D128.1 (K)
VLED_3V3: D1.2 (A), D2.2 (A), D3.2 (A), D4.2 (A), D5.2 (A), D6.2 (A), D7.2 (A), D8.2 (A), D9.2 (A), D10.2 (A), D11.2 (A), D12.2 (A), D13.2 (A), D14.2 (A), D15.2 (A), D16.2 (A), D17.2 (A), D18.2 (A), D19.2 (A), D20.2 (A), D21.2 (A), D22.2 (A), D23.2 (A), D24.2 (A), D25.2 (A), D26.2 (A), D27.2 (A), D28.2 (A), D29.2 (A), D30.2 (A), D31.2 (A), D32.2 (A), D33.2 (A), D34.2 (A), D35.2 (A), D36.2 (A), D37.2 (A), D38.2 (A), D39.2 (A), D40.2 (A), D41.2 (A), D42.2 (A), D43.2 (A), D44.2 (A), D45.2 (A), D46.2 (A), D47.2 (A), D48.2 (A), D49.2 (A), D50.2 (A), D51.2 (A), D52.2 (A), D53.2 (A), D54.2 (A), D55.2 (A), D56.2 (A), D57.2 (A), D58.2 (A), D59.2 (A), D60.2 (A), D61.2 (A), D62.2 (A), D63.2 (A), D64.2 (A), D65.2 (A), D66.2 (A), D67.2 (A), D68.2 (A), D69.2 (A), D70.2 (A), D71.2 (A), D72.2 (A), D73.2 (A), D74.2 (A), D75.2 (A), D76.2 (A), D77.2 (A), D78.2 (A), D79.2 (A), D80.2 (A), D81.2 (A), D82.2 (A), D83.2 (A), D84.2 (A), D85.2 (A), D86.2 (A), D87.2 (A), D88.2 (A), D89.2 (A), D90.2 (A), D91.2 (A), D92.2 (A), D93.2 (A), D94.2 (A), D95.2 (A), D96.2 (A), D97.2 (A), D98.2 (A), D99.2 (A), D100.2 (A), D101.2 (A), D102.2 (A), D103.2 (A), D104.2 (A), D105.2 (A), D106.2 (A), D107.2 (A), D108.2 (A), D109.2 (A), D110.2 (A), D111.2 (A), D112.2 (A), D113.2 (A), D114.2 (A), D115.2 (A), D116.2 (A), D117.2 (A), D118.2 (A), D119.2 (A), D120.2 (A), D121.2 (A), D122.2 (A), D123.2 (A), D124.2 (A), D125.2 (A), D126.2 (A), D127.2 (A), D128.2 (A)

Notes on the sheet:
D1..D128 : APHHS1005LSECK/J3-PF / anode (2) sur VLED_3V3
Vue logique face LED : lignes de gauche a droite. Schema sans echelle ni placement PCB.
Boitier 1 x 0,5 mm != pas. Comparer 2,5 / 4 mm au banc. Empreinte et polarite a revoir avant routage.
Une sortie par cathode. Les 16 sorties restantes de U6 sont non connectees. Toutes les empreintes restent a definir.
